tmarhguy/tomato/docs/log/README.md

# Tomato engineering journal

> **Historical record:** Entries in this directory preserve the design as it
> was discussed on their publication date. They are not canonical current
> documentation. Some describe superseded word widths, register designs, ISA
> counts, software versions, or preview-only behavior. Use
> [`../status.md`](../status.md) for present facts and
> [`../documentation-policy.md`](../documentation-policy.md) when claims differ.

The journal records the path from early datapath experiments through the
discrete ALU slice, FPGA Tomato, Tomato OS, and later integrations. Historical
content is intentionally not rewritten.

## September 2026

- 15 Sep — [Envelop — Parsing, Simplest](<2026-09-15 - Envelop Parsing - Simplest.md>)
- 15 Sep — [Envelop — Scope Optimization](<2026-09-15 - Envelop Scope Optimization.md>)
- 15 Sep — [Virtual Fallback vs AI](<2026-09-15 - Virtual Fallback vs AI.md>)
- 15 Sep — [Discard Previewer or Integrate](<2026-09-15 - Discard Previewer or Integrate.md>)
- 14 Sep — [Envelop — Website and World Connect](<2026-09-14 - Envelop Website and World Connect.md>)
- 14 Sep — [Envelop — Native Bridge](<2026-09-14 - Envelop Native Bridge.md>)
- 14 Sep — [Envelop — Origin](<2026-09-14 - Envelop Origin.md>)
- 14 Sep — [Synthesis Bypass](<2026-09-14 - Synthesis Bypass.md>)
- 14 Sep — [Multiple Participants](<2026-09-14 - Multiple Participants.md>)
- 14 Sep — [Envelop — Tomato gets a message app](<2026-09-14 - Envelop - Tomato gets a message app.md>)
- 13 Sep — [ISA Upgrade](<2026-09-13 - ISA Upgrade.md>)
- 11 Sep — [Of Course Tomato Needs Sudoku](<2026-09-11 - Of Course Tomato Needs Sudoku.md>)
- 11 Sep — [HDMI, Properly Captured](<2026-09-11 - HDMI, Properly Captured.md>)
- 11 Sep — [Wallpaper, Polish, and the Rest of the Computer](<2026-09-11 - Wallpaper, Polish, and the Rest of the Computer.md>)
- 11 Sep — [When assembly is still too high-level for Tomato](<2026-09-11 - When assembly is still too high-level for Tomato.md>)

## August 2026

- 29 Aug — [Tomato works beautifully!](<2026-08-29 - Tomato works beautifully!.md>)
- 28 Aug — [Pixels on the Glass](<2026-08-28 - Pixels on the Glass.md>)
- 28 Aug — [Exploring Beyond Vivado — Open-Source Synthesis Pivot](<2026-08-28 - Exploring Beyond Vivado - Open-Source Synthesis Pivot.md>)
- 28 Aug — [Successful Video — FPGA + PMOD](<2026-08-28 - Successful Video - FPGA + PMOD.md>)
- 28 Aug — [One Press, One Key](<2026-08-28 - One Press, One Key.md>)
- 26 Aug — [The PMOD Pivot](<2026-08-26 - The PMOD Pivot.md>)
- 23 Aug — [The Invisible Logic](<2026-08-23 - The Invisible Logic.md>)
- 21 Aug — [First Lights and Flux](<2026-08-21 - First Lights and Flux.md>)
- 20 Aug — [The Gallery Paradox](<2026-08-20 - The Gallery Paradox.md>)
- 18 Aug — [First Phase of Assembly](<2026-08-18 - First Phase of Assembly.md>)
- 16 Aug — [Tomato Web Optimization](<2026-08-16 - Tomato Web Optimization.md>)
- 15 Aug — [PCBs Arrive!](<2026-08-15 - PCBs Arrive!.md>)
- 15 Aug — [ISA as a Wire](<2026-08-15 - ISA as a Wire.md>)
- 13 Aug — [Solder Station Arrives](<2026-08-13 - Solder Station Arrives.md>)
- 13 Aug — [Front-Page News in Ashtown Valley](<2026-08-13 - Front-Page News in Ashtown Valley.md>)
- 07 Aug — [Ordered Tomato](<2026-08-07 - Ordered Tomato.md>)
- 02 Aug — [Designing Additional Boards](<2026-08-02 - Designing Additional Boards.md>)

## July 2026

- 31 Jul — [The lingering thoughts](<2026-07-31 - The lingering thoughts.md>)
- 31 Jul — [Falling back to 32b](<2026-07-31 - Falling back to 32b.md>)
- 30 Jul — [Redesign into 40b (Old design = 32b)](<2026-07-30 - Redesign into 40b (Old design = 32b).md>) — **superseded direction; Tomato is currently 32-bit**
- 13 Jul — [Truth Table Latch](<2026-07-13 - Truth Table Latch.md>)
- 13 Jul — [Pipelined FPGA — What if…](<2026-07-13 - Pipelined FPGA - What if....md>)
- 13 Jul — [Downgrade for an upgrade — 32b to 16b × 4](<2026-07-13 - Downgrade for an upgrade - 32b to 16b x 4.md>) — **superseded exploration**
- 13 Jul — [Demo Ideas](<2026-07-13 - Demo Ideas.md>)
- 13 Jul — [Architecture Upgrade](<2026-07-13 - Architecture Upgrade.md>)

## June 2026

- 27 Jun — [Elimination of Mode Multiplexers](<2026-06-27 - Elimination of Mode Multiplexers.md>)
- 26 Jun — [ALU Architecture Refinement & Logic Optimization](<2026-06-26 - ALU Architecture Refinement & Logic Optimization.md>)
- 26 Jun — [ALU — Redesign with 74251](<2026-06-26 - ALU - Redesign with 74251.md>)
- 19 Jun — [ALU segment display design](<2026-06-19 - ALU segment display design.md>)
- 16 Jun — [Microcode Control Modularization](<2026-06-16 - Microcode Control Modularization.md>)
- 15 Jun — [Multiplication and Division](<2026-06-15 - Multiplication and Division.md>)
- 11 Jun — [Load Store Pipeline Analysis](<2026-06-11 - Load Store Pipeline Analysis.md>)
- 10 Jun — [Implementing Mul-Div Engine](<2026-06-10 - Implementing Mul-Div Engine.md>)

## Original introduction

[Welcome to Tomato 32](<Welcome to Tomato 32.md>) is the original welcome
dispatch and former hand-maintained index. Its prose and stale links are kept
as historical content; this README is the maintained journal index.
