tmarhguy/tomato/hardware/kicad/boards/02_shift_encoder/README.md

# 02 — Shift encoder

<p align="center"><strong>Shift + mul-div control lot · in design.</strong></p>

 

KiCad lot for the shift encoder and mul-div control board. Schematic and layout details land here as the lot advances.

**Project map:** [Boards](../README.md) · [KiCad](../../README.md) · Digital: shift / mul control sheets under [hardware/digital/modules/](../../../digital/modules/)
