tmarhguy/tomato/docs/log/2026-08-15 - PCBs Arrive!.md

# PCBs Arrive!

The PCBs all just arrived! I ordered 5 of them, and I tested them with a continuity meter, particularly for the power connections, and I am happy to log that there are no islands! It is beautiful watching the board of such sophisticated nature, realizing that I remember placing every single trace!

<p align="center">
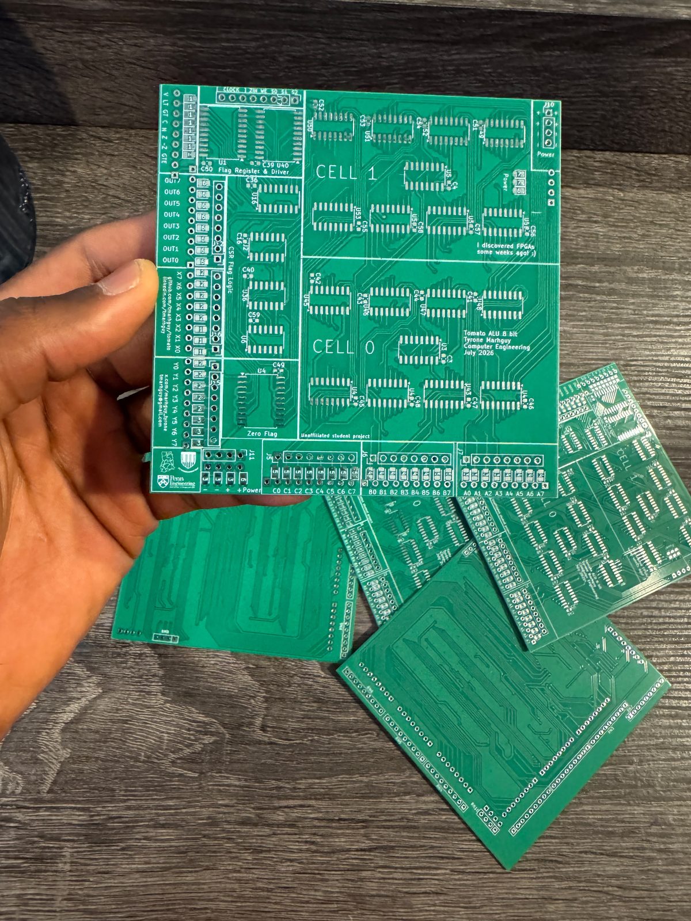
[picture p47: web/assets/pcb/pcb-arrive.jpeg]
Five 07_alu boards on the desk — Tomato ALU 8 bit, July 2026.
  
</p>
<p align="center"><em>Five boards. Lot 07, as received.</em></p>

<p align="center">
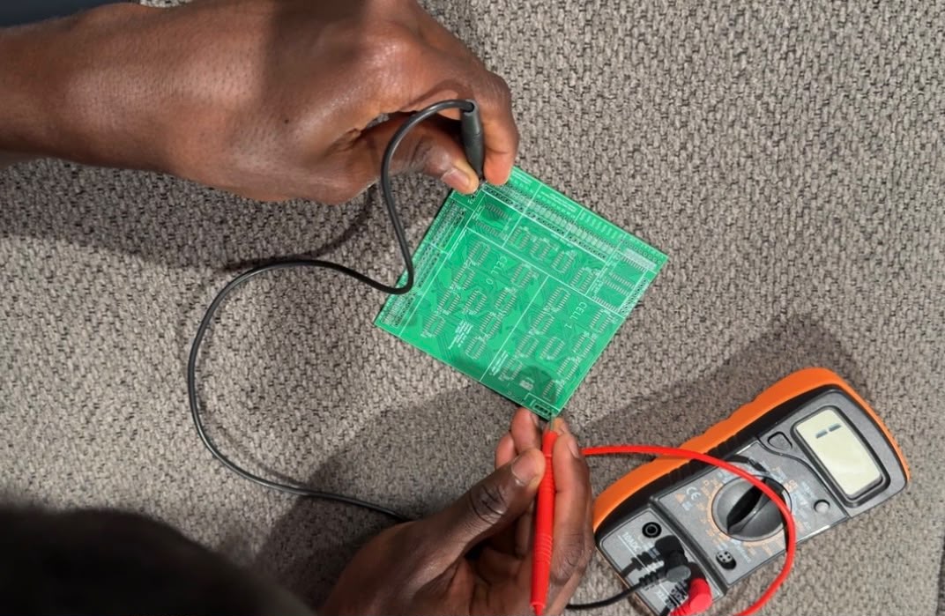
[picture p48: web/assets/pcb/continuity-test.jpeg]
Continuity meter on the 07_alu power rails — no islands.
  
</p>
<p align="center"><em>Continuity on power. No islands.</em></p>

<p align="center">
  <video src="../../web/assets/pcb/pcb-arrive.mp4" controls width="520"></video>
</p>
<p align="center"><em>The boards, in the round. ([video](../../web/assets/pcb/pcb-arrive.mp4))</em></p>

I had to admit to my roommate: isn't it hilarious that all this I have been working on, I did it all by myself? Buying a multimeter, an FPGA, using KiCad, down to this project. It has been a long and interesting journey!

The boards look stunning!
