tmarhguy/tomato/docs/alu/alu-1b/alu_control_map.pdf

# MOSAIC32 ALU Control Map - Reference Sheet

14-bit micro-instruction: LUT[7:0] + ctrl[4:0] + Cin | • Aeff = (Asel · A) ⊕ Ainv | Beff = (Bsel · B) ⊕ Binv
csel=0 → Arithmetic Mode (carry chain) | • csel=1 → Logic Mode (C bus)

# PART 1 — Arithmetic

csel=0 → ctrl 0x00--0x0F. SUM(0x96) for sub.

# Mnemonic | LUT Ctrl Aeff | Beff | Cin Result

1 ADD | 0x96 0x05 A | B | fr | A + B + Cin
2 ADC | 0x96 0x05 A | B | 1 | A + B + 1
3 INC A | 0x96 0x01 A | GND 1 | A + 1
4 INC B | 0x96 0x04 GND B | 1 | B + 1
5 DEC A | 0x96 0x09 A | VCC 0 | A − 1
6 DEC B | 0x96 0x06 VCC B | 0 | B − 1
7 NEG A | 0x96 0x03 ∼ A | GND 1 | −A
8 NEG B | 0x96 0x0C GND ∼ B | 1 | −B
9 NOT A | 0x96 0x03 ∼ A | GND 0 | ∼ A
10 NOT B | 0x96 0x0C GND ∼ B | 0 | ∼ B
11 MOV A | 0x96 0x01 A | GND 0 | A
12 MOV B | 0x96 0x04 GND B | 0 | B
13 ZERO | 0x96 0x00 GND GND 0 | 0
14 ONE | 0x96 0x00 GND GND 1 | +1
15 ALL ONES | 0x96 0x0A VCC VCC 1 | −1
16 MINUS TWO 0x96 0x0A VCC VCC 0 | −2
17 CMN | 0x96 0x05 A | B | 0 | A + B
18 RSC | 0x96 0x07 ∼ A | B | 0 | B − A − 1
19 RSB | 0x96 0x07 ∼ A | B | 1 | B − A
20 SBB | 0x96 0x0D A | ∼ B | 0 | A − B − 1
21 SUB | 0x96 0x0D A | ∼ B | 1 | A − B
22 CMP | 0x96 0x0D A | ∼ B | 1 | A − B (flg)
23 ANOM | 0x69 0x04 GND B | 0 | −B − 1
24 ANOM | 0x69 0x04 GND B | 1 | −B
25 ANOM | 0x69 0x05 A | B | 0 | −A − B − 1
26 ANOM | 0x69 0x05 A | B | 1 | −A − B
27 ANOM | 0x69 0x0C GND ∼ B | 0 | B
28 ANOM | 0x69 0x0C GND ∼ B | 1 | B + 1
29 ANOM | 0x96 0x0F ∼ A | ∼ B | 1 | ∼ (A + B)
30 ANOM | 0x96 0x0F ∼ A | ∼ B | 0 | −A − B − 2

## Routing States

Ctrl Aeff / Beff Maps To

0x00 GND / GND ZERO / ONE
0x01 A / GND INC A / MOV A 0x02 VCC / GND (unused)
0x03 ∼ A / GND | NEG A / NOT A
0x04 GND / B | INC B / MOV B
0x05 A / B | ADD/ADC/CMN
0x06 VCC / B | DEC B / ANOM
0x07 ∼ A / B | RSB / RSC
0x08 GND / VCC (unused)
0x09 A / VCC | DEC A
0x0A VCC / VCC | ONES / MINUS2
0x0B ∼ A / VCC | (unused)
0x0C GND / ∼ B | NEG B / NOT B
0x0D A / ∼ B | SUB/SBB/CMP
0x0E VCC / ∼ B | (unused)
0x0F ∼ A / ∼ B | ANOM

# PART 2 — Logic

csel=1 → ctrl = 0x15 for all logic ops.

# Mnemonic | LUT Expression

31 ZERO | 0x00 0
32 ONES | 0xFF 1
33 MOV A | 0xAA A
34 NOT A | 0x55 ∼ A
35 MOV B | 0xCC B
36 NOT B | 0x33 ∼ B
37 MOV C | 0xF0 C
38 NOT C | 0x0F ∼ C
39 AND A,B | 0x88 A ∧ B
40 OR A,B | 0xEE A ∨ B
41 NAND A,B 0x77 ∼ (A ∧ B)
42 NOR A,B | 0x11 ∼ (A ∨ B)
43 XOR A,B | 0x66 A ⊕ B
44 XNOR A,B 0x99 ∼ (A ⊕ B)
45 AND A,C | 0xA0 A ∧ C
46 OR A,C | 0xFA A ∨ C
47 NAND A,C 0x5F ∼ (A ∧ C)
48 NOR A,C | 0x05 ∼ (A ∨ C)
49 XOR A,C | 0x5A A ⊕ C
50 XNOR A,C 0xA5 ∼ (A ⊕ C)
51 AND B,C | 0xC0 B ∧ C
52 OR B,C | 0xFC B ∨ C
53 NAND B,C 0x3F ∼ (B ∧ C)
54 NOR B,C | 0x03 ∼ (B ∨ C)
55 XOR B,C | 0x3C B ⊕ C
56 XNOR B,C 0xC3 ∼ (B ⊕ C)
57 BIC A,B | 0x22 A∧ ∼ B
58 BIC B,A | 0x44 ∼ A ∧ B
59 ORN A,B | 0xBB A∨ ∼ B
60 IMP A→B | 0xDD ∼ A ∨ B
61 BIC A,C | 0x0A A∧ ∼ C
62 BIC C,A | 0x50 ∼ A ∧ C

# PART 2 — Continued

# Mnemonic | LUT Expression

63 ORN A,C | 0xAF A∨ ∼ C
64 IMP A→C | 0xF5 ∼ A ∨ C
65 BIC B,C | 0x0C B∧ ∼ C
66 BIC C,B | 0x30 ∼ B ∧ C
67 ORN B,C | 0xCF B∨ ∼ C
68 IMP B→C | 0xF3 ∼ B ∨ C
69 AND3 | 0x80 A ∧ B ∧ C
70 OR3 | 0xFE A ∨ B ∨ C
71 NAND3 | 0x7F ∼ (A ∧ B ∧ C)
72 NOR3 | 0x01 ∼ (A ∨ B ∨ C)
73 XOR3 / SUM 0x96 A ⊕ B ⊕ C
74 XNOR3 | 0x69 ∼ (A ⊕ B ⊕ C)
75 MAJ | 0xE8 AB ∨ BC ∨ AC
76 MIN | 0x17 ∼ (AB ∨ BC ∨ AC)
77 MUX C?B:A | 0xCA C?B : A
78 MUX B?C:A | 0xE2 B?C : A
79 MUX A?C:B | 0xE4 A?C : B
80 AO21 | 0xEA A ∨ (B ∧ C)
81 AO21 | 0xEC B ∨ (A ∧ C)
82 AO21 | 0xF8 C ∨ (A ∧ B)
83 OA21 | 0xA8 A ∧ (B ∨ C)
84 OA21 | 0xC8 B ∧ (A ∨ C)
85 OA21 | 0xE0 C ∧ (A ∨ B)
86 AOI21 | 0x15 ∼ (A ∨ (B ∧ C))
87 AOI21 | 0x13 ∼ (B ∨ (A ∧ C))
88 AOI21 | 0x07 ∼ (C ∨ (A ∧ B))
89 OAI21 | 0x57 ∼ (A ∧ (B ∨ C))
90 OAI21 | 0x37 ∼ (B ∧ (A ∨ C))
91 OAI21 | 0x1F ∼ (C ∧ (A ∨ B))

Total Primitives: 91 (30 Arithmetic + 61 Logic). All ops are single-pass. MAJ is a free CLA co-product. XOR3(0x96) used for both SUM and SUB. csel=1 routes C bus directly to each slice’s C-input for logic mode.
