tmarhguy/tomato/docs/log/Welcome to Tomato 32.md

> **Historical introduction and superseded index:** This dispatch is preserved
> as written. Its counts, status claims, and links may reflect earlier designs.
> Use the [current journal index](README.md) and
> [canonical status](../status.md) for present information.

This is a build log for Tomato 32. It will keep track of the questions that come up and the answers I settled for. It focussed on build log, the constraints explored and the journey from building simple logic gates to a parametric datapath — a machine where an ISA is a map onto muxes, not a second computer in copper. If you're reading this. You probably love building computers and enjoy the architecture like I do. Enjoy!

Every dispatch in [`docs/log/`](.) is listed below: the file itself, and a shield into the typeset page on [tomato.tmarhguy.com](https://tomato.tmarhguy.com/journal.html).

## The vault

| Date | Log | Link |
| --- | --- | --- |
| 13 Sep 2026 | [ISA Upgrade](<./2026-09-13%20-%20ISA%20Upgrade.md>) |  |
| 11 Sep 2026 | [HDMI, Properly Captured](<./2026-09-11%20-%20HDMI,%20Properly%20Captured.md>) |   |
| 11 Sep 2026 | [Of Course Tomato Needs Sudoku](<./2026-09-11%20-%20Of%20Course%20Tomato%20Needs%20Sudoku.md>) |  |
| 11 Sep 2026 | [Wallpaper, Polish, and the Rest of the Computer](<./2026-09-11%20-%20Wallpaper,%20Polish,%20and%20the%20Rest%20of%20the%20Computer.md>) |  |
| 11 Sep 2026 | [When assembly is still too high-level for Tomato](<./2026-09-11%20-%20When%20assembly%20is%20still%20too%20high-level%20for%20Tomato.md>) |  |
| 29 Aug 2026 | [Tomato works beautifully!](<./2026-08-29%20-%20Tomato%20works%20beautifully%21.md>) |  |
| 29 Aug 2026 | Register file → 32,768 GPR (dispatch) |  |
| 28 Aug 2026 | [One Press, One Key](<./2026-08-28%20-%20One%20Press,%20One%20Key.md>) |  |
| 28 Aug 2026 | [Exploring Beyond Vivado - Open-Source Synthesis Pivot](<./2026-08-28%20-%20Exploring%20Beyond%20Vivado%20-%20Open-Source%20Synthesis%20Pivot.md>) |  |
| 28 Aug 2026 | [Pixels on the Glass](<./2026-08-28%20-%20Pixels%20on%20the%20Glass.md>) |  |
| 26 Aug 2026 | [The PMOD Pivot](<./2026-08-26%20-%20The%20PMOD%20Pivot.md>) |  |
| 23 Aug 2026 | [The Invisible Logic](<./2026-08-23%20-%20The%20Invisible%20Logic.md>) |  |
| 21 Aug 2026 | [First Lights and Flux](<./2026-08-21%20-%20First%20Lights%20and%20Flux.md>) |  |
| 20 Aug 2026 | [The Gallery Paradox](<./2026-08-20%20-%20The%20Gallery%20Paradox.md>) |  |
| 18 Aug 2026 | [First Phase of Assembly](<./2026-08-18%20-%20First%20Phase%20of%20Assembly.md>) |  |
| 16 Aug 2026 | [Tomato Web Optimization](<./2026-08-16%20-%20Tomato%20Web%20Optimization.md>) |  |
| 15 Aug 2026 | [PCBs Arrive!](<./2026-08-15%20-%20PCBs%20Arrive%21.md>) |  |
| 15 Aug 2026 | [ISA as a Wire](<./2026-08-15%20-%20ISA%20as%20a%20Wire.md>) |   |
| 13 Aug 2026 | [Solder Station Arrives](<./2026-08-13%20-%20Solder%20Station%20Arrives.md>) |  |
| 13 Aug 2026 | [Front-Page News in Ashtown Valley](<./2026-08-13%20-%20Front-Page%20News%20in%20Ashtown%20Valley.md>) |  |
| 07 Aug 2026 | [Ordered Tomato](<./2026-08-07%20-%20Ordered%20Tomato.md>) |  |
| 02 Aug 2026 | [Designing Additional Boards](<./2026-08-02%20-%20Designing%20Additional%20Boards.md>) |  |
| 31 Jul 2026 | [The lingering thoughts](<./2026-07-31%20-%20The%20lingering%20thoughts.md>) |  |
| 31 Jul 2026 | [Falling back to 32b](<./2026-07-31%20-%20Falling%20back%20to%2032b.md>) |  |
| 30 Jul 2026 | [Redesign into 40b (Old design = 32b)](<./2026-07-30%20-%20Redesign%20into%2040b%20%28Old%20design%20=%2032b%29.md>) |  |
| 13 Jul 2026 | [Truth Table Latch](<./2026-07-13%20-%20Truth%20Table%20Latch.md>) |  |
| 13 Jul 2026 | [Pipelined FPGA — What if…](<./2026-07-13%20-%20Pipelined%20FPGA%20-%20What%20if....md>) |  |
| 13 Jul 2026 | [Downgrade for an upgrade — 32b to 16b × 4](<./2026-07-13%20-%20Downgrade%20for%20an%20upgrade%20-%2032b%20to%2016b%20x%204.md>) |  |
| 13 Jul 2026 | [Demo Ideas](<./2026-07-13%20-%20Demo%20Ideas.md>) |  |
| 13 Jul 2026 | [Architecture Upgrade](<./2026-07-13%20-%20Architecture%20Upgrade.md>) |  |
| 27 Jun 2026 | [Elimination of Mode Multiplexers](<./2026-06-27%20-%20Elimination%20of%20Mode%20Multiplexers.md>) |  |
| 26 Jun 2026 | [ALU — Redesign with 74251](<./2026-06-26%20-%20ALU%20-%20Redesign%20with%2074251.md>) |  |
| 26 Jun 2026 | [ALU Architecture Refinement &amp; Logic Optimization](<./2026-06-26%20-%20ALU%20Architecture%20Refinement%20%26%20Logic%20Optimization.md>) |  |
| 19 Jun 2026 | [ALU segment display design](<./2026-06-19%20-%20ALU%20segment%20display%20design.md>) |  |
| 16 Jun 2026 | [Microcode Control Modularization](<./2026-06-16%20-%20Microcode%20Control%20Modularization.md>) |  |
| 15 Jun 2026 | [Multiplication and Division](<./2026-06-15%20-%20Multiplication%20and%20Division.md>) |  |
| 11 Jun 2026 | [Load Store Pipeline Analysis](<./2026-06-11%20-%20Load%20Store%20Pipeline%20Analysis.md>) |  |
| 10 Jun 2026 | [Implementing Mul-Div Engine](<./2026-06-10%20-%20Implementing%20Mul-Div%20Engine.md>) |  |

## The map

The READMEs are the map of the tree. The log above is the trail.

| README | Link |
| --- | --- |
| [`README.md`](https://github.com/tmarhguy/tomato/blob/main/README.md) |  |
| [`web/README.md`](https://github.com/tmarhguy/tomato/blob/main/web/README.md) |  |
| [`docs/README.md`](https://github.com/tmarhguy/tomato/blob/main/docs/README.md) |  |
| [`docs/isa/README.md`](https://github.com/tmarhguy/tomato/blob/main/docs/isa/README.md) |  |
| [`hardware/README.md`](https://github.com/tmarhguy/tomato/blob/main/hardware/README.md) |  |
| [`hardware/digital/README.md`](https://github.com/tmarhguy/tomato/blob/main/hardware/digital/README.md) |  |
| [`hardware/verilog/README.md`](https://github.com/tmarhguy/tomato/blob/main/hardware/verilog/README.md) |  |
| [`hardware/kicad/README.md`](https://github.com/tmarhguy/tomato/blob/main/hardware/kicad/README.md) |  |
| [`hardware/kicad/modules/README.md`](https://github.com/tmarhguy/tomato/blob/main/hardware/kicad/modules/README.md) |  |
| [`hardware/kicad/boards/README.md`](https://github.com/tmarhguy/tomato/blob/main/hardware/kicad/boards/README.md) |  |
| [`hardware/kicad/boards/01_alu/README.md`](https://github.com/tmarhguy/tomato/blob/main/hardware/kicad/boards/01_alu/README.md) |  |
| [`hardware/kicad/boards/02_shift_encoder/README.md`](https://github.com/tmarhguy/tomato/blob/main/hardware/kicad/boards/02_shift_encoder/README.md) |  |
| [`hardware/kicad/boards/07_alu/README.md`](https://github.com/tmarhguy/tomato/blob/main/hardware/kicad/boards/07_alu/README.md) |  |
| [`hardware/fpga/core/README.md`](https://github.com/tmarhguy/tomato/blob/main/hardware/fpga/core/README.md) |  |
| [`hardware/fpga/README.md`](https://github.com/tmarhguy/tomato/blob/main/hardware/fpga/README.md) |  |
| [`verification/README.md`](https://github.com/tmarhguy/tomato/blob/main/verification/README.md) |  |
| [`verification/formal/README.md`](https://github.com/tmarhguy/tomato/blob/main/verification/formal/README.md) |  |
| [`verification/rtl/README.md`](https://github.com/tmarhguy/tomato/blob/main/verification/rtl/README.md) |  |
| [`verification/scripts/README.md`](https://github.com/tmarhguy/tomato/blob/main/verification/scripts/README.md) |  |
| [`verification/directed/README.md`](https://github.com/tmarhguy/tomato/blob/main/verification/directed/README.md) |  |
| [`verification/synthesis/README.md`](https://github.com/tmarhguy/tomato/blob/main/verification/synthesis/README.md) |  |
| [`verification/uvm/README.md`](https://github.com/tmarhguy/tomato/blob/main/verification/uvm/README.md) |  |
| [`verification/uvm/common/README.md`](https://github.com/tmarhguy/tomato/blob/main/verification/uvm/common/README.md) |   |
| [`verification/uvm/alu_1b/README.md`](https://github.com/tmarhguy/tomato/blob/main/verification/uvm/alu_1b/README.md) |   |
| [`verification/uvm/alu_8b/README.md`](https://github.com/tmarhguy/tomato/blob/main/verification/uvm/alu_8b/README.md) |   |
| [`verification/uvm/alu_32b/README.md`](https://github.com/tmarhguy/tomato/blob/main/verification/uvm/alu_32b/README.md) |  |
| [`microcode/README.md`](https://github.com/tmarhguy/tomato/blob/main/microcode/README.md) |  |
| [`software/README.md`](https://github.com/tmarhguy/tomato/blob/main/software/README.md) |  |
| [`firmware/README.md`](https://github.com/tmarhguy/tomato/blob/main/firmware/README.md) |  |
| [`test/README.md`](https://github.com/tmarhguy/tomato/blob/main/test/README.md) |  |
