tmarhguy/tomato/docs/images/envelop/chat-on-tomato.webp

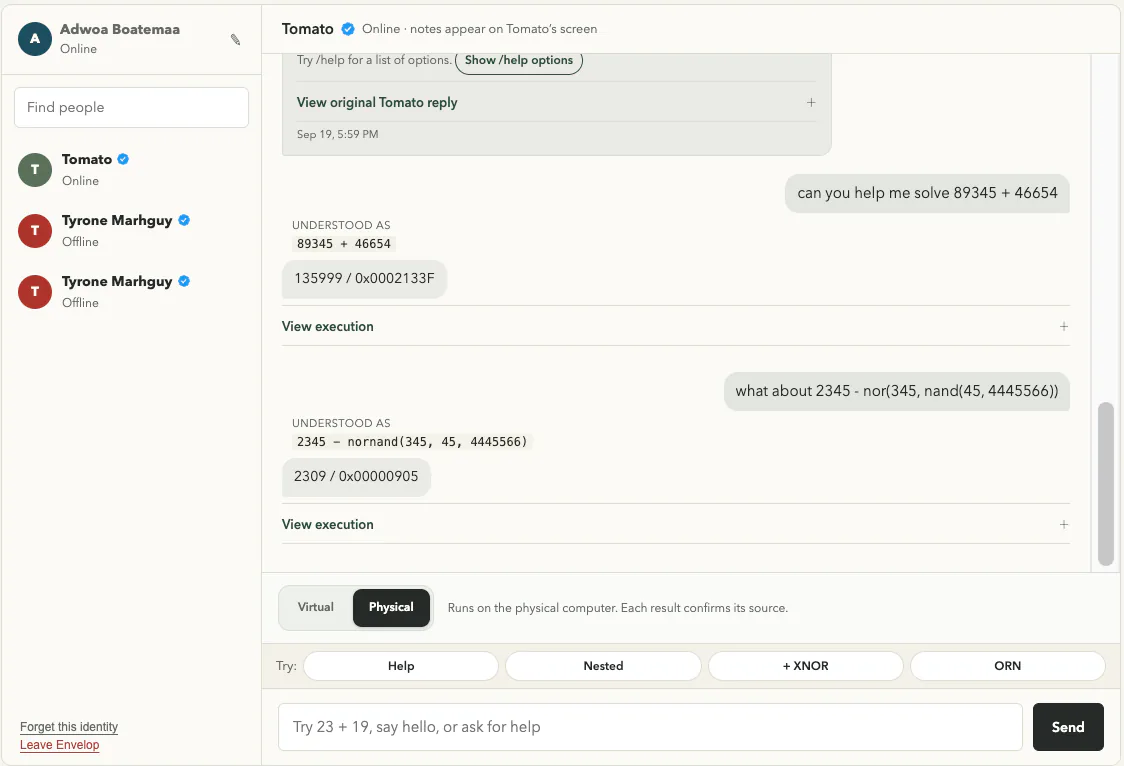
docs/images/envelop/chat-on-tomato.webp
