tmarhguy/tomato/hardware/kicad/main/8b-alu-slice/8b-alu-slice.png

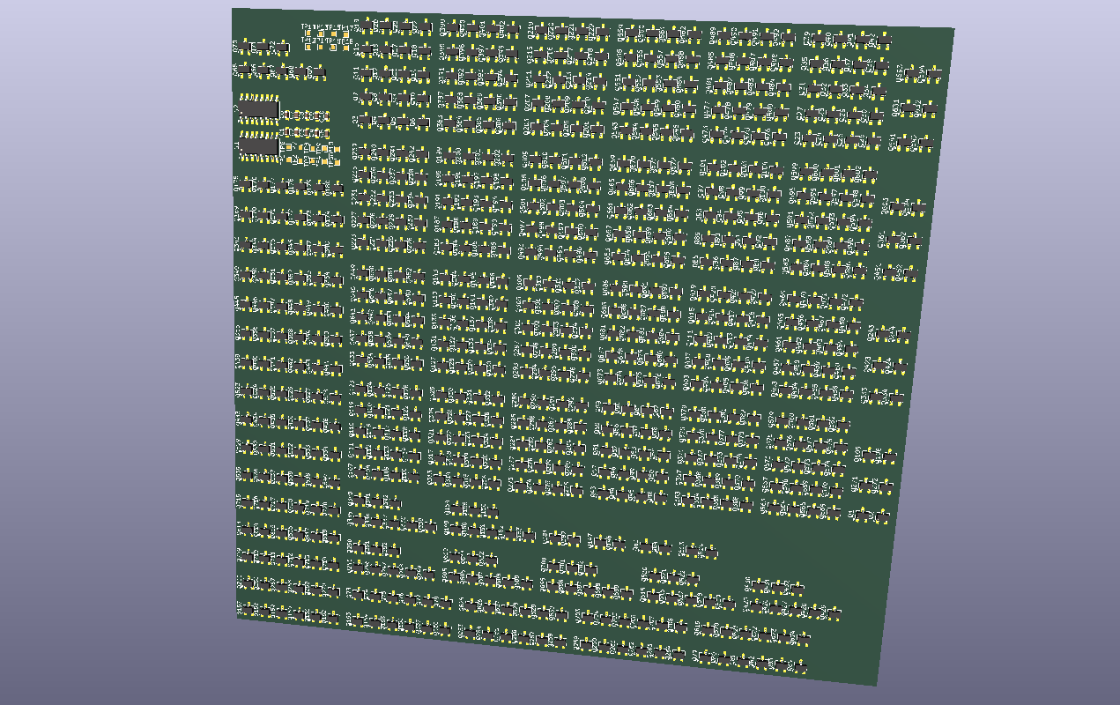
hardware/kicad/main/8b-alu-slice/8b-alu-slice.png
