tmarhguy/tomato/media/digital/2026-06-07-main.png

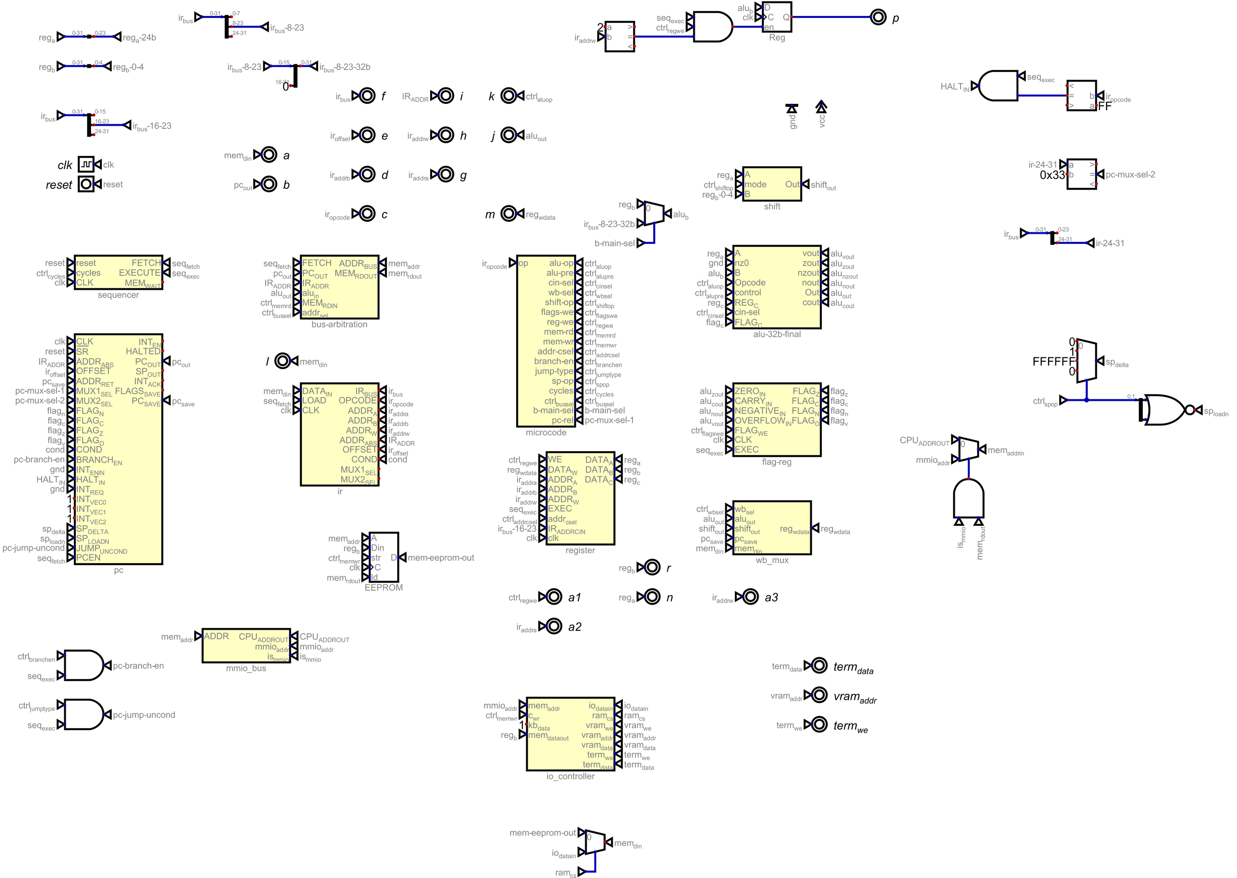
media/digital/2026-06-07-main.png
