tmarhguy/tomato/media/digital/2026-06-08-main.png

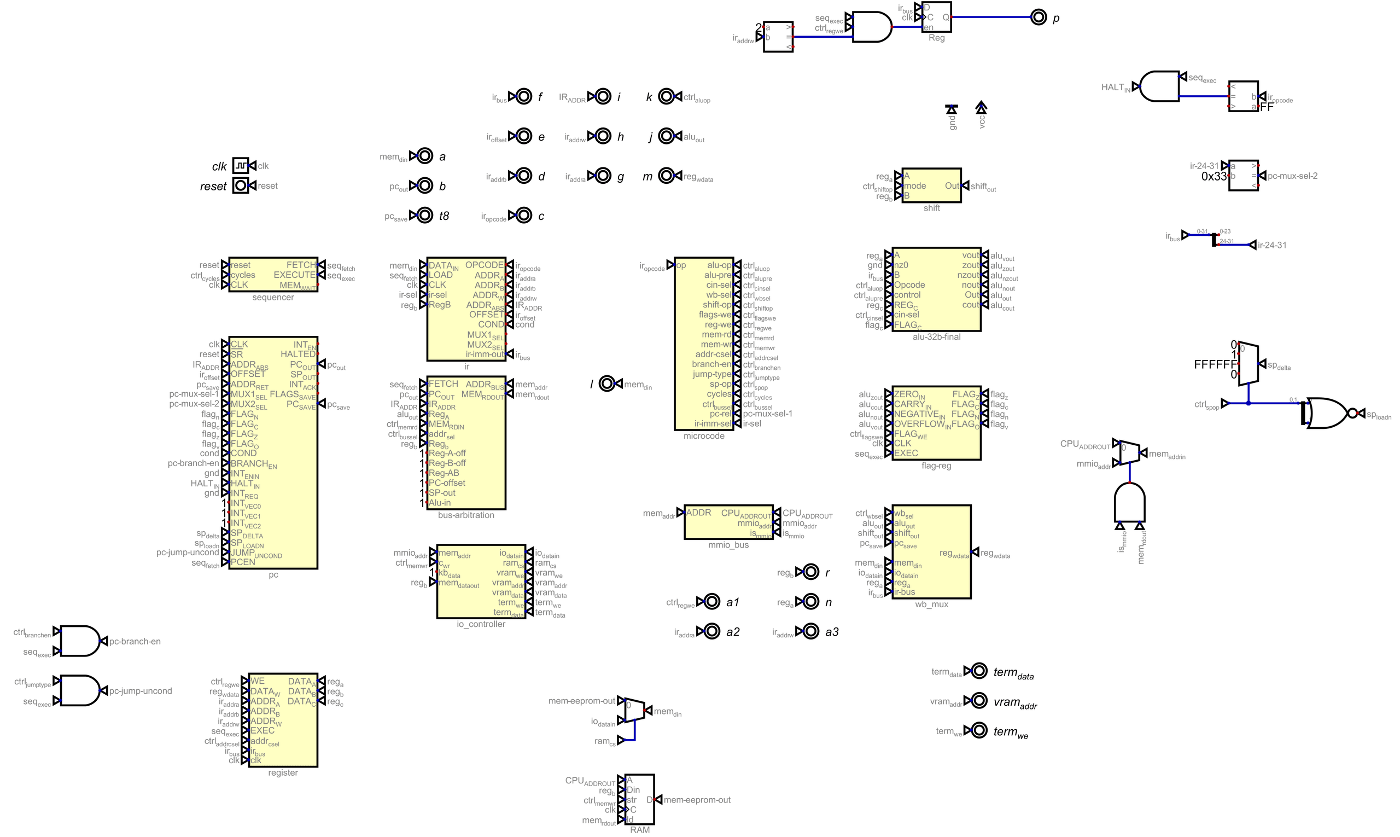
media/digital/2026-06-08-main.png
