tmarhguy/tomato/media/digital/2026-06-16-main.png

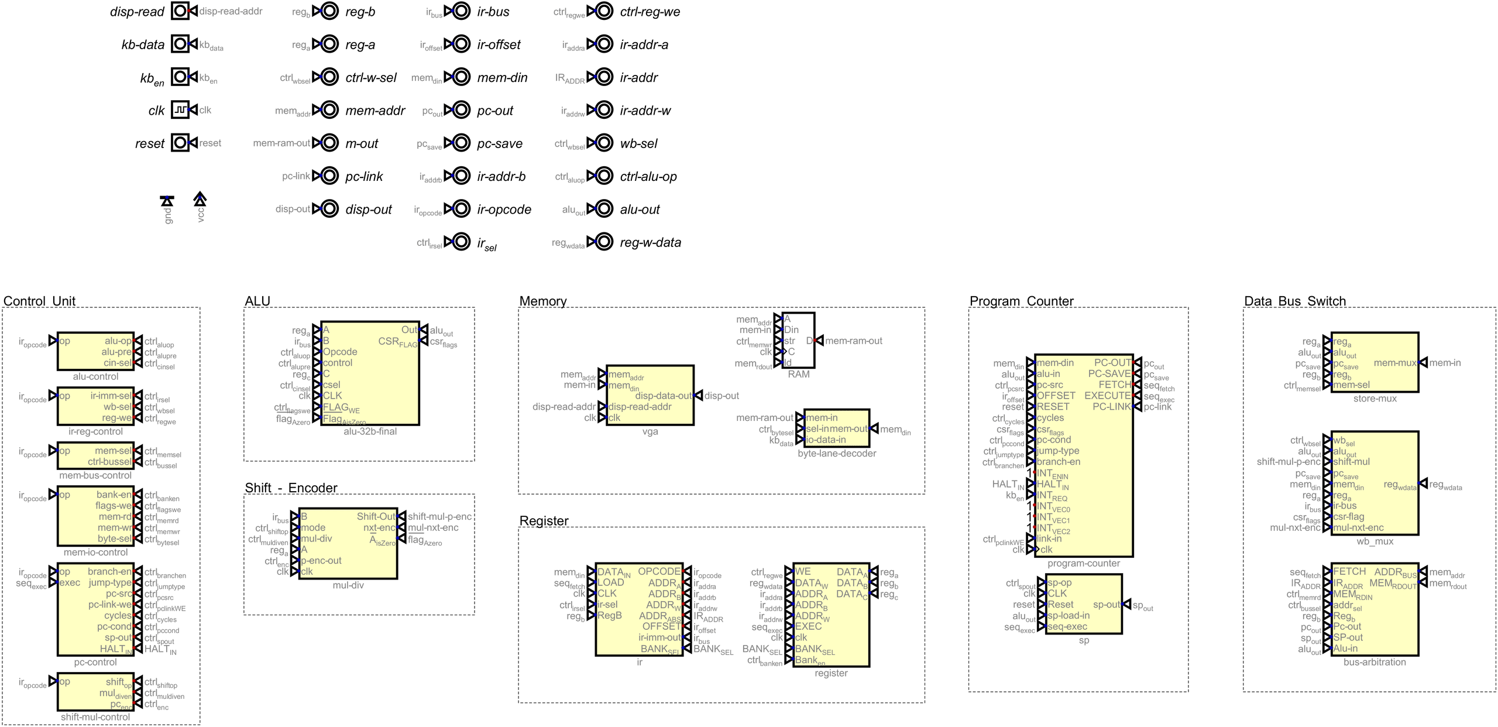
media/digital/2026-06-16-main.png
