tmarhguy/tomato/media/digital/alu/02-1b-cell-4to1-mux-logic.png

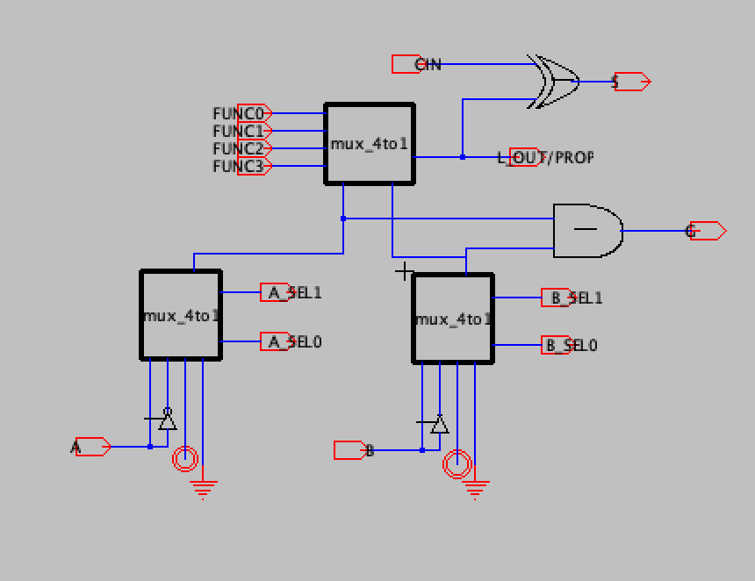
media/digital/alu/02-1b-cell-4to1-mux-logic.png
