tmarhguy/tomato/media/digital/alu/10-tg-xor-vpulse.png

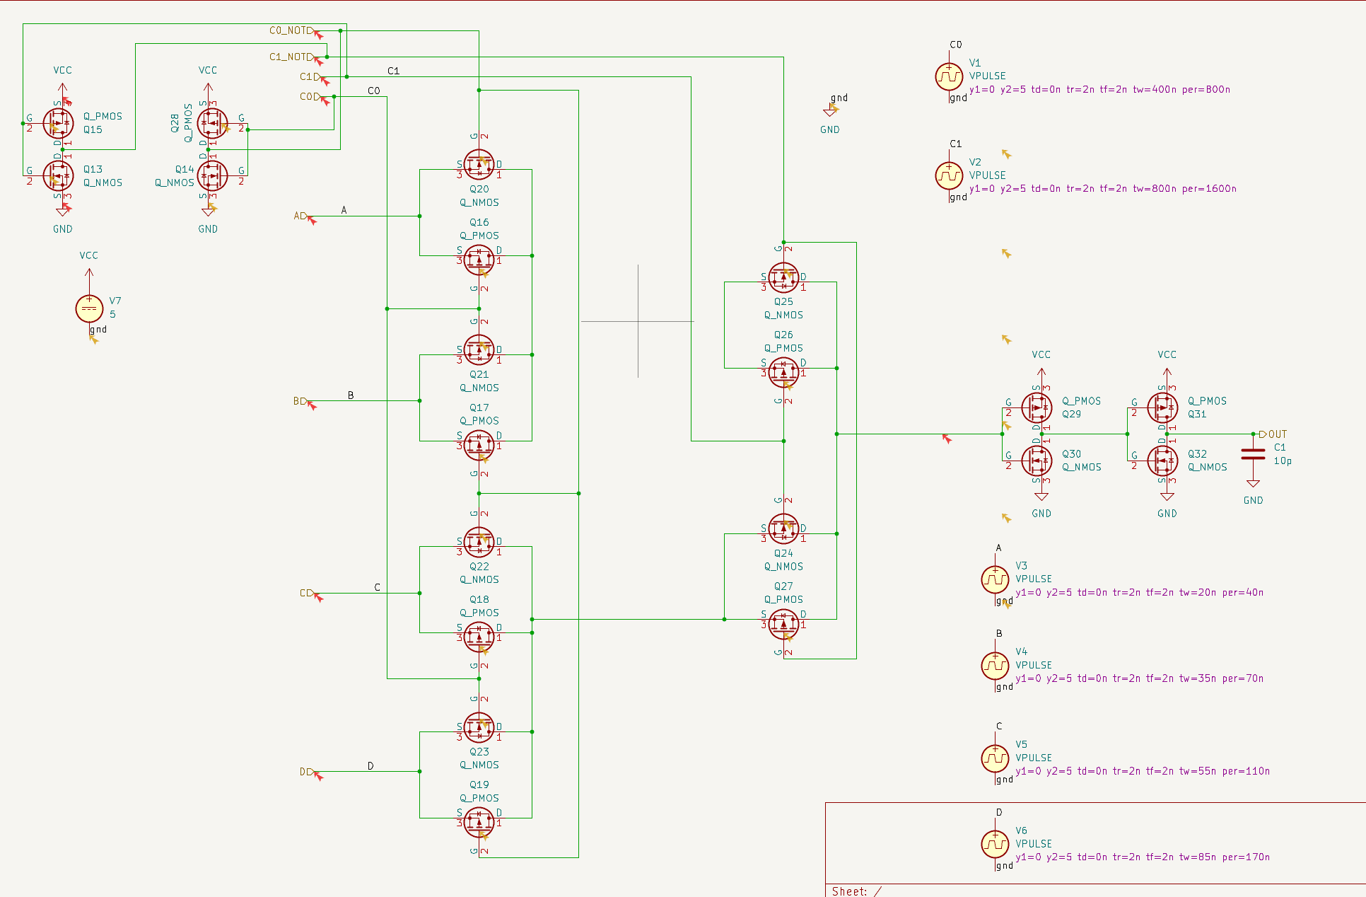
media/digital/alu/10-tg-xor-vpulse.png
