tmarhguy/tomato/media/digital/bus/01-arbiter-fail-then-pass.png

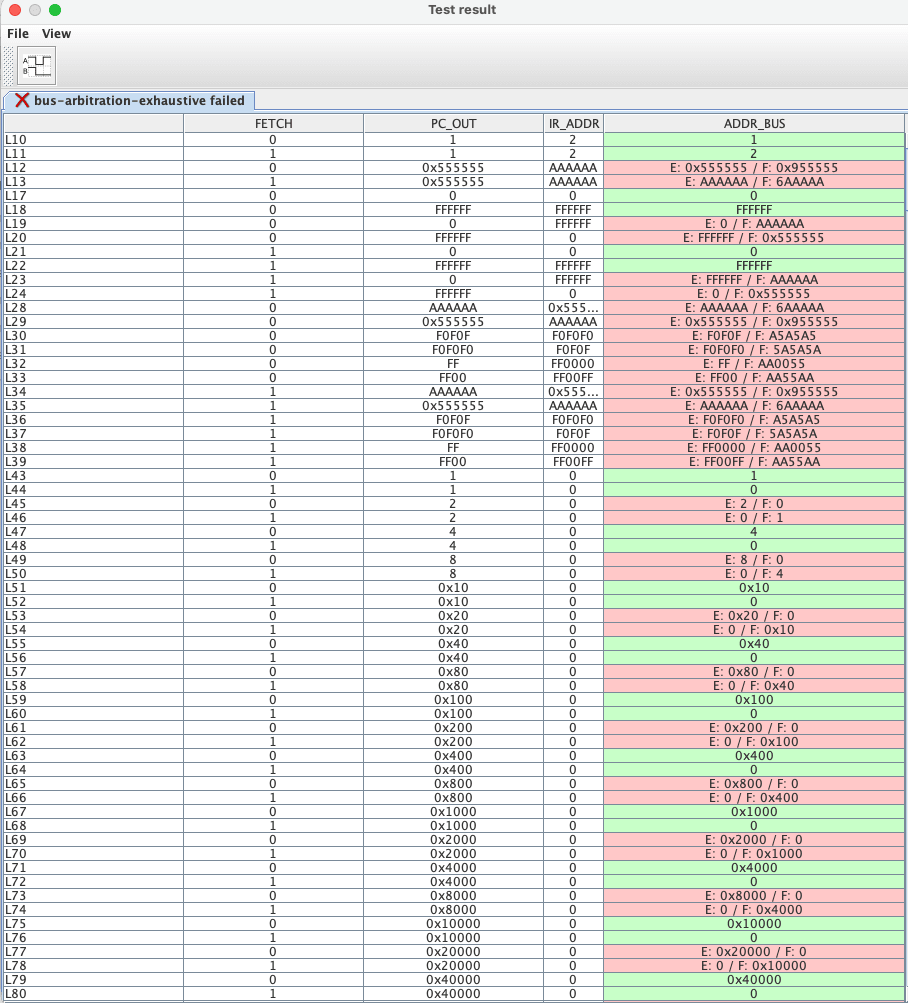
media/digital/bus/01-arbiter-fail-then-pass.png
