tmarhguy/tomato/media/digital/control/03-ctrl-unit-32b-later.png

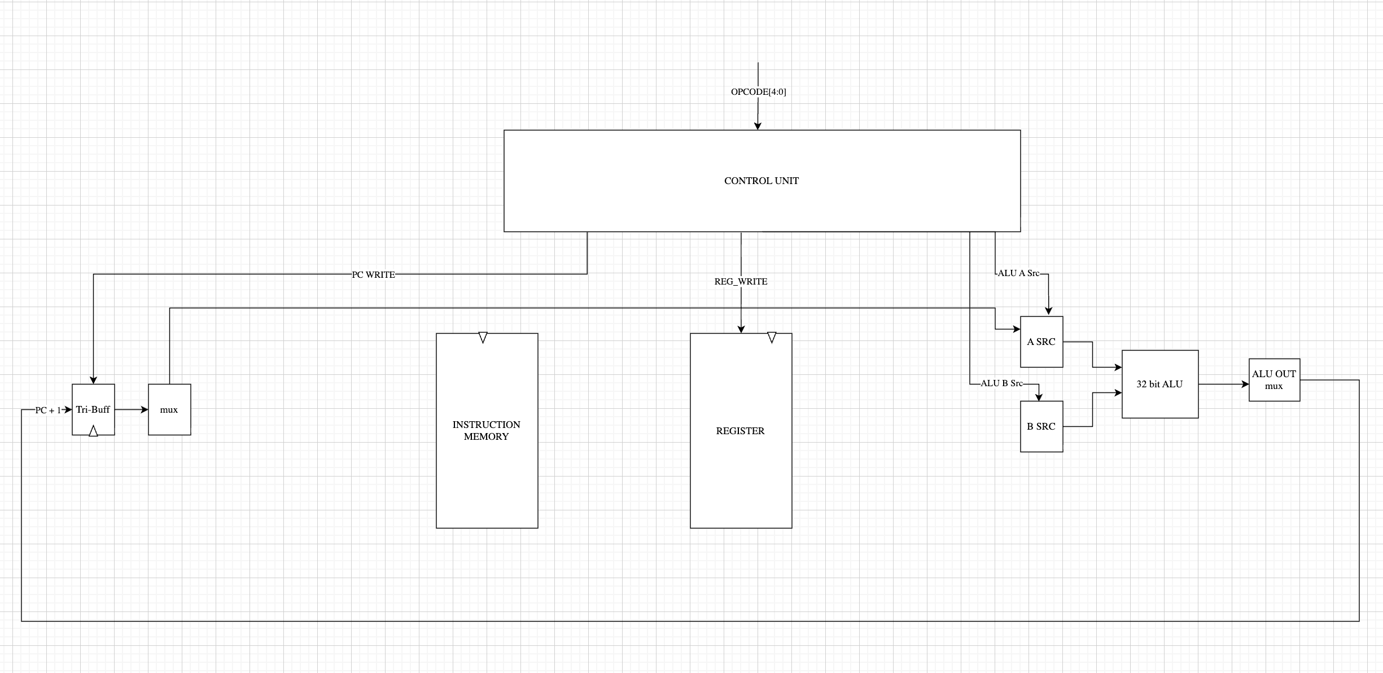
media/digital/control/03-ctrl-unit-32b-later.png
