tmarhguy/tomato/media/digital/control/06-microcode-rom-hex-64b.jpg

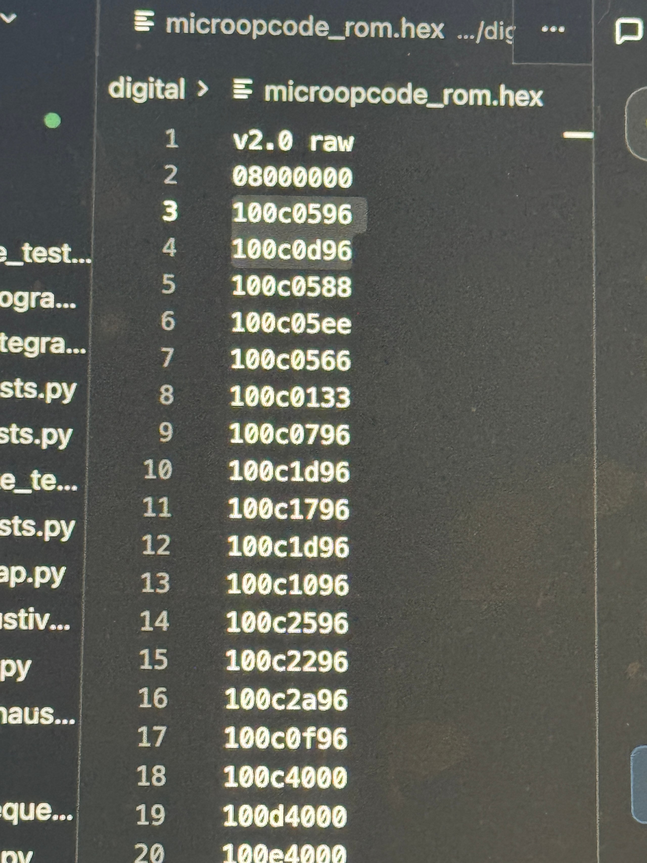
media/digital/control/06-microcode-rom-hex-64b.jpg
