tmarhguy/tomato/media/digital/control/07-system-schematic-overview.jpg

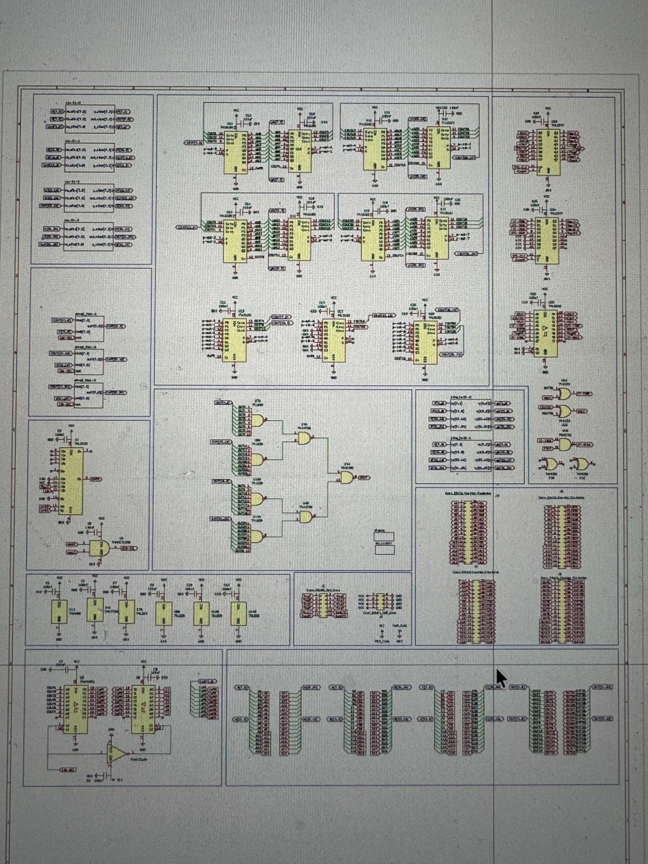
media/digital/control/07-system-schematic-overview.jpg
