tmarhguy/tomato/media/digital/pc-display/06-seg-atf16v8-cell.png

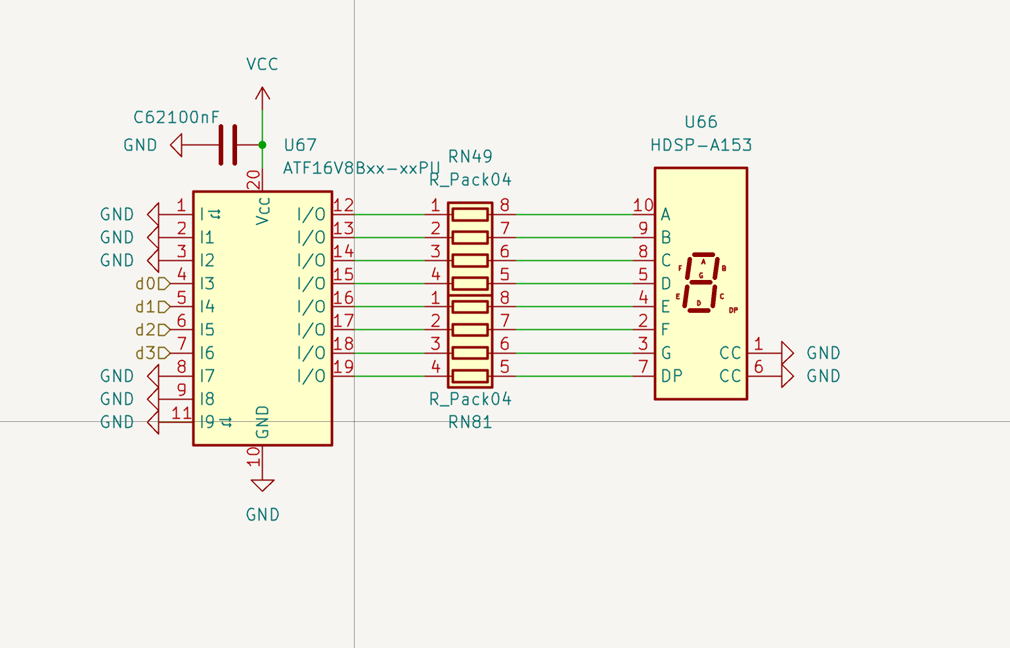
media/digital/pc-display/06-seg-atf16v8-cell.png
