tmarhguy/tomato/media/digital/pc-display/07-display-drawio.png

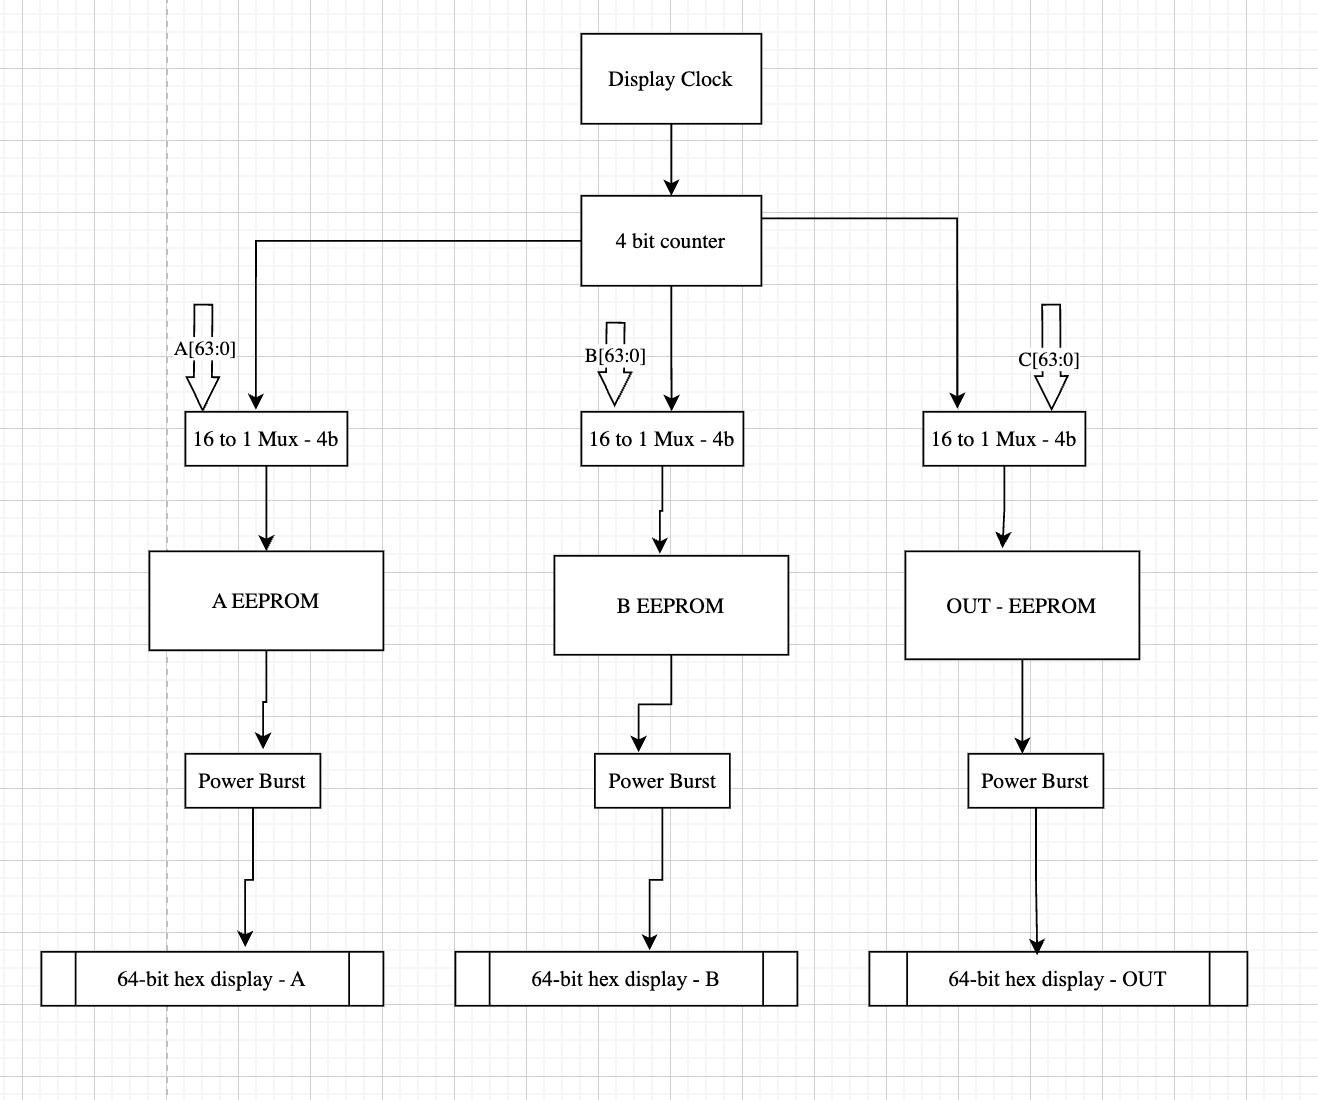
media/digital/pc-display/07-display-drawio.png
