tmarhguy/tomato/media/kicad/07_alu/schematics/07_alu-images-1.jpg

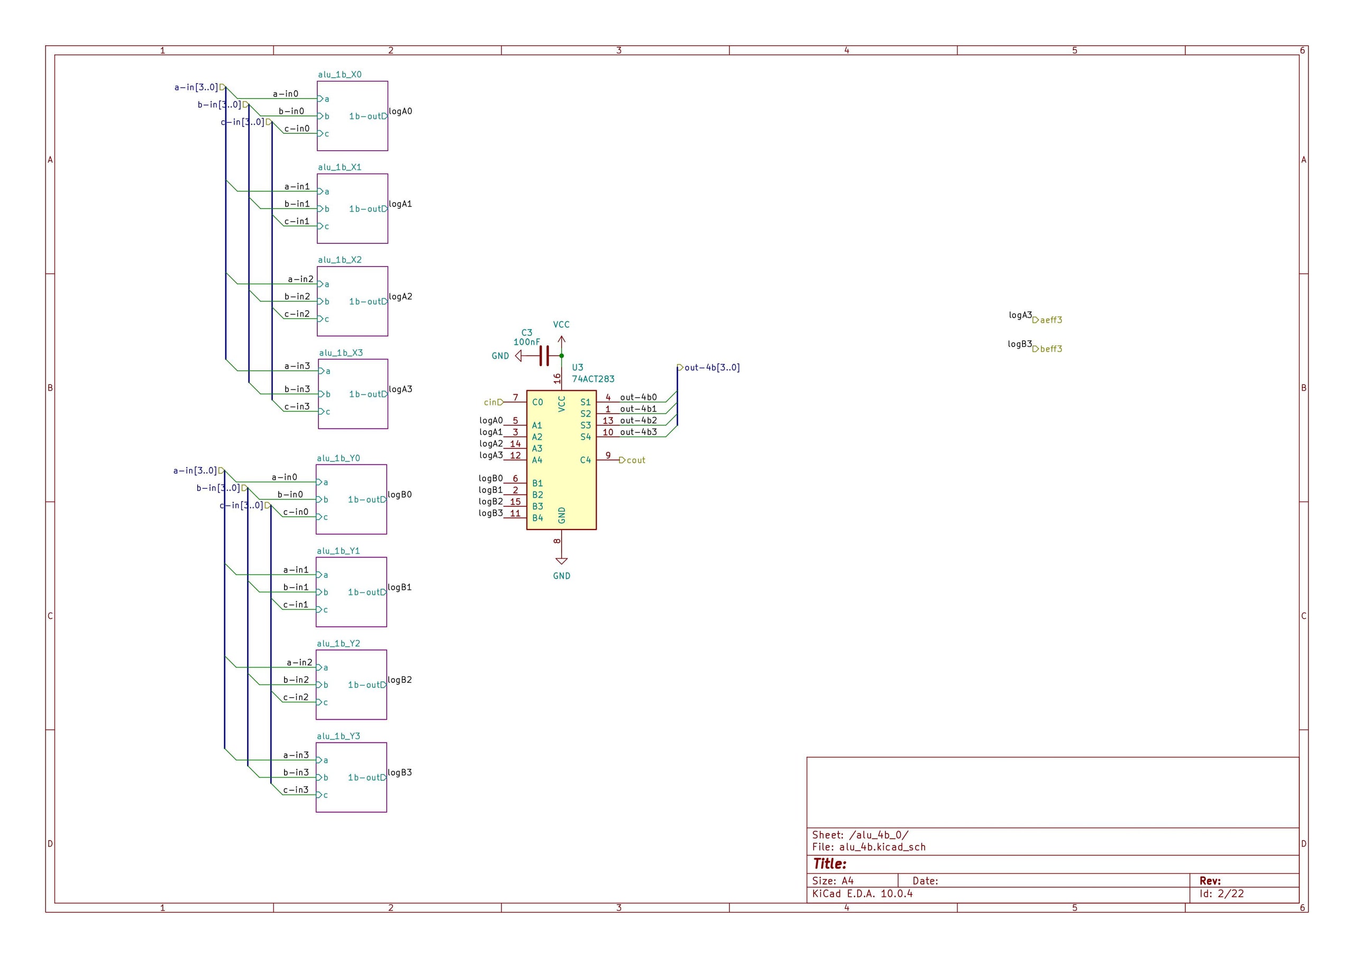
media/kicad/07_alu/schematics/07_alu-images-1.jpg
