tmarhguy/tomato/media/kicad/07_alu/schematics/07_alu-images-5.jpg

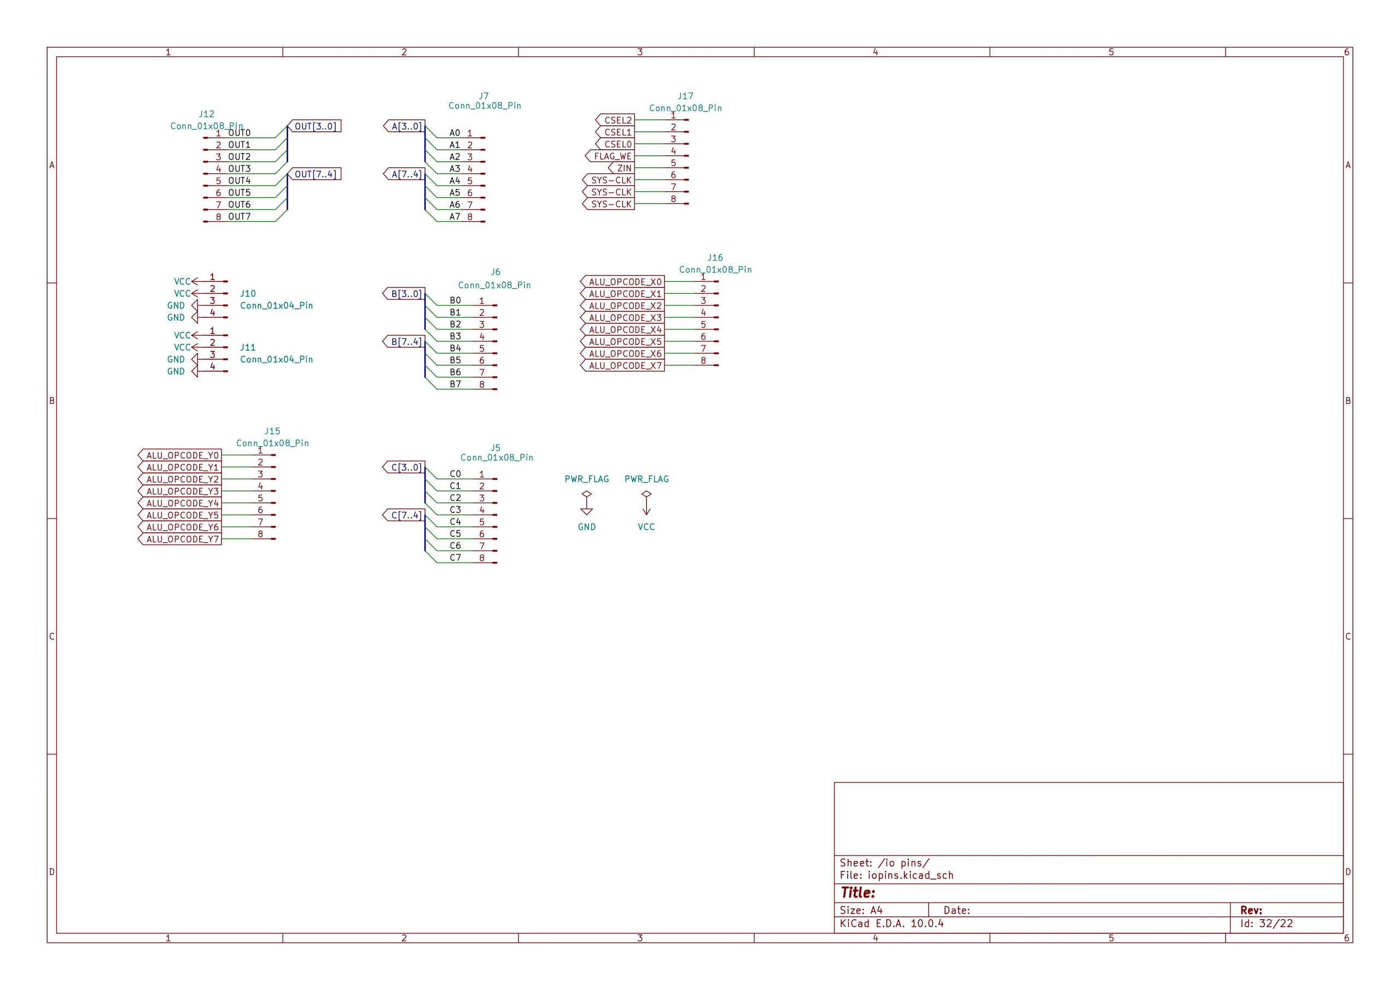
media/kicad/07_alu/schematics/07_alu-images-5.jpg
