tmarhguy/tomato/media/kicad/32b/05-74182-inv-driver-sch.png

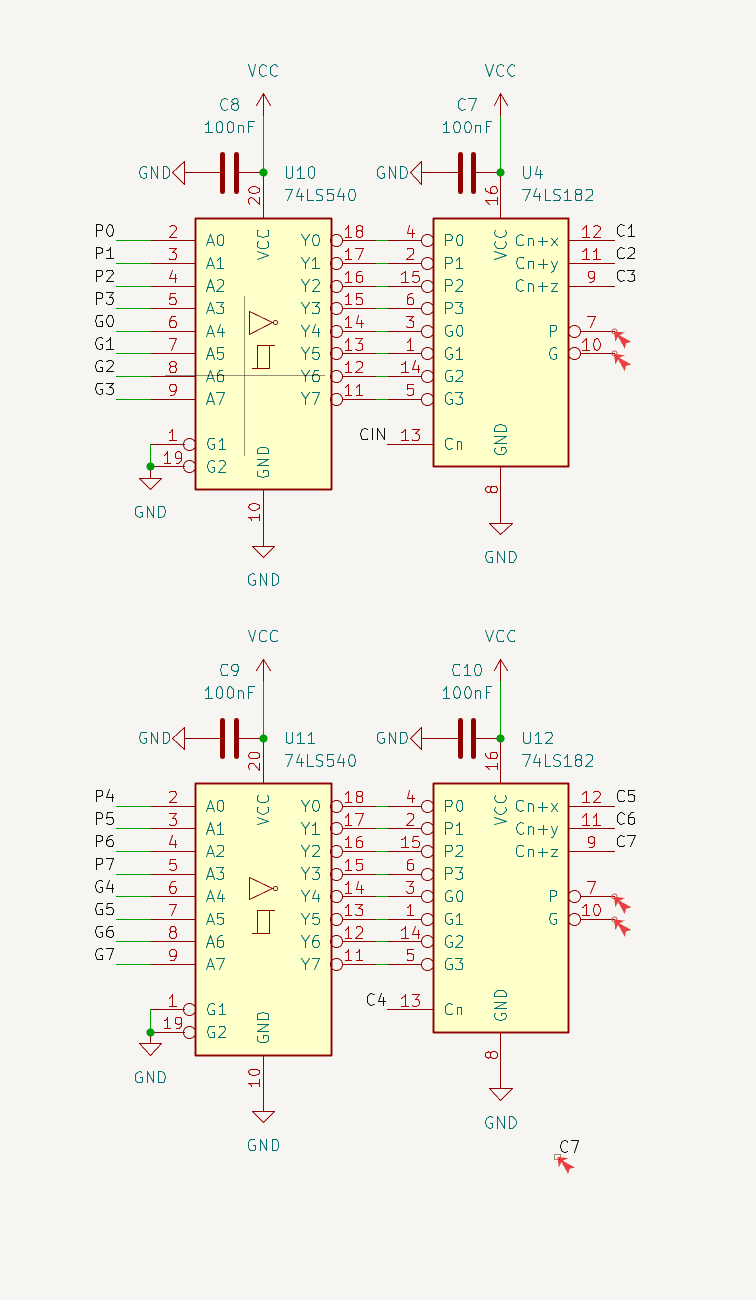
media/kicad/32b/05-74182-inv-driver-sch.png
