tmarhguy/tomato/media/logs/screenshots/2026-07-17-10.42.34-am.png

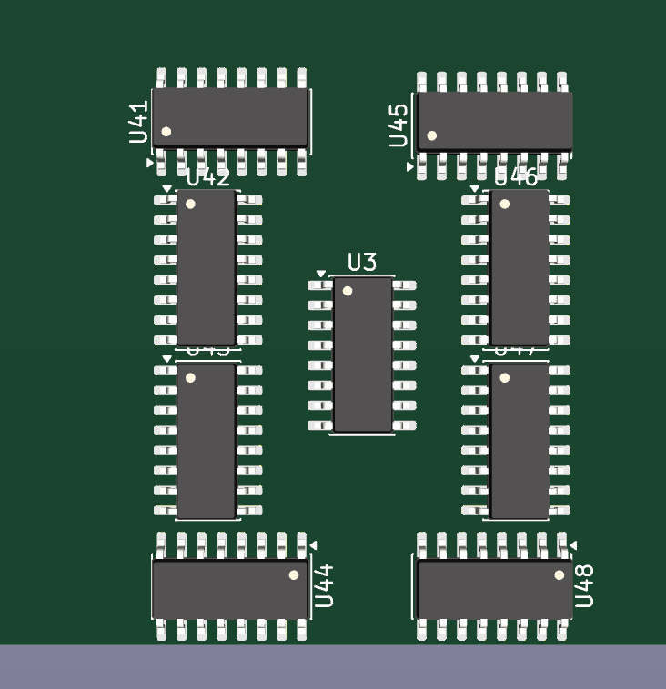
media/logs/screenshots/2026-07-17-10.42.34-am.png
