tmarhguy/tomato/media/logs/screenshots/2026-07-25-8.25.05-pm.png

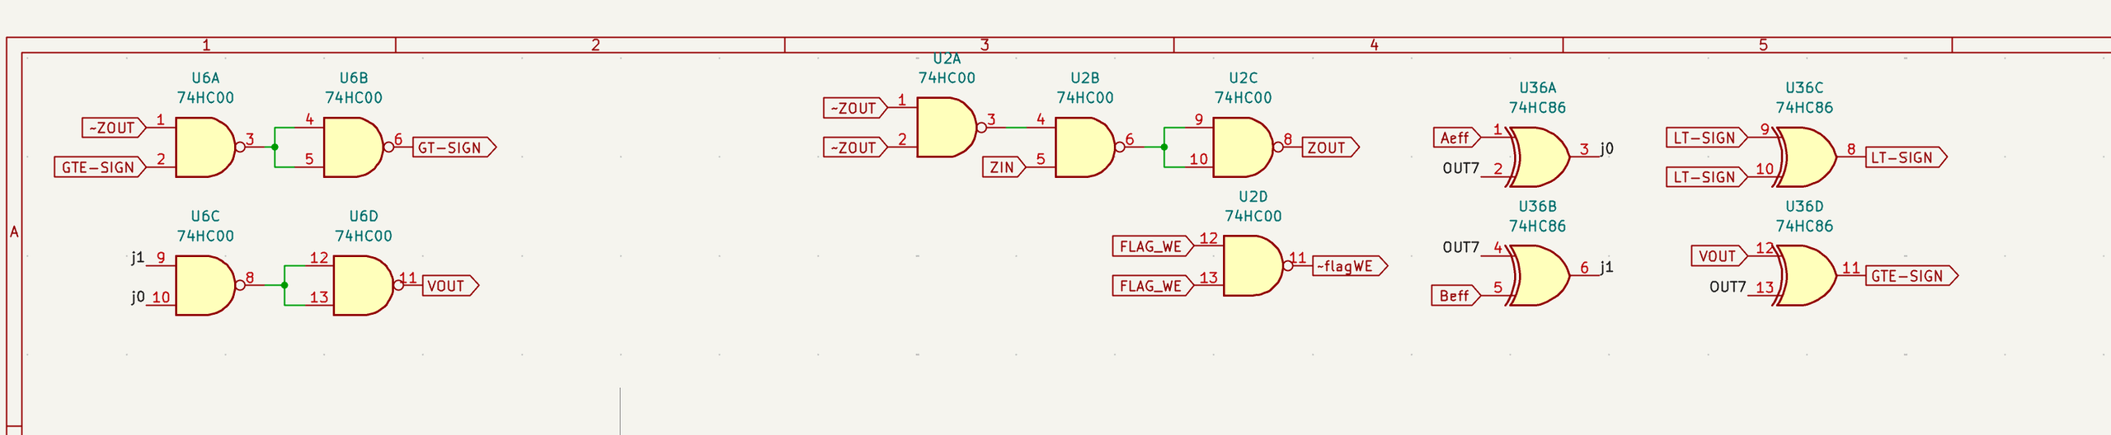
media/logs/screenshots/2026-07-25-8.25.05-pm.png
