tmarhguy/tomato/media/logs/screenshots/2026-07-26-2.43.37-pm.png

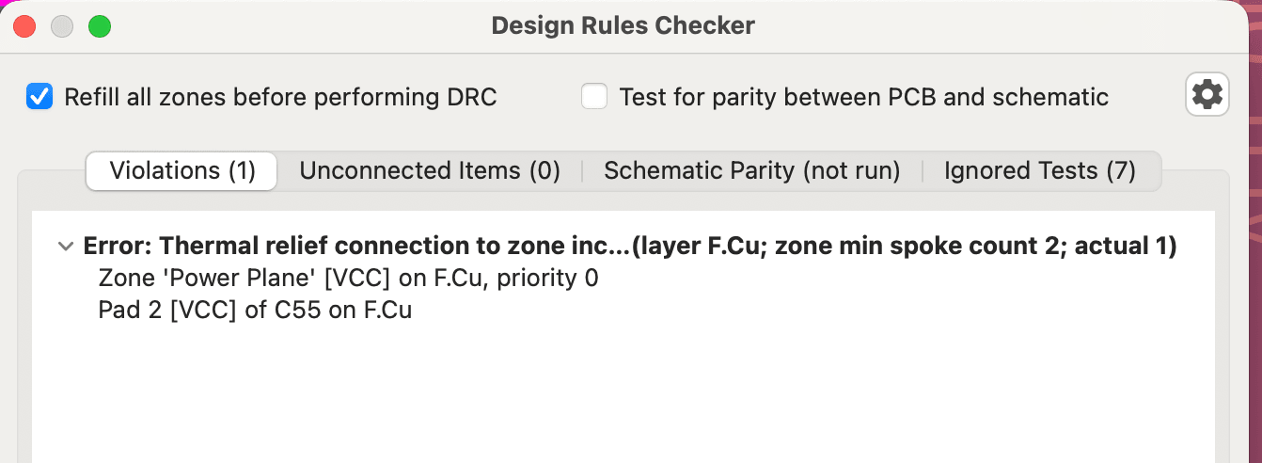
media/logs/screenshots/2026-07-26-2.43.37-pm.png
