tmarhguy/tomato/media/logs/screenshots/2026-07-26-5.35.04-pm.png

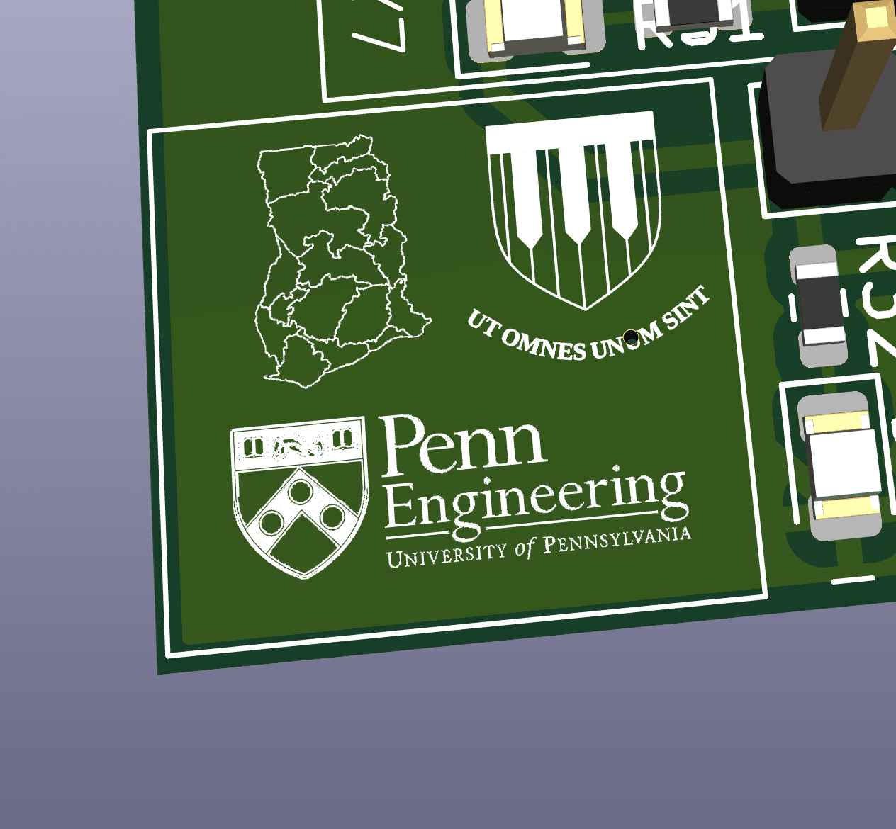
media/logs/screenshots/2026-07-26-5.35.04-pm.png
