tmarhguy/tomato/media/logs/screenshots/2026-07-26-6.12.58-pm.png

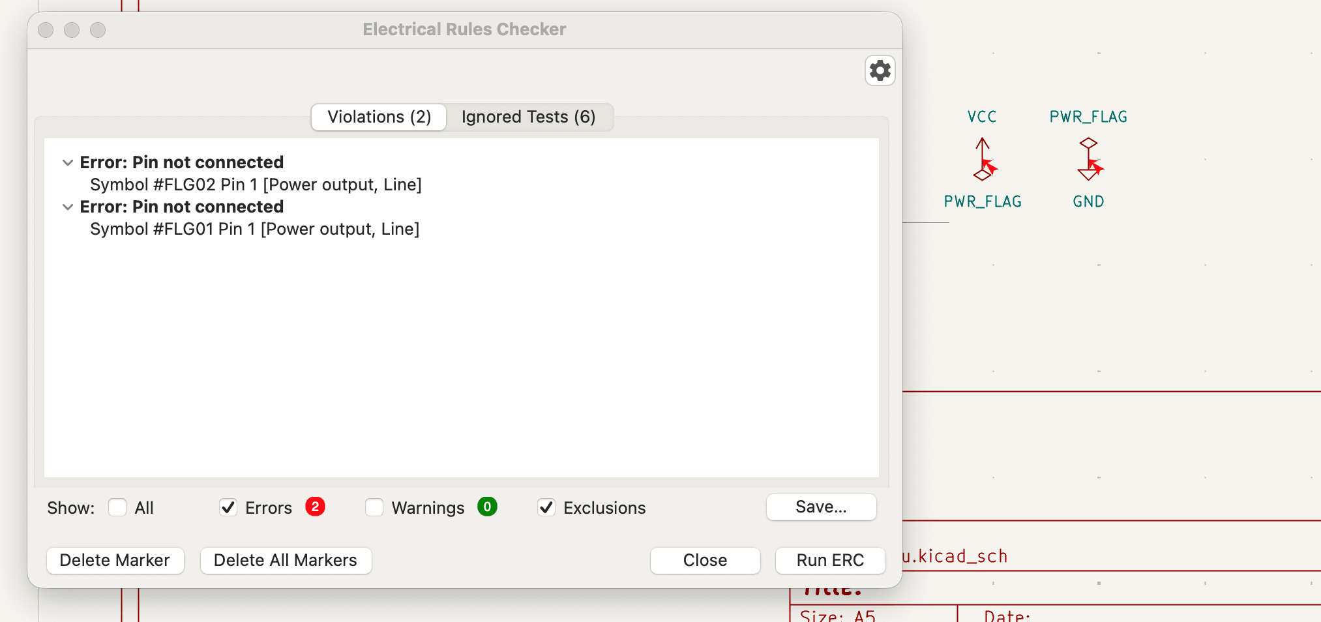
media/logs/screenshots/2026-07-26-6.12.58-pm.png
