tmarhguy/tomato/media/logs/screenshots/2026-08-08-2.02.14-am.png

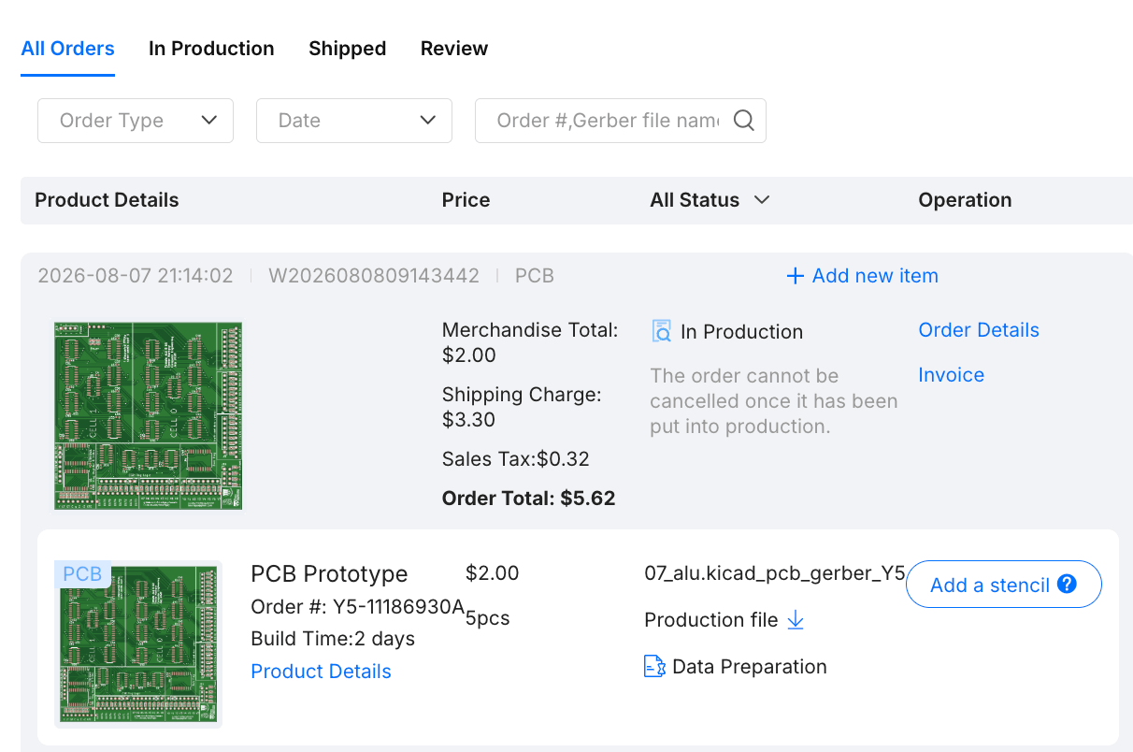
media/logs/screenshots/2026-08-08-2.02.14-am.png
