tmarhguy/tomato/media/logs/screenshots/2026-08-16-11.42.04-am.png

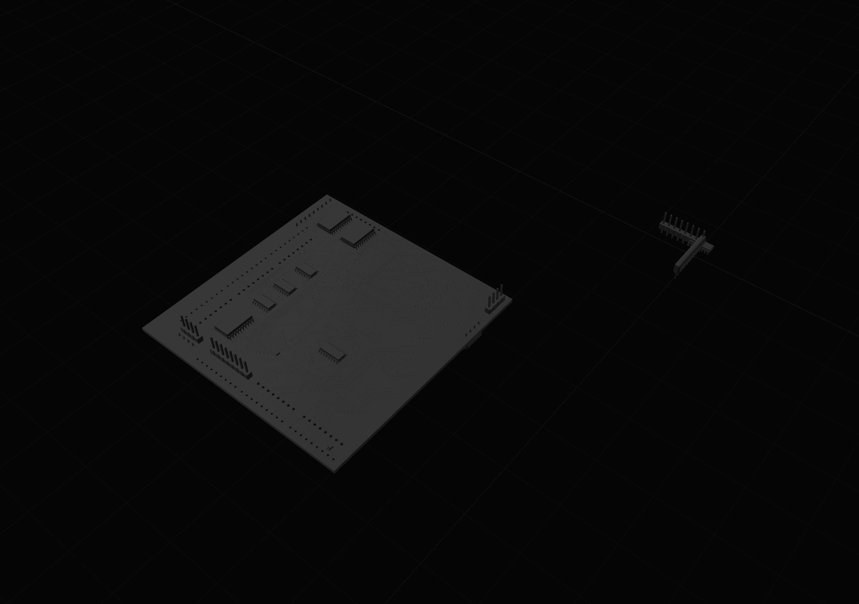
media/logs/screenshots/2026-08-16-11.42.04-am.png
