tmarhguy/tomato/media/notes/04-display-nibble-mux-insight.jpg

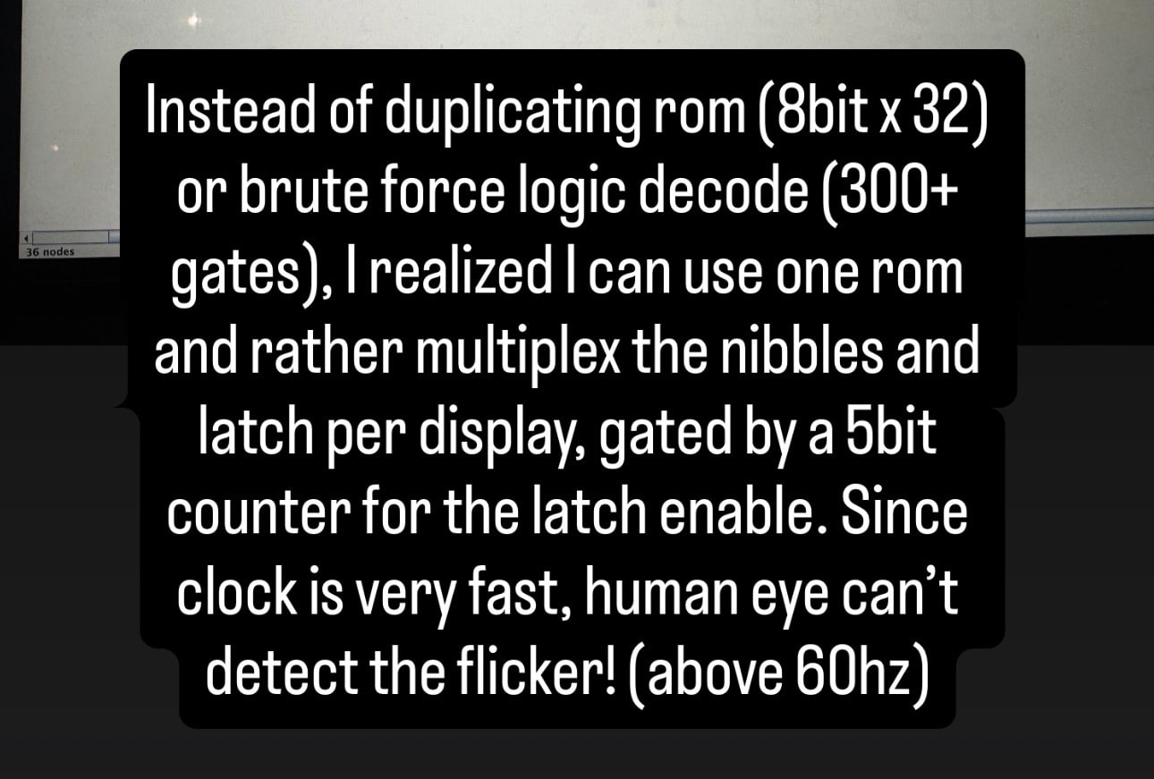
media/notes/04-display-nibble-mux-insight.jpg
