tmarhguy/tomato/media/open-source/librelane-3.0.8.png

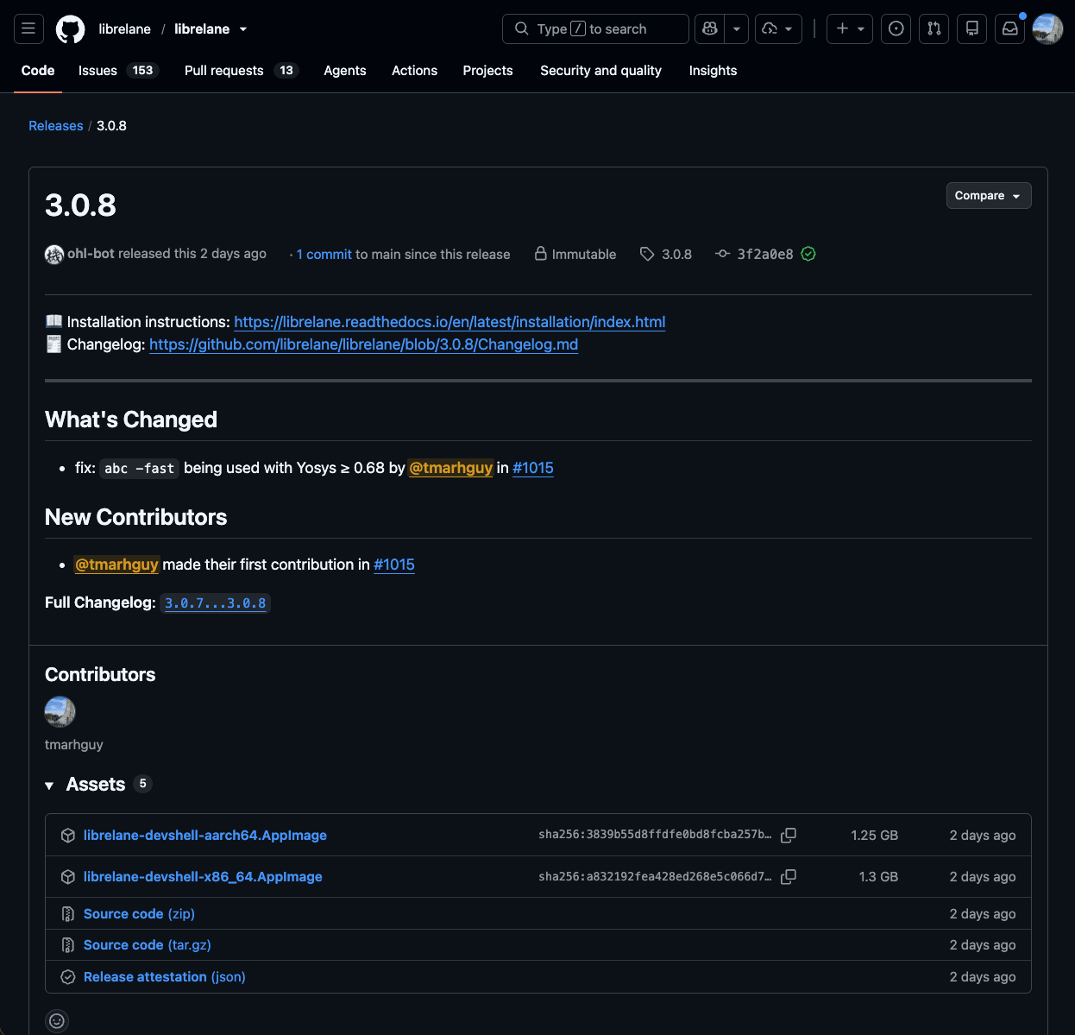
media/open-source/librelane-3.0.8.png
