tmarhguy/tomato/media/spice/01-555-timer-ltspice.png

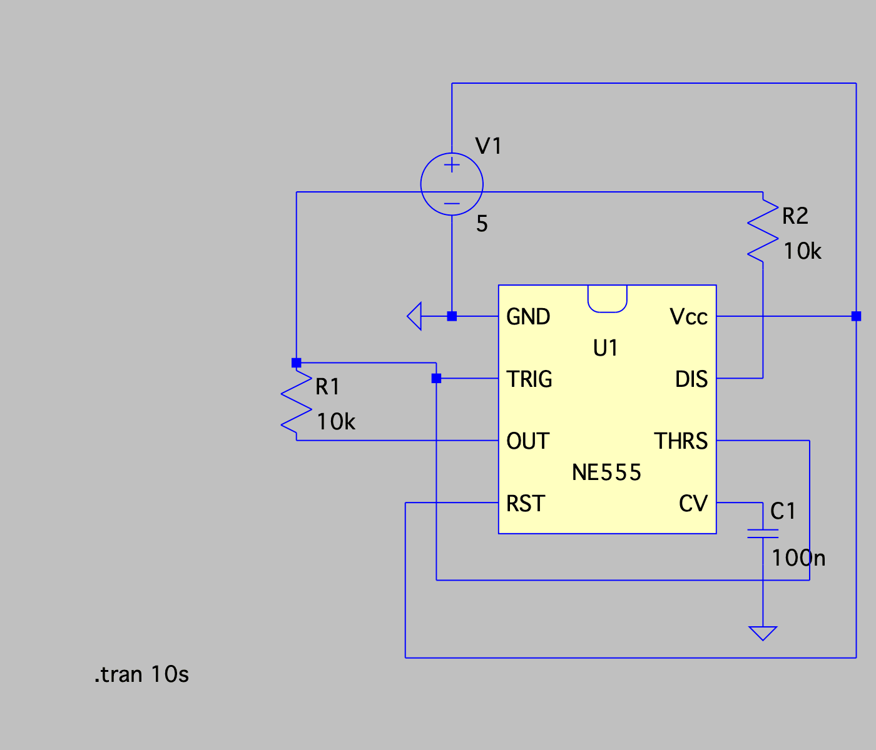
media/spice/01-555-timer-ltspice.png
