tmarhguy/tomato/software/os/assets/ghana-wallpaper.png

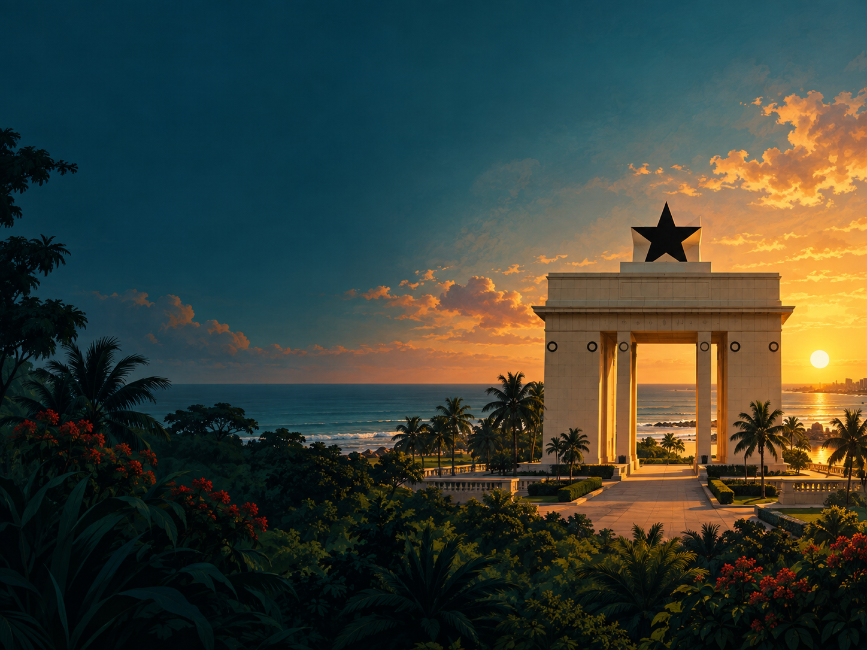
software/os/assets/ghana-wallpaper.png
