tmarhguy/tomato/web/assets/documentation/desktop/tomato-architecture-desktop.webp

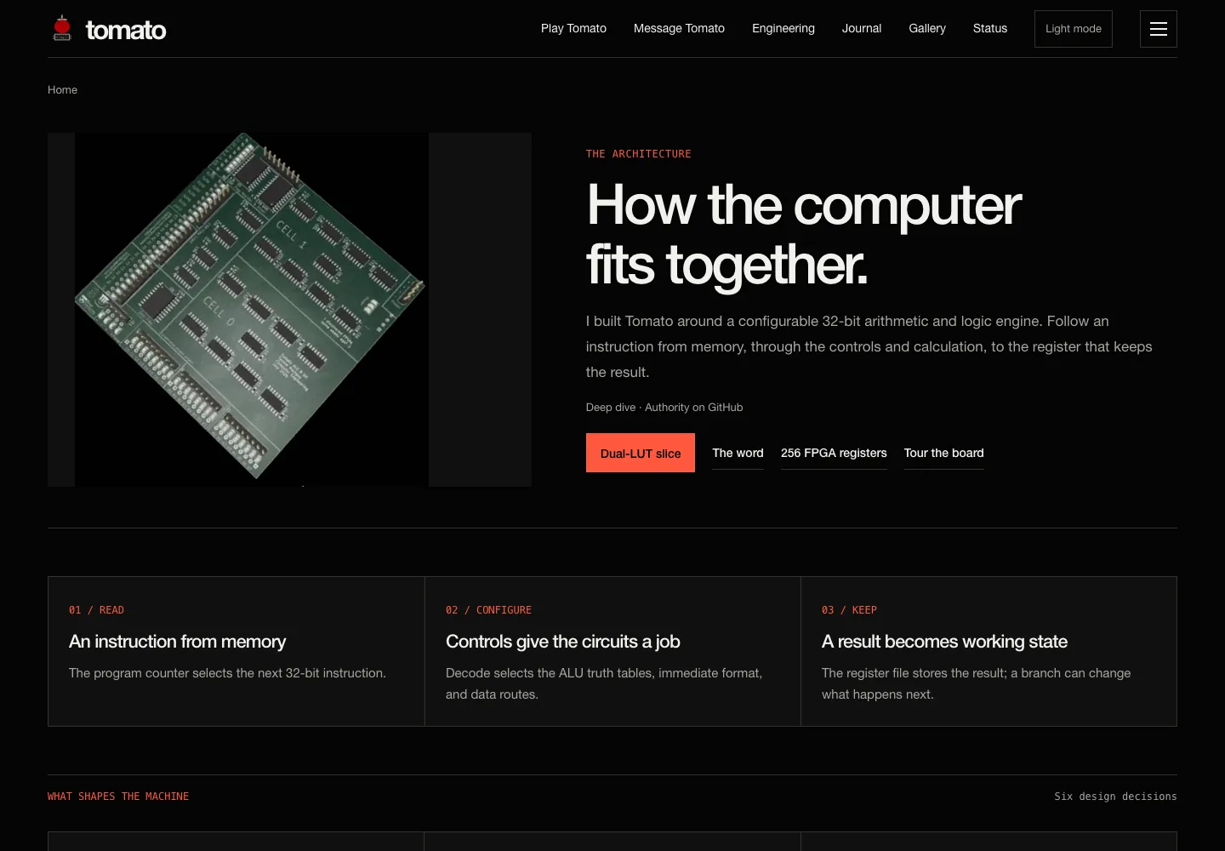
web/assets/documentation/desktop/tomato-architecture-desktop.webp
