tmarhguy/tomato/web/assets/documentation/infinix/tomato-home-infinix.webp

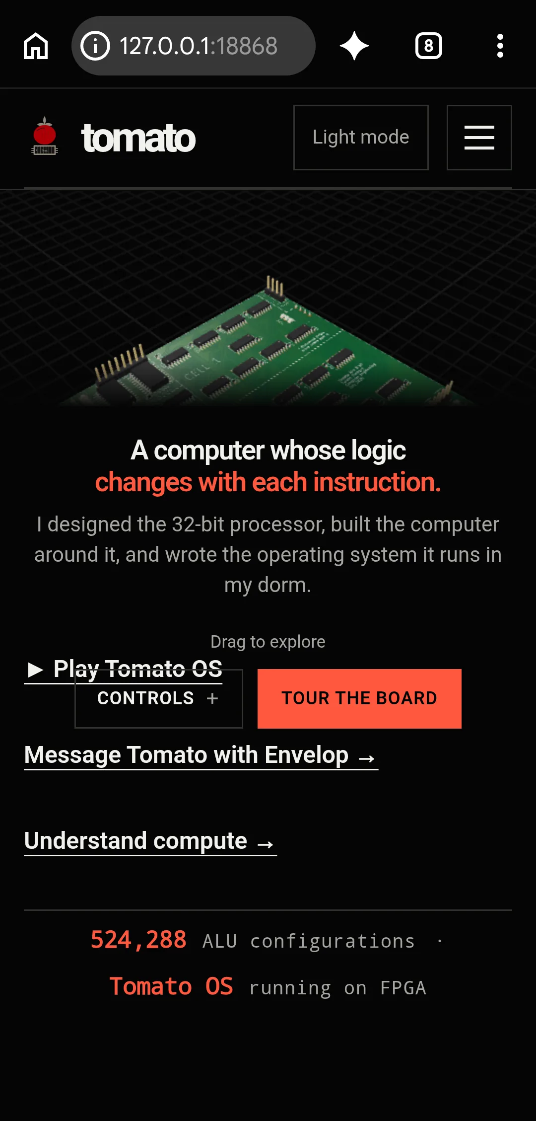
web/assets/documentation/infinix/tomato-home-infinix.webp
