tmarhguy/tomato/web/assets/documentation/infinix/tomato-os-page-infinix.webp

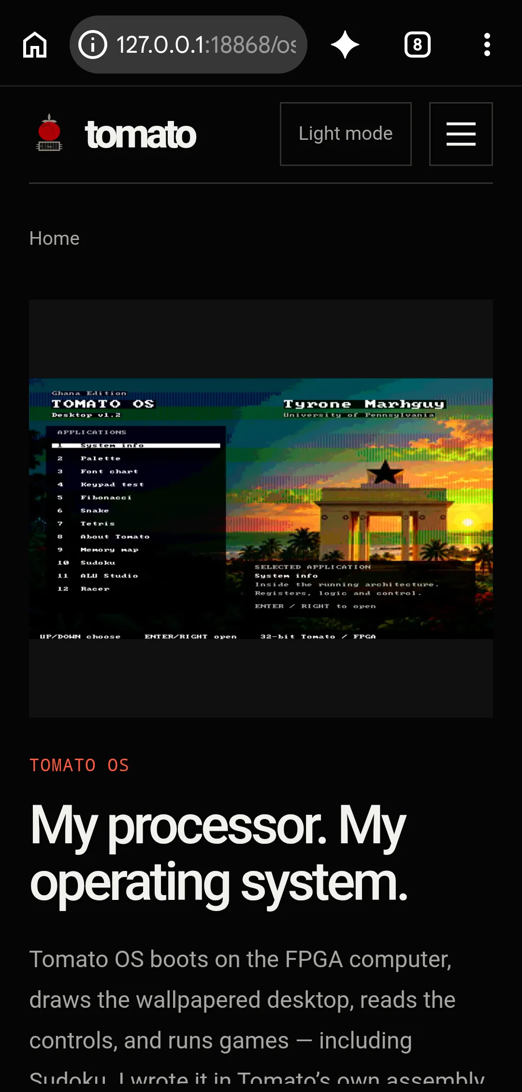
web/assets/documentation/infinix/tomato-os-page-infinix.webp
