tmarhguy/tomato/web/assets/envelop/envelop-on-tomato.webp

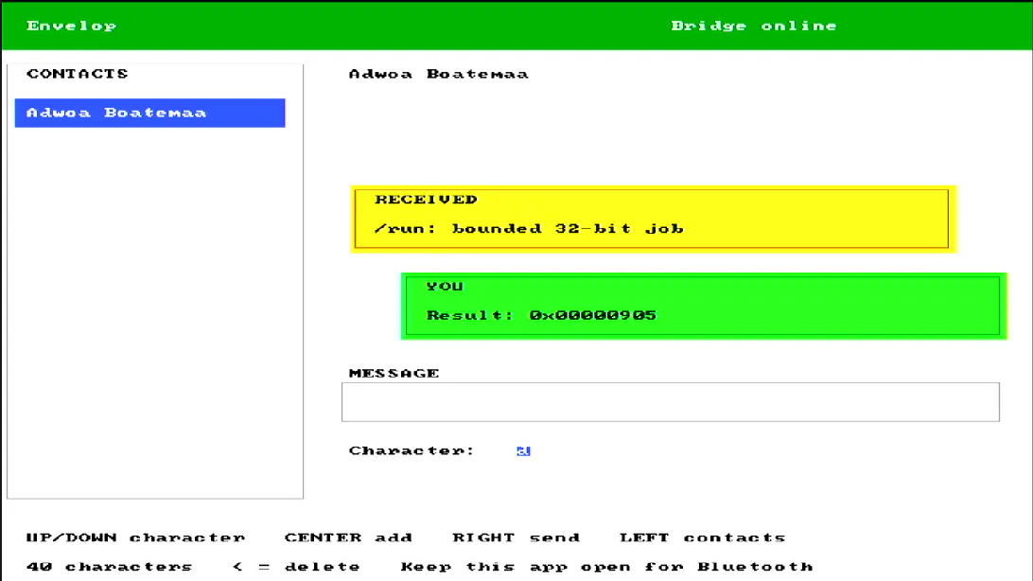
web/assets/envelop/envelop-on-tomato.webp
