tmarhguy/tomato/web/assets/envelop/tomato-compute.webp

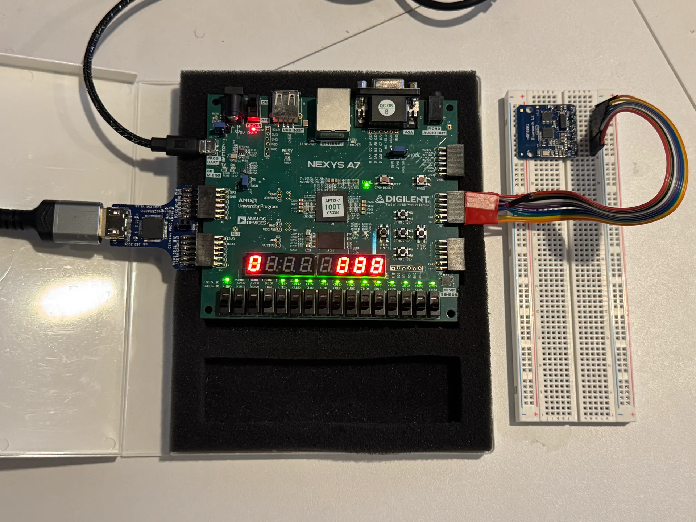
web/assets/envelop/tomato-compute.webp
