tmarhguy/tomato/web/assets/gallery/os/alu-studio-screen-640w.webp

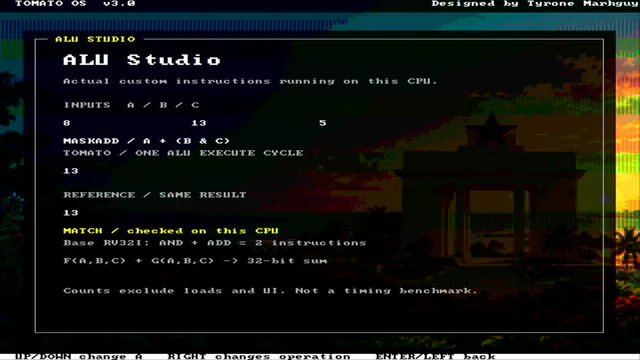
web/assets/gallery/os/alu-studio-screen-640w.webp
