tmarhguy/tomato/web/assets/gallery/os/keyboard-matrix-attempt-1280w.webp

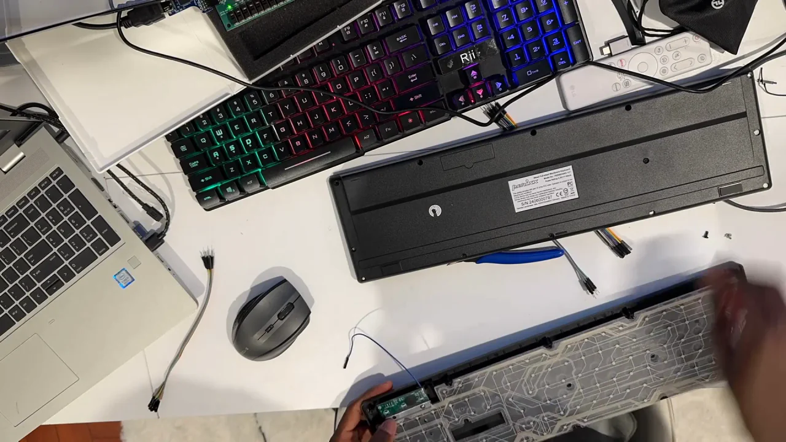
web/assets/gallery/os/keyboard-matrix-attempt-1280w.webp
