tmarhguy/tomato/web/assets/gallery/os/system-info-screen-640w.webp

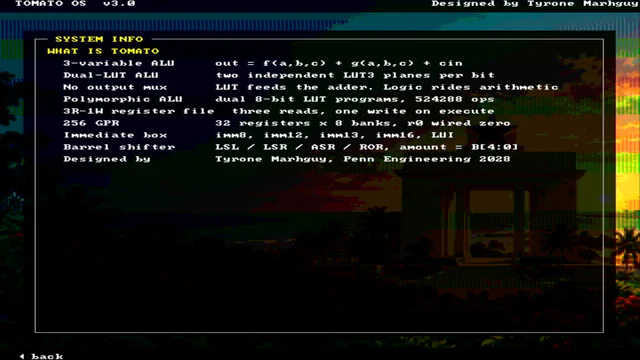
web/assets/gallery/os/system-info-screen-640w.webp
