tmarhguy/tomato/web/assets/gallery/pcb/board-iso-640w.webp

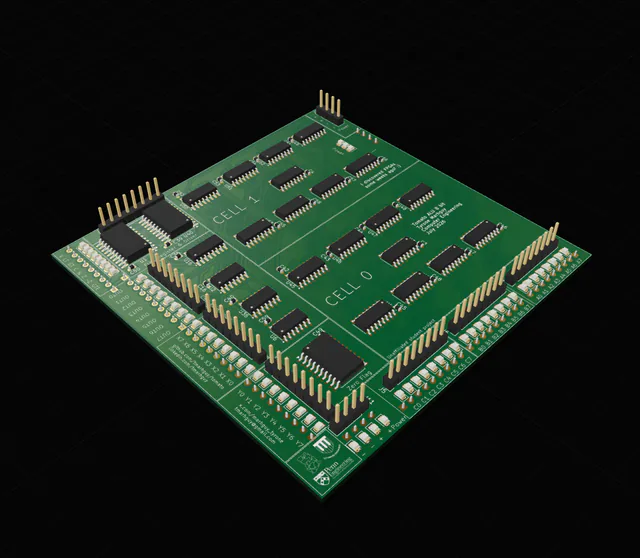
web/assets/gallery/pcb/board-iso-640w.webp
