tmarhguy/tomato/web/assets/gallery/plates/jlcpcb-checkout-640w.webp

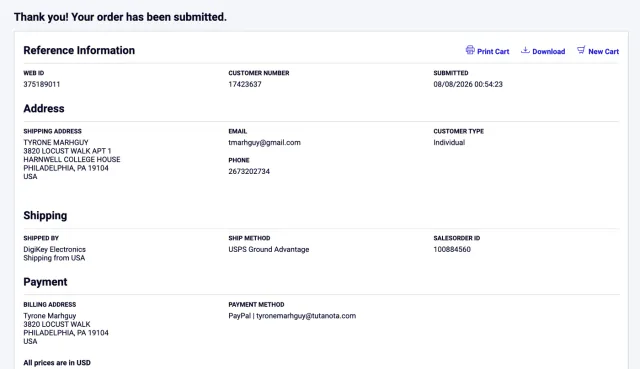
web/assets/gallery/plates/jlcpcb-checkout-640w.webp
