tmarhguy/tomato/web/assets/gallery/plates/microcode-modular-640w.webp

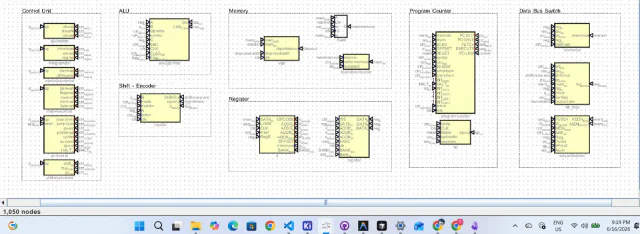
web/assets/gallery/plates/microcode-modular-640w.webp
