tmarhguy/tomato/web/assets/gallery/story/alu/8b-mux-sim-1280w.webp

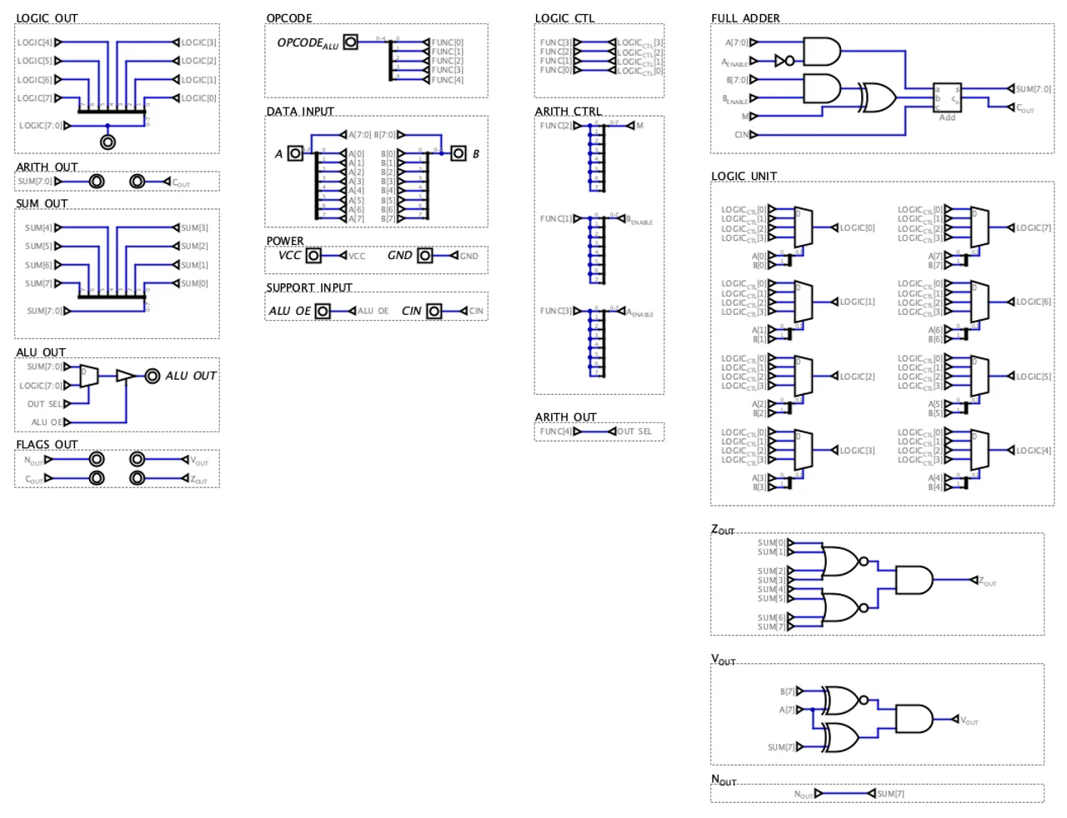
web/assets/gallery/story/alu/8b-mux-sim-1280w.webp
