tmarhguy/tomato/web/assets/gallery/story/alu/barrel-shift-640w.webp

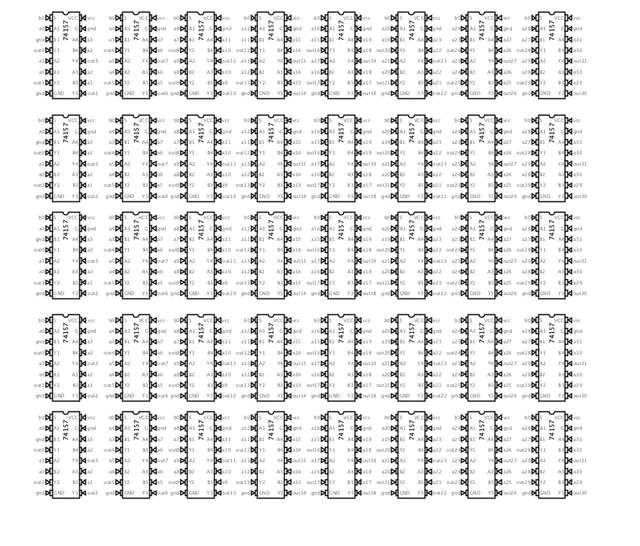
web/assets/gallery/story/alu/barrel-shift-640w.webp
