tmarhguy/tomato/web/assets/gallery/story/alu/barrel-shift-1280w.webp

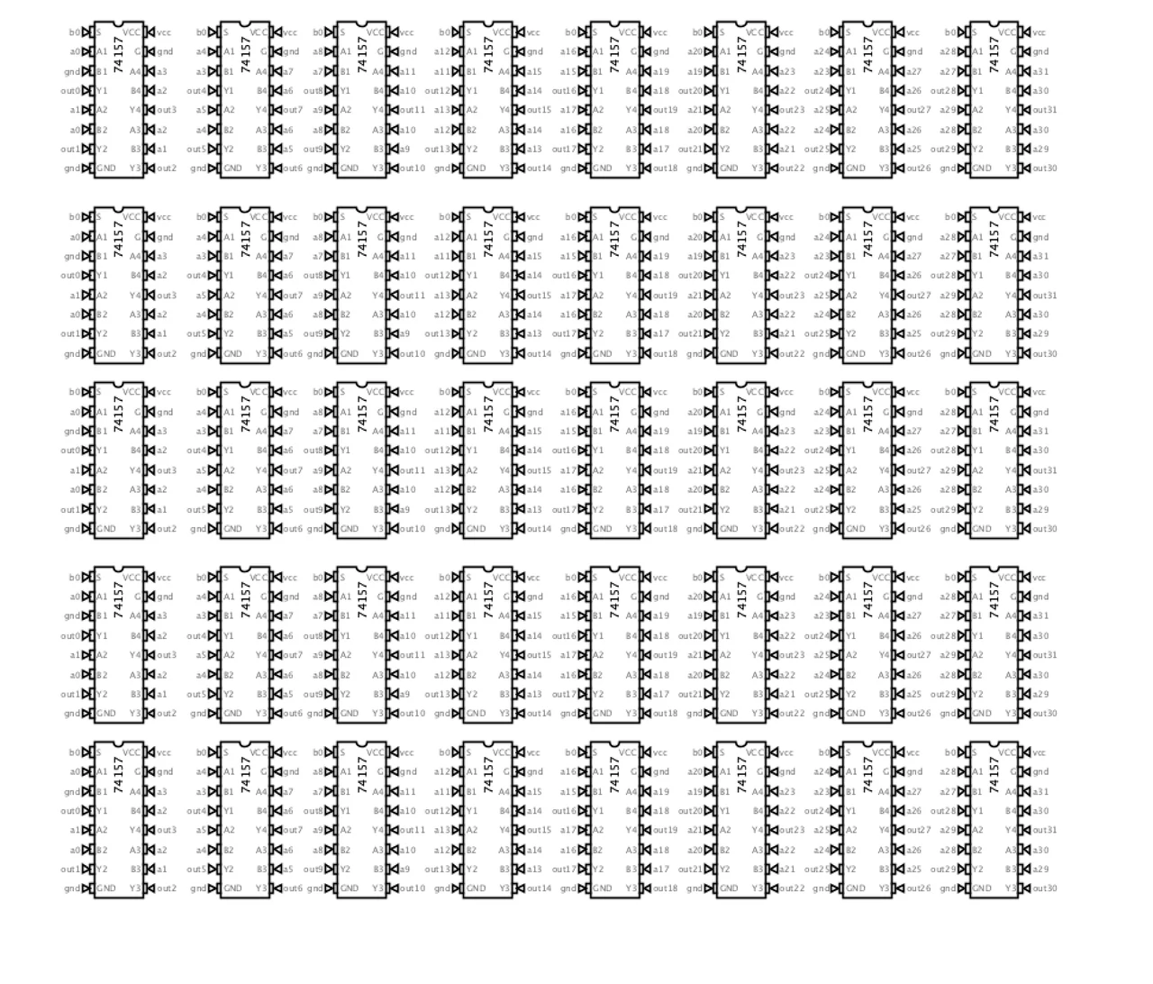
web/assets/gallery/story/alu/barrel-shift-1280w.webp
