tmarhguy/tomato/web/assets/gallery/story/arch/64b-machine-1280w.webp

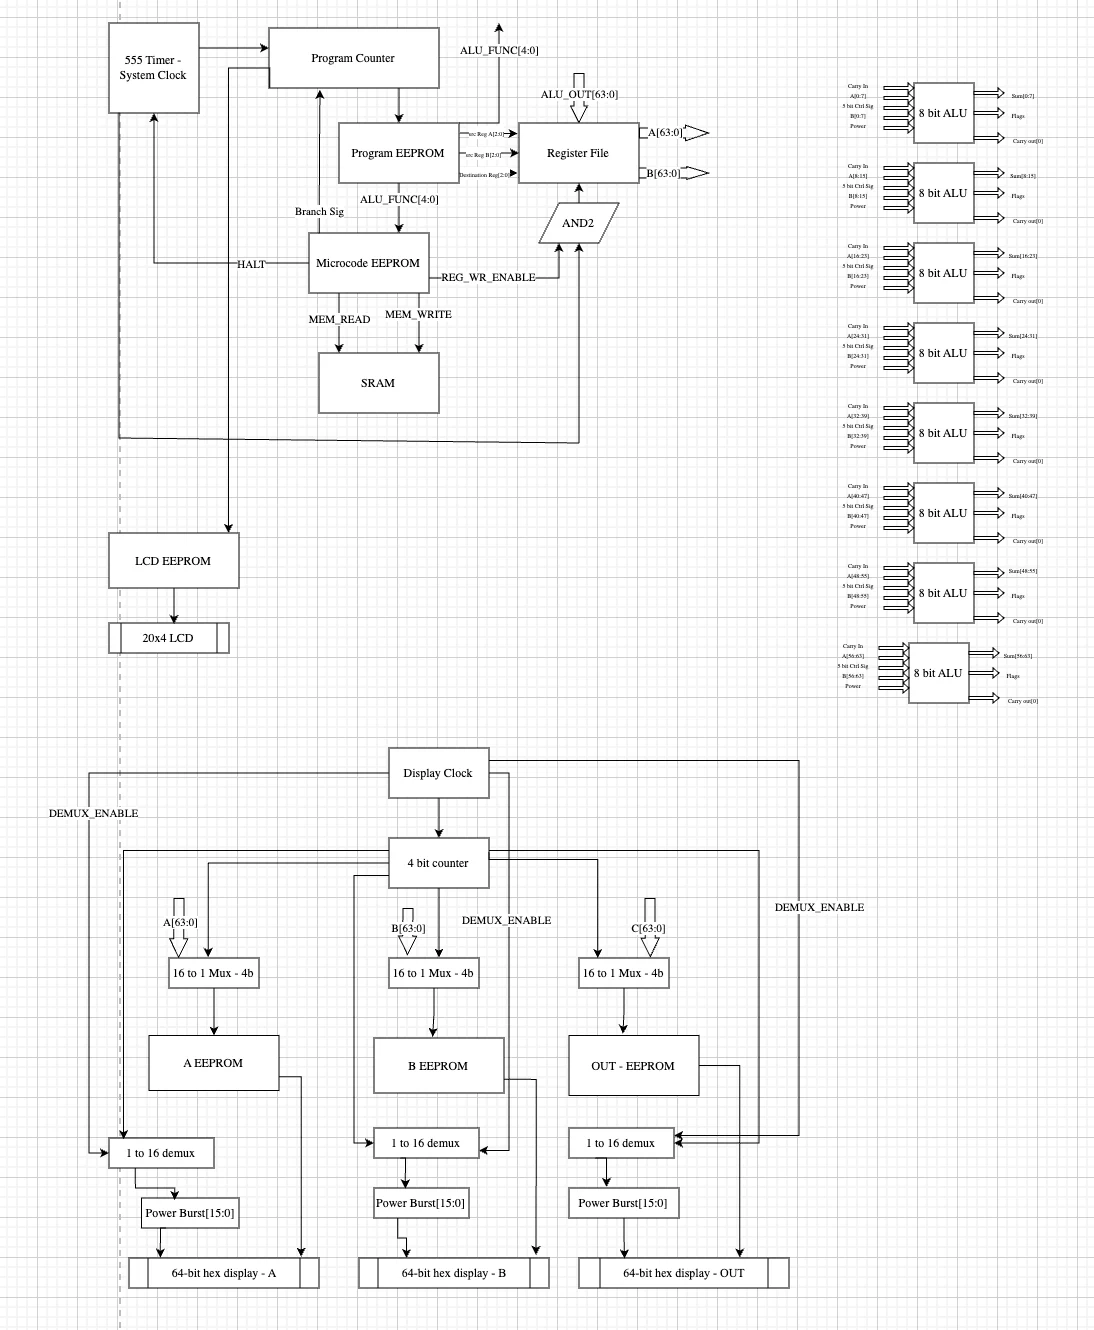
web/assets/gallery/story/arch/64b-machine-1280w.webp
