tmarhguy/tomato/web/assets/gallery/story/bus/mmio-passed-640w.webp

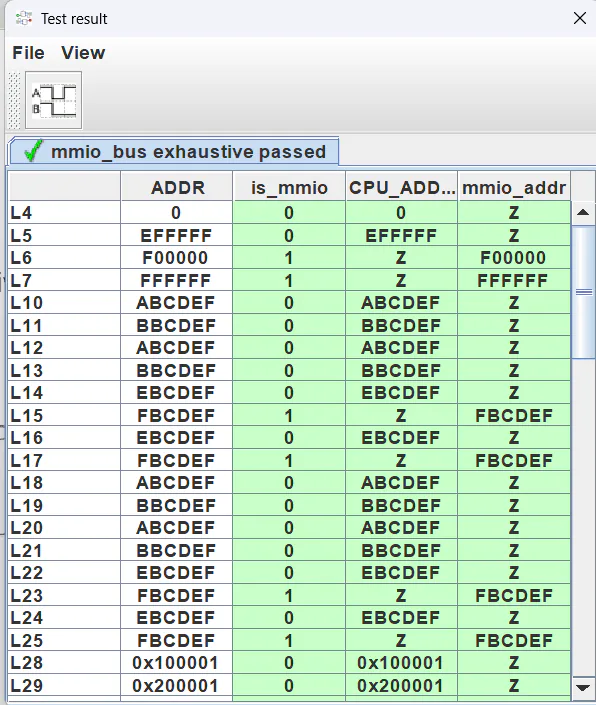
web/assets/gallery/story/bus/mmio-passed-640w.webp
