tmarhguy/tomato/web/assets/gallery/story/control/datapath-32b-128w.webp

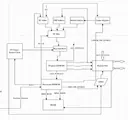
web/assets/gallery/story/control/datapath-32b-128w.webp
