tmarhguy/tomato/web/assets/gallery/story/control/eeprom-fanout-640w.webp

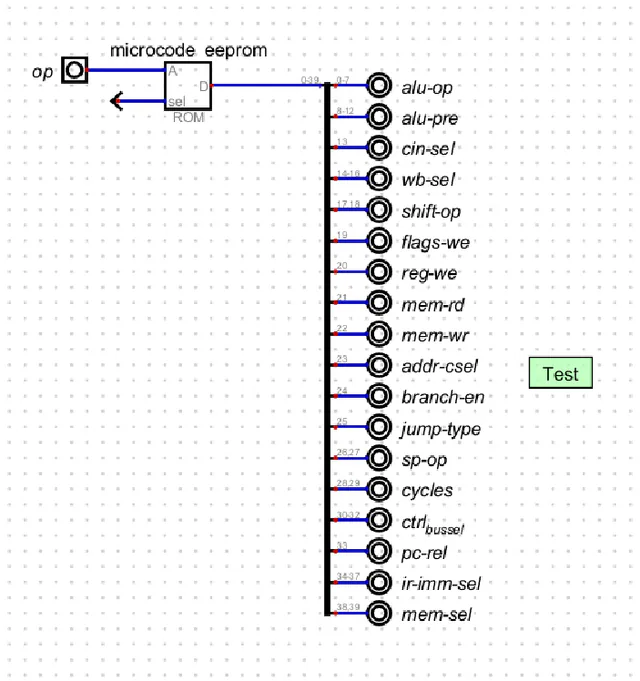
web/assets/gallery/story/control/eeprom-fanout-640w.webp
