tmarhguy/tomato/web/assets/gallery/story/digital/main-2026-06-06-640w.webp

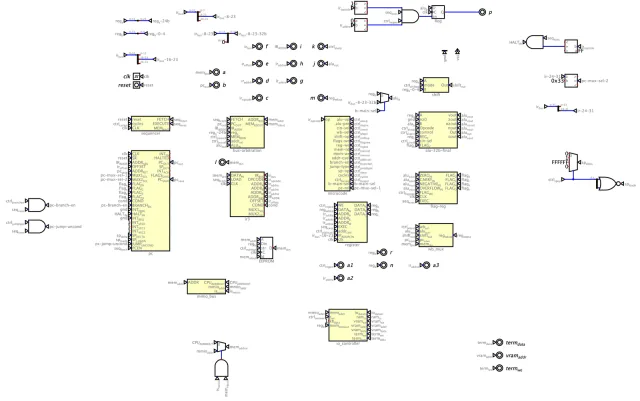
web/assets/gallery/story/digital/main-2026-06-06-640w.webp
