tmarhguy/tomato/web/assets/gallery/story/hardware/nexys-a7-128w.webp

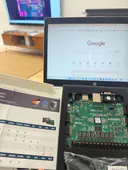
web/assets/gallery/story/hardware/nexys-a7-128w.webp
