tmarhguy/tomato/web/assets/gallery/story/kicad/24cm-3d-128w.webp

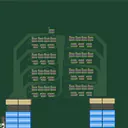
web/assets/gallery/story/kicad/24cm-3d-128w.webp
