tmarhguy/tomato/web/assets/gallery/story/kicad/ratsnest-32b-640w.webp

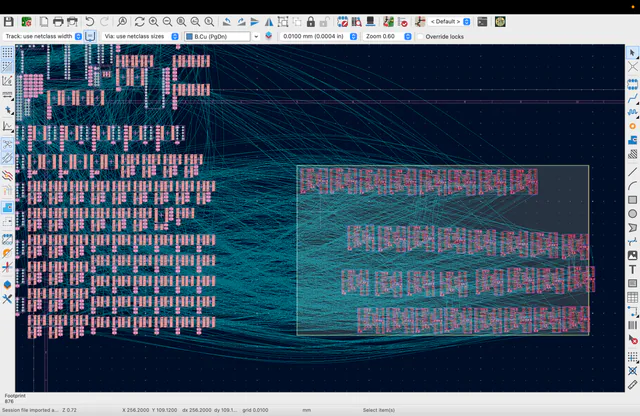
web/assets/gallery/story/kicad/ratsnest-32b-640w.webp
