tmarhguy/tomato/web/assets/gallery/story/notes/hex-patterns-640w.webp

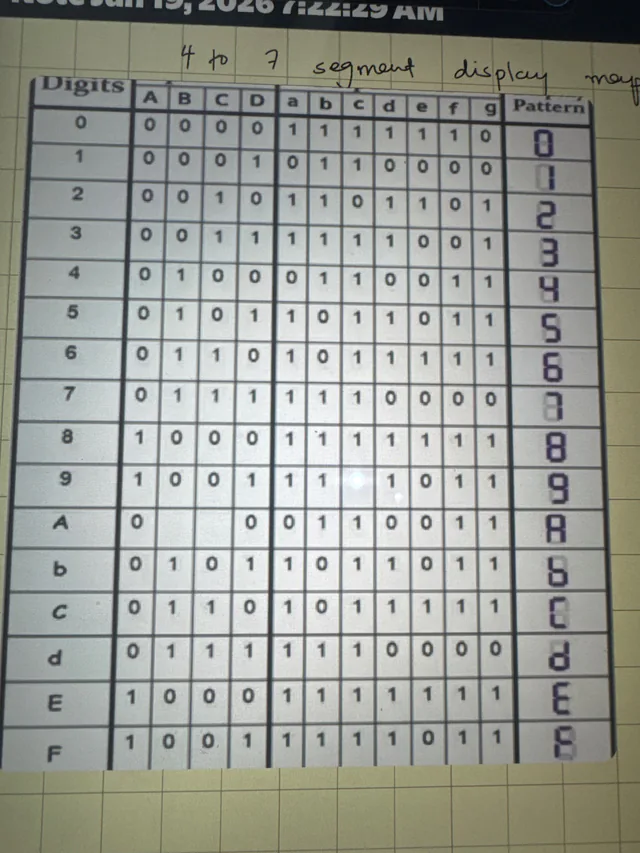
web/assets/gallery/story/notes/hex-patterns-640w.webp
