tmarhguy/tomato/web/assets/gallery/story/notes/hex-to-rom-128w.webp

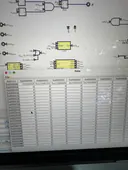
web/assets/gallery/story/notes/hex-to-rom-128w.webp
