tmarhguy/tomato/web/assets/gallery/story/open-source/openroad-activity-640w.webp

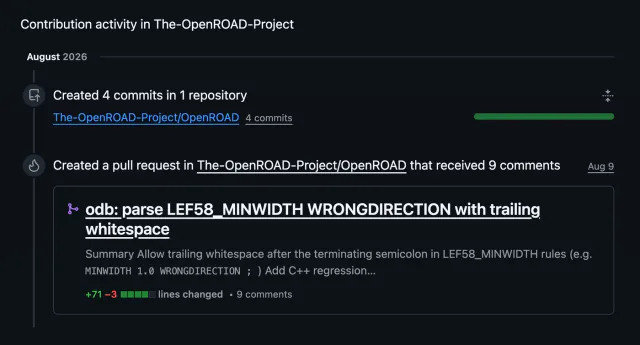
web/assets/gallery/story/open-source/openroad-activity-640w.webp
