tmarhguy/tomato/web/assets/gallery/story/run/custom-program-1280w.webp

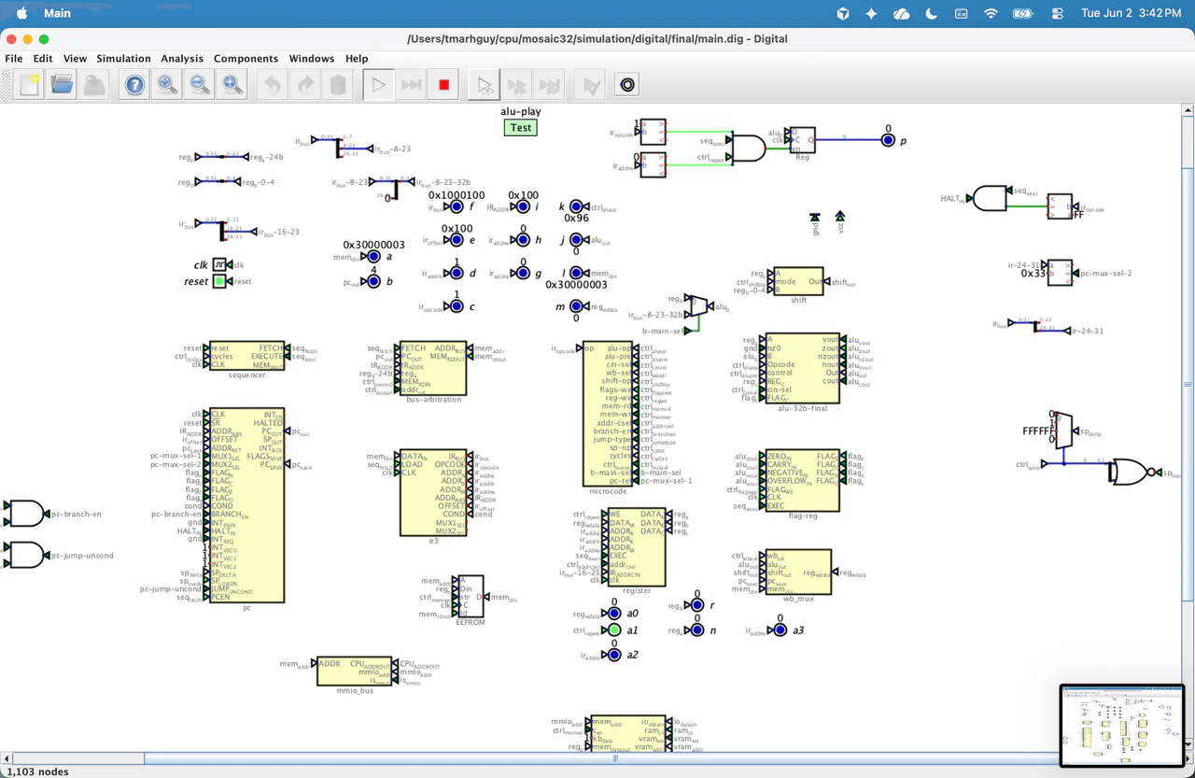
web/assets/gallery/story/run/custom-program-1280w.webp
