tmarhguy/tomato/web/assets/gallery/story/run/fibonacci-register-1280w.webp

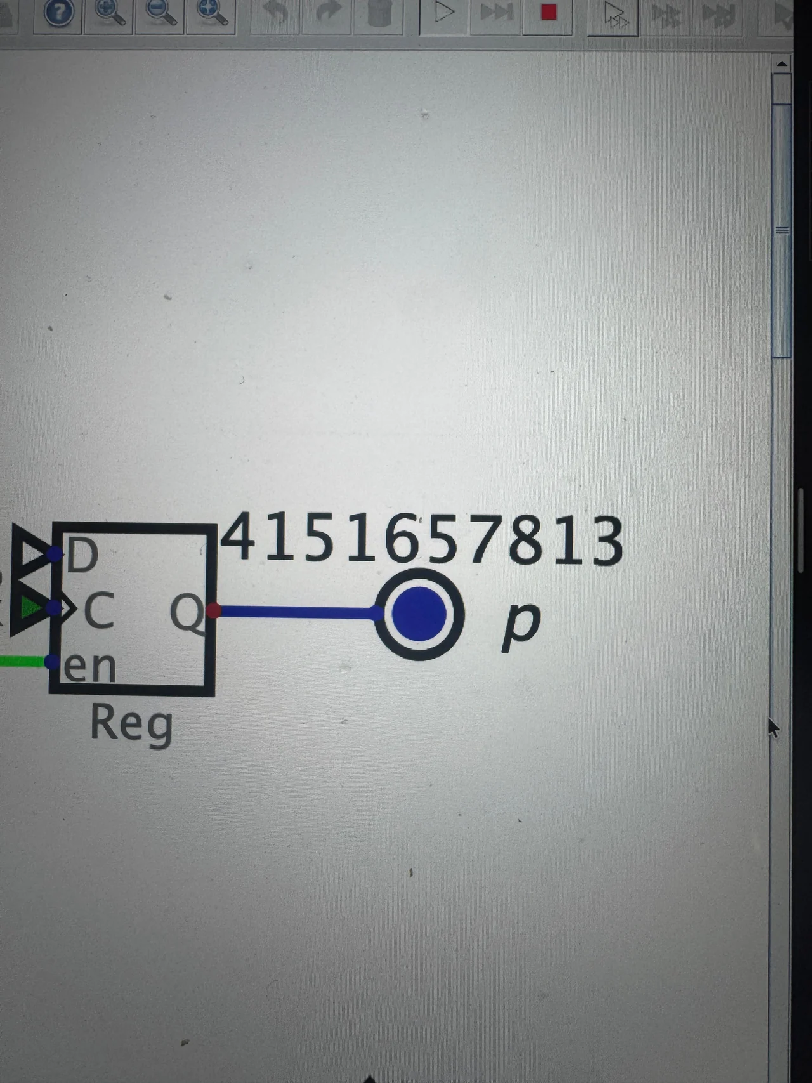
web/assets/gallery/story/run/fibonacci-register-1280w.webp
