tmarhguy/tomato/web/assets/gallery/story/run/html-emulator-1280w.webp

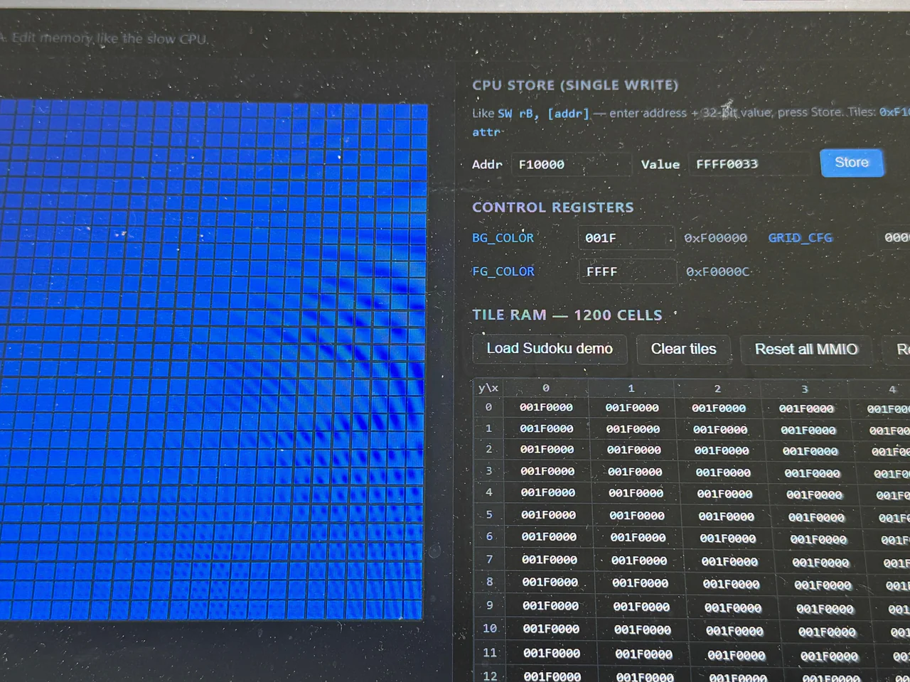
web/assets/gallery/story/run/html-emulator-1280w.webp
