tmarhguy/tomato/web/assets/gallery/story/spice/555-clock-128w.webp

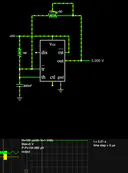
web/assets/gallery/story/spice/555-clock-128w.webp
