tmarhguy/tomato/web/assets/og/tomato-envelop.webp

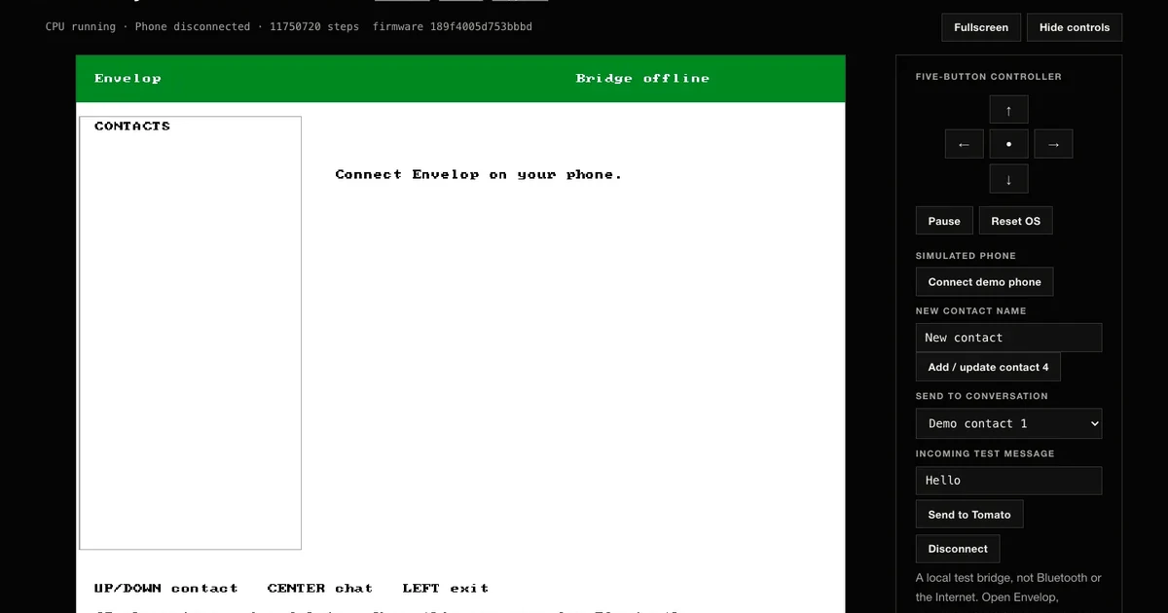
web/assets/og/tomato-envelop.webp
