tmarhguy/tomato/web/assets/pcb/board-iso-light.webp

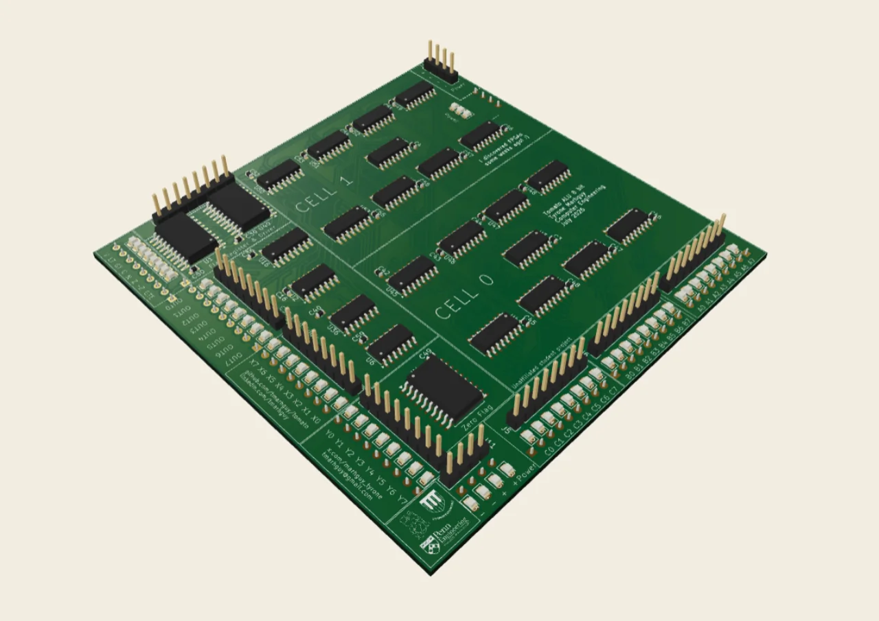
web/assets/pcb/board-iso-light.webp
