tmarhguy/tomato/web/assets/pcb/immersion_white_poster.webp

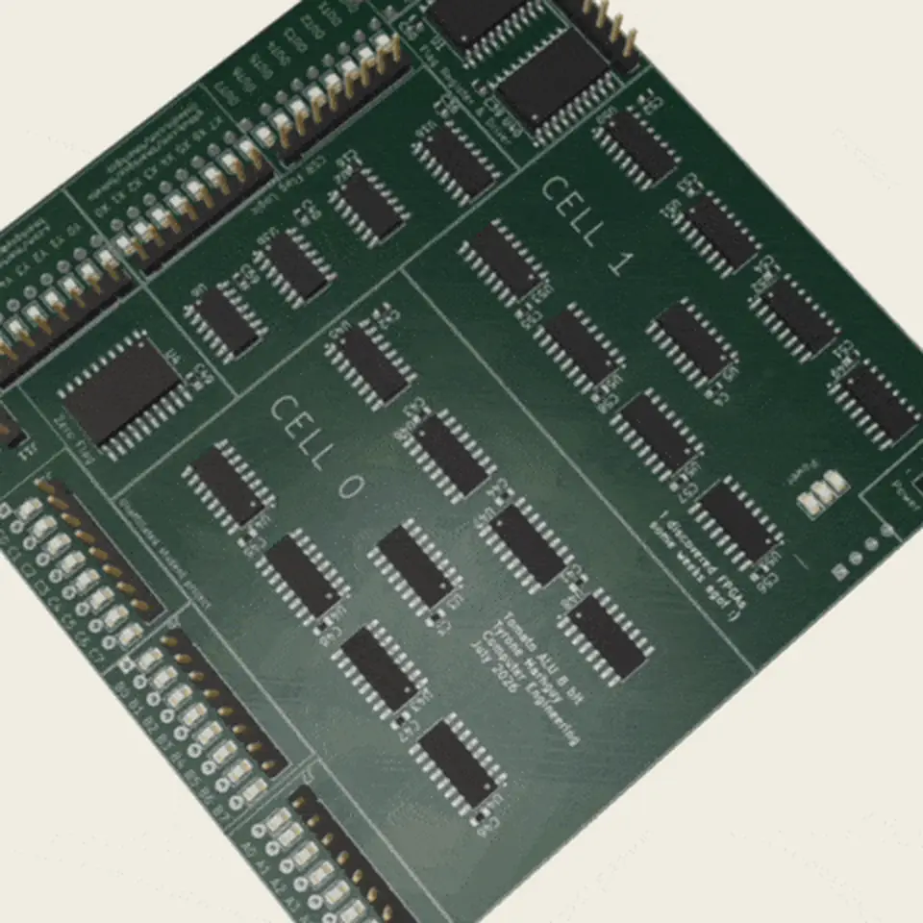
web/assets/pcb/immersion_white_poster.webp
