tmarhguy/tomato/web/assets/plates/digikey.jpg

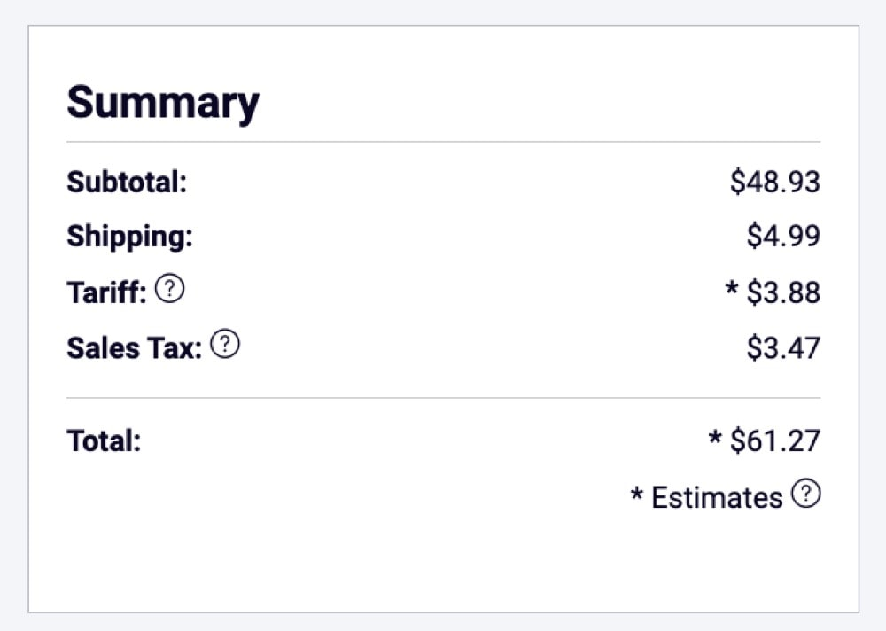
web/assets/plates/digikey.jpg
