tmarhguy/tomato/web/assets/story/control/eeprom-fanout.png

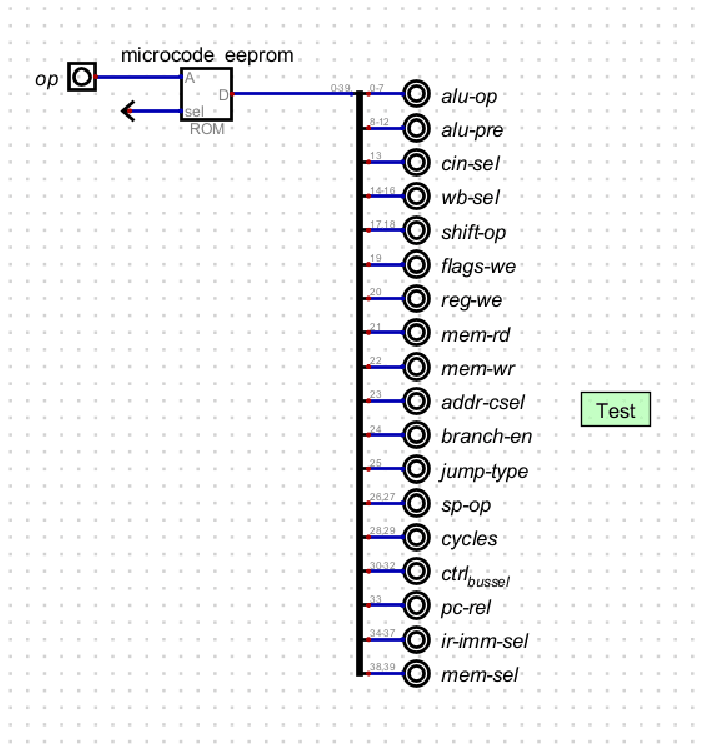
web/assets/story/control/eeprom-fanout.png
