tmarhguy/tomato/web/assets/story/field/atlantic-city.jpg

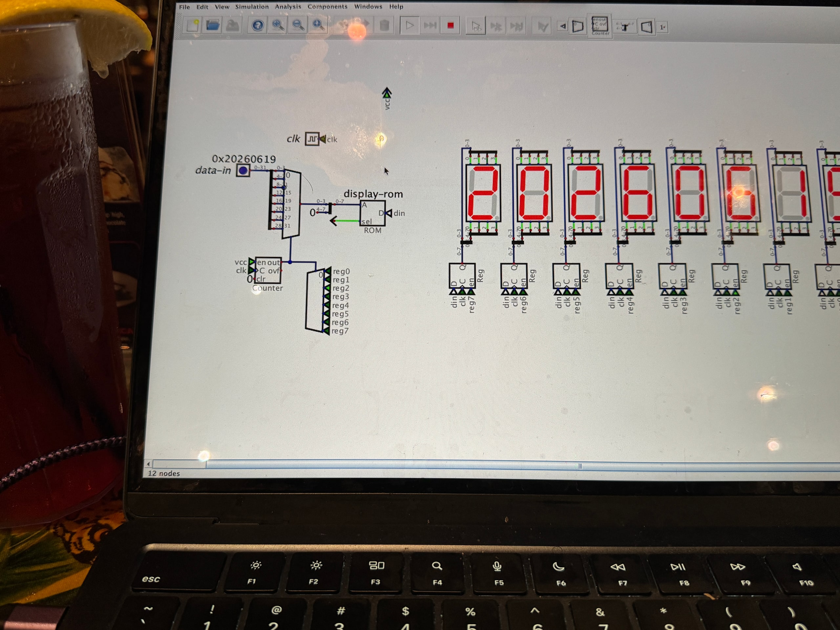
web/assets/story/field/atlantic-city.jpg
