tmarhguy/tomato/media/orders/bom-74act-line-items.png

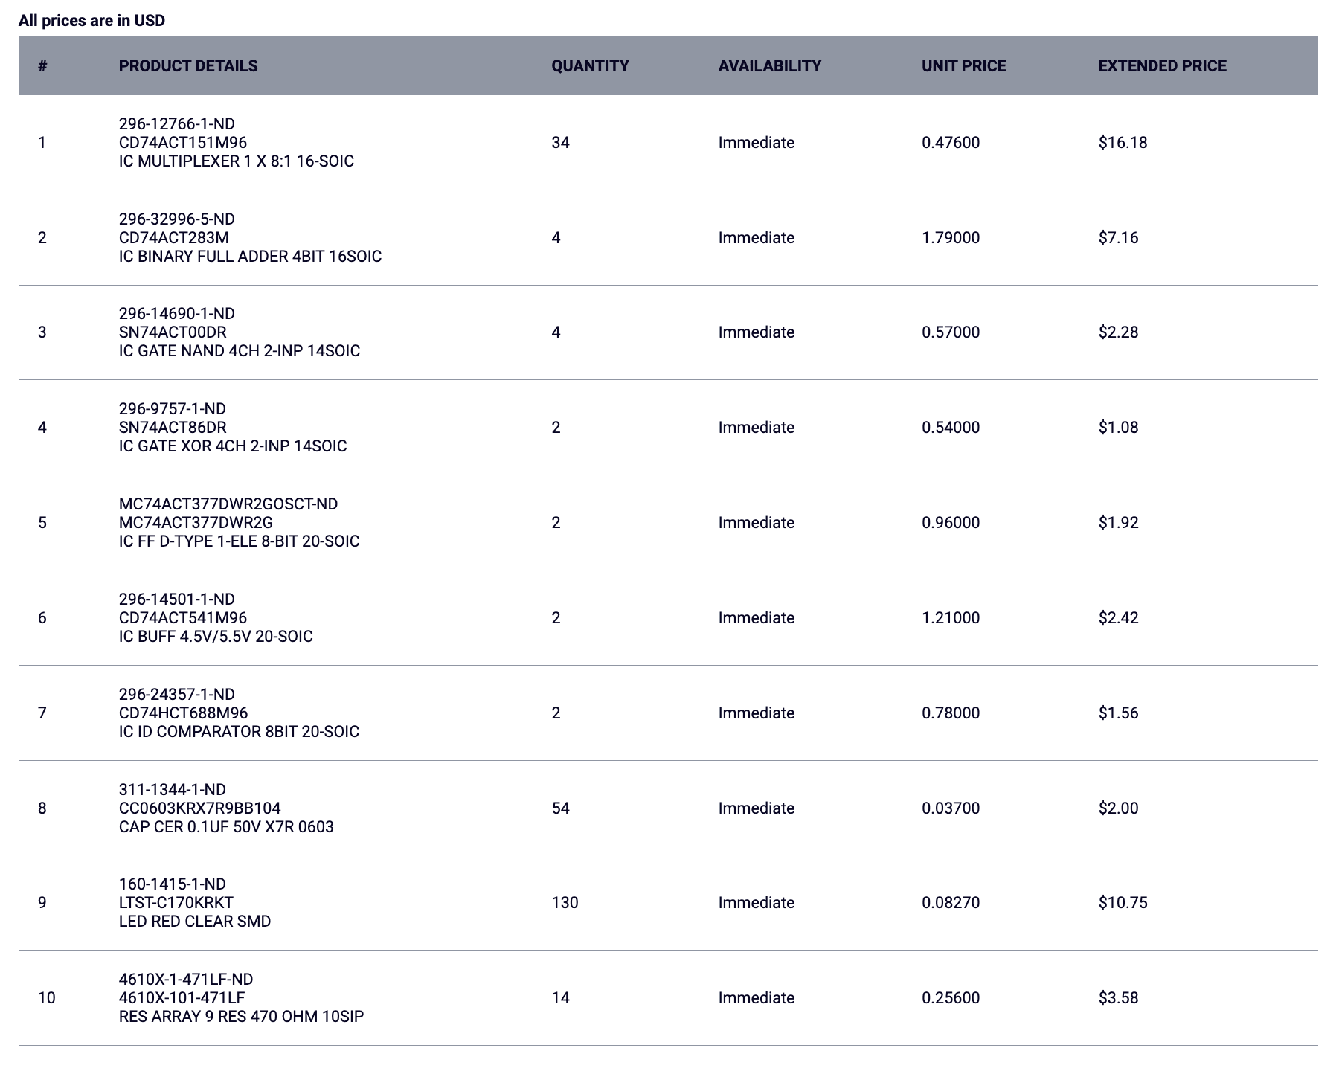
media/orders/bom-74act-line-items.png
