tmarhguy/tomato/web/assets/gallery/orders/hdmi-capture-receipt-640w.webp

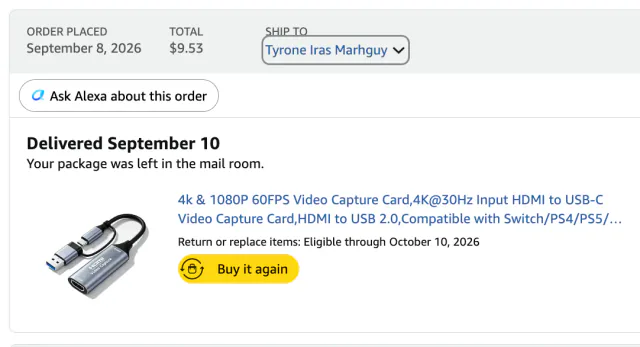
web/assets/gallery/orders/hdmi-capture-receipt-640w.webp
