tmarhguy/tomato/web/assets/assembly/3d-green-cells-july.png

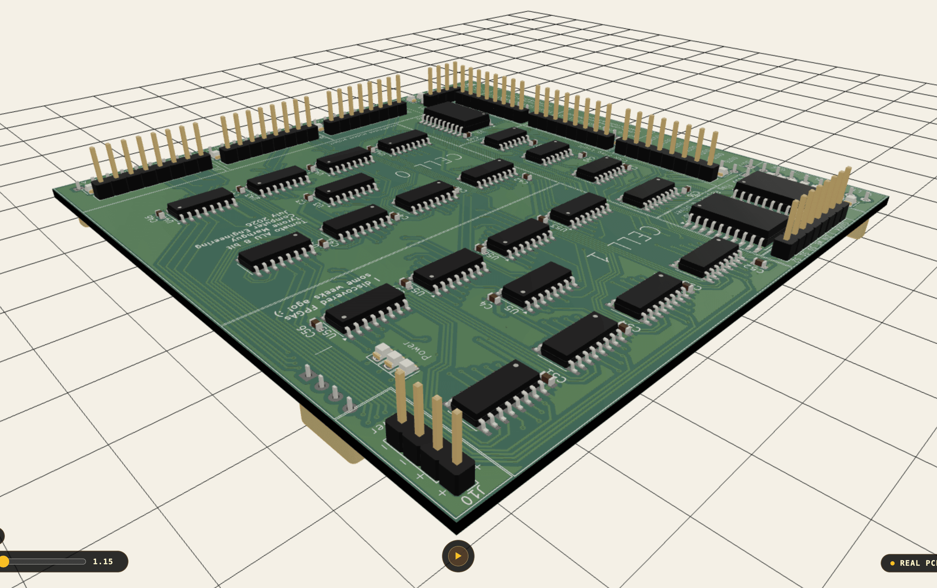
web/assets/assembly/3d-green-cells-july.png
