tmarhguy/tomato/web/assets/assembly/3d-olive-penn-branding.png

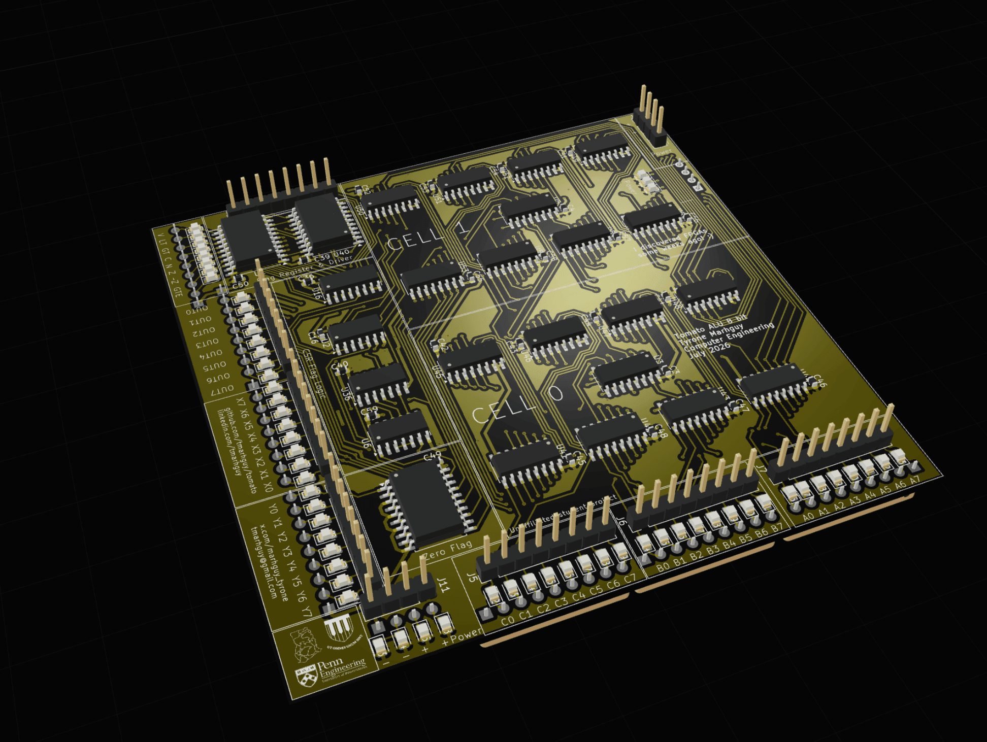
web/assets/assembly/3d-olive-penn-branding.png
