tmarhguy/tomato/web/assets/assembly/alu_back.png

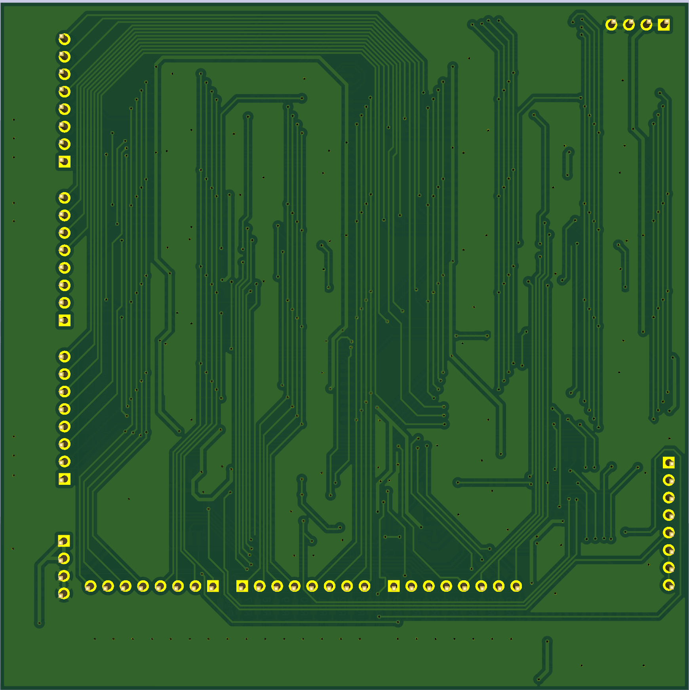
web/assets/assembly/alu_back.png
