tmarhguy/tomato/web/assets/assembly/fpga-num-seg-disp.webp

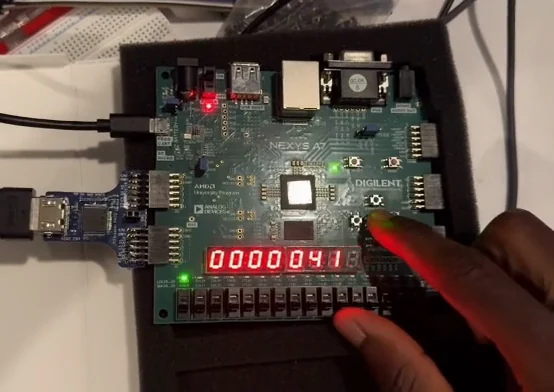
web/assets/assembly/fpga-num-seg-disp.webp
