tmarhguy/tomato/web/assets/assembly/placing-and-soldering.webp

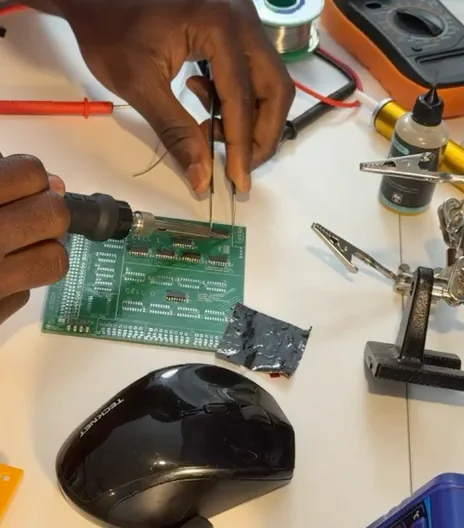
web/assets/assembly/placing-and-soldering.webp
