tmarhguy/tomato/web/assets/gallery/assembly/alu_back-128w.webp

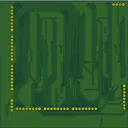
web/assets/gallery/assembly/alu_back-128w.webp
