tmarhguy/tomato/web/assets/gallery/assembly/digikey-box-1280w.webp

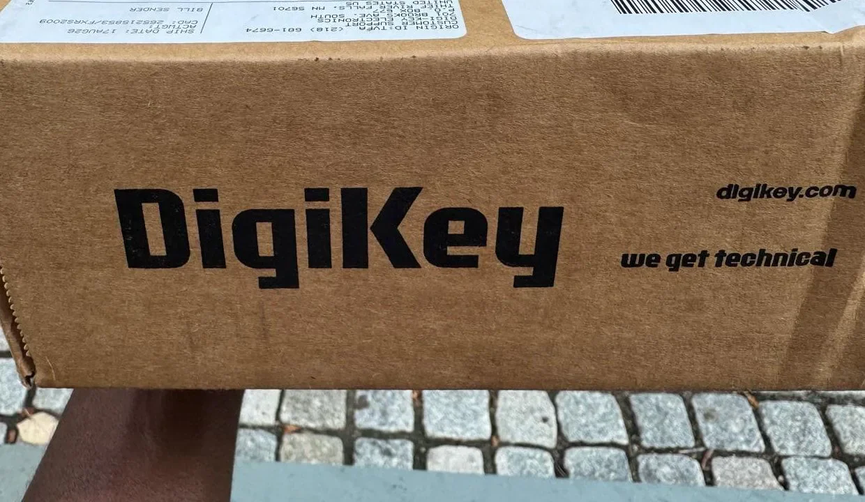
web/assets/gallery/assembly/digikey-box-1280w.webp
