tmarhguy/tomato/web/assets/gallery/assembly/layout-tomato-alu-8bit-128w.webp

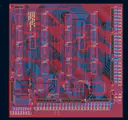
web/assets/gallery/assembly/layout-tomato-alu-8bit-128w.webp
