tmarhguy/tomato/web/assets/assembly/hdmi-test.webp

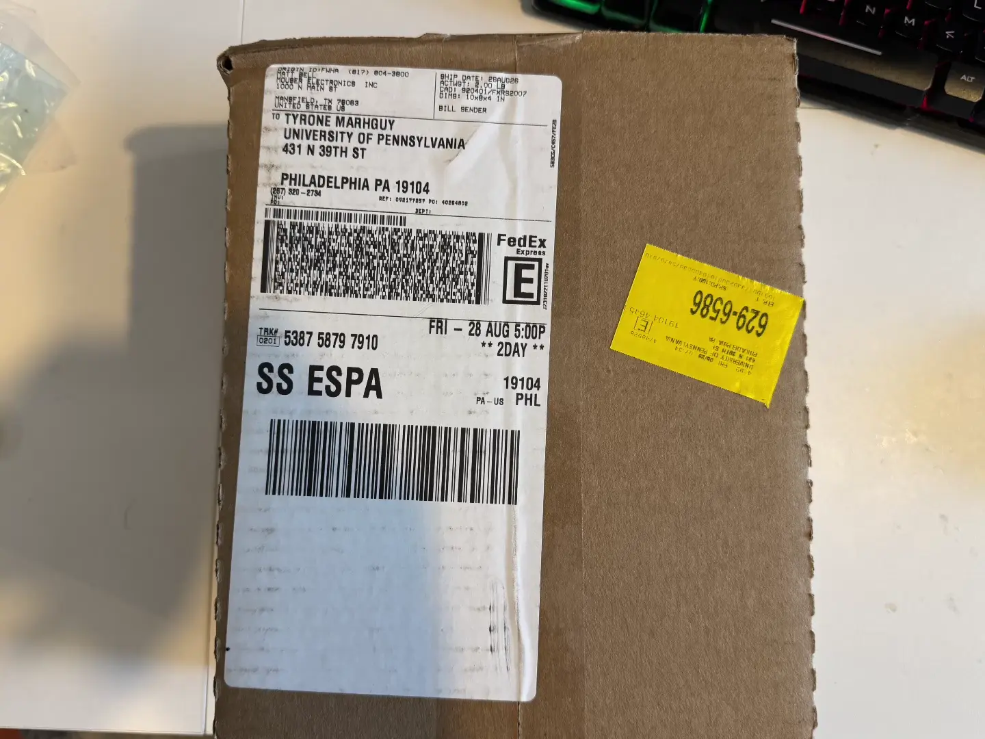
web/assets/assembly/hdmi-test.webp
