tmarhguy/tomato/web/assets/documentation/desktop/tomato-verification-desktop.webp

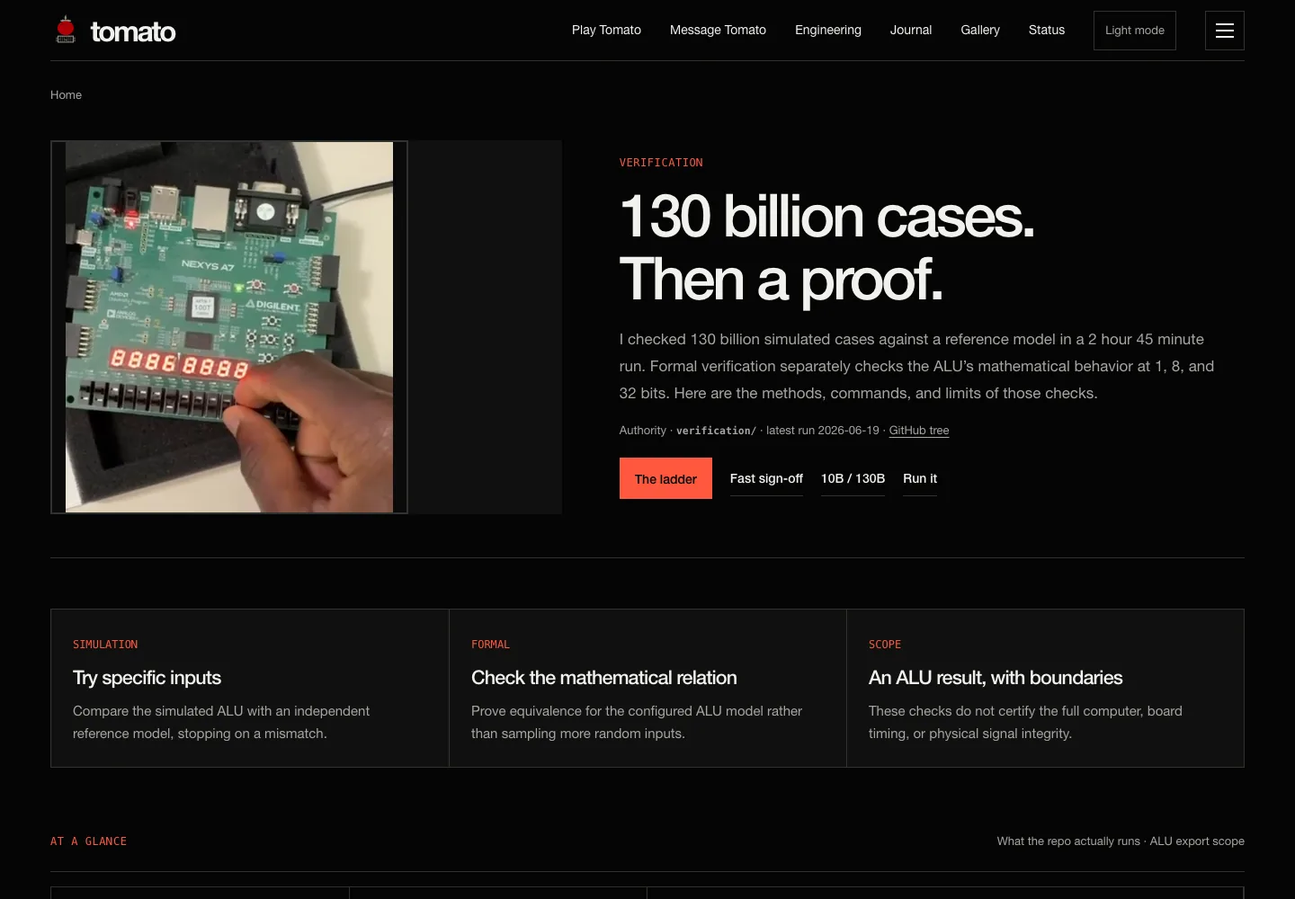
web/assets/documentation/desktop/tomato-verification-desktop.webp
