tmarhguy/tomato/hardware/kicad/main/1b-alu-slice/1b-alu-slice.cir

.title KiCad schematic
Q18 __Q18
Q19 __Q19
Q20 __Q20
Q17 __Q17
Q2 __Q2
Q1 __Q1
Q40 __Q40
Q41 __Q41
Q42 __Q42
Q39 __Q39
Q60 __Q60
Q61 __Q61
Q62 __Q62
Q59 __Q59
Q2 __Q2
Q1 __Q1
Q65 __Q65
Q66 __Q66
Q68 __Q68
Q67 __Q67
Q70 __Q70
Q69 __Q69
Q72 __Q72
Q71 __Q71
Q165 __Q165
Q157 __Q157
Q11 __Q11
Q12 __Q12
Q123 __Q123
Q115 __Q115
Q3 __Q3
Q2 __Q2
Q6 __Q6
Q515 __Q515
Q4 __Q4
Q5 __Q5
Q3 __Q3
Q2 __Q2
Q6 __Q6
Q515 __Q515
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
.end
