tmarhguy/tomato/hardware/kicad/main/8b-alu-slice/8b-alu-slice.cir

.title KiCad schematic
U7 __U7
C9 VCC GND C
C13 GND VCC 100n
U11 __U11
C10 GND VCC 100n
U8 __U8
C8 VCC GND C
U6 __U6
C6 GND VCC 100n
U10 __U10
U9 __U9
C7 GND VCC 100n
C15 GND VCC 100n
U13 __U13
C16 GND VCC 100n
U14 __U14
TP9 __TP9
TP1 __TP1
C5 VCC GND 100n
C2 VCC GND 100n
TP4 __TP4
TP2 __TP2
TP3 __TP3
U1 __U1
C1 VCC GND 100n
U4 __U4
C4 VCC GND 100n
U2 __U2
U5 __U5
U3 __U3
R3 Net-_U3-P2_ VCC 1000
C3 VCC GND 100n
R1 Net-_U3-G2_ VCC 1000
R2 Net-_U3-G3_ VCC 1000
R4 Net-_U3-P3_ VCC 1000
TP6 __TP6
TP5 __TP5
TP8 __TP8
J1 __J1
J2 __J2
TP7 __TP7
C11 GND VCC 100n
U12 __U12
R20 ALU_OUT_1_ Net-_D16-A_ 2200
R19 ALU_OUT_0_ Net-_D15-A_ 2200
D15 GND Net-_D15-A_ LED
D16 GND Net-_D16-A_ LED
R18 VOUT Net-_D14-A_ 2200
R17 N Net-_D13-A_ 2200
D14 GND Net-_D14-A_ LED
D13 GND Net-_D13-A_ LED
C12 VCC GND 100n
C14 GND VCC 100n
R22 ALU_OUT_3_ Net-_D18-A_ 2200
D17 GND Net-_D17-A_ LED
D18 GND Net-_D18-A_ LED
R21 ALU_OUT_2_ Net-_D17-A_ 2200
D19 GND Net-_D19-A_ LED
R25 ALU_OUT_6_ Net-_D21-A_ 2200
R24 ALU_OUT_5_ Net-_D20-A_ 2200
R26 ALU_OUT_7_ Net-_D22-A_ 2200
TP12 __TP12
TP13 __TP13
TP11 __TP11
TP10 __TP10
D20 GND Net-_D20-A_ LED
D22 GND Net-_D22-A_ LED
D21 GND Net-_D21-A_ LED
TP17 __TP17
TP15 __TP15
TP14 __TP14
TP16 __TP16
R23 ALU_OUT_4_ Net-_D19-A_ 2200
D4 GND Net-_D4-A_ LED
D2 GND Net-_D2-A_ LED
D3 GND Net-_D3-A_ LED
R8 /bsel1 Net-_D4-A_ 2200
R9 /func0 Net-_D5-A_ 2200
R10 /func1 Net-_D6-A_ 2200
D6 GND Net-_D6-A_ LED
D5 GND Net-_D5-A_ LED
R7 /bsel0 Net-_D3-A_ 2200
D1 GND Net-_D1-A_ LED
R5 /asel0 Net-_D1-A_ 2200
R6 /asel1 Net-_D2-A_ 2200
D11 GND Net-_D11-A_ LED
D12 GND Net-_D12-A_ LED
R15 ZOUT Net-_D11-A_ 2200
D10 GND Net-_D10-A_ LED
R14 NZ Net-_D10-A_ 2200
R16 COUT Net-_D12-A_ 2200
D9 GND Net-_D9-A_ LED
R13 /func4 Net-_D9-A_ 2200
D7 GND Net-_D7-A_ LED
R11 /func2 Net-_D7-A_ 2200
R12 /func3 Net-_D8-A_ 2200
D8 GND Net-_D8-A_ LED
Q34 __Q34
Q31 __Q31
Q32 __Q32
Q33 __Q33
Q199 __Q199
Q198 __Q198
Q202 __Q202
Q197 __Q197
Q200 __Q200
Q201 __Q201
Q211 __Q211
Q208 __Q208
Q214 __Q214
Q207 __Q207
Q212 __Q212
Q213 __Q213
Q225 __Q225
Q224 __Q224
Q228 __Q228
Q221 __Q221
Q226 __Q226
Q227 __Q227
Q231 __Q231
Q230 __Q230
Q234 __Q234
Q229 __Q229
Q232 __Q232
Q233 __Q233
Q237 __Q237
Q238 __Q238
Q235 __Q235
Q236 __Q236
Q239 __Q239
Q240 __Q240
Q241 __Q241
Q242 __Q242
Q36 __Q36
Q35 __Q35
Q40 __Q40
Q37 __Q37
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
.end
