tmarhguy/tomato/hardware/kicad/boards/07_alu/07_alu.kicad_pcb

## KiCad design hardware/kicad/boards/07_alu/07_alu.kicad_pcb (continued)

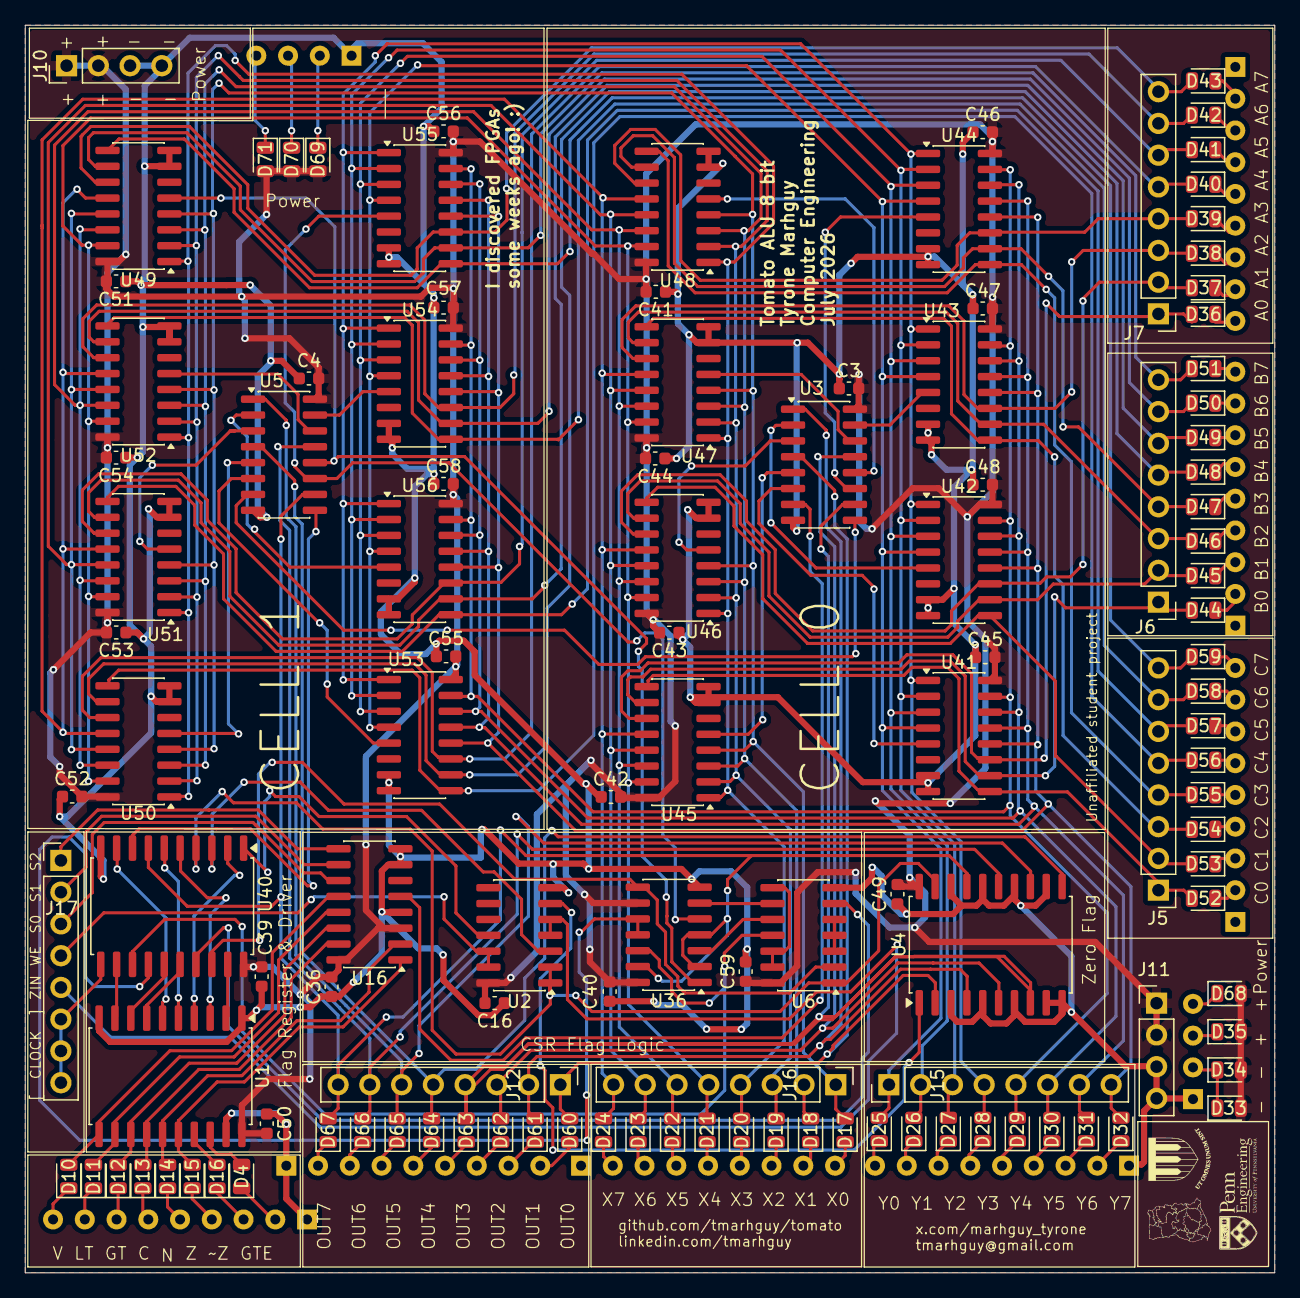
[picture p161: board 07_alu.kicad_pcb from above]

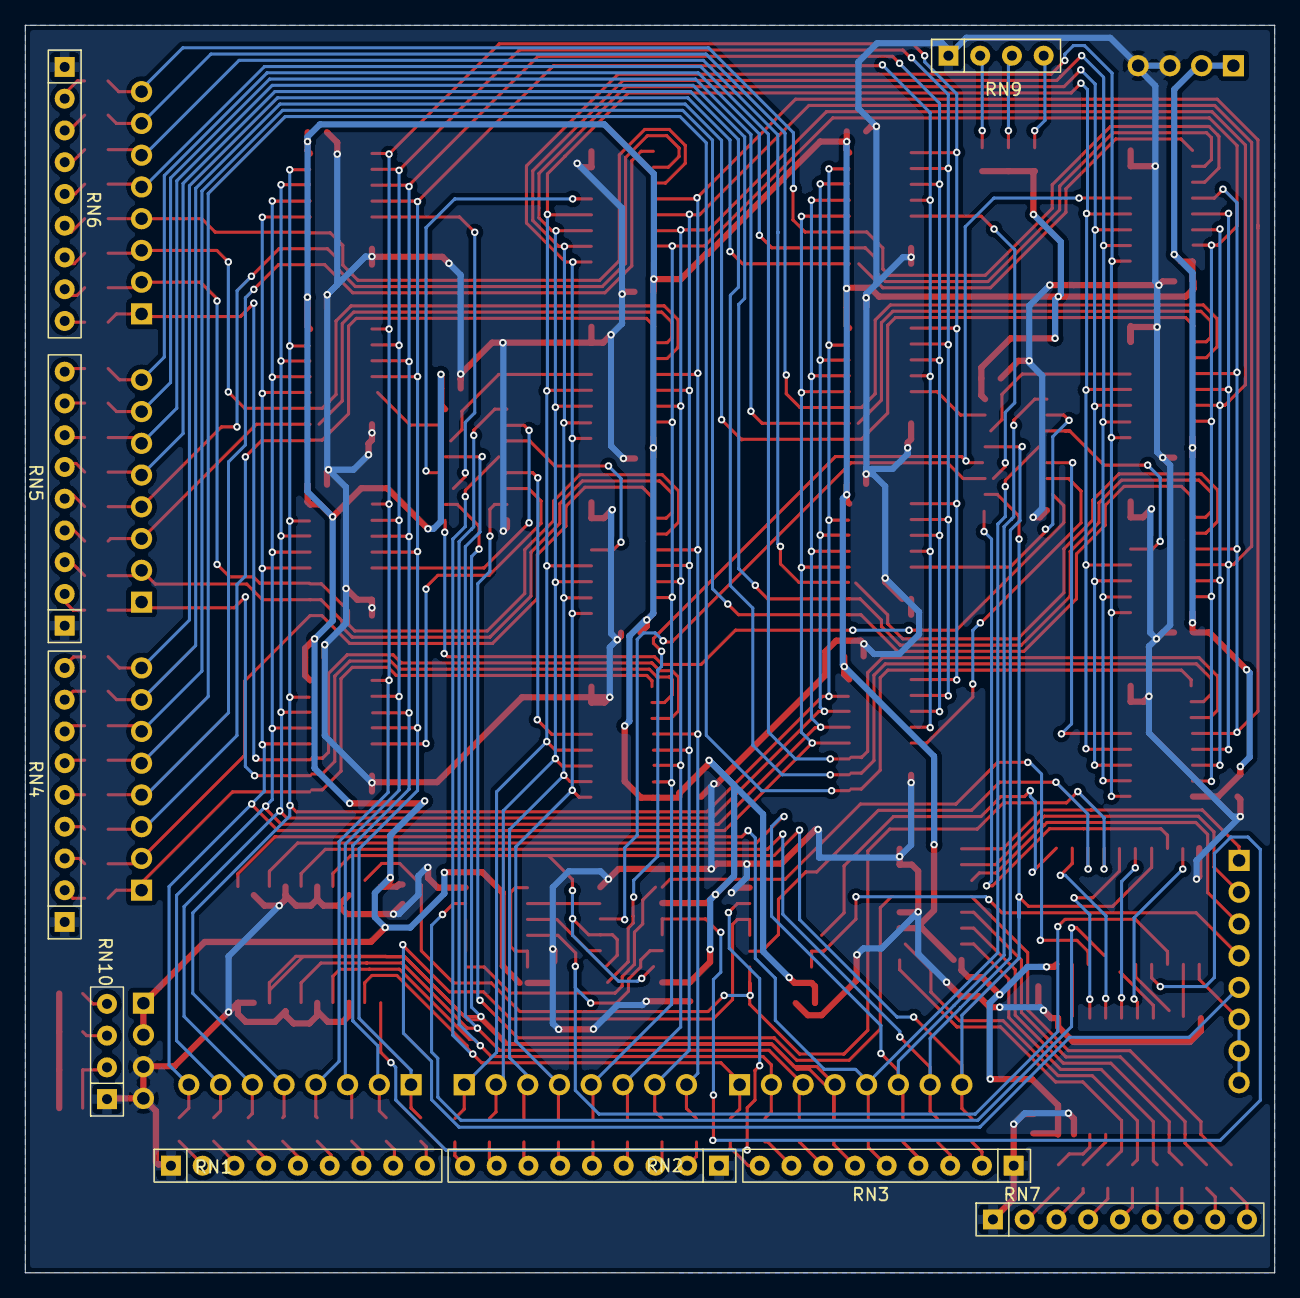
[picture p162: board 07_alu.kicad_pcb from below]

Board: 2 copper layers, 100.0 x 99.8 mm, 134 parts (9 on the bottom side), 165 nets.

Other parts of the board:
Ref**: Val**; ghana_map
Ref**#2: Val**; upenn_eng_logo
Ref**#3: Val**; achimota_logo
