tmarhguy/tomato/hardware/kicad/main/1b-alu-slice/1b-alu-slice.kicad_pcb

## KiCad design hardware/kicad/main/1b-alu-slice/1b-alu-slice.kicad_pcb (2026-06-05)

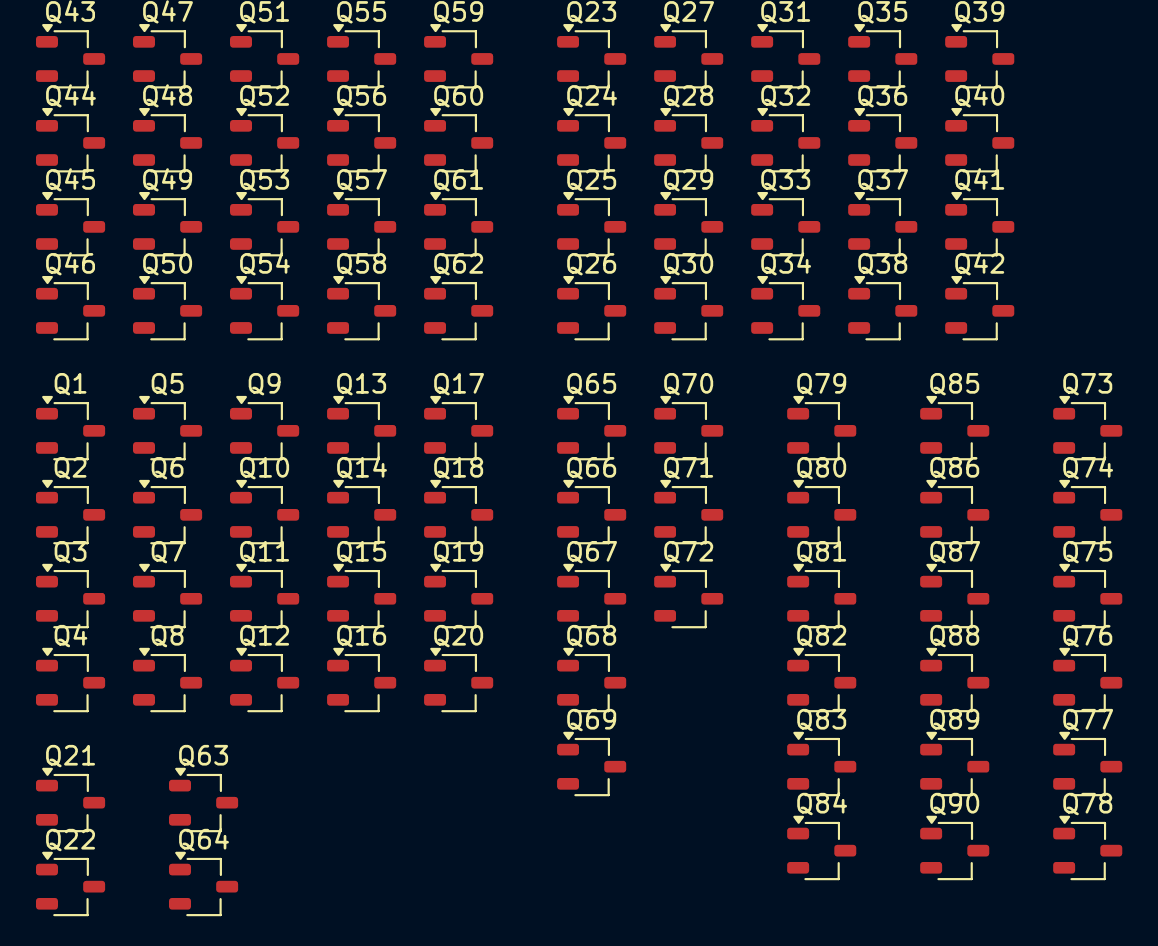
[picture p164: board 1b-alu-slice.kicad_pcb from above]

Board: 2 copper layers, 90 parts (0 on the bottom side), 49 nets, no tracks yet.

Parts:
Q1, Q3, Q6, Q8, Q10, Q12, Q14, Q16, Q17, Q19, Q21, Q23, Q25, Q28, Q30, Q32, Q34, Q36, Q38, Q39, Q41, Q43, Q45, Q48, Q50, Q52, Q54, Q56, Q58, Q59, Q61, Q63, Q65, Q67, Q71, Q73, Q74, Q79, Q80, Q86, Q87, Q89: Q_PMOS; TSOT-23
Q2, Q4, Q5, Q7, Q9, Q11, Q13, Q15, Q18, Q20, Q22, Q24, Q26, Q27, Q29, Q31, Q33, Q35, Q37, Q40, Q42, Q44, Q46, Q47, Q49, Q51, Q53, Q55, Q57, Q60, Q62, Q64, Q66, Q68, Q69, Q70, Q72, Q75, Q76, Q81, Q82, Q85, Q88, Q90: Q_NMOS; TSOT-23
Q77, Q83: PMOS; TSOT-23
Q78, Q84: NMOS; TSOT-23

Connections:
/A: Q5.3 (S), Q6.3 (S), Q21.2 (G), Q22.2 (G)
/A_SEL[0]: Q1.2 (G), Q2.2 (G), Q14.2 (G), Q15.2 (G)
/A_SEL[1]: Q3.2 (G), Q4.2 (G), Q6.2 (G), Q7.2 (G), Q10.2 (G), Q11.2 (G)
/B: Q47.3 (S), Q48.3 (S), Q63.2 (G), Q64.2 (G)
/B_SEL[0]: Q43.2 (G), Q44.2 (G), Q56.2 (G), Q57.2 (G)
/B_SEL[1]: Q45.2 (G), Q46.2 (G), Q48.2 (G), Q49.2 (G), Q52.2 (G), Q53.2 (G)
/CIN: Q67.2 (G), Q68.2 (G), Q70.1 (D), Q73.2 (G), Q76.2 (G)
/COUT: Q89.1 (D), Q90.1 (D)
/FUNC[0]: Q27.3 (S), Q28.3 (S)
/FUNC[1]: Q29.3 (S), Q30.3 (S)
/FUNC[2]: Q31.3 (S), Q32.3 (S)
/FUNC[3]: Q33.3 (S), Q34.3 (S)
/LOGIC_OUT: Q41.1 (D), Q42.1 (D), Q65.2 (G), Q66.2 (G), Q70.2 (G), Q74.2 (G), Q75.2 (G)
/S: Q71.1 (D), Q72.1 (D)
/and1/Y: Q77.1 (D), Q78.1 (D), Q85.2 (G), Q86.2 (G)
/and2/A: Q25.2 (G), Q26.2 (G), Q28.2 (G), Q29.2 (G), Q32.2 (G), Q33.2 (G), Q61.1 (D), Q62.1 (D), Q79.2 (G), Q82.2 (G)
/and2/B: Q19.1 (D), Q20.1 (D), Q23.2 (G), Q24.2 (G), Q36.2 (G), Q37.2 (G), Q80.2 (G), Q81.2 (G)
/and2/Y: Q83.1 (D), Q84.1 (D), Q87.2 (G), Q88.2 (G)
/inv1/Y: Q7.3 (S), Q8.3 (S), Q21.1 (D), Q22.1 (D)
/inv2/Y: Q49.3 (S), Q50.3 (S), Q63.1 (D), Q64.1 (D)
GND: Q2.3 (S), Q4.3 (S), Q11.3 (S), Q12.3 (S), Q18.3 (S), Q20.3 (S), Q22.3 (S), Q24.3 (S), Q26.3 (S), Q40.3 (S), Q42.3 (S), Q44.3 (S), Q46.3 (S), Q53.3 (S), Q54.3 (S), Q60.3 (S), Q62.3 (S), Q64.3 (S), Q66.3 (S), Q68.3 (S), Q72.3 (S), Q76.3 (S), Q78.3 (S), Q82.3 (S), Q84.3 (S), Q85.3 (S), Q88.3 (S), Q90.3 (S)
unnamed: Q1.1 (D), Q2.1 (D), Q13.2 (G), Q16.2 (G)
unnamed: Q9.1 (D), Q10.1 (D), Q11.1 (D), Q12.1 (D), Q15.3 (S), Q16.3 (S)
unnamed: Q3.1 (D), Q4.1 (D), Q5.2 (G), Q8.2 (G), Q9.2 (G), Q12.2 (G)
unnamed: Q13.1 (D), Q14.1 (D), Q15.1 (D), Q16.1 (D), Q17.2 (G), Q18.2 (G)
unnamed: Q5.1 (D), Q6.1 (D), Q7.1 (D), Q8.1 (D), Q13.3 (S), Q14.3 (S)
unnamed: Q17.1 (D), Q18.1 (D), Q19.2 (G), Q20.2 (G)
unnamed: Q23.1 (D), Q24.1 (D), Q35.2 (G), Q38.2 (G)
unnamed: Q25.1 (D), Q26.1 (D), Q27.2 (G), Q30.2 (G), Q31.2 (G), Q34.2 (G)
unnamed: Q27.1 (D), Q28.1 (D), Q29.1 (D), Q30.1 (D), Q35.3 (S), Q36.3 (S)
unnamed: Q31.1 (D), Q32.1 (D), Q33.1 (D), Q34.1 (D), Q37.3 (S), Q38.3 (S)
unnamed: Q35.1 (D), Q36.1 (D), Q37.1 (D), Q38.1 (D), Q39.2 (G), Q40.2 (G)
unnamed: Q39.1 (D), Q40.1 (D), Q41.2 (G), Q42.2 (G)
unnamed: Q43.1 (D), Q44.1 (D), Q55.2 (G), Q58.2 (G)
unnamed: Q45.1 (D), Q46.1 (D), Q47.2 (G), Q50.2 (G), Q51.2 (G), Q54.2 (G)
unnamed: Q47.1 (D), Q48.1 (D), Q49.1 (D), Q50.1 (D), Q55.3 (S), Q56.3 (S)
unnamed: Q51.1 (D), Q52.1 (D), Q53.1 (D), Q54.1 (D), Q57.3 (S), Q58.3 (S)
unnamed: Q55.1 (D), Q56.1 (D), Q57.1 (D), Q58.1 (D), Q59.2 (G), Q60.2 (G)
unnamed: Q59.1 (D), Q60.1 (D), Q61.2 (G), Q62.2 (G)
unnamed: Q65.1 (D), Q66.1 (D), Q69.2 (G)
unnamed: Q67.1 (D), Q68.1 (D), Q69.3 (S)
unnamed: Q69.1 (D), Q70.3 (S), Q71.2 (G), Q72.2 (G)
unnamed: Q73.1 (D), Q74.1 (D), Q75.1 (D), Q77.2 (G), Q78.2 (G)
unnamed: Q75.3 (S), Q76.1 (D)
unnamed: Q79.1 (D), Q80.1 (D), Q81.1 (D), Q83.2 (G), Q84.2 (G)
unnamed: Q81.3 (S), Q82.1 (D)
unnamed: Q85.1 (D), Q87.1 (D), Q88.1 (D), Q89.2 (G), Q90.2 (G)
unnamed: Q86.1 (D), Q87.3 (S)
VCC: Q1.3 (S), Q3.3 (S), Q9.3 (S), Q10.3 (S), Q17.3 (S), Q19.3 (S), Q21.3 (S), Q23.3 (S), Q25.3 (S), Q39.3 (S), Q41.3 (S), Q43.3 (S), Q45.3 (S), Q51.3 (S), Q52.3 (S), Q59.3 (S), Q61.3 (S), Q63.3 (S), Q65.3 (S), Q67.3 (S), Q71.3 (S), Q73.3 (S), Q74.3 (S), Q77.3 (S), Q79.3 (S), Q80.3 (S), Q83.3 (S), Q86.3 (S), Q89.3 (S)
