tmarhguy/tomato/hardware/kicad/modules/gates/and/gate_and_3in.kicad_sch

## KiCad design hardware/kicad/modules/gates/and/gate_and_3in.kicad_sch (2026-06-05)

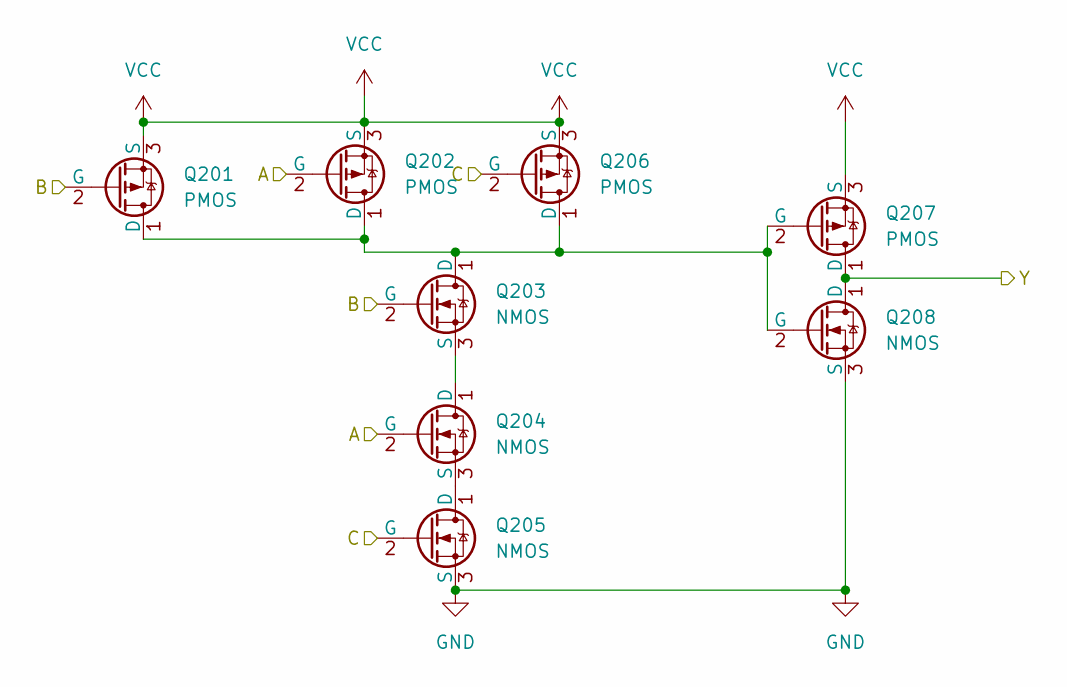
[picture p165: schematic gate_and_3in.kicad_sch]

Parts:
Q201, Q202, Q206, Q207: PMOS; TSOT-23
Q203, Q204, Q205, Q208: NMOS; TSOT-23

Connections:
A: Q202.2 (G), Q204.2 (G)
B: Q201.2 (G), Q203.2 (G)
C: Q205.2 (G), Q206.2 (G)
GND: Q205.3 (S), Q208.3 (S)
unnamed: Q201.1 (D), Q202.1 (D), Q203.1 (D), Q206.1 (D), Q207.2 (G), Q208.2 (G)
unnamed: Q203.3 (S), Q204.1 (D)
unnamed: Q204.3 (S), Q205.1 (D)
VCC: Q201.3 (S), Q202.3 (S), Q206.3 (S), Q207.3 (S)
Y: Q207.1 (D), Q208.1 (D)
