tmarhguy/tomato/hardware/kicad/modules/gates/and/gate_and_4in.kicad_sch

## KiCad design hardware/kicad/modules/gates/and/gate_and_4in.kicad_sch (2026-06-05)

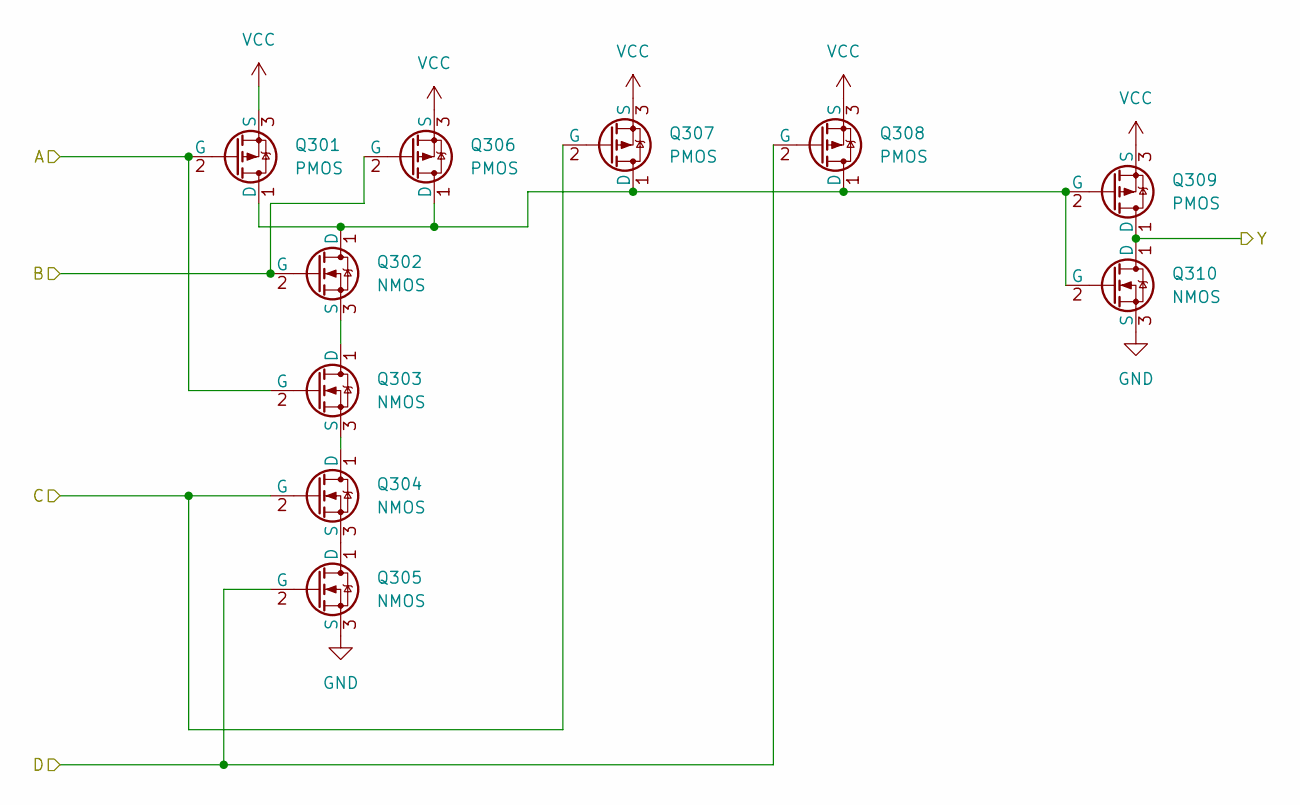
[picture p166: schematic gate_and_4in.kicad_sch]

Parts:
Q301, Q306, Q307, Q308, Q309: PMOS; TSOT-23
Q302, Q303, Q304, Q305, Q310: NMOS; TSOT-23

Connections:
A: Q301.2 (G), Q303.2 (G)
B: Q302.2 (G), Q306.2 (G)
C: Q304.2 (G), Q307.2 (G)
D: Q305.2 (G), Q308.2 (G)
GND: Q305.3 (S), Q310.3 (S)
unnamed: Q301.1 (D), Q302.1 (D), Q306.1 (D), Q307.1 (D), Q308.1 (D), Q309.2 (G), Q310.2 (G)
unnamed: Q302.3 (S), Q303.1 (D)
unnamed: Q303.3 (S), Q304.1 (D)
unnamed: Q304.3 (S), Q305.1 (D)
VCC: Q301.3 (S), Q306.3 (S), Q307.3 (S), Q308.3 (S), Q309.3 (S)
Y: Q309.1 (D), Q310.1 (D)
