tmarhguy/tomato/hardware/kicad/modules/gates/aoi22/gate_aoi22.kicad_sch

## KiCad design hardware/kicad/modules/gates/aoi22/gate_aoi22.kicad_sch (2026-06-08)

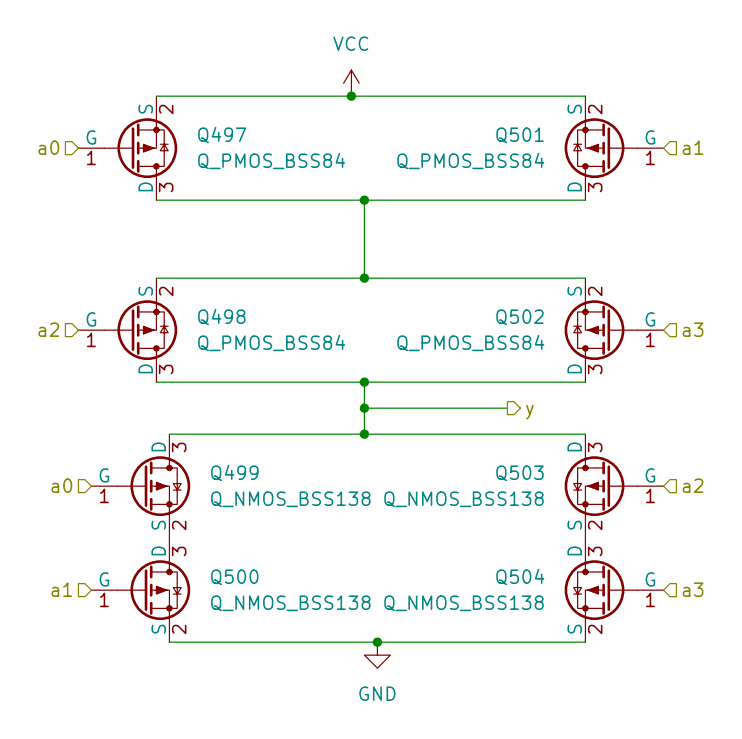
[picture p167: schematic gate_aoi22.kicad_sch]

Parts:
Q497, Q498, Q501, Q502: Q_PMOS_BSS84; SOT-23
Q499, Q500, Q503, Q504: Q_NMOS_BSS138; SOT-23

Connections:
GND: Q500.2 (S), Q504.2 (S)
unnamed: Q497.3 (D), Q498.2 (S), Q501.3 (D), Q502.2 (S)
unnamed: Q499.2 (S), Q500.3 (D)
unnamed: Q503.2 (S), Q504.3 (D)
VCC: Q497.2 (S), Q501.2 (S)
a0: Q497.1 (G), Q499.1 (G)
a1: Q500.1 (G), Q501.1 (G)
a2: Q498.1 (G), Q503.1 (G)
a3: Q502.1 (G), Q504.1 (G)
y: Q498.3 (D), Q499.3 (D), Q502.3 (D), Q503.3 (D)
