tmarhguy/tomato/hardware/kicad/modules/gates/buff/gate_buff.kicad_sch

## KiCad design hardware/kicad/modules/gates/buff/gate_buff.kicad_sch (2026-06-05)

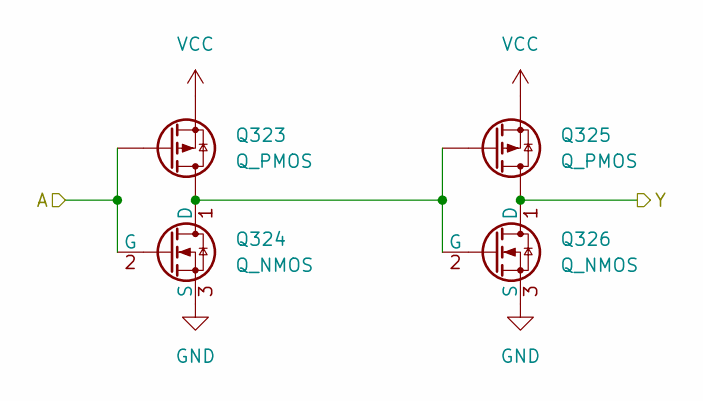
[picture p168: schematic gate_buff.kicad_sch]

Parts:
Q323, Q325: Q_PMOS; TSOT-23
Q324, Q326: Q_NMOS; TSOT-23

Connections:
A: Q323.G, Q324.2 (G)
GND: Q324.3 (S), Q326.3 (S)
unnamed: Q323.D, Q324.1 (D), Q325.G, Q326.2 (G)
VCC: Q323.S, Q325.S
Y: Q325.D, Q326.1 (D)
