tmarhguy/tomato/hardware/kicad/modules/gates/inv/gate_inv.kicad_sch

## KiCad design hardware/kicad/modules/gates/inv/gate_inv.kicad_sch (2026-06-23)

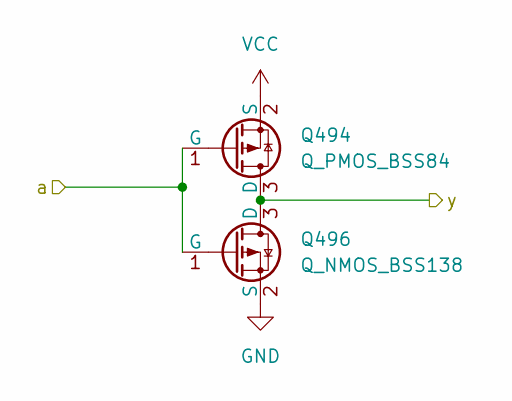
[picture p169: schematic gate_inv.kicad_sch]

Parts:
Q494: Q_PMOS_BSS84; SOT-23
Q496: Q_NMOS_BSS138; SOT-23

Connections:
GND: Q496.2 (S)
VCC: Q494.2 (S)
a: Q494.1 (G), Q496.1 (G)
y: Q494.3 (D), Q496.3 (D)
