tmarhguy/tomato/hardware/kicad/modules/gates/nand/gate_nand.kicad_sch

## KiCad design hardware/kicad/modules/gates/nand/gate_nand.kicad_sch (2026-06-05)

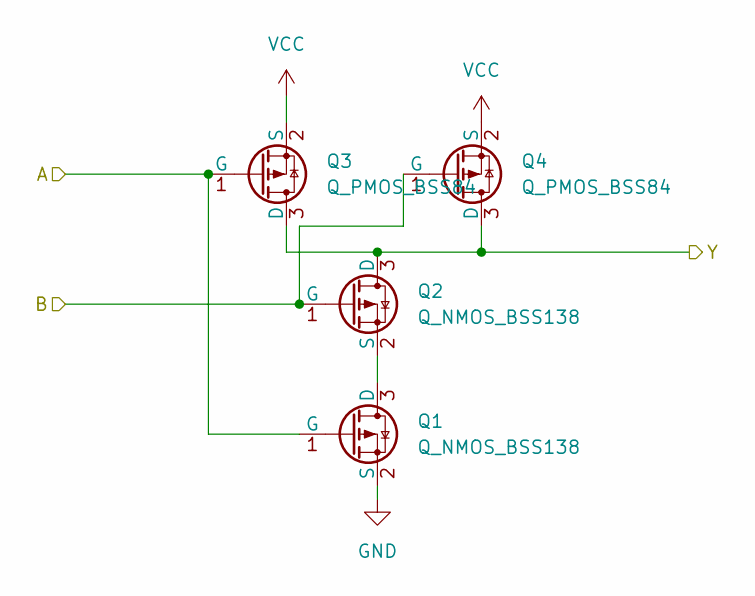
[picture p170: schematic gate_nand.kicad_sch]

Parts:
Q1, Q2: Q_NMOS_BSS138; SOT-23
Q3, Q4: Q_PMOS_BSS84; SOT-23

Connections:
A: Q1.1 (G), Q3.1 (G)
B: Q2.1 (G), Q4.1 (G)
GND: Q1.2 (S)
unnamed: Q1.3 (D), Q2.2 (S)
VCC: Q3.2 (S), Q4.2 (S)
Y: Q2.3 (D), Q3.3 (D), Q4.3 (D)
