tmarhguy/tomato/hardware/kicad/modules/gates/nand/gate_nand_3in.kicad_sch

## KiCad design hardware/kicad/modules/gates/nand/gate_nand_3in.kicad_sch (2026-06-05)

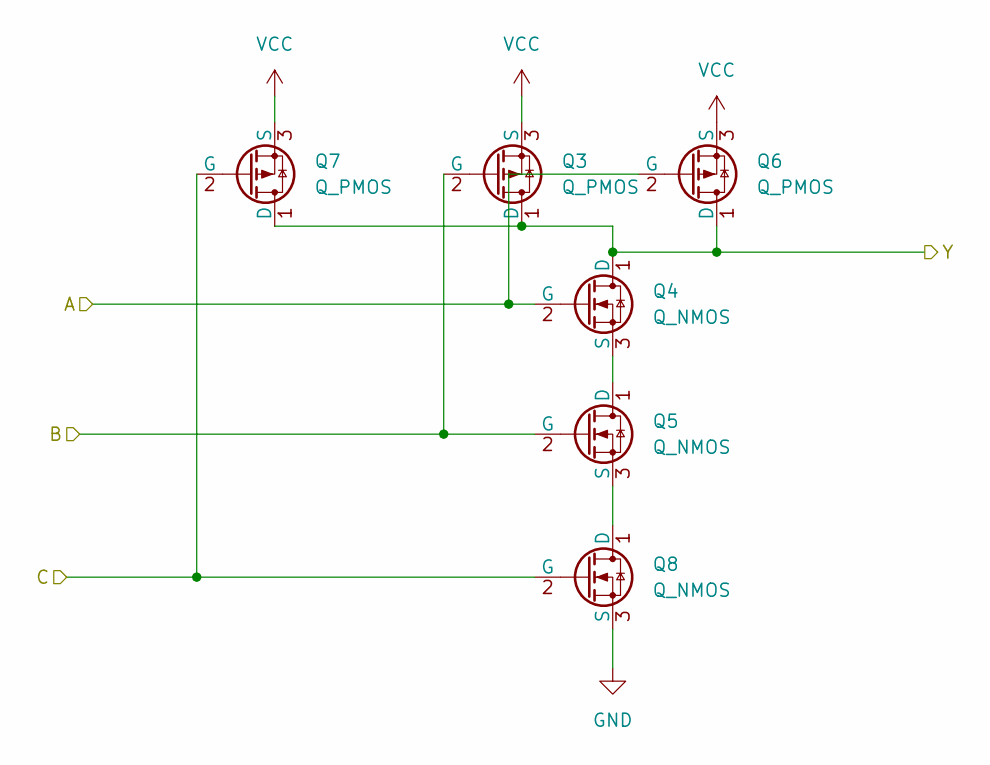
[picture p171: schematic gate_nand_3in.kicad_sch]

Parts:
Q3, Q6, Q7: Q_PMOS; TSOT-23
Q4, Q5, Q8: Q_NMOS; TSOT-23

Connections:
A: Q4.2 (G), Q6.2 (G)
B: Q3.2 (G), Q5.2 (G)
C: Q7.2 (G), Q8.2 (G)
GND: Q8.3 (S)
unnamed: Q4.3 (S), Q5.1 (D)
unnamed: Q5.3 (S), Q8.1 (D)
VCC: Q3.3 (S), Q6.3 (S), Q7.3 (S)
Y: Q3.1 (D), Q4.1 (D), Q6.1 (D), Q7.1 (D)
