tmarhguy/tomato/hardware/kicad/modules/gates/nand/gate_nand_4in.kicad_sch

## KiCad design hardware/kicad/modules/gates/nand/gate_nand_4in.kicad_sch (2026-06-05)

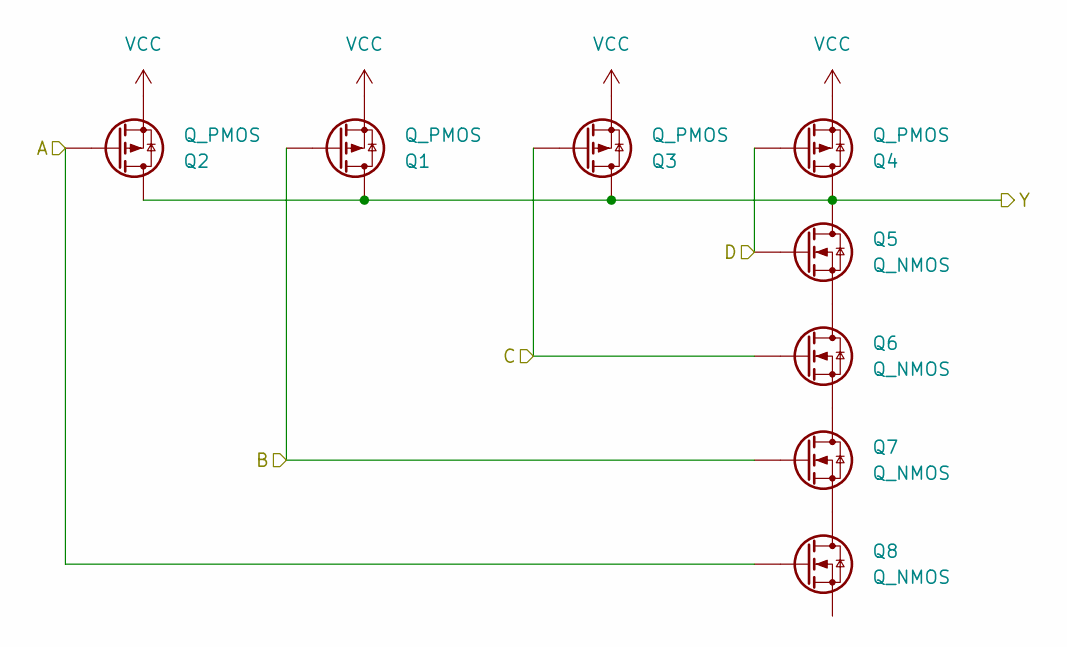
[picture p172: schematic gate_nand_4in.kicad_sch]

Parts:
Q1, Q2, Q3, Q4: Q_PMOS
Q5, Q6, Q7, Q8: Q_NMOS

Connections:
A: Q2.G, Q8.G
B: Q1.G, Q7.G
C: Q3.G, Q6.G
D: Q4.G, Q5.G
unnamed: Q5.S, Q6.D
unnamed: Q6.S, Q7.D
unnamed: Q7.S, Q8.D
VCC: Q1.S, Q2.S, Q3.S, Q4.S
Y: Q1.D, Q2.D, Q3.D, Q4.D, Q5.D
