tmarhguy/tomato/hardware/kicad/modules/gates/nor/gate_nor_2in.kicad_sch

## KiCad design hardware/kicad/modules/gates/nor/gate_nor_2in.kicad_sch (2026-06-05)

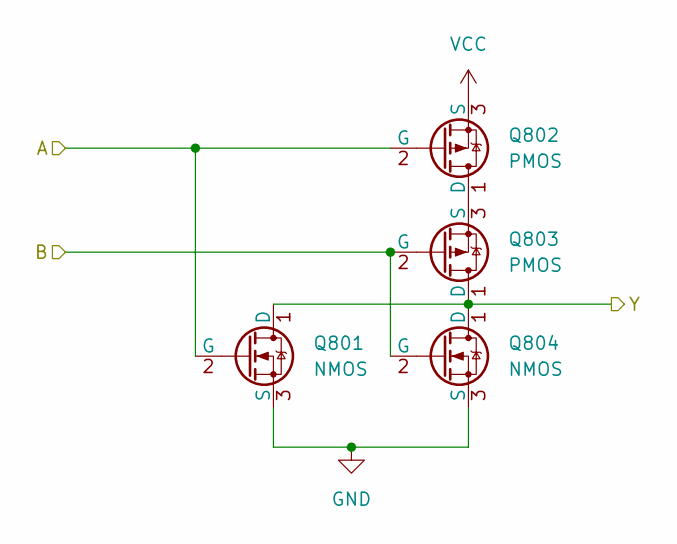
[picture p173: schematic gate_nor_2in.kicad_sch]

Parts:
Q801, Q804: NMOS; TSOT-23
Q802, Q803: PMOS; TSOT-23

Connections:
A: Q801.2 (G), Q802.2 (G)
B: Q803.2 (G), Q804.2 (G)
GND: Q801.3 (S), Q804.3 (S)
unnamed: Q802.1 (D), Q803.3 (S)
VCC: Q802.3 (S)
Y: Q801.1 (D), Q803.1 (D), Q804.1 (D)
