tmarhguy/tomato/hardware/kicad/modules/gates/nor/gate_nor_8in_1bit.kicad_sch

## KiCad design hardware/kicad/modules/gates/nor/gate_nor_8in_1bit.kicad_sch (2026-06-05)

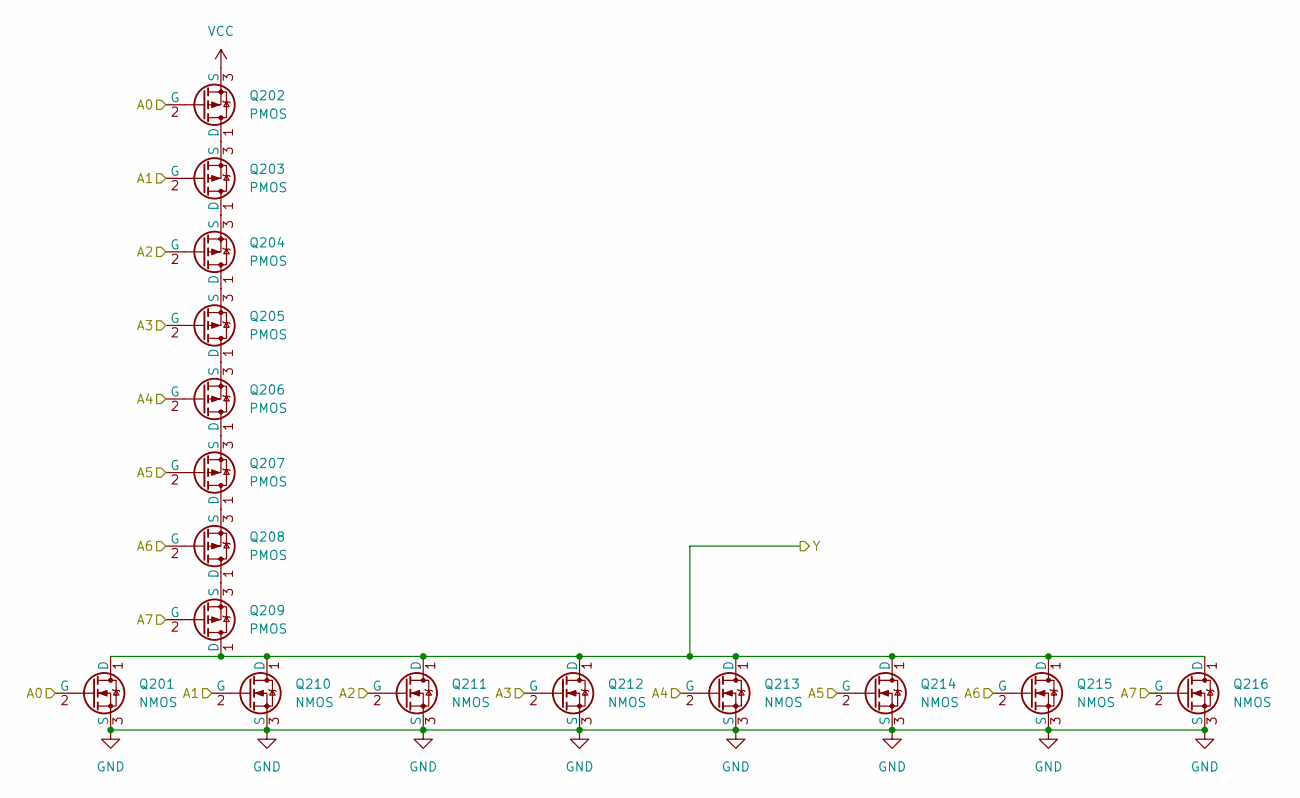
[picture p174: schematic gate_nor_8in_1bit.kicad_sch]

Parts:
Q201, Q210, Q211, Q212, Q213, Q214, Q215, Q216: NMOS; TSOT-23
Q202, Q203, Q204, Q205, Q206, Q207, Q208, Q209: PMOS; TSOT-23

Connections:
A0: Q201.2 (G), Q202.2 (G)
A1: Q203.2 (G), Q210.2 (G)
A2: Q204.2 (G), Q211.2 (G)
A3: Q205.2 (G), Q212.2 (G)
A4: Q206.2 (G), Q213.2 (G)
A5: Q207.2 (G), Q214.2 (G)
A6: Q208.2 (G), Q215.2 (G)
A7: Q209.2 (G), Q216.2 (G)
GND: Q201.3 (S), Q210.3 (S), Q211.3 (S), Q212.3 (S), Q213.3 (S), Q214.3 (S), Q215.3 (S), Q216.3 (S)
unnamed: Q202.1 (D), Q203.3 (S)
unnamed: Q203.1 (D), Q204.3 (S)
unnamed: Q204.1 (D), Q205.3 (S)
unnamed: Q205.1 (D), Q206.3 (S)
unnamed: Q206.1 (D), Q207.3 (S)
unnamed: Q207.1 (D), Q208.3 (S)
unnamed: Q208.1 (D), Q209.3 (S)
VCC: Q202.3 (S)
Y: Q201.1 (D), Q209.1 (D), Q210.1 (D), Q211.1 (D), Q212.1 (D), Q213.1 (D), Q214.1 (D), Q215.1 (D), Q216.1 (D)
