tmarhguy/tomato/hardware/kicad/modules/gates/or/gate_or.kicad_sch

## KiCad design hardware/kicad/modules/gates/or/gate_or.kicad_sch (2026-06-05)

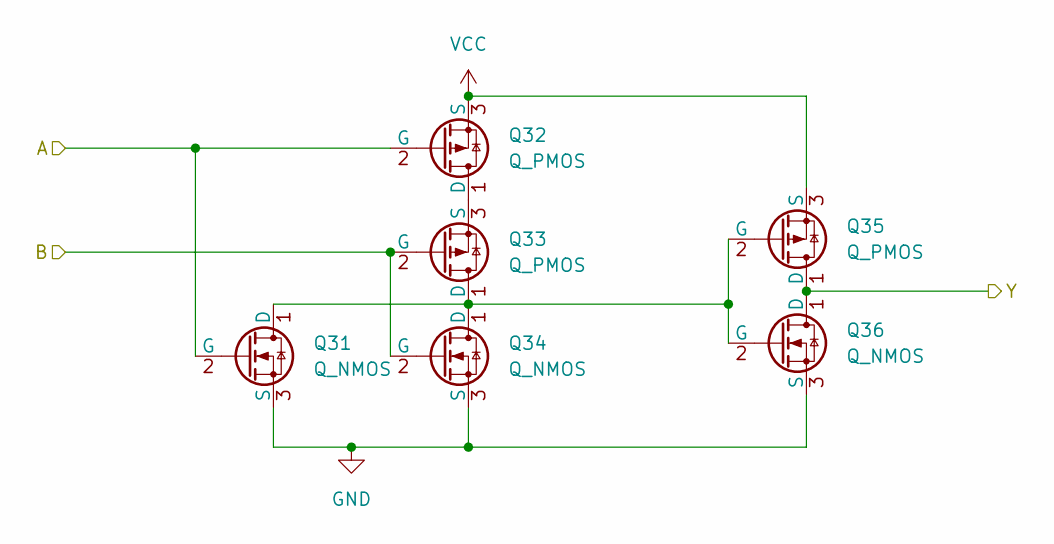
[picture p175: schematic gate_or.kicad_sch]

Parts:
Q31, Q34, Q36: Q_NMOS; TSOT-23
Q32, Q33, Q35: Q_PMOS; TSOT-23

Connections:
A: Q31.2 (G), Q32.2 (G)
B: Q33.2 (G), Q34.2 (G)
GND: Q31.3 (S), Q34.3 (S), Q36.3 (S)
unnamed: Q31.1 (D), Q33.1 (D), Q34.1 (D), Q35.2 (G), Q36.2 (G)
unnamed: Q32.1 (D), Q33.3 (S)
VCC: Q32.3 (S), Q35.3 (S)
Y: Q35.1 (D), Q36.1 (D)
