tmarhguy/tomato/hardware/kicad/modules/gates/or/gate_or_3in.kicad_sch

## KiCad design hardware/kicad/modules/gates/or/gate_or_3in.kicad_sch (2026-06-05)

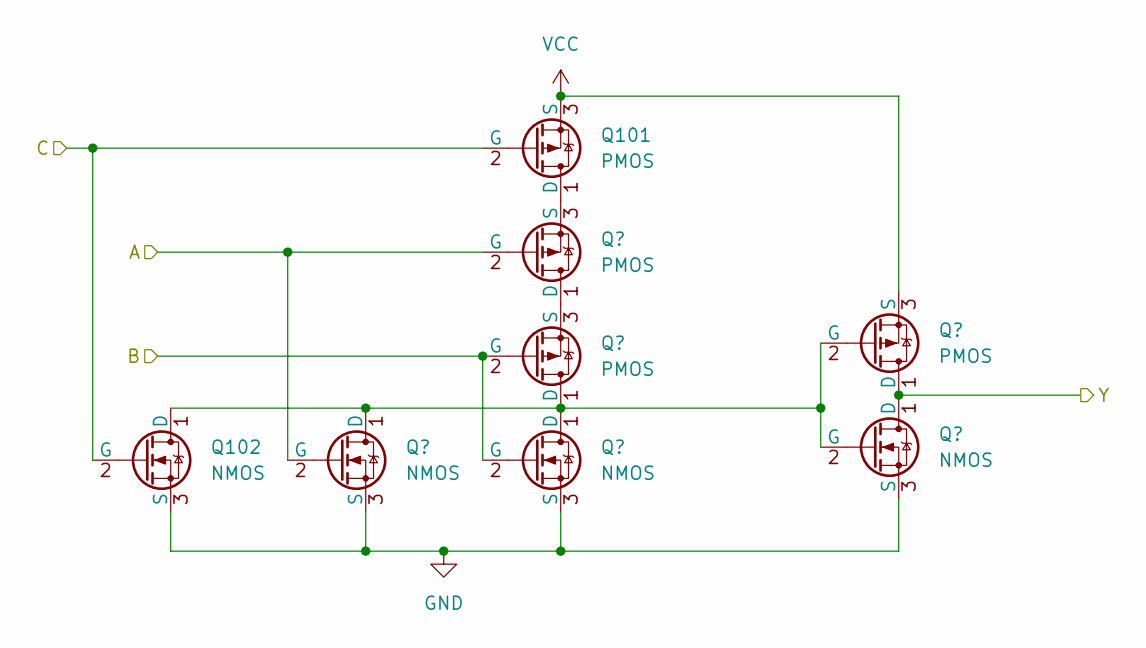
[picture p176: schematic gate_or_3in.kicad_sch]

Parts:
Q101: PMOS
Q102: NMOS; TSOT-23

Connections:
C: Q101.2 (G), Q102.2 (G)
VCC: Q101.3 (S)
