tmarhguy/tomato/hardware/kicad/modules/gates/xnor/gate_xnor_2in.kicad_sch

## KiCad design hardware/kicad/modules/gates/xnor/gate_xnor_2in.kicad_sch (2026-06-05)

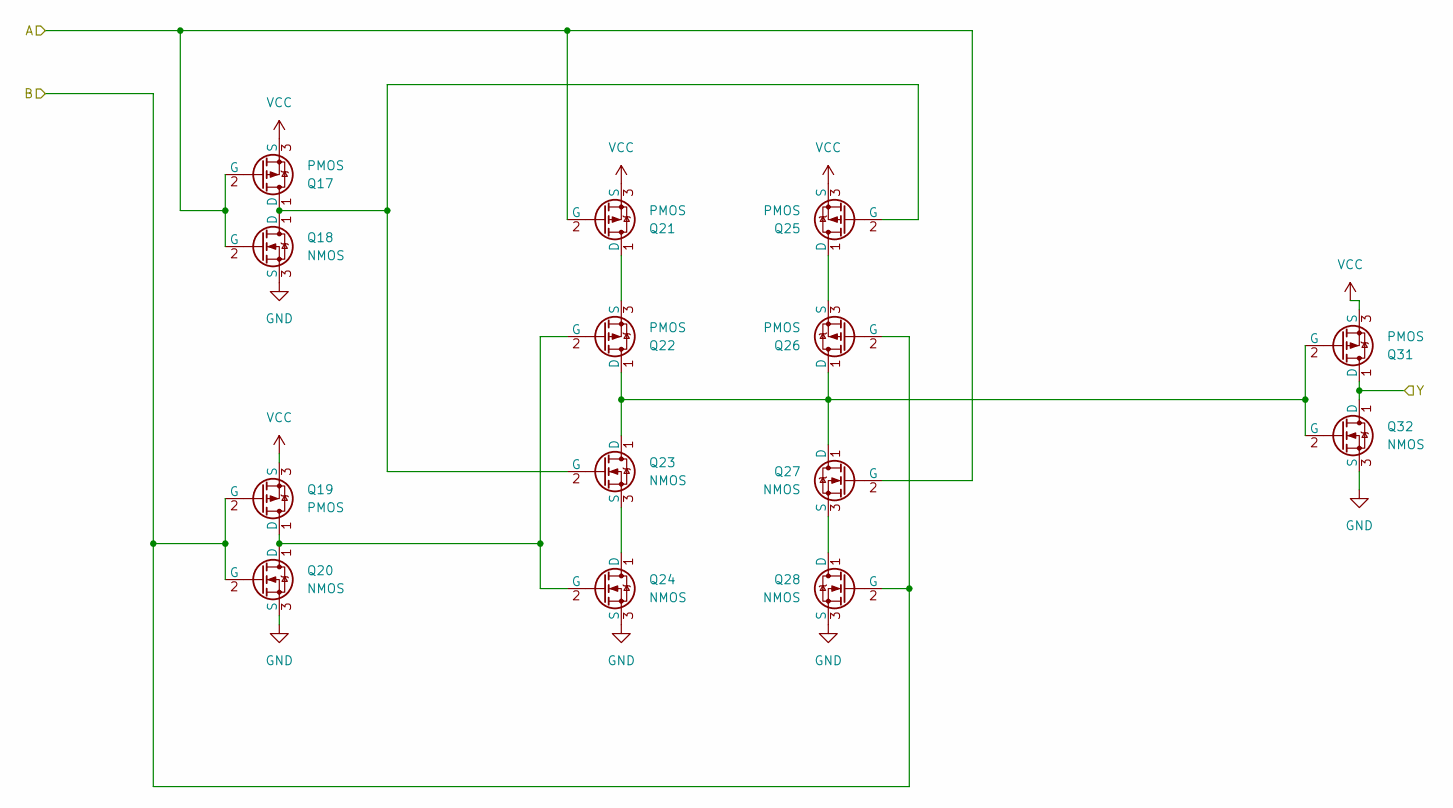
[picture p177: schematic gate_xnor_2in.kicad_sch]

Parts:
Q17, Q19, Q21, Q22, Q25, Q26, Q31: PMOS; TO-92_Inline_Wide
Q18, Q20, Q23, Q24, Q27, Q28, Q32: NMOS; TO-92_Inline_Wide

Connections:
A: Q17.2 (G), Q18.2 (G), Q21.2 (G), Q27.2 (G)
B: Q19.2 (G), Q20.2 (G), Q26.2 (G), Q28.2 (G)
GND: Q18.3 (S), Q20.3 (S), Q24.3 (S), Q28.3 (S), Q32.3 (S)
unnamed: Q17.1 (D), Q18.1 (D), Q23.2 (G), Q25.2 (G)
unnamed: Q19.1 (D), Q20.1 (D), Q22.2 (G), Q24.2 (G)
unnamed: Q21.1 (D), Q22.3 (S)
unnamed: Q22.1 (D), Q23.1 (D), Q26.1 (D), Q27.1 (D), Q31.2 (G), Q32.2 (G)
unnamed: Q23.3 (S), Q24.1 (D)
unnamed: Q25.1 (D), Q26.3 (S)
unnamed: Q27.3 (S), Q28.1 (D)
VCC: Q17.3 (S), Q19.3 (S), Q21.3 (S), Q25.3 (S), Q31.3 (S)
Y: Q31.1 (D), Q32.1 (D)
