tmarhguy/tomato/hardware/kicad/modules/gates/xor/gate_xor_2in.kicad_sch

## KiCad design hardware/kicad/modules/gates/xor/gate_xor_2in.kicad_sch (2026-06-05)

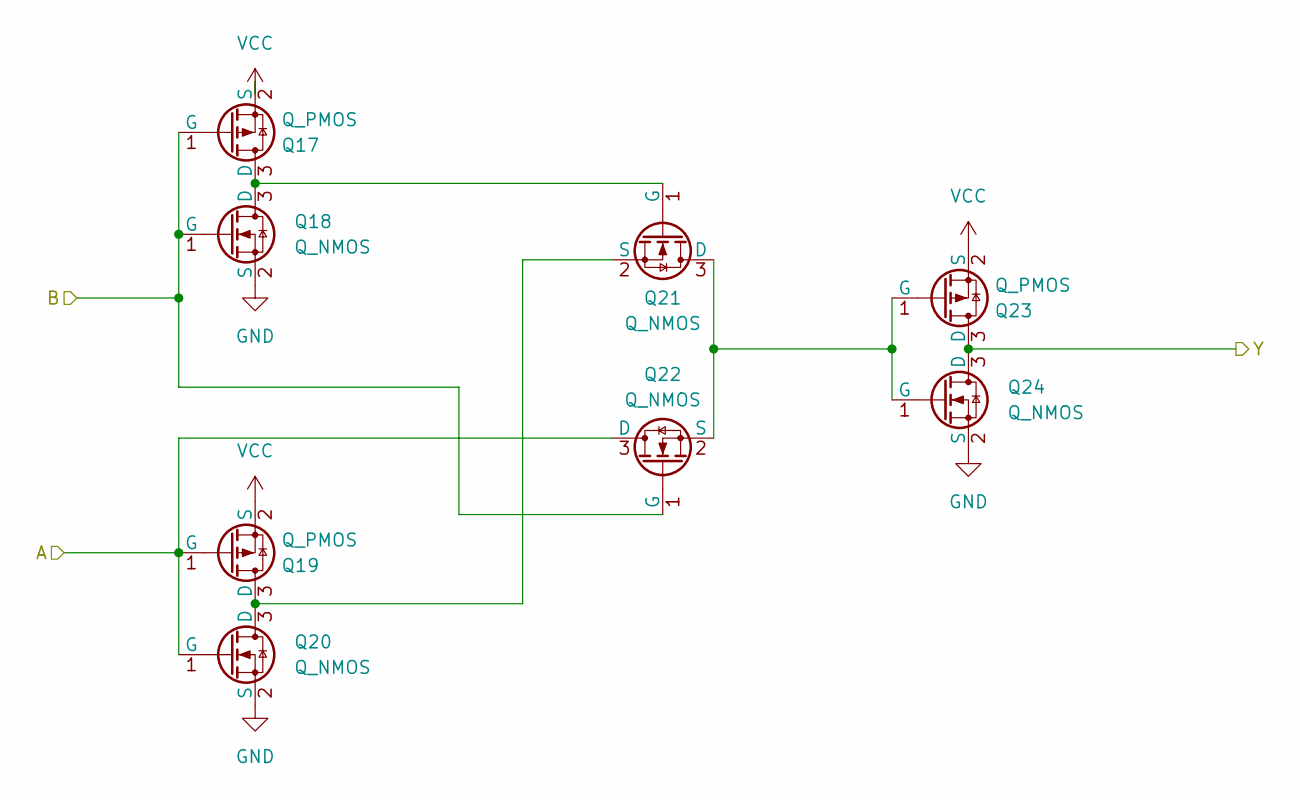
[picture p178: schematic gate_xor_2in.kicad_sch]

Parts:
Q17, Q19, Q23: Q_PMOS; SOT-23
Q18, Q20, Q21, Q22, Q24: Q_NMOS; SOT-23

Connections:
A: Q19.1 (G), Q20.1 (G), Q22.3 (D)
B: Q17.1 (G), Q18.1 (G), Q22.1 (G)
GND: Q18.2 (S), Q20.2 (S), Q24.2 (S)
unnamed: Q17.3 (D), Q18.3 (D), Q21.1 (G)
unnamed: Q19.3 (D), Q20.3 (D), Q21.2 (S)
unnamed: Q21.3 (D), Q22.2 (S), Q23.1 (G), Q24.1 (G)
VCC: Q17.2 (S), Q19.2 (S), Q23.2 (S)
Y: Q23.3 (D), Q24.3 (D)
