tmarhguy/tomato/hardware/kicad/modules/gates/xor/gate_xor_8bit.kicad_sch

## KiCad design hardware/kicad/modules/gates/xor/gate_xor_8bit.kicad_sch (2026-06-05)

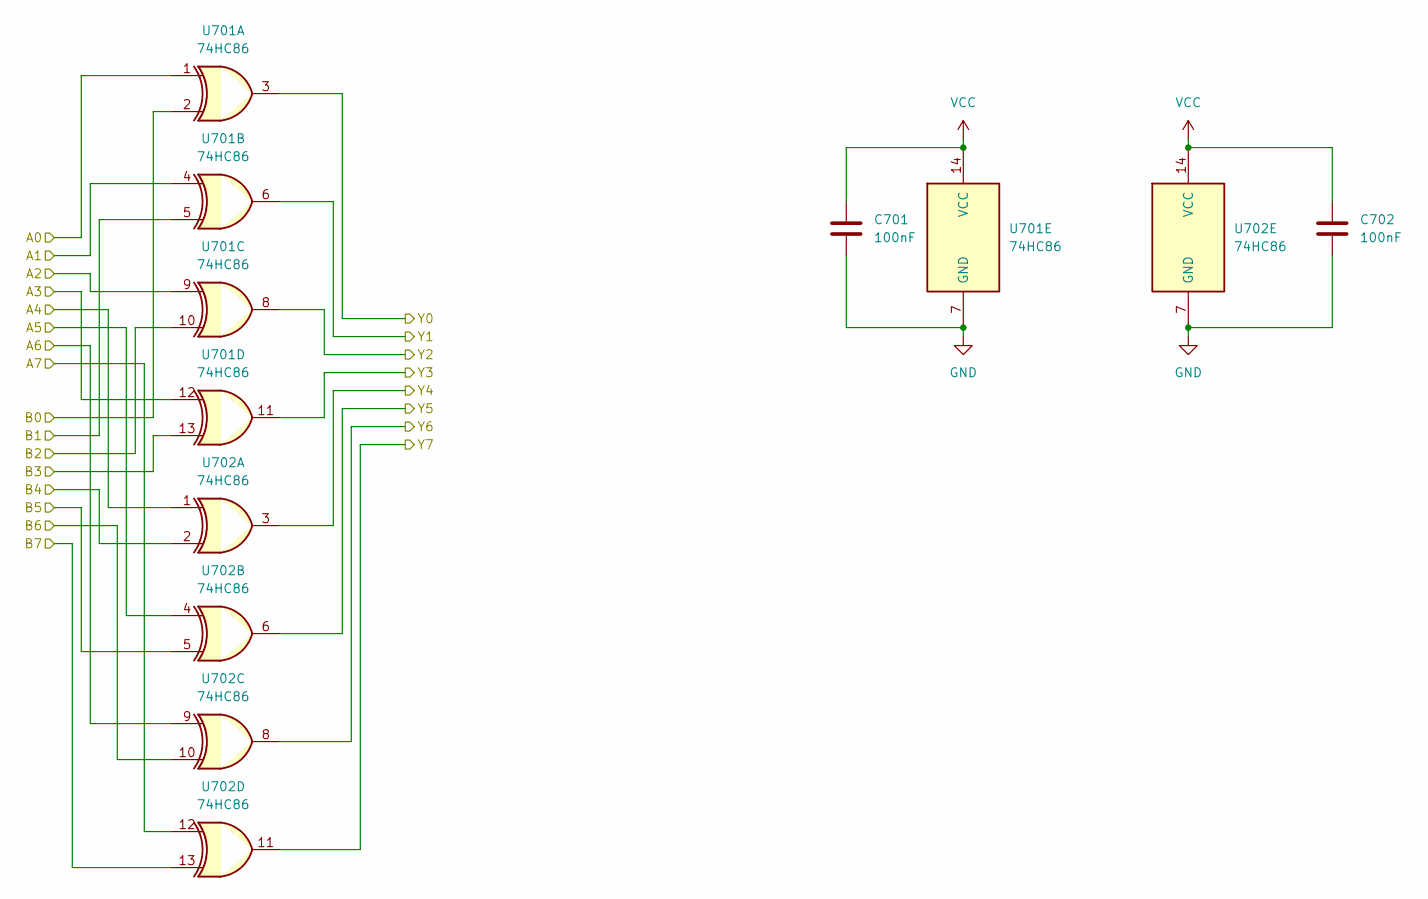
[picture p179: schematic gate_xor_8bit.kicad_sch]

Parts:
C701, C702: 100nF; C_Disc_D5.0mm_W2.5mm_P5.00mm
U701, U702: 74HC86; DIP-14_W7.62mm

Connections:
A0: U701.1
A1: U701.4
A2: U701.9
A3: U701.12
A4: U702.1
A5: U702.4
A6: U702.9
A7: U702.12
B0: U701.2
B1: U701.5
B2: U701.10
B3: U701.13
B4: U702.2
B5: U702.5
B6: U702.10
B7: U702.13
GND: C701.2, C702.2, U701.7 (GND), U702.7 (GND)
VCC: C701.1, C702.1, U701.14 (VCC), U702.14 (VCC)
Y0: U701.3
Y1: U701.6
Y2: U701.8
Y3: U701.11
Y4: U702.3
Y5: U702.6
Y6: U702.8
Y7: U702.11
