tmarhguy/tomato/hardware/kicad/modules/mux/drivers-74xx/drive8_2to1.kicad_sch

## KiCad design hardware/kicad/modules/mux/drivers-74xx/drive8_2to1.kicad_sch (2026-06-27)

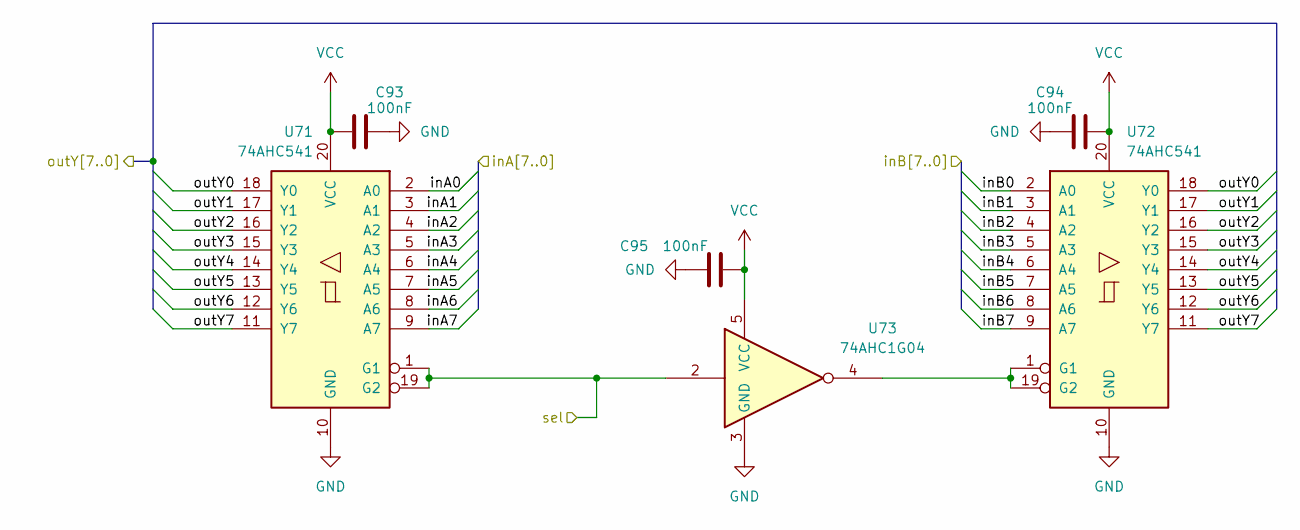
[picture p180: schematic drive8_2to1.kicad_sch]

Parts:
C93, C94, C95: 100nF; C_0603_1608Metric
U71, U72: 74AHC541; SOIC-20W_7.5x12.8mm_P1.27mm
U73: 74AHC1G04; SOT-23-5

Connections:
GND: C93.1, C94.1, C95.1, U71.10 (GND), U72.10 (GND), U73.3 (GND)
unnamed: U72.1 (G1), U72.19 (G2), U73.4
VCC: C93.2, C94.2, C95.2, U71.20 (VCC), U72.20 (VCC), U73.5 (VCC)
inA0: U71.2 (A0)
inA1: U71.3 (A1)
inA2: U71.4 (A2)
inA3: U71.5 (A3)
inA4: U71.6 (A4)
inA5: U71.7 (A5)
inA6: U71.8 (A6)
inA7: U71.9 (A7)
inB0: U72.2 (A0)
inB1: U72.3 (A1)
inB2: U72.4 (A2)
inB3: U72.5 (A3)
inB4: U72.6 (A4)
inB5: U72.7 (A5)
inB6: U72.8 (A6)
inB7: U72.9 (A7)
outY0: U71.18 (Y0), U72.18 (Y0)
outY1: U71.17 (Y1), U72.17 (Y1)
outY2: U71.16 (Y2), U72.16 (Y2)
outY3: U71.15 (Y3), U72.15 (Y3)
outY4: U71.14 (Y4), U72.14 (Y4)
outY5: U71.13 (Y5), U72.13 (Y5)
outY6: U71.12 (Y6), U72.12 (Y6)
outY7: U71.11 (Y7), U72.11 (Y7)
sel: U71.1 (G1), U71.19 (G2), U73.2
