tmarhguy/tomato/hardware/kicad/modules/mux/drivers-74xx/driver1_8to1.kicad_sch

## KiCad design hardware/kicad/modules/mux/drivers-74xx/driver1_8to1.kicad_sch (2026-06-26)

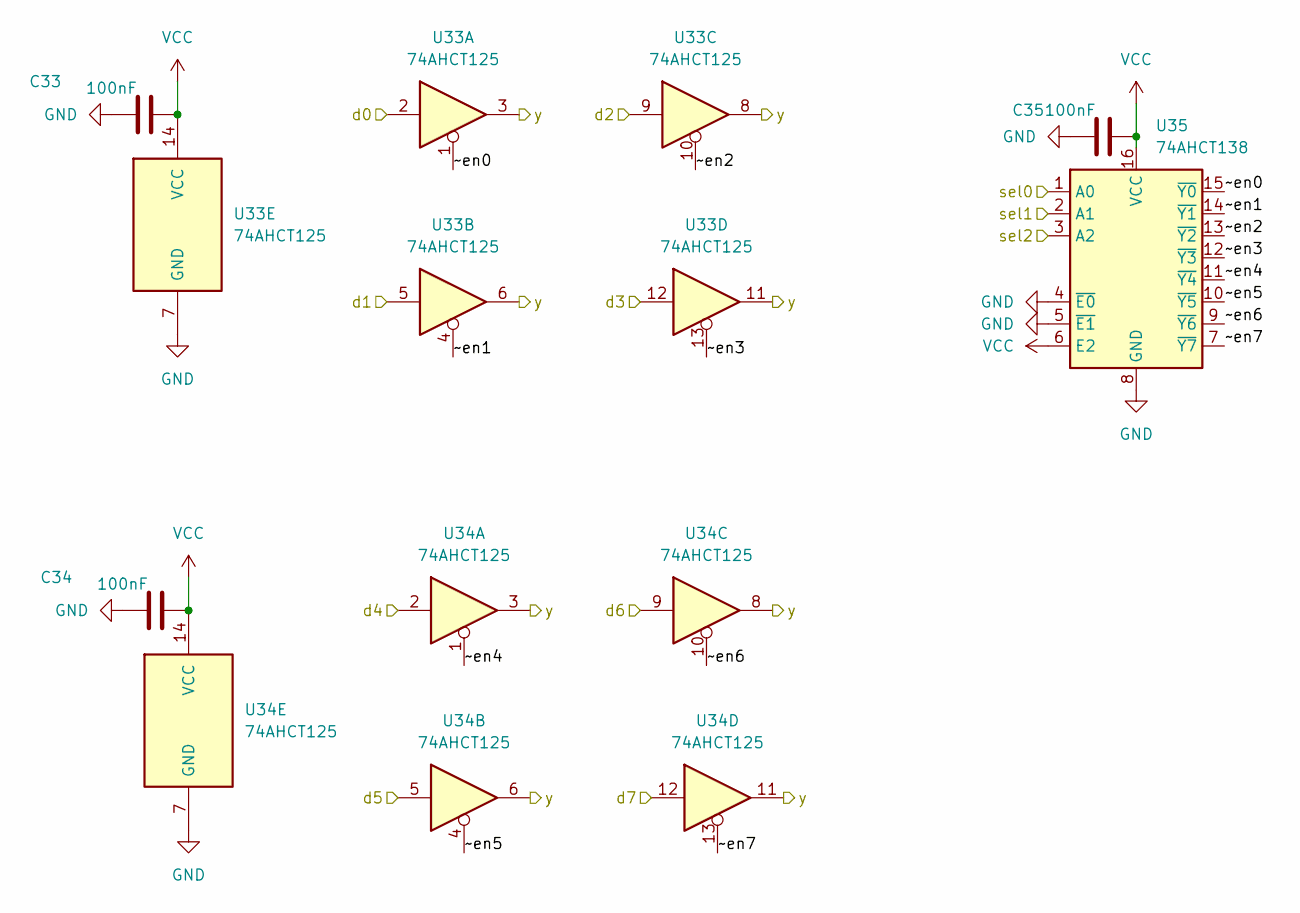
[picture p181: schematic driver1_8to1.kicad_sch]

Parts:
C33, C34, C35: 100nF; C_0805_2012Metric
U33, U34: 74AHCT125; SOIC-14_3.9x8.7mm_P1.27mm
U35: 74AHCT138; SOIC-16_3.9x9.9mm_P1.27mm

Connections:
GND: C33.1, C34.1, C35.1, U33.7 (GND), U34.7 (GND), U35.4 (~E0), U35.5 (~E1), U35.8 (GND)
VCC: C33.2, C34.2, C35.2, U33.14 (VCC), U34.14 (VCC), U35.6 (E2), U35.16 (VCC)
d0: U33.2
d1: U33.5
d2: U33.9
d3: U33.12
d4: U34.2
d5: U34.5
d6: U34.9
d7: U34.12
sel0: U35.1 (A0)
sel1: U35.2 (A1)
sel2: U35.3 (A2)
y: U33.3, U33.6, U33.8, U33.11, U34.3, U34.6, U34.8, U34.11
~en0: U33.1, U35.15 (~Y0)
~en1: U33.4, U35.14 (~Y1)
~en2: U33.10, U35.13 (~Y2)
~en3: U33.13, U35.12 (~Y3)
~en4: U34.1, U35.11 (~Y4)
~en5: U34.4, U35.10 (~Y5)
~en6: U34.10, U35.9 (~Y6)
~en7: U34.13, U35.7 (~Y7)
