tmarhguy/tomato/hardware/kicad/modules/mux/drivers_inv-74xx/drive_inv32.kicad_sch

## KiCad design hardware/kicad/modules/mux/drivers_inv-74xx/drive_inv32.kicad_sch (2026-06-27)

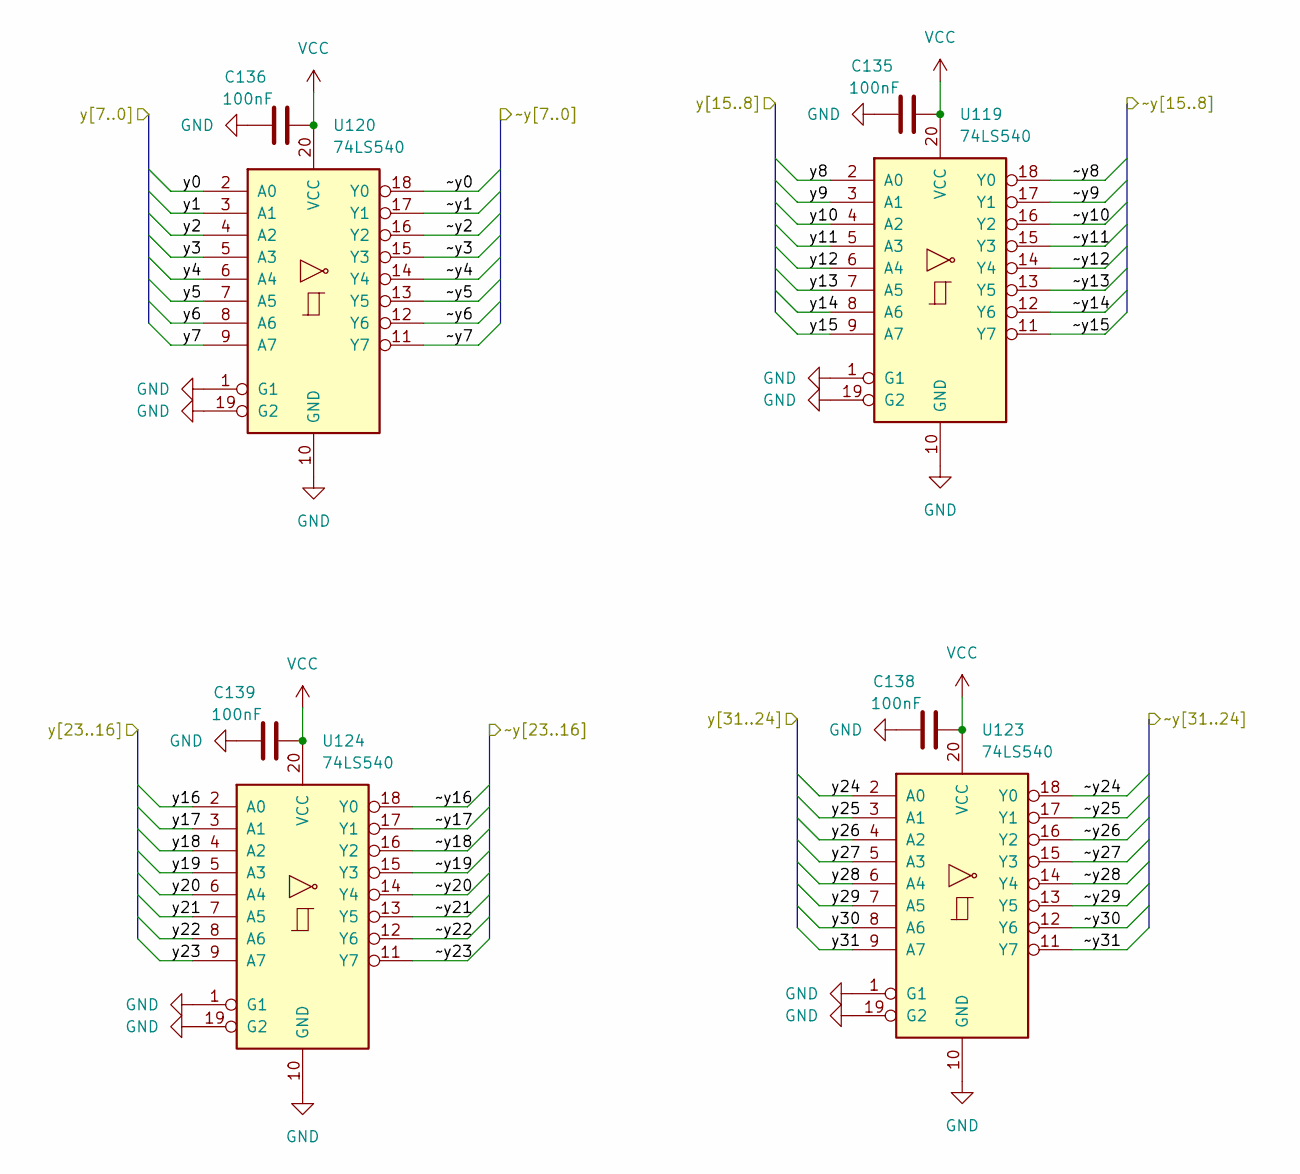
[picture p182: schematic drive_inv32.kicad_sch]

Parts:
C135, C136, C138, C139: 100nF; C_0805_2012Metric
U119, U120, U123, U124: 74LS540; SOIC-20W_7.5x12.8mm_P1.27mm

Connections:
GND: C135.1, C136.1, C138.1, C139.1, U119.1 (G1), U119.10 (GND), U119.19 (G2), U120.1 (G1), U120.10 (GND), U120.19 (G2), U123.1 (G1), U123.10 (GND), U123.19 (G2), U124.1 (G1), U124.10 (GND), U124.19 (G2)
VCC: C135.2, C136.2, C138.2, C139.2, U119.20 (VCC), U120.20 (VCC), U123.20 (VCC), U124.20 (VCC)
y0: U120.2 (A0)
y1: U120.3 (A1)
y2: U120.4 (A2)
y3: U120.5 (A3)
y4: U120.6 (A4)
y5: U120.7 (A5)
y6: U120.8 (A6)
y7: U120.9 (A7)
y8: U119.2 (A0)
y9: U119.3 (A1)
y10: U119.4 (A2)
y11: U119.5 (A3)
y12: U119.6 (A4)
y13: U119.7 (A5)
y14: U119.8 (A6)
y15: U119.9 (A7)
y16: U124.2 (A0)
y17: U124.3 (A1)
y18: U124.4 (A2)
y19: U124.5 (A3)
y20: U124.6 (A4)
y21: U124.7 (A5)
y22: U124.8 (A6)
y23: U124.9 (A7)
y24: U123.2 (A0)
y25: U123.3 (A1)
y26: U123.4 (A2)
y27: U123.5 (A3)
y28: U123.6 (A4)
y29: U123.7 (A5)
y30: U123.8 (A6)
y31: U123.9 (A7)
~y0: U120.18 (Y0)
~y1: U120.17 (Y1)
~y2: U120.16 (Y2)
~y3: U120.15 (Y3)
~y4: U120.14 (Y4)
~y5: U120.13 (Y5)
~y6: U120.12 (Y6)
~y7: U120.11 (Y7)
~y8: U119.18 (Y0)
~y9: U119.17 (Y1)
~y10: U119.16 (Y2)
~y11: U119.15 (Y3)
~y12: U119.14 (Y4)
~y13: U119.13 (Y5)
~y14: U119.12 (Y6)
~y15: U119.11 (Y7)
~y16: U124.18 (Y0)
~y17: U124.17 (Y1)
~y18: U124.16 (Y2)
~y19: U124.15 (Y3)
~y20: U124.14 (Y4)
~y21: U124.13 (Y5)
~y22: U124.12 (Y6)
~y23: U124.11 (Y7)
~y24: U123.18 (Y0)
~y25: U123.17 (Y1)
~y26: U123.16 (Y2)
~y27: U123.15 (Y3)
~y28: U123.14 (Y4)
~y29: U123.13 (Y5)
~y30: U123.12 (Y6)
~y31: U123.11 (Y7)
