tmarhguy/tomato/hardware/kicad/modules/mux/mux-74xx/mux4_8to1.kicad_sch

## KiCad design hardware/kicad/modules/mux/mux-74xx/mux4_8to1.kicad_sch (2026-06-26)

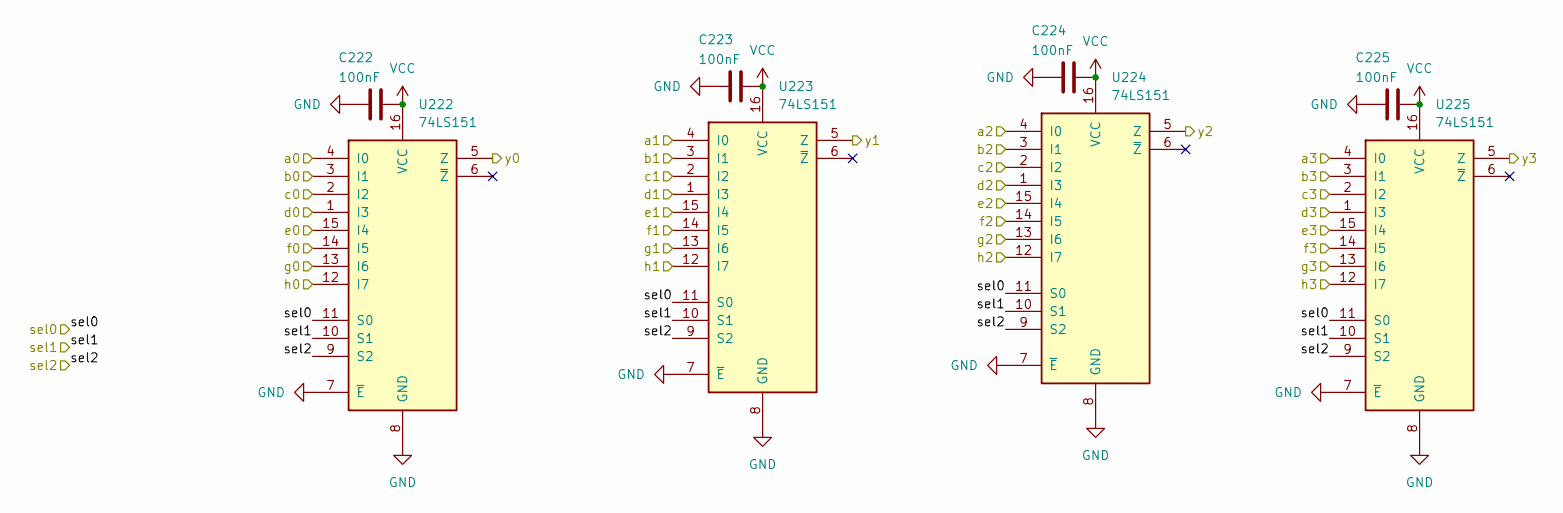
[picture p183: schematic mux4_8to1.kicad_sch]

Parts:
C222, C223, C224, C225: 100nF; C_0805_2012Metric
U222, U223, U224, U225: 74LS151; SOIC-16_3.9x9.9mm_P1.27mm

Connections:
GND: C222.1, C223.1, C224.1, C225.1, U222.7 (~E), U222.8 (GND), U223.7 (~E), U223.8 (GND), U224.7 (~E), U224.8 (GND), U225.7 (~E), U225.8 (GND)
VCC: C222.2, C223.2, C224.2, C225.2, U222.16 (VCC), U223.16 (VCC), U224.16 (VCC), U225.16 (VCC)
a0: U222.4 (I0)
a1: U223.4 (I0)
a2: U224.4 (I0)
a3: U225.4 (I0)
b0: U222.3 (I1)
b1: U223.3 (I1)
b2: U224.3 (I1)
b3: U225.3 (I1)
c0: U222.2 (I2)
c1: U223.2 (I2)
c2: U224.2 (I2)
c3: U225.2 (I2)
d0: U222.1 (I3)
d1: U223.1 (I3)
d2: U224.1 (I3)
d3: U225.1 (I3)
e0: U222.15 (I4)
e1: U223.15 (I4)
e2: U224.15 (I4)
e3: U225.15 (I4)
f0: U222.14 (I5)
f1: U223.14 (I5)
f2: U224.14 (I5)
f3: U225.14 (I5)
g0: U222.13 (I6)
g1: U223.13 (I6)
g2: U224.13 (I6)
g3: U225.13 (I6)
h0: U222.12 (I7)
h1: U223.12 (I7)
h2: U224.12 (I7)
h3: U225.12 (I7)
sel0: U222.11 (S0), U223.11 (S0), U224.11 (S0), U225.11 (S0)
sel1: U222.10 (S1), U223.10 (S1), U224.10 (S1), U225.10 (S1)
sel2: U222.9 (S2), U223.9 (S2), U224.9 (S2), U225.9 (S2)
y0: U222.5 (Z)
y1: U223.5 (Z)
y2: U224.5 (Z)
y3: U225.5 (Z)
