tmarhguy/tomato/hardware/kicad/modules/mux/mux-74xx/mux_2to1-8b.kicad_sch

## KiCad design hardware/kicad/modules/mux/mux-74xx/mux_2to1-8b.kicad_sch (2026-06-22)

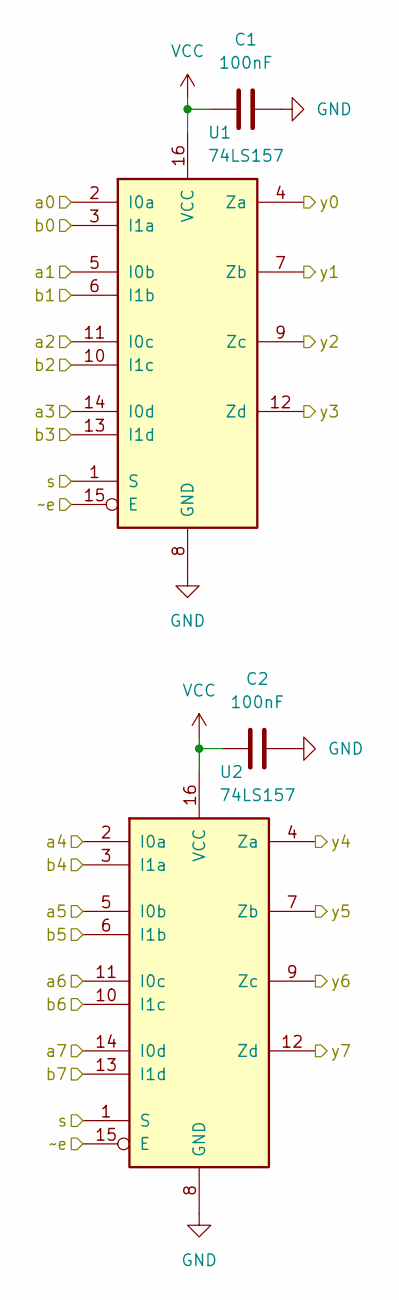
[picture p184: schematic mux_2to1-8b.kicad_sch]

Parts:
C1, C2: 100nF; C_0201_0603Metric
U1, U2: 74LS157; SOIC-16_3.9x9.9mm_P1.27mm

Connections:
GND: C1.2, C2.2, U1.8 (GND), U2.8 (GND)
VCC: C1.1, C2.1, U1.16 (VCC), U2.16 (VCC)
a0: U1.2 (I0a)
a1: U1.5 (I0b)
a2: U1.11 (I0c)
a3: U1.14 (I0d)
a4: U2.2 (I0a)
a5: U2.5 (I0b)
a6: U2.11 (I0c)
a7: U2.14 (I0d)
b0: U1.3 (I1a)
b1: U1.6 (I1b)
b2: U1.10 (I1c)
b3: U1.13 (I1d)
b4: U2.3 (I1a)
b5: U2.6 (I1b)
b6: U2.10 (I1c)
b7: U2.13 (I1d)
s: U1.1 (S), U2.1 (S)
y0: U1.4 (Za)
y1: U1.7 (Zb)
y2: U1.9 (Zc)
y3: U1.12 (Zd)
y4: U2.4 (Za)
y5: U2.7 (Zb)
y6: U2.9 (Zc)
y7: U2.12 (Zd)
~e: U1.15 (E), U2.15 (E)
