tmarhguy/tomato/hardware/kicad/modules/mux/mux-74xx/mux_8to1-8b.kicad_sch

## KiCad design hardware/kicad/modules/mux/mux-74xx/mux_8to1-8b.kicad_sch (2026-06-05)

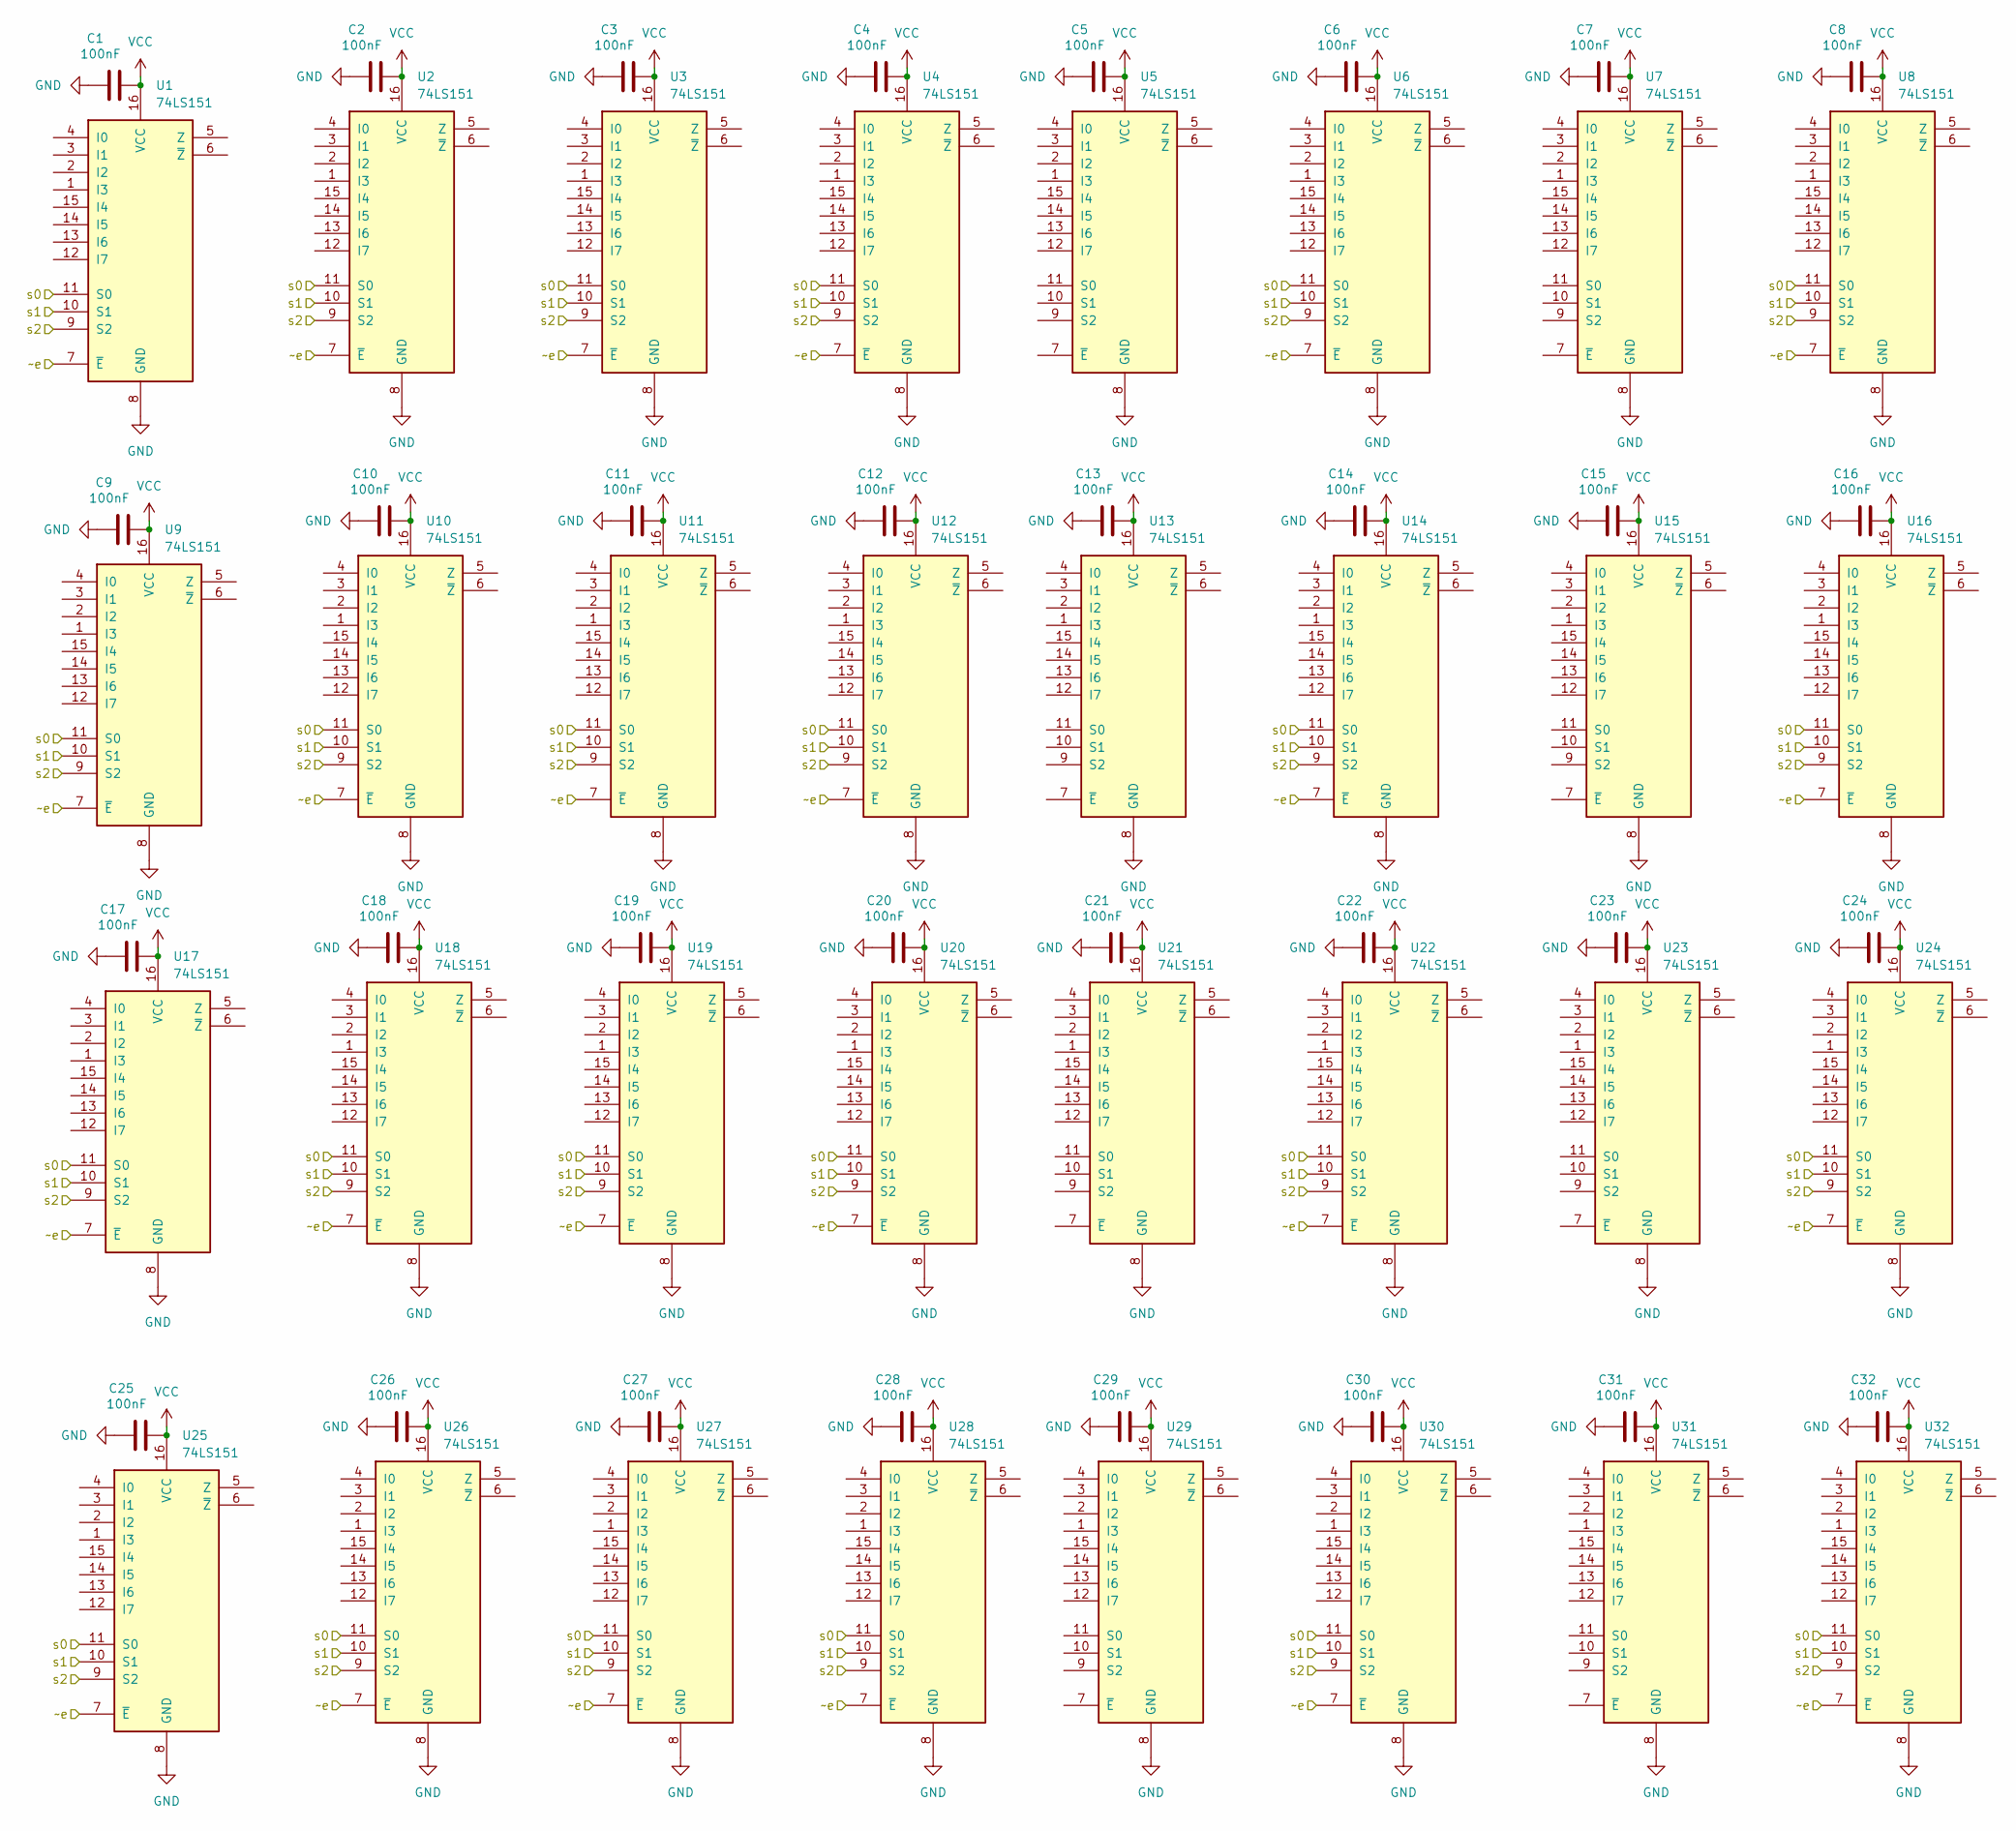
[picture p185: schematic mux_8to1-8b.kicad_sch]

Parts:
C1, C2, C3, C4, C5, C6, C7, C8, C9, C10, C11, C12, C13, C14, C15, C16, C17, C18, C19, C20, C21, C22, C23, C24, C25, C26, C27, C28, C29, C30, C31, C32: 100nF
U1, U2, U3, U4, U5, U6, U7, U8, U9, U10, U11, U12, U13, U14, U15, U16, U17, U18, U19, U20, U21, U22, U23, U24, U25, U26, U27, U28, U29, U30, U31, U32: 74LS151

Connections:
GND: C1.1, C2.1, C3.1, C4.1, C5.1, C6.1, C7.1, C8.1, C9.1, C10.1, C11.1, C12.1, C13.1, C14.1, C15.1, C16.1, C17.1, C18.1, C19.1, C20.1, C21.1, C22.1, C23.1, C24.1, C25.1, C26.1, C27.1, C28.1, C29.1, C30.1, C31.1, C32.1, U1.8 (GND), U2.8 (GND), U3.8 (GND), U4.8 (GND), U5.8 (GND), U6.8 (GND), U7.8 (GND), U8.8 (GND), U9.8 (GND), U10.8 (GND), U11.8 (GND), U12.8 (GND), U13.8 (GND), U14.8 (GND), U15.8 (GND), U16.8 (GND), U17.8 (GND), U18.8 (GND), U19.8 (GND), U20.8 (GND), U21.8 (GND), U22.8 (GND), U23.8 (GND), U24.8 (GND), U25.8 (GND), U26.8 (GND), U27.8 (GND), U28.8 (GND), U29.8 (GND), U30.8 (GND), U31.8 (GND), U32.8 (GND)
VCC: C1.2, C2.2, C3.2, C4.2, C5.2, C6.2, C7.2, C8.2, C9.2, C10.2, C11.2, C12.2, C13.2, C14.2, C15.2, C16.2, C17.2, C18.2, C19.2, C20.2, C21.2, C22.2, C23.2, C24.2, C25.2, C26.2, C27.2, C28.2, C29.2, C30.2, C31.2, C32.2, U1.16 (VCC), U2.16 (VCC), U3.16 (VCC), U4.16 (VCC), U5.16 (VCC), U6.16 (VCC), U7.16 (VCC), U8.16 (VCC), U9.16 (VCC), U10.16 (VCC), U11.16 (VCC), U12.16 (VCC), U13.16 (VCC), U14.16 (VCC), U15.16 (VCC), U16.16 (VCC), U17.16 (VCC), U18.16 (VCC), U19.16 (VCC), U20.16 (VCC), U21.16 (VCC), U22.16 (VCC), U23.16 (VCC), U24.16 (VCC), U25.16 (VCC), U26.16 (VCC), U27.16 (VCC), U28.16 (VCC), U29.16 (VCC), U30.16 (VCC), U31.16 (VCC), U32.16 (VCC)
s0: U1.11 (S0), U2.11 (S0), U3.11 (S0), U4.11 (S0), U6.11 (S0), U8.11 (S0), U9.11 (S0), U10.11 (S0), U11.11 (S0), U12.11 (S0), U14.11 (S0), U16.11 (S0), U17.11 (S0), U18.11 (S0), U19.11 (S0), U20.11 (S0), U22.11 (S0), U24.11 (S0), U25.11 (S0), U26.11 (S0), U27.11 (S0), U28.11 (S0), U30.11 (S0), U32.11 (S0)
s1: U1.10 (S1), U2.10 (S1), U3.10 (S1), U4.10 (S1), U6.10 (S1), U8.10 (S1), U9.10 (S1), U10.10 (S1), U11.10 (S1), U12.10 (S1), U14.10 (S1), U16.10 (S1), U17.10 (S1), U18.10 (S1), U19.10 (S1), U20.10 (S1), U22.10 (S1), U24.10 (S1), U25.10 (S1), U26.10 (S1), U27.10 (S1), U28.10 (S1), U30.10 (S1), U32.10 (S1)
s2: U1.9 (S2), U2.9 (S2), U3.9 (S2), U4.9 (S2), U6.9 (S2), U8.9 (S2), U9.9 (S2), U10.9 (S2), U11.9 (S2), U12.9 (S2), U14.9 (S2), U16.9 (S2), U17.9 (S2), U18.9 (S2), U19.9 (S2), U20.9 (S2), U22.9 (S2), U24.9 (S2), U25.9 (S2), U26.9 (S2), U27.9 (S2), U28.9 (S2), U30.9 (S2), U32.9 (S2)
~e: U1.7 (~E), U2.7 (~E), U3.7 (~E), U4.7 (~E), U6.7 (~E), U8.7 (~E), U9.7 (~E), U10.7 (~E), U11.7 (~E), U12.7 (~E), U14.7 (~E), U16.7 (~E), U17.7 (~E), U18.7 (~E), U19.7 (~E), U20.7 (~E), U22.7 (~E), U24.7 (~E), U25.7 (~E), U26.7 (~E), U27.7 (~E), U28.7 (~E), U30.7 (~E), U32.7 (~E)
