tmarhguy/tomato/hardware/fpga/core/rtl/main.v

/*
 * Tomato — top-level CPU (Nexys A7 board)
 *
 * Engineer : Tyrone Marhguy
 * Project  : Tomato 32-bit CPU
 * File     : main.v
 * Target   : Artix-7 / synthesizable Verilog-2001
 * ISA      : docs/isa/tomato.v1.csv
 *
 * Copyright (c) 2025-2026 Tyrone Marhguy
 * SPDX-License-Identifier: Apache-2.0 WITH SHL-2.1
 *
 * This is the machine, not the board. Everything that only exists because the
 * FPGA has pins — pixel timing, glyph ROM, 7-seg multiplexing, button
 * debounce — lives in rtl/board/ and hangs off the ports below. What is left
 * matches the Digital sheet in hardware/verilog/main.v.
 *
 * Peripherals: IN/OUT via lane sel=2 + io_out latch; MMIO [21:19]==111.
 * The tile RAM read port is exposed the way the Digital `vga` block exposes
 * it — the scanout supplies the address from outside, on its own clock.
 *
 * FPGA burn: without -DTOMATO_SIM, dmem is initialized from rtl/burn/dmem_init.vh
 * (Tomato OS by default). Microcode is always burned in control.v.
 * Board top: rtl/board/nexys_top.v.
 */

module main #(parameter CPU_HZ = 6250000) (
    input         clk,
    input         reset,
    input  [7:0]  kb_data,     // PS/2 / keypad byte (lane IN / MMIO)
    input         kb_ready,    // key pending (IRQ + status MMIO)
    output        kb_rd,       // CPU consumed the key this cycle
    output [7:0]  io_out,      // last OUT byte (UART TX / LED)
    output [31:0] disp_value,  // last nonzero WB / store (board 7-seg)
    output        halted,
    output [15:0] activity_leds, // board LED row: beat/halt/RX/TX + activity
    // Tile RAM scanout port — driven by rtl/board/videoout.v
    input         tile_rclk,
    input  [12:0] tile_raddr,
    output [31:0] tile_rdata,
    output [6:0] ble_addr,
    output ble_wr,
    output [7:0] ble_wdata,
    input [31:0] ble_rdata
);
    wire       kb_en = kb_ready;

    wire        cregwe, cbanken;
    wire        cmemrd, cmemwr;
    wire [3:0]  cbytesel;
    wire [2:0]  cbussel, cwbsel, cpcsrc, cpccond, ccsel;
    wire [3:0]  cirsel;
    wire [1:0]  ccycles, cspop, cshiftop;
    wire        cbranchen, cjumptype, cpclinkwe;
    wire        cmulen, cpenc, halt, calusel;
    wire [7:0]  clutA, clutB;

    wire        fetch, exec;
    wire [8:0]  opcode;
    wire [4:0]  addra, addrb, addrc, addrw;
    wire [2:0]  banksel;
    wire [21:0] addrabs, offset;
    wire [31:0] imm;
    wire [31:0] ra, rb, rc;
    wire [31:0] alu_a = calusel ? rb : ra;
    wire [31:0] aluout;
    wire [7:0]  flags;
    wire [31:0] shiftmul;
    wire [31:0] mulhi;
    wire        anz;
    wire [23:0] pcsave, pclink, spout, memaddr;
    wire [23:0] pcout;
    wire        memrdout;
    wire [31:0] memram, memdin;
    wire [31:0] wbdata;
    wire        aluflagwe;
    wire        flagswe = aluflagwe & exec;

    wire        vga_hit = (memaddr[21:19] == 3'b110);
    wire        kb_hit  = (memaddr[21:19] == 3'b111);
    // The nRF8001 ACI controller occupies the keyboard MMIO +0x100 subwindow.
    wire        ble_hit = kb_hit && memaddr[8];
    // Dual-LUT compiler counter: keyboard MMIO +0x80, not BLE.
    wire        compiler_hit = kb_hit && memaddr[7] && !memaddr[8];
    wire        compiler_wr = exec && cmemwr && compiler_hit;
    wire [31:0] compiler_rdata;
    wire        compiler_busy, compiler_done, compiler_hit_flag, compiler_held;
    wire [15:0] compiler_count, compiler_latched;
    compiler_fsm compiler0 (
        .clk(clk), .reset(reset), .wr(compiler_wr),
        .sel(memaddr[2:0]), .wdata(wbdata), .rdata(compiler_rdata),
        .busy_o(compiler_busy), .done_o(compiler_done),
        .hit_o(compiler_hit_flag), .held_o(compiler_held),
        .count_o(compiler_count), .latched_o(compiler_latched)
    );
    assign ble_addr = memaddr[6:0];
    assign ble_wr = exec && cmemwr && ble_hit;
    assign ble_wdata = wbdata[7:0];
    reg  [7:0]  io_out_r;
    assign io_out = io_out_r;

    // Key is consumed by a load of MMIO word 0 or by the IN opcode. The keypad
    // drops kb_ready on this strobe so one press yields exactly one keycode.
    assign kb_rd = exec & ((cmemrd & kb_hit & ~ble_hit &
                            (memaddr[1:0] == 0)) | (opcode == 9'h0C8));

    // Millisecond clock for OS delays; timer reads never consume a key.
    localparam MS_CYCLES = CPU_HZ / 1000;
    reg [31:0] ms_div, milliseconds;
    always @(posedge clk) begin
        if (reset) begin ms_div <= 0; milliseconds <= 0; end
        else if (ms_div == MS_CYCLES-1) begin
            ms_div <= 0; milliseconds <= milliseconds + 1'b1;
        end else ms_div <= ms_div + 1'b1;
    end

    // OUT opcode: latch peripheral byte (board UART/LED glue — same spirit as VGA MMIO)
    always @(posedge clk) begin
        if (reset)                         io_out_r <= 8'h00;
        else if (exec && (opcode == 9'h0C9)) io_out_r <= ra[7:0];
    end

    lane lane0 (
        .mem_in  (memram),
        .sel     (cbytesel),
        .io_data (kb_data),
        .mem_out (memdin)
    );

    pc pc0 (
        .clk       (clk),
        .rst       (reset),
        .cycles    (ccycles),
        .pc_src    (cpcsrc),
        .offset    (offset),
        .alu_in    (aluout),
        .mem_din   (memdin),
        .csr_flags (flags),
        .pc_cond   (cpccond),
        .jump      (cjumptype),
        .branch_en (cbranchen),
        .link_we   (cpclinkwe),
        .halt_in   (halt),
        .ecall_in  ((opcode == 9'h0E1) & exec),
        .int_en_in (1'b0),   // IRQ off until SEI; kb via IN / MMIO only
        .int_req   (kb_en),
        .int_vec0  (1'b0),
        .int_vec1  (1'b0),
        .int_vec2  (1'b0),
        .pc        (pcout),
        .pc_next   (pcsave),
        .pc_link   (pclink),
        .fetch     (fetch),
        .execute   (exec),
        .halted_o  (halted)
    );

    sp sp0 (
        .clk     (clk),
        .rst     (reset),
        .exec    (exec),
        .sp_op   (cspop),
        .load_in (aluout),
        .sp_out  (spout)
    );

    vga vga0 (
        .clk      (clk),
        .mem_addr (memaddr),
        .mem_din  (wbdata),
        .mem_wr   (cmemwr),
        .rclk     (tile_rclk),
        .raddr    (tile_raddr),
        .rdata    (tile_rdata)
    );

    // 7-seg = last nonzero writeback (or store). Latching every execute let
    // HALT wipe the answer; latching every LW of 0 (the OS idle poll) held
    // 00000000 on the board while the machine was clearly running.
    reg [31:0] disp;
    wire disp_reg = exec & cregwe & (addrw != 5'd0) & (wbdata != 32'd0);
    wire disp_mem = exec & cmemwr & (wbdata != 32'd0);
    always @(posedge clk) begin
        if (reset)                 disp <= 32'h0;
        else if (disp_reg | disp_mem) disp <= wbdata;
    end
    assign disp_value = disp;

    // Board LED activity: writeback chatter for apps; Dual-LUT sweep while
    // the hardware compiler searches; freeze on latched opcodes after a hit,
    // then release to writeback after a short hold so leaving the compiler
    // does not leave the row stuck forever.
    reg [11:0] wb_leds;
    reg [15:0] sweep_or;
    reg [21:0] latch_hold; // ~0.67 s at 6.25 MHz
    reg [22:0] beat;
    wire       wb_any = exec & ((cregwe & (addrw != 5'd0)) | cmemwr);
    always @(posedge clk) begin
        if (reset) begin
            wb_leds <= 12'h0;
            sweep_or <= 16'h0;
            latch_hold <= 22'h0;
            beat <= 23'h0;
        end else begin
            beat <= beat + 1'b1;
            if (wb_any)
                wb_leds <= wbdata[11:0];
            if (compiler_busy) begin
                sweep_or <= sweep_or | compiler_count;
                latch_hold <= 22'h0;
            end else if (compiler_done | compiler_held) begin
                if (latch_hold != 22'h3FFFFF)
                    latch_hold <= latch_hold + 1'b1;
            end else begin
                sweep_or <= 16'h0;
                latch_hold <= 22'h0;
            end
            // Fresh GO clears the sticky OR so a new search animates cleanly.
            if (compiler_wr && (memaddr[2:0] == 3'd5) && wbdata[0])
                sweep_or <= 16'h0;
        end
    end
    wire [11:0] freeze12 = compiler_latched[11:0] | sweep_or[11:0] | 12'h001;
    wire [11:0] activity_low =
        compiler_busy ? compiler_count[11:0] :
        ((compiler_done | compiler_held) && (latch_hold != 22'h3FFFFF)) ? freeze12 :
        wb_leds;
    // Bits 13:12 reserved for Envelop RX/TX pulses (board top overlays them).
    assign activity_leds = {beat[22], halted, 1'b0, 1'b0, activity_low};

    regs regs0 (
        .clk      (clk),
        .we       (cregwe),
        .exec     (exec),
        .bank_en  (cbanken),
        .bank_sel (banksel),
        .addr_a   (addra),
        .addr_b   (addrb),
        .addr_c   (addrc),
        .addr_w   (addrw),
        .data_w   (wbdata),
        .data_a   (ra),
        .data_b   (rb),
        .data_c   (rc)
    );

    wb wb0 (
        .wb_sel      (cwbsel),
        .alu_out     (aluout),
        .shift_mul   (shiftmul),
        .pc_save     (pcsave),
        .mem_din     (memdin),
        .reg_a       (ra),
        .imm         (imm),
        .csr_flags   (flags),
        .mul_hi      (mulhi),
        .wb_data     (wbdata)
    );

    // IR must see raw mem words — lane/byte_sel is for loads only. Fetching
    // through memdin after LB/SB leaves byte_sel≠0 and corrupts the next insn.
    ir ir0 (
        .clk      (clk),
        .load     (fetch),
        .data_in  (memram),
        .imm_sel  (cirsel),
        .reg_b    (rb),
        .opcode   (opcode),
        .addr_a   (addra),
        .addr_b   (addrb),
        .addr_c   (addrc),
        .addr_w   (addrw),
        .bank_sel (banksel),
        .addr_abs (addrabs),
        .offset   (offset),
        .imm_out  (imm)
    );

    bus bus0 (
        .fetch     (fetch),
        .mem_rd_in (cmemrd),
        .addr_sel  (cbussel),
        .ir_addr   (addrabs),
        .reg_b     (rb),
        .alu_in    (aluout),
        .pc        (pcout),
        .sp        (spout),
        .addr      (memaddr),
        .mem_rd    (memrdout)
    );

    // 16K×32 dmem (not VGA window). Byte/half stores merge via cbytesel (lane map).
    // FPGA: program image burned here (tools/gen_fpga_burn.py → burn/dmem_init.vh).
    // Sim TBs: compile with -DTOMATO_SIM and $readmemh into uut.dmem themselves.
    //
    // The Digital sheet's RAM reads asynchronously, and both phases of the
    // sequencer need the word in the same cycle they present the address: FETCH
    // latches it into IR, and a byte/half store merges it with wbdata on the very
    // edge that writes it back. Block RAM has no async port, so the read is taken
    // on the falling edge instead. The word lands mid-cycle — before the posedge
    // that consumes it — and a store still sees the pre-write contents, because
    // the sample happens half a cycle ahead of the write. Costs half the period
    // of setup, which is free at the divided CPU clock, and keeps the sequencer
    // at two phases. 16K×32 async read would otherwise mean ~500 Kb of LUTs.
    (* ram_style = "block" *) reg [31:0] dmem [0:16383];
`ifndef TOMATO_SIM
    integer burn_i;
    initial begin
        for (burn_i = 0; burn_i < 16384; burn_i = burn_i + 1)
            dmem[burn_i] = 32'h0;
        `include "burn/dmem_init.vh"
    end
`endif
    wire [13:0] dmema = memaddr[13:0];
    reg  [31:0] dread;
    always @(negedge clk) dread <= dmem[dmema];
    reg  [31:0] dmerge;
    always @(*) begin
        case (cbytesel)
            4'd4, 4'd8:  dmerge = {dread[31:8],  wbdata[7:0]};                 // byte0
            4'd5, 4'd9:  dmerge = {dread[31:16], wbdata[7:0], dread[7:0]};     // byte1
            4'd6, 4'd10: dmerge = {dread[31:24], wbdata[7:0], dread[15:0]};    // byte2
            4'd7, 4'd11: dmerge = {wbdata[7:0],  dread[23:0]};                 // byte3
            4'd12, 4'd14: dmerge = {dread[31:16], wbdata[15:0]};               // half0
            4'd13, 4'd15: dmerge = {wbdata[15:0], dread[15:0]};                // half1
            default:      dmerge = wbdata;                                      // word
        endcase
    end
    always @(posedge clk) begin
        if (cmemwr & exec & ~vga_hit & ~kb_hit) dmem[dmema] <= dmerge;
    end
    // MMIO [21:19]==111: word0 = kb data, word1 = {ready}
    assign memram = ble_hit ? ble_rdata : compiler_hit ? compiler_rdata : kb_hit
                  ? (memaddr[1:0] == 0 ? {24'b0, kb_data} :
                     memaddr[1:0] == 1 ? {31'b0, kb_ready} :
                     memaddr[1:0] == 2 ? milliseconds : CPU_HZ)
                  : dread;

    alu alu0 (
        .lutA    (clutA),
        .lutB    (clutB),
        .A       (alu_a),
        .B       (imm),
        .C       (rc),
        .csel    (ccsel),
        .flag_we (flagswe),
        .clk     (clk),
        .out     (aluout),
        .csr     (flags)
    );

    muldiv muldiv0 (
        .a        (alu_a),
        .b        (imm),
        .mode     (cshiftop),
        .mulen    (cmulen),
        .isdiv    (cpenc),
        .result   (shiftmul),
        .resulthi (mulhi),
        .anz      (anz)
    );

    memio memio0 (
        .op      (opcode),
        .fetch   (fetch),
        .banken  (cbanken),
        .memrd   (cmemrd),
        .memwr   (cmemwr),
        .bytesel (cbytesel)
    );
    pcctrl pcctrl0 (
        .exec     (exec),
        .op       (opcode),
        .branchen (cbranchen),
        .jumptype (cjumptype),
        .pcsrc    (cpcsrc),
        .pclinkwe (cpclinkwe),
        .cycles   (ccycles),
        .pccond   (cpccond),
        .spop     (cspop),
        .halt     (halt)
    );
    aluctrl aluctrl0 (
        .op      (opcode),
        .lutA    (clutA),
        .lutB    (clutB),
        .csel    (ccsel),
        .flagwe  (aluflagwe),
        .shiftop (cshiftop),
        .mulen   (cmulen),
        .penc    (cpenc)
    );
    irctrl irctrl0 (
        .op     (opcode),
        .immsel (cirsel),
        .wbsel  (cwbsel),
        .regwe  (cregwe)
    );
    membus membus0 (
        .op     (opcode),
        .bussel (cbussel),
        .alusel (calusel)
    );
endmodule
