tmarhguy/tomato/verification/directed/alu-32b-final_alu-comb-flags_tb.v

//  A testbench for alu-32b-final_alu-comb-flags_tb
`timescale 1us/1ns

module alu-32b-final_alu-comb-flags_tb;
    reg [31:0] A;
    reg [31:0] B;
    reg [7:0] Opcode;
    reg [3:0] control;
    reg [31:0] C;
    reg [1:0] csel;
    reg CLK;
    reg FLAG_WE;
    reg \~flag_a_is_zero ;
    wire [31:0] Out;
    wire [12:0] CSR_FLAG;

  \alu-32b-final  \alu-32b-final 0 (
    .A(A),
    .B(B),
    .Opcode(Opcode),
    .control(control),
    .C(C),
    .csel(csel),
    .CLK(CLK),
    .FLAG_WE(FLAG_WE),
    .\~flag_a_is_zero (\~flag_a_is_zero ),
    .Out(Out),
    .CSR_FLAG(CSR_FLAG)
  );

    reg [143:0] patterns[0:11];
    integer i;

    initial begin
      patterns[0] = 144'b00000000000000000000000000000000_00000000000000000000000000000000_00000000000000000000000000000000_10010110_0000_00_0_0_00000000000000000000000000000000;
      patterns[1] = 144'b11111111111111111111111111111111_11111111111111111111111111111111_00000000000000000000000000000000_10010110_1101_01_0_0_00000000000000000000000000000000;
      patterns[2] = 144'b00000000000000000000000000000000_00000000000000000000000000000001_00000000000000000000000000000000_10010110_1101_01_0_0_11111111111111111111111111111111;
      patterns[3] = 144'b01111111111111111111111111111111_00000000000000000000000000000001_00000000000000000000000000000000_10010110_0001_01_0_0_10000000000000000000000000000000;
      patterns[4] = 144'b10000000000000000000000000000000_10000000000000000000000000000000_00000000000000000000000000000000_10010110_0101_10_0_0_00000000000000000000000000000000;
      patterns[5] = 144'b00000000000000000000000000000001_11111111111111111111111111111111_00000000000000000000000000000000_10010110_0101_00_0_0_00000000000000000000000000000000;
      patterns[6] = 144'b11111111111111111111111111111111_00000000000000000000000000000001_00000000000000000000000000000000_10010110_0101_00_0_0_00000000000000000000000000000000;
      patterns[7] = 144'b00010010001101000101011001111000_00010010001101000101011001111000_00000000000000000000000000000000_10010110_1101_01_0_0_00000000000000000000000000000000;
      patterns[8] = 144'b00000000000000000000000000000000_00000000000000000000000000000001_00000000000000000000000000000000_10010110_1101_01_0_0_11111111111111111111111111111111;
      patterns[9] = 144'b00000000000000000000000000000010_00000000000000000000000000000001_00000000000000000000000000000000_10010110_1101_01_0_0_00000000000000000000000000000001;
      patterns[10] = 144'b10000000000000000000000000000000_00000000000000000000000000000001_00000000000000000000000000000000_10010110_1101_01_0_0_01111111111111111111111111111111;
      patterns[11] = 144'b01111111111111111111111111111111_11111111111111111111111111111111_00000000000000000000000000000000_10010110_1101_01_0_0_10000000000000000000000000000000;

      for (i = 0; i < 12; i = i + 1)
      begin
        A = patterns[i][143:112];
        B = patterns[i][111:80];
        C = patterns[i][79:48];
        Opcode = patterns[i][47:40];
        control = patterns[i][39:36];
        csel = patterns[i][35:34];
        CLK = patterns[i][33];
        FLAG_WE = patterns[i][32];
        #10;
        if (patterns[i][31:0] !== 32'hx)
        begin
          if (Out !== patterns[i][31:0])
          begin
            $display("%d:Out: (assertion error). Expected %h, found %h", i, patterns[i][31:0], Out);
            $finish;
          end
        end
      end

      $display("All tests passed.");
    end
    endmodule
