tmarhguy/tomato/hardware/fpga/core/tb/os_tb.v

/*
 * Tomato — Tomato OS end-to-end testbench
 *
 * Engineer : Tyrone Marhguy
 * Project  : Tomato 32-bit CPU
 * File     : tb/os_tb.v
 * Target   : simulation (cwd = hardware/fpga/core)
 *
 * Copyright (c) 2025-2026 Tyrone Marhguy
 * SPDX-License-Identifier: Apache-2.0 WITH SHL-2.1
 *
 * Boots the OS image, feeds it keystrokes through the keyboard MMIO exactly
 * the way rtl/board/keypad.v does, and prints the framebuffer as text. A
 * monitor cannot tell you why a screen is wrong; this can, before the bitstream
 * is ever built.
 *
 *   +PROG=<name>   image under tb/mem  (default tomato_os)
 *   +KEYS=<hex>    keystrokes to send, e.g. 1f1f0d for down,down,enter
 *   +SETTLE=<n>    cycles to run between keys (default 400000)
 *   +DUMP=1        print the framebuffer after each key
 */
`timescale 1ns/1ps
module os_tb;
    reg clk = 0;
    reg reset = 1;
    reg  [7:0]  kb_data = 8'h00;
    reg         kb_ready = 1'b0;
    wire [7:0]  io_out;
    wire [31:0] disp_value;
    wire        kb_rd, halted;
    reg  [12:0] tile_raddr = 13'd0;
    wire [31:0] tile_rdata;

    always #5 clk = ~clk;

    main #(.CPU_HZ(1000000)) uut (
        .clk(clk), .reset(reset),
        .kb_data(kb_data), .kb_ready(kb_ready), .kb_rd(kb_rd),
        .io_out(io_out), .disp_value(disp_value), .halted(halted),
        .tile_rclk(clk), .tile_raddr(tile_raddr), .tile_rdata(tile_rdata),
        .ble_rdata(32'd0)
    );

    // Same handshake as the keypad: the key clears when the CPU reads it.
    always @(posedge clk) if (kb_rd) kb_ready <= 1'b0;

    task tick; begin @(posedge clk); #1; end endtask

    task press;
        input [7:0] code;
        integer guard;
        begin
            kb_data  = code;
            kb_ready = 1'b1;
            guard = 0;
            while (kb_ready && guard < 200000) begin
                tick;
                guard = guard + 1;
            end
            if (kb_ready) begin
                $display("FAIL: key %02h never consumed (CPU not polling)", code);
                $finish(1);
            end
        end
    endtask

    // ---- framebuffer → text ------------------------------------------------
    integer x, y;
    reg [31:0] fb_word;
    
    reg [8*80-1:0] line;

    function [7:0] printable;
        input [31:0] word;
        begin
            if (word[15:8] == 8'h00)
                printable = (word[3:0] == 4'h0) ? 8'h20 : 8'h23;   // blank / '#'
            else if (word[7:0] >= 8'h20 && word[7:0] < 8'h7F)
                printable = word[7:0];
            else if (word[7:0] == 8'h00)
                printable = 8'h20;
            else
                printable = 8'h2E;                                  // '.'
        end
    endfunction

    task dump_screen;
        begin
            $display("+------------------------------------------------------------------------------+");
            for (y = 0; y < 60; y = y + 1) begin
                line = 0;
                for (x = 0; x < 80; x = x + 1) begin
                    fb_word = {uut.vga0.hi[y * 80 + x], uut.vga0.lo[y * 80 + x]};
                    line = {line[8*79-1:0], printable(fb_word)};
                end
                $display("|%0s|", line);
            end
            $display("+------------------------------------------------------------------------------+");
        end
    endtask

    // Count non-blank cells so the test can assert something actually drew.
    function integer painted;
        input dummy;
        integer i, n;
        begin
            n = 0;
            for (i = 0; i < 4800; i = i + 1)
                if ({uut.vga0.hi[i], uut.vga0.lo[i]} != 32'h0) n = n + 1;
            painted = n;
        end
    endfunction

    integer k, nkeys, settle, want_dump, drawn, frame_fd, frame_i;
    reg [1023:0] frame_path;
    reg [8*64-1:0] prog;
    reg [1023:0]   path;
    reg [8*32-1:0] keys_arg;
    reg [7:0]      keys [0:31];

    // Parse an ASCII hex string of keycodes into a byte list.
    task parse_keys;
        input [8*32-1:0] s;
        integer i, n, hi_nib;
        reg [7:0] c;
        begin
            // $value$plusargs right-justifies, so walk down from the top byte
            // and take the non-NUL hex digits in order, two per keycode.
            n = 0;
            nkeys = 0;
            hi_nib = 0;
            for (i = 31; i >= 0; i = i - 1) begin
                c = s[i*8 +: 8];
                if (c != 8'h00) begin
                    if (n[0] == 0) hi_nib = hex_val(c);
                    else begin
                        keys[nkeys] = (hi_nib << 4) | hex_val(c);
                        nkeys = nkeys + 1;
                    end
                    n = n + 1;
                end
            end
        end
    endtask

    function integer hex_val;
        input [7:0] c;
        begin
            if (c >= "0" && c <= "9")      hex_val = c - "0";
            else if (c >= "a" && c <= "f") hex_val = c - "a" + 10;
            else if (c >= "A" && c <= "F") hex_val = c - "A" + 10;
            else                           hex_val = 0;
        end
    endfunction

    initial begin
        prog     = "tomato_os";
        keys_arg = "";
        settle   = 400000;
        want_dump = 0;
        nkeys = 0;

        if ($value$plusargs("PROG=%s", prog)) begin end
        if ($value$plusargs("SETTLE=%d", settle)) begin end
        if ($value$plusargs("DUMP=%d", want_dump)) begin end
        if ($value$plusargs("KEYS=%s", keys_arg)) parse_keys(keys_arg);

        for (k = 0; k < 256; k = k + 1) uut.regs0.mem[k] = 32'h0;
        uut.regs0.bank = 3'd0;
        for (k = 0; k < 16384; k = k + 1) uut.dmem[k] = 32'h0;
        for (k = 0; k < 8192; k = k + 1) begin
            uut.vga0.lo[k] = 16'h0;
            uut.vga0.hi[k] = 16'h0;
        end

        $sformat(path, "tb/mem/%0s.mem", prog);
        $readmemh(path, uut.dmem);
        uut.dmem[14'h0E03] = 32'd1;     // tune_boot: skip the splash delay

        tick; tick;
        reset = 0;

        // Let the first screen paint (splash + desktop).
        for (k = 0; k < settle; k = k + 1) tick;

        drawn = painted(1'b0);
        if (drawn < 300) begin
            $display("FAIL: only %0d cells painted after boot — no GUI on screen", drawn);
            dump_screen;
            $finish(1);
        end
        // Native launcher and bitmap/large-type attributes.
        if (uut.vga0.lo[15*80+9][7:0] !== "S" ||
            uut.vga0.lo[30*80+9][7:0] !== "S" ||
            uut.vga0.lo[33*80+9][7:0] !== "T" ||
            uut.vga0.lo[42*80+9][7:0] !== "S" ||
            uut.vga0.lo[45*80+9][7:0] !== "A" ||
            uut.vga0.hi[5*80+4][4:0] !== 5'b00111)
            $fatal(1, "workspace apps or large glass heading missing");
        $display("boot: %0d cells painted", drawn);
        if (want_dump) dump_screen;
        if (!$test$plusargs("NO_NAV_CHECK")) begin
        press(8'h1E); repeat (settle) tick;
        if (uut.regs0.mem[20] !== 13 || uut.vga0.lo[54*80+9][7:0] !== "E")
            $fatal(1,"Envelop missing at end of launcher");
        press(8'h10); repeat (settle) tick;
        // Envelop Lite landmarks match the firmware UI test (envelop_tb):
        // title at (2,2), CONTACTS header at (2,7).
        if (uut.vga0.lo[2*80+2][7:0] !== "E" ||
            uut.vga0.lo[7*80+2][7:0] !== "C")
            $fatal(1,"Envelop Lite screen missing");
        press(8'h11); repeat (settle) tick;
        press(8'h1E); repeat (settle) tick;
        if (uut.regs0.mem[20] !== 12 || uut.vga0.lo[51*80+9][7:0] !== "C")
            $fatal(1,"Compiler missing before Envelop");
        press(8'h1E); repeat (settle) tick;
        if (uut.regs0.mem[20] !== 11 || uut.vga0.lo[48*80+9][7:0] !== "R")
            $fatal(1,"Racer missing before Compiler");
        press(8'h1E); repeat (settle) tick;
        if (uut.regs0.mem[20] !== 10 ||
            uut.vga0.lo[45*80+9][15:8] !== 8'hf0 ||
            uut.vga0.lo[45*80+39][7:0] !== "A")
            $fatal(1, "focus wrap/preview mismatch");
        press(8'h10); repeat (settle) tick;
        // ALU Studio opens from RIGHT; wallpaper bit stays set under the UI.
        if (uut.vga0.lo[9*80+8][7:0] !== "A" || uut.vga0.hi[20*80+40][0] !== 1'b1)
            $fatal(1, "RIGHT ALU Studio title=%h background=%h PC=%h", uut.vga0.lo[9*80+8], uut.vga0.hi[20*80+40], uut.pc0.pc);
        press(8'h11); repeat (settle) tick;
        if (uut.regs0.mem[20] !== 10 || uut.vga0.lo[45*80+39][7:0] !== "A")
            $fatal(1, "return failed to retain focus");
        press(8'h1F); repeat (settle) tick;
        press(8'h1F); repeat (settle) tick;
        press(8'h1F); repeat (settle) tick;
        press(8'h1F); repeat (settle) tick;
        if (uut.regs0.mem[20] !== 0 ||
            uut.vga0.lo[15*80+9][15:8] !== 8'hf0 ||
            uut.vga0.lo[45*80+9][15:8] !== 8'h0f ||
            uut.vga0.lo[45*80+39][7:0] !== "S")
            $fatal(1, "down wrap left stale selection/preview");
        $display("workspace: bitmap, typography, wrap, ALU Studio, return pass");

        end

        for (k = 0; k < nkeys; k = k + 1) begin
            press(keys[k]);
            for (x = 0; x < settle; x = x + 1) tick;
            $display("after key %02h: %0d cells painted", keys[k], painted(1'b0));
            if (want_dump) dump_screen;
        end

        if (halted) begin
            $display("FAIL: OS halted — the shell should never stop");
            $finish(1);
        end

        // Exact tile dump for the host renderer; no approximated mockup.
        if ($value$plusargs("FRAME=%s", frame_path)) begin
            frame_fd = $fopen(frame_path, "w");
            if (!frame_fd) $fatal(1, "cannot write FRAME");
            for (frame_i = 0; frame_i < 4800; frame_i = frame_i + 1)
                $fdisplay(frame_fd, "%08h", {uut.vga0.hi[frame_i], uut.vga0.lo[frame_i]});
            $fclose(frame_fd);
        end
        $display("PASS: tomato_os");
        $finish;
    end
endmodule
