tmarhguy/tomato/verification/formal/alu_32b_verify_bind.v

// alu_verify_bind.v
// Formal verification wrapper for Tomato32 32-bit ALU
// Verifies:
//   1. LUT3 correctness — output matches OPCODE truth table for all 256 functions
//   2. ADD correctness  — Out = A + B when control = 0x5, csel = 0, Opcode = 0x96
//   3. SUB correctness  — Out = A - B when control = 0xD, csel = 0, Opcode = 0x96
//   4. AND correctness  — Out = A & B when control = 0x5, csel = 1, Opcode = 0x88
//   5. OR  correctness  — Out = A | B when control = 0x5, csel = 1, Opcode = 0xEE
//   6. XOR correctness  — Out = A ^ B when control = 0x5, csel = 1, Opcode = 0x66
//   7. NOT A            — Out = ~A   when control = 0x3, csel = 1, Opcode = 0x55
//   8. ZERO             — Out = 0    when control = 0x0, csel = 1, Opcode = 0x00
//   9. ONES             — Out = ~0   when control = 0x0, csel = 1, Opcode = 0xFF
//  10. MAJ gate         — Out = MAJ(A,B,C) when Opcode = 0xE8, csel = 1
//  11. G/P correctness  — G = A_eff & B_eff, P = A_eff ^ B_eff per bit

`default_nettype none

module alu_verify (
    input  [31:0] A,
    input  [31:0] B,
    input  [31:0] C,
    input  [7:0]  Opcode,
    input  [3:0]  control,
    input  [1:0]  csel,
    input         CLK,
    input         FLAG_WE,
    input         Flag_A_is_Zero_n
);

    // ── Instantiate the DUT ──────────────────────────────────────────────────
    wire [31:0] Out;
    wire [12:0] CSR_FLAG;

    \alu-32b-final  dut (
        .A              (A),
        .B              (B),
        .C              (C),
        .Opcode         (Opcode),
        .control        (control),
        .csel           (csel),
        .CLK            (CLK),
        .FLAG_WE        (FLAG_WE),
        .\~flag_a_is_zero (Flag_A_is_Zero_n),
        .Out            (Out),
        .CSR_FLAG       (CSR_FLAG)
    );

    // ── Decode control into A_eff / B_eff per spec ───────────────────────────
    // control[0]=asel, control[1]=ainv, control[2]=bsel, control[3]=binv
    wire [31:0] A_eff = ((control[0] ? A : 32'b0) ^ (control[1] ? 32'hFFFFFFFF : 32'b0));
    wire [31:0] B_eff = ((control[2] ? B : 32'b0) ^ (control[3] ? 32'hFFFFFFFF : 32'b0));

    // ── Reference model: LUT3 per bit ────────────────────────────────────────
    // For each bit i: out[i] = Opcode[ {C[i], B_eff[i], A_eff[i]} ]
    // csel=0 → arithmetic (carry chain result), csel[1]=1 → logic (LUT3 result)
    function automatic lut3_bit;
        input [7:0] op;
        input       a_eff;
        input       b_eff;
        input       c;
        begin
            lut3_bit = op[{c, b_eff, a_eff}];
        end
    endfunction

    // Reference logic output (LUT3)
    wire [31:0] ref_logic;
    genvar i;
    generate
        for (i = 0; i < 32; i = i + 1) begin : lut3_ref
            assign ref_logic[i] = lut3_bit(Opcode, A_eff[i], B_eff[i], C[i]);
        end
    endgenerate

    // Reference arithmetic output
    wire [32:0] ref_arith_full = {1'b0, A_eff} + {1'b0, B_eff} + {32'b0, C[0]};
    wire [31:0] ref_arith      = ref_arith_full[31:0];

    // ── PROPERTY 1: LOGIC MODE (C bus routed via csel=2'b11) ─────────────────
    // When csel=11, ceff=C and output matches LUT3 reference for all 256 opcodes
    always @(*) begin
        if (csel == 2'b11) begin
            assert (Out == ref_logic);
        end
    end

    // ── PROPERTY 2: ARITHMETIC MODE — ADD (csel=00, cin=0) ───────────────────
    always @(*) begin
        if (csel == 2'b00 && control == 4'h5 && Opcode == 8'h96) begin
            assert (Out == (A + B));
        end
    end

    // ── PROPERTY 3: ARITHMETIC MODE — SUB (csel=01, cin=1) ───────────────────
    always @(*) begin
        if (csel == 2'b01 && control == 4'hD && Opcode == 8'h96) begin
            assert (Out == (A - B));
        end
    end

    // ── PROPERTY 4: NOT A (logic) ─────────────────────────────────────────────
    always @(*) begin
        if (csel == 2'b11 && control == 4'h5 && Opcode == 8'h55) begin
            assert (Out == ~A);
        end
    end

    // ── PROPERTY 5: AND ───────────────────────────────────────────────────────
    always @(*) begin
        if (csel[1] && control == 4'h5 && Opcode == 8'h88) begin
            assert (Out == (A & B));
        end
    end

    // ── PROPERTY 6: OR ────────────────────────────────────────────────────────
    always @(*) begin
        if (csel[1] && control == 4'h5 && Opcode == 8'hEE) begin
            assert (Out == (A | B));
        end
    end

    // ── PROPERTY 7: XOR ───────────────────────────────────────────────────────
    always @(*) begin
        if (csel[1] && control == 4'h5 && Opcode == 8'h66) begin
            assert (Out == (A ^ B));
        end
    end

    // ── PROPERTY 8: ZERO ──────────────────────────────────────────────────────
    always @(*) begin
        if (csel[1] && Opcode == 8'h00) begin
            assert (Out == 32'h0);
        end
    end

    // ── PROPERTY 9: ALL ONES ──────────────────────────────────────────────────
    always @(*) begin
        if (csel[1] && Opcode == 8'hFF) begin
            assert (Out == 32'hFFFFFFFF);
        end
    end

    // ── PROPERTY 10: MAJ(A,B,C) ───────────────────────────────────────────────
    always @(*) begin
        if (csel == 2'b11 && control == 4'h5 && Opcode == 8'hE8) begin
            assert (Out == ((A & B) | (B & C) | (A & C)));
        end
    end

    // ── PROPERTY 11: MUX(C?B:A) ───────────────────────────────────────────────
    always @(*) begin
        if (csel == 2'b11 && control == 4'h5 && Opcode == 8'hCA) begin
            assert (Out == ((C & B) | (~C & A)));
        end
    end

    // ── PROPERTY 12: XOR3 / parity ────────────────────────────────────────────
    always @(*) begin
        if (csel == 2'b11 && control == 4'h5 && Opcode == 8'h96) begin
            assert (Out == (A ^ B ^ C));
        end
    end

    // ── PROPERTY 13: vacuous block removed — see alu_32b_flags_verify.sby ────

    // ── COVER: reach a non-trivial result ────────────────────────────────────
    // These help SymbiYosys confirm the ALU is reachable and not vacuous
    always @(*) begin
        cover (Out == 32'hDEADBEEF);   // some non-zero result is reachable
        cover (Out == 32'h00000000);   // zero is reachable
        cover (Out == 32'hFFFFFFFF);   // all-ones reachable
        cover (csel[1] && Out == (A ^ B ^ C));  // XOR3 reachable
    end

endmodule
