tmarhguy/tomato/verification/directed/alu-32b-final_Exhaustive 91 Ops Test_tb.v

//  A testbench for alu-32b-final_Exhaustive 91 Ops Test_tb
`timescale 1us/1ns

module alu-32b-final_Exhaustive 91 Ops Test_tb;
    reg [31:0] A;
    reg [31:0] B;
    reg [7:0] Opcode;
    reg [3:0] control;
    reg [31:0] C;
    reg [1:0] csel;
    reg CLK;
    reg FLAG_WE;
    reg \~flag_a_is_zero ;
    wire [31:0] Out;
    wire [12:0] CSR_FLAG;

  \alu-32b-final  \alu-32b-final 0 (
    .A(A),
    .B(B),
    .Opcode(Opcode),
    .control(control),
    .C(C),
    .csel(csel),
    .CLK(CLK),
    .FLAG_WE(FLAG_WE),
    .\~flag_a_is_zero (\~flag_a_is_zero ),
    .Out(Out),
    .CSR_FLAG(CSR_FLAG)
  );

    reg [143:0] patterns[0:454];
    integer i;

    initial begin
      patterns[0] = 144'b10100111100000111010011110100110_01001101101100001100001011111010_01000100110111110101001001000010_10010110_0101_10_0_0_11110101001101000110101010100000;
      patterns[1] = 144'b00100101101010110110000110101001_00011110110011111111010001101001_10010110110101101010110000101011_10010110_0101_10_0_0_01000100011110110101011000010010;
      patterns[2] = 144'b00100011000010000010010100111101_01101011001011110011011101111000_00010011101110100100011111111011_10010110_0101_10_0_0_10001110001101110101110010110101;
      patterns[3] = 144'b00100100010001110101001010000110_10010000111110111000011100011101_01111010100111001010011101101101_10010110_0101_10_0_0_10110101010000101101100110100011;
      patterns[4] = 144'b10110111110110110100001000110100_01011010010101001001001011001100_01010110101110011011011001001100_10010110_0101_10_0_0_00010010001011111101010100000000;
      patterns[5] = 144'b00111001101110010101110011101010_00110101001011011111010100110001_11111000101011100011101101001001_10010110_0101_01_0_0_01101110111001110101001000011100;
      patterns[6] = 144'b10111000110111110010111001101110_10111011100001101110101101100111_11001111000011100110100000111010_10010110_0101_01_0_0_01110100011001100001100111010110;
      patterns[7] = 144'b11000110001100110110010011110000_10110111111000101100000110110000_11011001101100110011001001001000_10010110_0101_01_0_0_01111110000101100010011010100001;
      patterns[8] = 144'b10100011000110111001101101111101_11110110110011010000010110100111_00110101000110101000010111001101_10010110_0101_01_0_0_10011001111010001010000100100101;
      patterns[9] = 144'b11000111111001100000010010111010_00111101011100001011011101010001_10100111110010111000111110101001_10010110_0101_01_0_0_00000101010101101011110000001100;
      patterns[10] = 144'b10100100110110101100000101111100_11100100100111110010001100001111_11111111111111111111111111111111_10010110_0001_01_0_0_10100100110110101100000101111101;
      patterns[11] = 144'b01010101000001110001000111101010_00000011001010111010110100111010_00101011111010001110100101001011_10010110_0001_01_0_0_01010101000001110001000111101011;
      patterns[12] = 144'b11001010101111011001011010110111_11110000010011000111110100100110_01010110010101100001010100110011_10010110_0001_01_0_0_11001010101111011001011010111000;
      patterns[13] = 144'b10000010010011000001101111010100_11100111000100011101001001000110_10100111010011001011001110011110_10010110_0001_01_0_0_10000010010011000001101111010101;
      patterns[14] = 144'b00000011011101111010111000111001_01101100000011110111001101000100_11000000011010111010010010101100_10010110_0001_01_0_0_00000011011101111010111000111010;
      patterns[15] = 144'b11001001100001111110100000111001_01000111011000001101110010100101_11111111001001101100000100111001_10010110_0100_01_0_0_01000111011000001101110010100110;
      patterns[16] = 144'b11010101110110000101011110011110_10111111110100010011000010000001_00001010111001011011011110010011_10010110_0100_01_0_0_10111111110100010011000010000010;
      patterns[17] = 144'b00110111110001100111100010000110_01100101101001011111111010011111_11110101001000011000111100101001_10010110_0100_01_0_0_01100101101001011111111010100000;
      patterns[18] = 144'b10001000001001111110000110100111_00110001100000001111101011100100_01001100100000001000011111001100_10010110_0100_01_0_0_00110001100000001111101011100101;
      patterns[19] = 144'b00000011111000101010101111000110_00100010000101011100010111011011_01111001001011101111100100000000_10010110_0100_01_0_0_00100010000101011100010111011100;
      patterns[20] = 144'b10011001110111000010011111010101_10001010001001000010001110111001_01010110110001010011111001111111_10010110_1001_00_0_0_10011001110111000010011111010100;
      patterns[21] = 144'b00110110110101010011010110110011_00001100111110110110101001110100_11100101110001011110100100101011_10010110_1001_00_0_0_00110110110101010011010110110010;
      patterns[22] = 144'b10011000100101011000010000010111_10100011000101000101100110011011_00010101011111111110100001001110_10010110_1001_00_0_0_10011000100101011000010000010110;
      patterns[23] = 144'b11010000000001111010111011000000_01100101001001011000111110101011_00101101111000111011110010100001_10010110_1001_00_0_0_11010000000001111010111010111111;
      patterns[24] = 144'b00011001010000001101110111100100_01010110001111110100111110011100_10011000011111010101001111101011_10010110_1001_00_0_0_00011001010000001101110111100011;
      patterns[25] = 144'b01010010111111101011010011111010_10110001111111010110011010111101_11111111111111111111111111111111_10010110_0110_00_0_0_10110001111111010110011010111100;
      patterns[26] = 144'b01000100010001010000010101010010_00011100001011001111000100110100_10100001111110010010001011101111_10010110_0110_00_0_0_00011100001011001111000100110011;
      patterns[27] = 144'b11000110011000110001000011111100_11000101110100011001000101000100_01110011000000011110110010000011_10010110_0110_00_0_0_11000101110100011001000101000011;
      patterns[28] = 144'b11010100011001010011001011000000_01010110110100111110011011110000_01101011100000001101000010011111_10010110_0110_00_0_0_01010110110100111110011011101111;
      patterns[29] = 144'b11001100011111101110110011111101_01011011110001000011001111100001_01010111111101000111010100001110_10010110_0110_00_0_0_01011011110001000011001111100000;
      patterns[30] = 144'b01111010101100010111101101011010_00000101111100010111111000011000_01110001111101110110001110101101_10010110_0011_01_0_0_10000101010011101000010010100110;
      patterns[31] = 144'b00000101011011101100001000100111_00010001011101100110100100101011_00001100001100011000001100001100_10010110_0011_01_0_0_11111010100100010011110111011001;
      patterns[32] = 144'b00011000101110101000100100100111_11110001010110010100001000110010_10010111010111011010101010001111_10010110_0011_01_0_0_11100111010001010111011011011001;
      patterns[33] = 144'b00000101100000011111000100110111_00011011101010111110000010100111_10011000101001011101001111110111_10010110_0011_01_0_0_11111010011111100000111011001001;
      patterns[34] = 144'b01100100011011111011100110110100_11001101010110101100111100101100_10010010000010010100000110011111_10010110_0011_01_0_0_10011011100100000100011001001100;
      patterns[35] = 144'b01000101011011101110010010001100_00001000011111011110101111010111_10111100001111100001011101011010_10010110_1100_01_0_0_11110111100000100001010000101001;
      patterns[36] = 144'b11100000101000010110000111101100_11101101010111011111100011100011_10101100110100100000100011001111_10010110_1100_01_0_0_00010010101000100000011100011101;
      patterns[37] = 144'b01011111010010001010000100010110_11100111110000111101100001011011_00001111110001111001000101000111_10010110_1100_01_0_0_00011000001111000010011110100101;
      patterns[38] = 144'b10101101000001010001110111010011_10101000111110010011110010000111_10101110001110111111001100101001_10010110_1100_01_0_0_01010111000001101100001101111001;
      patterns[39] = 144'b11110110110100100000000000111011_00111011000101000100011110000010_00011010111010110100000110100100_10010110_1100_01_0_0_11000100111010111011100001111110;
      patterns[40] = 144'b01110001111011000011000111100010_11110010101110110010101110001111_11111111111111111111111111111111_10010110_0011_00_0_0_10001110000100111100111000011101;
      patterns[41] = 144'b10100110001111001110110110100110_11110111000100011111010010110101_10010001101101101001001110000110_10010110_0011_00_0_0_01011001110000110001001001011001;
      patterns[42] = 144'b11101000000011001010101100101011_00010101000110111100001111001001_01011110110000101010110011001111_10010110_0011_00_0_0_00010111111100110101010011010100;
      patterns[43] = 144'b01010111100111110001010111011111_11000010100000010000001100100101_10101110001000101111000010001001_10010110_0011_00_0_0_10101000011000001110101000100000;
      patterns[44] = 144'b10001101000101100100010000000000_00001111011000100100010010011011_01010111111101011110111100010000_10010110_0011_00_0_0_01110010111010011011101111111111;
      patterns[45] = 144'b10100110011100111111001111011000_11110111111100001011011100011110_10000101001011000101001101101101_10010110_1100_00_0_0_00001000000011110100100011100001;
      patterns[46] = 144'b11011100110111010001000101000110_00101010011001110010000011100101_11101101010011111110100001101100_10010110_1100_00_0_0_11010101100110001101111100011010;
      patterns[47] = 144'b10100110010011111010101000110101_10000010110101011001001100100001_11110010100011101110110010111011_10010110_1100_00_0_0_01111101001010100110110011011110;
      patterns[48] = 144'b10101001101100110110101101011011_11001011100101001011010010011010_01010000000100110110001111011001_10010110_1100_00_0_0_00110100011010110100101101100101;
      patterns[49] = 144'b11011111100000000111001000100010_00001101101101011111000010001101_10010011001101110110110111100110_10010110_1100_00_0_0_11110010010010100000111101110010;
      patterns[50] = 144'b11011011000100100010110101110001_00100111001100100100011110000011_01110100100101101110001100100010_10010110_0001_00_0_0_11011011000100100010110101110001;
      patterns[51] = 144'b01100110011101111001100011100010_00001011011011100001110011110011_00101101100110011100111110110101_10010110_0001_00_0_0_01100110011101111001100011100010;
      patterns[52] = 144'b10110111010010101100111111110110_10001011101000100010111101111010_00110110010101100010001000011011_10010110_0001_00_0_0_10110111010010101100111111110110;
      patterns[53] = 144'b10001110010100001110111111010001_10110101001111100011111010101111_00100000011001010000011100101001_10010110_0001_00_0_0_10001110010100001110111111010001;
      patterns[54] = 144'b00111111001110100011011010101011_01011000000001000001101110110100_11000000001110010000100001001100_10010110_0001_00_0_0_00111111001110100011011010101011;
      patterns[55] = 144'b11100111000100010110011001011100_11100010100001001000111101110011_11111111111111111111111111111111_10010110_0100_00_0_0_11100010100001001000111101110011;
      patterns[56] = 144'b01001111010001001101101011110110_01110011110110111000111001001110_00100010011100011100100000110001_10010110_0100_00_0_0_01110011110110111000111001001110;
      patterns[57] = 144'b10100100111100110100100000100001_10011111110010001100110110011000_00110101001101010001110100110110_10010110_0100_00_0_0_10011111110010001100110110011000;
      patterns[58] = 144'b01010011110000000010111101110100_10011100000010111111001011101001_00101011100001000100111111110101_10010110_0100_00_0_0_10011100000010111111001011101001;
      patterns[59] = 144'b01111100001101101110001011101111_10001000000011101101100110010011_10010010110011010001101011110111_10010110_0100_00_0_0_10001000000011101101100110010011;
      patterns[60] = 144'b10000011101000101110100010001001_11001000010011111011110011111101_00110011110011001001000111101110_10010110_0000_00_0_0_00000000000000000000000000000000;
      patterns[61] = 144'b01010010101111111001101101010011_11000101100101110111010110000110_10011010001101011001001011110000_10010110_0000_00_0_0_00000000000000000000000000000000;
      patterns[62] = 144'b10101101011100100101011111100001_00111111001100010111111011000001_10001110011010010111111100011010_10010110_0000_00_0_0_00000000000000000000000000000000;
      patterns[63] = 144'b11000111010101101010001101100001_11001000011000110011000100010110_01110111011110111010111110101000_10010110_0000_00_0_0_00000000000000000000000000000000;
      patterns[64] = 144'b01011100100011111110011101001011_01101010011000100101110100000010_00010011000010011101110100000100_10010110_0000_00_0_0_00000000000000000000000000000000;
      patterns[65] = 144'b00110100110001010110101110010010_00011001010101111001010110101000_11011001000000000011110100010011_10010110_0000_01_0_0_00000000000000000000000000000001;
      patterns[66] = 144'b00111011110110110101011011110101_10100101010101000111011111100000_10110010100100101100000000110110_10010110_0000_01_0_0_00000000000000000000000000000001;
      patterns[67] = 144'b11100010000001010100110001011010_10101001011010011001011010011110_10101011101010110100100101100111_10010110_0000_01_0_0_00000000000000000000000000000001;
      patterns[68] = 144'b10010000001001010010111000110000_10001010100111110100110100000011_00001111111110100011001000011110_10010110_0000_01_0_0_00000000000000000000000000000001;
      patterns[69] = 144'b10110111110110110101111100001010_00000010101101010110001000101000_10010011000011110001101011000101_10010110_0000_01_0_0_00000000000000000000000000000001;
      patterns[70] = 144'b01111001000010101110001010011101_00000010111010000011010100101101_11111111111111111111111111111111_10010110_1010_01_0_0_11111111111111111111111111111111;
      patterns[71] = 144'b10111000111110111010010000111000_11101110000011011101011100000110_01101110011100011000110010010000_10010110_1010_01_0_0_11111111111111111111111111111111;
      patterns[72] = 144'b10011000000000011111111110111011_01111111001001000111011001010101_00110000111110010001011011110010_10010110_1010_01_0_0_11111111111111111111111111111111;
      patterns[73] = 144'b11010001001111100011100110000110_00010011010000101101000111001110_01000000000010010100001010001011_10010110_1010_01_0_0_11111111111111111111111111111111;
      patterns[74] = 144'b00001110101100000101011000110111_10000111100110110110100001100010_01100001001011011100011010000100_10010110_1010_01_0_0_11111111111111111111111111111111;
      patterns[75] = 144'b00111100000011110110001000101101_10000010011110000111110100110010_01000110000100001001010000000101_10010110_1010_00_0_0_11111111111111111111111111111110;
      patterns[76] = 144'b01001101001000001101100001101010_00001011001000010100000010100100_11010000110101101010110001110111_10010110_1010_00_0_0_11111111111111111111111111111110;
      patterns[77] = 144'b11000101000101111000110111010001_01000100101010010100101000101110_01000110100011110101101010110100_10010110_1010_00_0_0_11111111111111111111111111111110;
      patterns[78] = 144'b10010110111110011011111101010001_01000101001110000001101100100100_11011001111110111100100000110101_10010110_1010_00_0_0_11111111111111111111111111111110;
      patterns[79] = 144'b01110010000001110100100100111000_01101010110111011111001100010100_00100000111110110001100011001010_10010110_1010_00_0_0_11111111111111111111111111111110;
      patterns[80] = 144'b10010101101100110101010010101000_11011001110110111111100001000100_10000000111000000110111001000010_10010110_0101_00_0_0_01101111100011110100110011101100;
      patterns[81] = 144'b01100010101110010110110111001100_10101100000101010000010111101111_10010100111110100110100100000010_10010110_0101_00_0_0_00001110110011100111001110111011;
      patterns[82] = 144'b01010011110101110010010011101001_10011101111000001000010011110100_00001111100100001010111011001001_10010110_0101_00_0_0_11110001101101111010100111011101;
      patterns[83] = 144'b01111010110101111001101110000010_00001010001111100110100010001001_00011010100111010111101111000111_10010110_0101_00_0_0_10000101000101100000010000001011;
      patterns[84] = 144'b11001000100111111101001111011011_10101010110000001111011001110111_10100011100100000010011001010000_10010110_0101_00_0_0_01110011011000001100101001010010;
      patterns[85] = 144'b11101101110110011000001101011001_10011011001110000000011001101010_11111111111111111111111111111111_10010110_0111_00_0_0_10101101010111101000001100010000;
      patterns[86] = 144'b01110011010011101000100001000110_01001111101101111011111111011011_00010111001101100001011000110001_10010110_0111_00_0_0_11011100011010010011011110010100;
      patterns[87] = 144'b10111100100111101001100100001011_00001110001101010110011000110110_10011100101001110110010010111010_10010110_0111_00_0_0_01010001100101101100110100101010;
      patterns[88] = 144'b10101010001010111001111011010010_00010011100001100011000010000110_11101101010010101001011101101001_10010110_0111_00_0_0_01101001010110101001000110110011;
      patterns[89] = 144'b01110001010101100111110000110010_00111001011011111111001000010001_11101001100101100110001000000101_10010110_0111_00_0_0_11001000000110010111010111011110;
      patterns[90] = 144'b00110111010000000011001011111100_00101111000100010010100011110100_00010001101100101010100110000100_10010110_0111_01_0_0_11110111110100001111010111111000;
      patterns[91] = 144'b11000111011000001000110111100000_11001000010011010100010000011000_01000001001110010001010100010100_10010110_0111_01_0_0_00000000111011001011011000111000;
      patterns[92] = 144'b00101000011110110011101110001011_01010010001100001100000100110000_10000111010011001100111011010011_10010110_0111_01_0_0_00101001101101011000010110100101;
      patterns[93] = 144'b00010100000000000111110001001010_10010010110101111111100011111111_01111100101010111110000101000010_10010110_0111_01_0_0_01111110110101110111110010110101;
      patterns[94] = 144'b10010101000100111110000011000111_01000011101111000011100001001111_10000010111010100110101111100100_10010110_0111_01_0_0_10101110101010000101011110001000;
      patterns[95] = 144'b10010101100001111000010100111111_10100010101001000001100111111101_10101110101010011001111001111000_10010110_1101_00_0_0_11110010111000110110101101000001;
      patterns[96] = 144'b01110010111010010011110101110110_01111010110000111000101000110011_00101111011001010001110010001010_10010110_1101_00_0_0_11111000001001011011001101000010;
      patterns[97] = 144'b10010011010011011101100101110100_10111000010111000000101010001011_11100100111110001111000101101110_10010110_1101_00_0_0_11011010111100011100111011101000;
      patterns[98] = 144'b11000111011110110000100010000110_00011011001001010000000010010101_10000011010111000001010010010000_10010110_1101_00_0_0_10101100010101100000011111110000;
      patterns[99] = 144'b10001100101001010100101011010101_01001100101100010100100111101100_01011100101010000100000110010110_10010110_1101_00_0_0_00111111111101000000000011101000;
      patterns[100] = 144'b10011010111110010101010110111010_00010011000111000111101111011010_11111111111111111111111111111111_10010110_1101_01_0_0_10000111110111001101100111100000;
      patterns[101] = 144'b10001000101011001101111111010011_11111100110100111000011010111111_01010010001111011011100001111001_10010110_1101_01_0_0_10001011110110010101100100010100;
      patterns[102] = 144'b11011010110111011100100101100100_11111100100001110101011011110000_00110001011010010101101011111011_10010110_1101_01_0_0_11011110010101100111001001110100;
      patterns[103] = 144'b01100100100101000111100100111000_11100100101110010001010010100011_10111100110110000110011101100000_10010110_1101_01_0_0_01111111110110110110010010010101;
      patterns[104] = 144'b01010111100010111100001001001011_00010011000000010000100000100010_00001000110000011011011000011110_10010110_1101_01_0_0_01000100100010101011101000101001;
      patterns[105] = 144'b00010010010010011001100011101010_11010001111101111111010100001001_00100011001011000001011101110000_10010110_1101_01_0_0_01000000010100011010001111100001;
      patterns[106] = 144'b00100110000101111111011011011010_00100100011001100011100001011110_01001001011000000000000110010101_10010110_1101_01_0_0_00000001101100011011111001111100;
      patterns[107] = 144'b00000101110110001110010100010101_10001111010001010110000101101100_01000000101010111110011100000101_10010110_1101_01_0_0_01110110100100111000001110101001;
      patterns[108] = 144'b11011111110001110101111110010110_01001111000001011110111000110101_10100111100000111100101111110000_10010110_1101_01_0_0_10010000110000010111000101100001;
      patterns[109] = 144'b01111000101011010110011110001001_11010111001110111100011000001010_10100011111100111110111001111111_10010110_1101_01_0_0_10100001011100011010000101111111;
      patterns[110] = 144'b11010001101000001101100110111100_10110011011011111001110101101101_10000111100000101101110110110110_01101001_0100_00_0_0_01001100100100000110001010010010;
      patterns[111] = 144'b11011110110000011011111010010100_00111010001110100101101010110100_00011101101111001100111100101011_01101001_0100_00_0_0_11000101110001011010010101001011;
      patterns[112] = 144'b00111010100101111001101110001100_10001001101100001110010111001010_00011000011110011001110101001000_01101001_0100_00_0_0_01110110010011110001101000110101;
      patterns[113] = 144'b01101111110111110001000100100111_00011010010001111111101100010101_10101001110100000000010010010001_01101001_0100_00_0_0_11100101101110000000010011101010;
      patterns[114] = 144'b00000000110010000011110101000000_10011000011011110000001110110001_00110100101001110011101110010111_01101001_0100_00_0_0_01100111100100001111110001001110;
      patterns[115] = 144'b00110110001011011110111110111111_11010111011101010000011101101101_11111111111111111111111111111111_01101001_0100_01_0_0_00101000100010101111100010010011;
      patterns[116] = 144'b10000001000100100010101010110011_00011100010100111110000100110000_00111011000101100010011000011010_01101001_0100_01_0_0_11100011101011000001111011010000;
      patterns[117] = 144'b10110011011000111000001010101110_01101011011100000111110010100010_10100100111001011001001011111000_01101001_0100_01_0_0_10010100100011111000001101011110;
      patterns[118] = 144'b00110100001111011101100111010010_01011110110111100011101010100100_00000000011111100101001110110110_01101001_0100_01_0_0_10100001001000011100010101011100;
      patterns[119] = 144'b01011000101100110111110000010101_11010111000000011011110010000010_00100001010111010011110011001100_01101001_0100_01_0_0_00101000111111100100001101111110;
      patterns[120] = 144'b11101010010110100110110110111101_11101111111111001010001001010010_11011100101100011101101010111111_01101001_0101_00_0_0_00001110111010010111000000110000;
      patterns[121] = 144'b10111010011000001000011111110100_01101010000100101110110010001001_00111010001111101000011110010111_01101001_0101_00_0_0_01110011100011101001110110000010;
      patterns[122] = 144'b10001001111110110101111111110111_10101001001000111111010110111000_00110100110100011100010100100010_01101001_0101_00_0_0_11100001011010011111111011010000;
      patterns[123] = 144'b10000001101010011000001111011000_10101010010111001000001011101101_10001110000011000101010111100010_01101001_0101_00_0_0_11010100000110110000001101011010;
      patterns[124] = 144'b00010101010111011110011110000101_10011101011110011010111101110010_11111110000000001011000010110110_01101001_0101_00_0_0_10011000011011001111100100001000;
      patterns[125] = 144'b10100010110000101111011111100010_01111001110011110011110101110110_01100111101110011101010010110001_01101001_0101_01_0_0_01100101011101100101111110101100;
      patterns[126] = 144'b11001011010001011000100011000111_01101101110010110000101010101111_01011100001111100001101001011000_01101001_0101_01_0_0_11101011111100111000111010011000;
      patterns[127] = 144'b01101111111001011010000100011001_10101001000001001101100011100001_00000111000100110100110101011110_01101001_0101_01_0_0_01001011001001111000011000001000;
      patterns[128] = 144'b10001011110000001111100000011010_11010011011100100011110111110011_11110010011001100110101000001010_01101001_0101_01_0_0_10101001110011010100101000111011;
      patterns[129] = 144'b11100111001001000100100010001111_01100110011100110100001010000001_01001110010111010100010101111011_01101001_0101_01_0_0_10000010111010010111011011110010;
      patterns[130] = 144'b10100101011101100100111000011110_01010000100011011000011101011000_11111111111111111111111111111111_01101001_1100_00_0_0_01010000100011011000011101011000;
      patterns[131] = 144'b00001111001110001010100110110100_00010001001110110110011101110010_10111100011101111101011100111111_01101001_1100_00_0_0_00010001001110110110011101110010;
      patterns[132] = 144'b10001111011111010000101111010000_01010101011101101110011010001100_10111100111011111101001101111011_01101001_1100_00_0_0_01010101011101101110011010001100;
      patterns[133] = 144'b00001111011101011100110111110001_00000010000011010100000010000100_10011000101110010101011001101111_01101001_1100_00_0_0_00000010000011010100000010000100;
      patterns[134] = 144'b00111010010001010000000110011100_11100111110011111110110001000110_11001110000010010100100000110100_01101001_1100_00_0_0_11100111110011111110110001000110;
      patterns[135] = 144'b00000000010111111101011011010011_00111110110111100111100001111010_11010111111000111001101100000111_01101001_1100_01_0_0_00111110110111100111100001111011;
      patterns[136] = 144'b10100000010101001000111101100001_00011111110010011000010111110000_11010000111101011100110100000011_01101001_1100_01_0_0_00011111110010011000010111110001;
      patterns[137] = 144'b01011100001111101101001111111101_01100010011001100110000111111101_01101110100011101100011000011100_01101001_1100_01_0_0_01100010011001100110000111111110;
      patterns[138] = 144'b00100111010110110101011110110101_10011011100010110000111010101011_10110001011001000111110111111000_01101001_1100_01_0_0_10011011100010110000111010101100;
      patterns[139] = 144'b00111001100010000001011001101000_10110001111010111100001111011101_10011100101000011010110011001011_01101001_1100_01_0_0_10110001111010111100001111011110;
      patterns[140] = 144'b11101100011111111001111100001110_01010101000010011010010000010010_00010101101111010101001011110010_10010110_1111_01_0_0_10111110011101101011110011011111;
      patterns[141] = 144'b00011001110000111101100001000100_10111010011001101110010111100100_10100010001110001011011110011010_10010110_1111_01_0_0_00101011110101010100000111010111;
      patterns[142] = 144'b10010000000010001001101010100000_00000100001100011100000111011011_10001000000001010001101011010101_10010110_1111_01_0_0_01101011110001011010001110000100;
      patterns[143] = 144'b10111101010111001011001011101101_10111000100011100111110110010010_01110110111000010001001111001010_10010110_1111_01_0_0_10001010000101001100111110000000;
      patterns[144] = 144'b11011101110101000001001001001111_00011100111000111001011000101111_11000111001001001000110011011011_10010110_1111_01_0_0_00000101010010000101011110000001;
      patterns[145] = 144'b01110101111000110100011111101111_11100000001100100110010110000001_11111111111111111111111111111111_10010110_1111_00_0_0_10101001111010100101001010001110;
      patterns[146] = 144'b11001100001001110110011011100110_00111011101011110011011100010011_00010110110010101000010110101010_10010110_1111_00_0_0_11111000001010010110001000000101;
      patterns[147] = 144'b01010111000010101111111001011010_10010001011110110110111011110001_10111100000111100010111000110010_10010110_1111_00_0_0_00010111011110011001001010110011;
      patterns[148] = 144'b00001010110101111011101101101101_01100011111011011111111101110101_11110100101101001011010101001100_10010110_1111_00_0_0_10010001001110100100010100011100;
      patterns[149] = 144'b01001001111011110101000000001101_01000100000001111001001000110100_00100111000000010100001011101100_10010110_1111_00_0_0_01110010000010010001110110111101;
      patterns[150] = 144'b10111110111101100001001100011110_10101101111001001101111000011111_11111111111111111111111111111111_00000000_0101_11_0_0_00000000000000000000000000000000;
      patterns[151] = 144'b01011010100001000100011100001110_01101100110001111001110011100111_11111111111111111111111111111111_00000000_0101_11_0_0_00000000000000000000000000000000;
      patterns[152] = 144'b00110101011101101010101110001111_10111111111101011110111011111001_11111111111111111111111111111111_00000000_0101_11_0_0_00000000000000000000000000000000;
      patterns[153] = 144'b00110111100111011011011111111001_00011001001001110111100001110111_11111111111111111111111111111111_00000000_0101_11_0_0_00000000000000000000000000000000;
      patterns[154] = 144'b00010010011100111001000010111001_00110001100001001000101100100101_11111111111111111111111111111111_00000000_0101_11_0_0_00000000000000000000000000000000;
      patterns[155] = 144'b00111000011011100111000000001110_00111000110111000001101000011011_11111111111111111111111111111111_11111111_0101_11_0_0_11111111111111111111111111111111;
      patterns[156] = 144'b01011111011001110110010010000001_10001010000011110001011001111010_11111111111111111111111111111111_11111111_0101_11_0_0_11111111111111111111111111111111;
      patterns[157] = 144'b11010011101101110100001000100000_10011001110110001101101000010100_11111111111111111111111111111111_11111111_0101_11_0_0_11111111111111111111111111111111;
      patterns[158] = 144'b00000001000111110101011010000101_11010101100001111010011101101000_11111111111111111111111111111111_11111111_0101_11_0_0_11111111111111111111111111111111;
      patterns[159] = 144'b00001100011011010111101111110111_10110001010111100101100011100001_11111111111111111111111111111111_11111111_0101_11_0_0_11111111111111111111111111111111;
      patterns[160] = 144'b00001011000000101000100101010000_01111111110011100010001001101101_11111111111111111111111111111111_10101010_0101_11_0_0_00001011000000101000100101010000;
      patterns[161] = 144'b10001101010010110011101011001011_00011101001111011111000100101110_11111111111111111111111111111111_10101010_0101_11_0_0_10001101010010110011101011001011;
      patterns[162] = 144'b11011001011110010010010110110100_11000110000010000111010001010111_11111111111111111111111111111111_10101010_0101_11_0_0_11011001011110010010010110110100;
      patterns[163] = 144'b11101001011111100010000100010001_01000101001000010110100111011100_11111111111111111111111111111111_10101010_0101_11_0_0_11101001011111100010000100010001;
      patterns[164] = 144'b11110001010010001100111101101111_11110111101101101001111110011011_11111111111111111111111111111111_10101010_0101_11_0_0_11110001010010001100111101101111;
      patterns[165] = 144'b01110011101101010111110111101011_00111011100011101111010100111010_11111111111111111111111111111111_01010101_0101_11_0_0_10001100010010101000001000010100;
      patterns[166] = 144'b10111110100110001011010011111000_01001110001000110000101011101110_11111111111111111111111111111111_01010101_0101_11_0_0_01000001011001110100101100000111;
      patterns[167] = 144'b11000001011001111100001001000001_00110110010111111011101010011011_11111111111111111111111111111111_01010101_0101_11_0_0_00111110100110000011110110111110;
      patterns[168] = 144'b01000101110111111100100011100001_11101101100111101111111001110100_11111111111111111111111111111111_01010101_0101_11_0_0_10111010001000000011011100011110;
      patterns[169] = 144'b01111011100001001011101111101100_00101110111101010011101000100001_11111111111111111111111111111111_01010101_0101_11_0_0_10000100011110110100010000010011;
      patterns[170] = 144'b10010001001011111000011111100001_10101110111101110111100110101000_11111111111111111111111111111111_11001100_0101_11_0_0_10101110111101110111100110101000;
      patterns[171] = 144'b10000001010011011000010110010101_11111101011111000100001000110000_11111111111111111111111111111111_11001100_0101_11_0_0_11111101011111000100001000110000;
      patterns[172] = 144'b01111000111001001010110101000010_01110001110110101011000010000011_11111111111111111111111111111111_11001100_0101_11_0_0_01110001110110101011000010000011;
      patterns[173] = 144'b00000110101111111010110111000010_00101000001001011100011101110100_11111111111111111111111111111111_11001100_0101_11_0_0_00101000001001011100011101110100;
      patterns[174] = 144'b10011010101001010011111101011010_00010111011011001001100100101011_11111111111111111111111111111111_11001100_0101_11_0_0_00010111011011001001100100101011;
      patterns[175] = 144'b11011111000110111100110101100010_10011100011000100111000111100111_11111111111111111111111111111111_00110011_0101_11_0_0_01100011100111011000111000011000;
      patterns[176] = 144'b01001001101111001110100001111001_01000001011000110000110011101010_11111111111111111111111111111111_00110011_0101_11_0_0_10111110100111001111001100010101;
      patterns[177] = 144'b10000010111110010100011000001001_01000000111111000110000110010000_11111111111111111111111111111111_00110011_0101_11_0_0_10111111000000111001111001101111;
      patterns[178] = 144'b10001100000000110011111101100111_00111110000001111100001100110011_11111111111111111111111111111111_00110011_0101_11_0_0_11000001111110000011110011001100;
      patterns[179] = 144'b00101001001100110000000000000110_00000100011010000001001011100101_11111111111111111111111111111111_00110011_0101_11_0_0_11111011100101111110110100011010;
      patterns[180] = 144'b01011111010010001010001001111000_00110110110011110111001001101100_11111111111111111111111111111111_11110000_0101_11_0_0_11111111111111111111111111111111;
      patterns[181] = 144'b00010111000011111011011010001010_01010000100100001011100001001001_11111111111111111111111111111111_11110000_0101_11_0_0_11111111111111111111111111111111;
      patterns[182] = 144'b11100101110011100110011000110100_01001011101101100100011101010111_11111111111111111111111111111111_11110000_0101_11_0_0_11111111111111111111111111111111;
      patterns[183] = 144'b11010101011101100101101001101010_00111001001111100101000100101101_11111111111111111111111111111111_11110000_0101_11_0_0_11111111111111111111111111111111;
      patterns[184] = 144'b10110110111101011011010101101110_00110100001011000010110010010010_11111111111111111111111111111111_11110000_0101_11_0_0_11111111111111111111111111111111;
      patterns[185] = 144'b10101010110110010000111000111100_00110011110111001010111011001011_11111111111111111111111111111111_00001111_0101_11_0_0_00000000000000000000000000000000;
      patterns[186] = 144'b00110101101000011110110001101110_01001100110011010010000111010100_11111111111111111111111111111111_00001111_0101_11_0_0_00000000000000000000000000000000;
      patterns[187] = 144'b01110101111111011010111110010100_00010111001111101000111011010110_11111111111111111111111111111111_00001111_0101_11_0_0_00000000000000000000000000000000;
      patterns[188] = 144'b10101100010001011110101010001101_11100011110000100101001011010110_11111111111111111111111111111111_00001111_0101_11_0_0_00000000000000000000000000000000;
      patterns[189] = 144'b11111111001101010000000101111111_11101101000100100010111100011001_11111111111111111111111111111111_00001111_0101_11_0_0_00000000000000000000000000000000;
      patterns[190] = 144'b01001100001111010110110100000000_11010111010011000011101110110011_11111111111111111111111111111111_10001000_0101_11_0_0_01000100000011000010100100000000;
      patterns[191] = 144'b11101001011110111001101010110111_01001110110010100101111000111101_11111111111111111111111111111111_10001000_0101_11_0_0_01001000010010100001101000110101;
      patterns[192] = 144'b00000111101011011000000111000111_10111101110010011001001101100000_11111111111111111111111111111111_10001000_0101_11_0_0_00000101100010011000000101000000;
      patterns[193] = 144'b01100001100011011101010101011001_11010010010110100101111001000101_11111111111111111111111111111111_10001000_0101_11_0_0_01000000000010000101010001000001;
      patterns[194] = 144'b11000100011001110001001001101101_10000110100011101010000011010110_11111111111111111111111111111111_10001000_0101_11_0_0_10000100000001100000000001000100;
      patterns[195] = 144'b10001010110100101101011110011100_10001110111110001111010000001001_11111111111111111111111111111111_11101110_0101_11_0_0_10001110111110101111011110011101;
      patterns[196] = 144'b01011110010110001000001111000111_00011001011100011100010110101010_11111111111111111111111111111111_11101110_0101_11_0_0_01011111011110011100011111101111;
      patterns[197] = 144'b01001001110101001011111010001001_00110110001110101110010011010000_11111111111111111111111111111111_11101110_0101_11_0_0_01111111111111101111111011011001;
      patterns[198] = 144'b11010101011101011011001111110101_00001000101001110100100001001100_11111111111111111111111111111111_11101110_0101_11_0_0_11011101111101111111101111111101;
      patterns[199] = 144'b10110110110001011011111101000011_00000011111111011100010010110001_11111111111111111111111111111111_11101110_0101_11_0_0_10110111111111011111111111110011;
      patterns[200] = 144'b11000110000111001101011010000001_00000001100001110110100110010110_11111111111111111111111111111111_01110111_0101_11_0_0_11111111111110111011111101111111;
      patterns[201] = 144'b11111101100011000000110000110011_10011111110110001011110010111100_11111111111111111111111111111111_01110111_0101_11_0_0_01100010011101111111001111001111;
      patterns[202] = 144'b00000110111010111011111000110100_11101110010000010011101000010101_11111111111111111111111111111111_01110111_0101_11_0_0_11111001101111101100010111101011;
      patterns[203] = 144'b01010010000011001101010000010111_00001001110100010001100011001110_11111111111111111111111111111111_01110111_0101_11_0_0_11111111111111111110111111111001;
      patterns[204] = 144'b01000111010110101011000100000111_00111100110111000011010101110101_11111111111111111111111111111111_01110111_0101_11_0_0_11111011101001111100111011111010;
      patterns[205] = 144'b01000110101010011101000111110001_00001010110010011101111010011111_11111111111111111111111111111111_00010001_0101_11_0_0_10110001000101100010000000000000;
      patterns[206] = 144'b11000011000001001100011011010010_10111011100000011110010100101010_11111111111111111111111111111111_00010001_0101_11_0_0_00000100011110100001100000000101;
      patterns[207] = 144'b11000010100110101101100100110111_00000011111101111100101101110010_11111111111111111111111111111111_00010001_0101_11_0_0_00111100000000000010010010001000;
      patterns[208] = 144'b00010101000111011011010001001011_00100111101101010011110110010001_11111111111111111111111111111111_00010001_0101_11_0_0_11001000010000100100001000100100;
      patterns[209] = 144'b01000100101011010000100001111111_00011101001010010000010110011101_11111111111111111111111111111111_00010001_0101_11_0_0_10100010010100101111001000000000;
      patterns[210] = 144'b00010111100011110110110010110011_00000010000111110111001011000010_11111111111111111111111111111111_01100110_0101_11_0_0_00010101100100000001111001110001;
      patterns[211] = 144'b11110100101101110101000010111010_00001010111101011110010100100100_11111111111111111111111111111111_01100110_0101_11_0_0_11111110010000101011010110011110;
      patterns[212] = 144'b00010110101011100000010001100001_00011111011000110110001100110001_11111111111111111111111111111111_01100110_0101_11_0_0_00001001110011010110011101010000;
      patterns[213] = 144'b00111110111011111100100001100101_01001111110111111010010110010011_11111111111111111111111111111111_01100110_0101_11_0_0_01110001001100000110110111110110;
      patterns[214] = 144'b00011011111100100010101100010101_11011001110100010100101101001101_11111111111111111111111111111111_01100110_0101_11_0_0_11000010001000110110000001011000;
      patterns[215] = 144'b01100001111111011100011011100011_01001000111001000101001011111011_11111111111111111111111111111111_10011001_0101_11_0_0_11010110111001100110101111100111;
      patterns[216] = 144'b11010010110010111001011011101010_01011001011100010001011100011011_11111111111111111111111111111111_10011001_0101_11_0_0_01110100010001010111111000001110;
      patterns[217] = 144'b00010000110111010101101000011100_11100000111011010101110100000100_11111111111111111111111111111111_10011001_0101_11_0_0_00001111110011111111100011100111;
      patterns[218] = 144'b01101000000111001001010110000111_00010100110011000111011100011011_11111111111111111111111111111111_10011001_0101_11_0_0_10000011001011110001110101100011;
      patterns[219] = 144'b00100000110111111010111001000101_01011001000100101110101101011110_11111111111111111111111111111111_10011001_0101_11_0_0_10000110001100101011101011100100;
      patterns[220] = 144'b10111011001110100111011110111100_00110011110111000110101010001111_11111111111111111111111111111111_10100000_0101_11_0_0_10111011001110100111011110111100;
      patterns[221] = 144'b11011100000100011100100010100110_00100010001010000101011111010101_11111111111111111111111111111111_10100000_0101_11_0_0_11011100000100011100100010100110;
      patterns[222] = 144'b10000001110001100100011100100111_00001101011010110001000101111011_11111111111111111111111111111111_10100000_0101_11_0_0_10000001110001100100011100100111;
      patterns[223] = 144'b00001000000100100001011101000001_00110111111000000000110110101111_11111111111111111111111111111111_10100000_0101_11_0_0_00001000000100100001011101000001;
      patterns[224] = 144'b01100111101010110110110110111011_11101111001110110010011000001011_11111111111111111111111111111111_10100000_0101_11_0_0_01100111101010110110110110111011;
      patterns[225] = 144'b10100100111001010000101101000111_00011111001011100000101010001110_11111111111111111111111111111111_11111010_0101_11_0_0_11111111111111111111111111111111;
      patterns[226] = 144'b11000010100100011100100110111010_11101000001110001000001110001000_11111111111111111111111111111111_11111010_0101_11_0_0_11111111111111111111111111111111;
      patterns[227] = 144'b00110001000100100001001100001101_11000010101000011101010111111100_11111111111111111111111111111111_11111010_0101_11_0_0_11111111111111111111111111111111;
      patterns[228] = 144'b00001100111111110100010001010100_01000011010001010001011010110010_11111111111111111111111111111111_11111010_0101_11_0_0_11111111111111111111111111111111;
      patterns[229] = 144'b11100110001111101001000110001100_10001000010000000010101100010000_11111111111111111111111111111111_11111010_0101_11_0_0_11111111111111111111111111111111;
      patterns[230] = 144'b11110101100111000000111110000101_10011000000000100111110111111101_11111111111111111111111111111111_01011111_0101_11_0_0_00001010011000111111000001111010;
      patterns[231] = 144'b01011000001011001010111010010101_00001111101100110111100010100100_11111111111111111111111111111111_01011111_0101_11_0_0_10100111110100110101000101101010;
      patterns[232] = 144'b00001101010101001011000010110100_01111011001000110111101101111111_11111111111111111111111111111111_01011111_0101_11_0_0_11110010101010110100111101001011;
      patterns[233] = 144'b10100010000000010111010010101110_01000010011001101111111111010110_11111111111111111111111111111111_01011111_0101_11_0_0_01011101111111101000101101010001;
      patterns[234] = 144'b01000000010111101101000011100001_11101101101100110100011011010111_11111111111111111111111111111111_01011111_0101_11_0_0_10111111101000010010111100011110;
      patterns[235] = 144'b11111111100011110011010110110000_00000100001001110100001010110010_11111111111111111111111111111111_00000101_0101_11_0_0_00000000000000000000000000000000;
      patterns[236] = 144'b10001010110110110010111110010101_11011001100100001101001011011101_11111111111111111111111111111111_00000101_0101_11_0_0_00000000000000000000000000000000;
      patterns[237] = 144'b00010111001001100101101011111001_10111101011001110111010110100011_11111111111111111111111111111111_00000101_0101_11_0_0_00000000000000000000000000000000;
      patterns[238] = 144'b00100111011111011010010110100111_11110000100100000101000101101000_11111111111111111111111111111111_00000101_0101_11_0_0_00000000000000000000000000000000;
      patterns[239] = 144'b01111011011100101100011001010000_01000110100110011010111010100100_11111111111111111111111111111111_00000101_0101_11_0_0_00000000000000000000000000000000;
      patterns[240] = 144'b11111010011010100011000001000010_00011000000110110101111001010111_11111111111111111111111111111111_01011010_0101_11_0_0_00000101100101011100111110111101;
      patterns[241] = 144'b01111001000110101010101001010010_01010010100001001110101001100101_11111111111111111111111111111111_01011010_0101_11_0_0_10000110111001010101010110101101;
      patterns[242] = 144'b10011101110110011001001111100001_11100000101100010001111110101001_11111111111111111111111111111111_01011010_0101_11_0_0_01100010001001100110110000011110;
      patterns[243] = 144'b01101000110101010110011011001111_01001011000000011000100110101100_11111111111111111111111111111111_01011010_0101_11_0_0_10010111001010101001100100110000;
      patterns[244] = 144'b10010110111111001101101100110010_00011000000000011101110110100111_11111111111111111111111111111111_01011010_0101_11_0_0_01101001000000110010010011001101;
      patterns[245] = 144'b11010011011001010100110110010111_01110111000110111001101000011011_11111111111111111111111111111111_10100101_0101_11_0_0_11010011011001010100110110010111;
      patterns[246] = 144'b01101101101110100111001001011001_00100011011100111000110000000111_11111111111111111111111111111111_10100101_0101_11_0_0_01101101101110100111001001011001;
      patterns[247] = 144'b10001111000011011000000000010101_11111101100000100100001101011011_11111111111111111111111111111111_10100101_0101_11_0_0_10001111000011011000000000010101;
      patterns[248] = 144'b11010001110010001010001001100010_10100110101001100101011111010110_11111111111111111111111111111111_10100101_0101_11_0_0_11010001110010001010001001100010;
      patterns[249] = 144'b00110100111100001011010110000110_01000011010001100101001110111110_11111111111111111111111111111111_10100101_0101_11_0_0_00110100111100001011010110000110;
      patterns[250] = 144'b00110101000001110010110001110111_10100111110110101010011101100000_11111111111111111111111111111111_11000000_0101_11_0_0_10100111110110101010011101100000;
      patterns[251] = 144'b10010111011101100101001111010001_10000001111101011000110011001100_11111111111111111111111111111111_11000000_0101_11_0_0_10000001111101011000110011001100;
      patterns[252] = 144'b11011011011111100111111010011101_01001011010001010101111010000100_11111111111111111111111111111111_11000000_0101_11_0_0_01001011010001010101111010000100;
      patterns[253] = 144'b11010000111011001111001101100101_10110011110010111010000011100000_11111111111111111111111111111111_11000000_0101_11_0_0_10110011110010111010000011100000;
      patterns[254] = 144'b10000110000011100100110010000011_00011000111001010001011110101011_11111111111111111111111111111111_11000000_0101_11_0_0_00011000111001010001011110101011;
      patterns[255] = 144'b00100111110000100001100011100110_11010001111010110011000010011001_11111111111111111111111111111111_11111100_0101_11_0_0_11111111111111111111111111111111;
      patterns[256] = 144'b10001101000111001000010100001100_10101001001101000111000110011100_11111111111111111111111111111111_11111100_0101_11_0_0_11111111111111111111111111111111;
      patterns[257] = 144'b00110001010000100011010111100111_10101011111111111111101010010101_11111111111111111111111111111111_11111100_0101_11_0_0_11111111111111111111111111111111;
      patterns[258] = 144'b01000010010100010110001100001101_00111100001001011011100010111100_11111111111111111111111111111111_11111100_0101_11_0_0_11111111111111111111111111111111;
      patterns[259] = 144'b10110000001111101101010111011111_10100001100111111110110011001111_11111111111111111111111111111111_11111100_0101_11_0_0_11111111111111111111111111111111;
      patterns[260] = 144'b11111000010111100110110111100001_10000011110010010100111011110100_11111111111111111111111111111111_00111111_0101_11_0_0_01111100001101101011000100001011;
      patterns[261] = 144'b01110011100010001000100011101001_00110010100111110001000001001001_11111111111111111111111111111111_00111111_0101_11_0_0_11001101011000001110111110110110;
      patterns[262] = 144'b00000111101110011011100110110010_01001001101000100010111001011010_11111111111111111111111111111111_00111111_0101_11_0_0_10110110010111011101000110100101;
      patterns[263] = 144'b00011001000110110111101000000100_11011110001001001111010110100001_11111111111111111111111111111111_00111111_0101_11_0_0_00100001110110110000101001011110;
      patterns[264] = 144'b01011101111000110101000010001000_00111010010011001101001110101001_11111111111111111111111111111111_00111111_0101_11_0_0_11000101101100110010110001010110;
      patterns[265] = 144'b00000000011000011000010111110110_00101100110011011001000101100000_11111111111111111111111111111111_00000011_0101_11_0_0_00000000000000000000000000000000;
      patterns[266] = 144'b01111011111000011011010110011101_01001000001111101011011101011111_11111111111111111111111111111111_00000011_0101_11_0_0_00000000000000000000000000000000;
      patterns[267] = 144'b11101110100110011111000101110111_01111111011101000010110101101011_11111111111111111111111111111111_00000011_0101_11_0_0_00000000000000000000000000000000;
      patterns[268] = 144'b00001001010011000101011000100100_00011101110100001001010110000001_11111111111111111111111111111111_00000011_0101_11_0_0_00000000000000000000000000000000;
      patterns[269] = 144'b00101001011100000011111010100011_11011110001101010101100100001101_11111111111111111111111111111111_00000011_0101_11_0_0_00000000000000000000000000000000;
      patterns[270] = 144'b00110000101100110000100010001101_11101010011010100101011100101011_11111111111111111111111111111111_00111100_0101_11_0_0_00010101100101011010100011010100;
      patterns[271] = 144'b11110111011010001000101110010000_10001011111100111100000101101100_11111111111111111111111111111111_00111100_0101_11_0_0_01110100000011000011111010010011;
      patterns[272] = 144'b11011111110111110000101110000010_00001000001101010011111111011010_11111111111111111111111111111111_00111100_0101_11_0_0_11110111110010101100000000100101;
      patterns[273] = 144'b10100000110011010111000111000000_11011101000111011111100111110110_11111111111111111111111111111111_00111100_0101_11_0_0_00100010111000100000011000001001;
      patterns[274] = 144'b00100000101001001001111000110101_11110011100110100100100000111111_11111111111111111111111111111111_00111100_0101_11_0_0_00001100011001011011011111000000;
      patterns[275] = 144'b10111001000110111001000100100110_10111010111010110110011110001011_11111111111111111111111111111111_11000011_0101_11_0_0_10111010111010110110011110001011;
      patterns[276] = 144'b00001110111110001000100001100000_00001011111110010101001011111101_11111111111111111111111111111111_11000011_0101_11_0_0_00001011111110010101001011111101;
      patterns[277] = 144'b10100110101101100010011100100101_10111011110110111011001001111110_11111111111111111111111111111111_11000011_0101_11_0_0_10111011110110111011001001111110;
      patterns[278] = 144'b10010101011000001111010100110001_11000000111100100101011001011100_11111111111111111111111111111111_11000011_0101_11_0_0_11000000111100100101011001011100;
      patterns[279] = 144'b00100000110001100100111111001110_10110011100100011010100011011101_11111111111111111111111111111111_11000011_0101_11_0_0_10110011100100011010100011011101;
      patterns[280] = 144'b00010110101100110111111100011000_11010000100100010110010001111100_11111111111111111111111111111111_00100010_0101_11_0_0_00000110001000100001101100000000;
      patterns[281] = 144'b10101000011010101111110011011000_01110010000101110100100011000100_11111111111111111111111111111111_00100010_0101_11_0_0_10001000011010001011010000011000;
      patterns[282] = 144'b01110110111010011111101110001100_01000000101001100000100000000111_11111111111111111111111111111111_00100010_0101_11_0_0_00110110010010011111001110001000;
      patterns[283] = 144'b11110110100111110111000100111001_00011010011111001011111111101111_11111111111111111111111111111111_00100010_0101_11_0_0_11100100100000110100000000010000;
      patterns[284] = 144'b11010100110010111010100010100110_10100101110100010110000111101100_11111111111111111111111111111111_00100010_0101_11_0_0_01010000000010101000100000000010;
      patterns[285] = 144'b10011000000000110000110111011000_10001110100001000011001110000000_11111111111111111111111111111111_01000100_0101_11_0_0_00000110100001000011001000000000;
      patterns[286] = 144'b11100110001011101111011110010010_01001100000101100110001011010010_11111111111111111111111111111111_01000100_0101_11_0_0_00001000000100000000000001000000;
      patterns[287] = 144'b00111001100100101011101100100111_11000010110110000000111101001011_11111111111111111111111111111111_01000100_0101_11_0_0_11000010010010000000010001001000;
      patterns[288] = 144'b10100001000101010011111101111101_00101000000011010100011010001010_11111111111111111111111111111111_01000100_0101_11_0_0_00001000000010000100000010000010;
      patterns[289] = 144'b00101110111101110000100100001001_10110011000000000000111100100010_11111111111111111111111111111111_01000100_0101_11_0_0_10010001000000000000011000100010;
      patterns[290] = 144'b00101011010111001110000110011110_11110010110010001100000100110111_11111111111111111111111111111111_10111011_0101_11_0_0_00101111011111111111111111011110;
      patterns[291] = 144'b10110001000111011000010010001010_10101011000110010001000010100001_11111111111111111111111111111111_10111011_0101_11_0_0_11110101111111111110111111011110;
      patterns[292] = 144'b01001101100001010101110000001101_10000111011001100110110110110110_11111111111111111111111111111111_10111011_0101_11_0_0_01111101100111011101111001001101;
      patterns[293] = 144'b11101000010011000110011101011001_10001001111011001001101000001101_11111111111111111111111111111111_10111011_0101_11_0_0_11111110010111110110011111111011;
      patterns[294] = 144'b01100001101011101011111010011000_01100110110101110101000010010101_11111111111111111111111111111111_10111011_0101_11_0_0_11111001101011101011111111111010;
      patterns[295] = 144'b11101010011000010100010000110111_11101100000110110000111010101100_11111111111111111111111111111111_11011101_0101_11_0_0_11111101100111111011111111101100;
      patterns[296] = 144'b00011110011100110001000000001100_00001111110101000110011010110101_11111111111111111111111111111111_11011101_0101_11_0_0_11101111110111001110111111110111;
      patterns[297] = 144'b00011000111001110110101011100000_11111110100010011101011001110101_11111111111111111111111111111111_11011101_0101_11_0_0_11111111100110011101011101111111;
      patterns[298] = 144'b00100010000101100100000001101010_11001101110100101101011100001111_11111111111111111111111111111111_11011101_0101_11_0_0_11011101111110111111111110011111;
      patterns[299] = 144'b01011101000111010111100001100110_10100000010100011011000000000000_11111111111111111111111111111111_11011101_0101_11_0_0_10100010111100111011011110011001;
      patterns[300] = 144'b11101011010001110011100111010111_01111011000110001111100000001010_11111111111111111111111111111111_00001010_0101_11_0_0_00000000000000000000000000000000;
      patterns[301] = 144'b00111101001011110101110001111001_00011000000111011011010100110100_11111111111111111111111111111111_00001010_0101_11_0_0_00000000000000000000000000000000;
      patterns[302] = 144'b10001010101010110000101110100010_10101110011111001110010100110001_11111111111111111111111111111111_00001010_0101_11_0_0_00000000000000000000000000000000;
      patterns[303] = 144'b00111000110101001110001011001011_10000100101111011111101110010101_11111111111111111111111111111111_00001010_0101_11_0_0_00000000000000000000000000000000;
      patterns[304] = 144'b11110010010110000110110100100000_11001101011100101110011110010100_11111111111111111111111111111111_00001010_0101_11_0_0_00000000000000000000000000000000;
      patterns[305] = 144'b10111111000000101111010001001101_10111110010110001111011001011001_11111111111111111111111111111111_01010000_0101_11_0_0_01000000111111010000101110110010;
      patterns[306] = 144'b10001110010000010100110000110111_11100001001000101111001001000110_11111111111111111111111111111111_01010000_0101_11_0_0_01110001101111101011001111001000;
      patterns[307] = 144'b00110011000111001101010011100100_01101000111100010101110111110001_11111111111111111111111111111111_01010000_0101_11_0_0_11001100111000110010101100011011;
      patterns[308] = 144'b01011100111111110000101011101101_11110011110010111010010011110010_11111111111111111111111111111111_01010000_0101_11_0_0_10100011000000001111010100010010;
      patterns[309] = 144'b01000000100111000011100110100111_01001111010111110100001000110100_11111111111111111111111111111111_01010000_0101_11_0_0_10111111011000111100011001011000;
      patterns[310] = 144'b11111000100010000110010011010000_10100101111100111100110000010100_11111111111111111111111111111111_10101111_0101_11_0_0_11111000100010000110010011010000;
      patterns[311] = 144'b10001011010001000010010010000010_11111011111010110010110001101101_11111111111111111111111111111111_10101111_0101_11_0_0_10001011010001000010010010000010;
      patterns[312] = 144'b00010110110010100000001011000100_10100011001111110011110001011001_11111111111111111111111111111111_10101111_0101_11_0_0_00010110110010100000001011000100;
      patterns[313] = 144'b01001111011101001100010101001100_11000110000110000001000111000010_11111111111111111111111111111111_10101111_0101_11_0_0_01001111011101001100010101001100;
      patterns[314] = 144'b11111111101000000101110000100001_11001100010000111000110011111111_11111111111111111111111111111111_10101111_0101_11_0_0_11111111101000000101110000100001;
      patterns[315] = 144'b11111000111100110011111011001000_11101110101100000111001000001011_11111111111111111111111111111111_11110101_0101_11_0_0_11111111111111111111111111111111;
      patterns[316] = 144'b01011110010100011010110110010111_11111011001101001000110011011000_11111111111111111111111111111111_11110101_0101_11_0_0_11111111111111111111111111111111;
      patterns[317] = 144'b10000010111111010101111100101011_01001101000100000100011000011000_11111111111111111111111111111111_11110101_0101_11_0_0_11111111111111111111111111111111;
      patterns[318] = 144'b00010110001101011011011111101111_01111110000101110010001111111011_11111111111111111111111111111111_11110101_0101_11_0_0_11111111111111111111111111111111;
      patterns[319] = 144'b00000001101100100000010001100001_11001100100011111000010011110100_11111111111111111111111111111111_11110101_0101_11_0_0_11111111111111111111111111111111;
      patterns[320] = 144'b11001101110111010010001001110001_01010111101100011111110000000011_11111111111111111111111111111111_00001100_0101_11_0_0_00000000000000000000000000000000;
      patterns[321] = 144'b10000101000000110010001001110111_11000111101000110001110101010010_11111111111111111111111111111111_00001100_0101_11_0_0_00000000000000000000000000000000;
      patterns[322] = 144'b01011100101011111111111011110000_01001001010111001010101111110110_11111111111111111111111111111111_00001100_0101_11_0_0_00000000000000000000000000000000;
      patterns[323] = 144'b10101000001000100011100100100101_00011001110010011000101001010011_11111111111111111111111111111111_00001100_0101_11_0_0_00000000000000000000000000000000;
      patterns[324] = 144'b00001110100101010100110111101000_11100000101001110010100110101010_11111111111111111111111111111111_00001100_0101_11_0_0_00000000000000000000000000000000;
      patterns[325] = 144'b01101001010101110100011011000111_11011011110110111000000110001100_11111111111111111111111111111111_00110000_0101_11_0_0_00100100001001000111111001110011;
      patterns[326] = 144'b01001111001001100100101010011011_10010110111100110001110010101011_11111111111111111111111111111111_00110000_0101_11_0_0_01101001000011001110001101010100;
      patterns[327] = 144'b11010000000110110110101110011010_01110110011011011101001011010010_11111111111111111111111111111111_00110000_0101_11_0_0_10001001100100100010110100101101;
      patterns[328] = 144'b01101011100000100010101101111101_10101000010001100110000001110100_11111111111111111111111111111111_00110000_0101_11_0_0_01010111101110011001111110001011;
      patterns[329] = 144'b10100001110110001110010111001111_10111000011110001010010010101000_11111111111111111111111111111111_00110000_0101_11_0_0_01000111100001110101101101010111;
      patterns[330] = 144'b00001010010110101100010001100011_10010010001000001000111100001001_11111111111111111111111111111111_11001111_0101_11_0_0_10010010001000001000111100001001;
      patterns[331] = 144'b10011010000110101110000001110100_01110001101110010011111100110001_11111111111111111111111111111111_11001111_0101_11_0_0_01110001101110010011111100110001;
      patterns[332] = 144'b10101001110110100010000101000010_11101111011011011111100100010011_11111111111111111111111111111111_11001111_0101_11_0_0_11101111011011011111100100010011;
      patterns[333] = 144'b01100110010100111000111010011110_10010100110101100101010011101110_11111111111111111111111111111111_11001111_0101_11_0_0_10010100110101100101010011101110;
      patterns[334] = 144'b10100010111111110101001001111111_01001110110011110001111100110010_11111111111111111111111111111111_11001111_0101_11_0_0_01001110110011110001111100110010;
      patterns[335] = 144'b11010001000101000010000011000110_01010000101011100000100000001111_11111111111111111111111111111111_11110011_0101_11_0_0_11111111111111111111111111111111;
      patterns[336] = 144'b00001000000001010100010011110011_00010111110000110111110001011001_11111111111111111111111111111111_11110011_0101_11_0_0_11111111111111111111111111111111;
      patterns[337] = 144'b10001101011000010011110100010110_01001100101111110110111011101100_11111111111111111111111111111111_11110011_0101_11_0_0_11111111111111111111111111111111;
      patterns[338] = 144'b10011011010010000111010101000010_01101010000001011100100110011010_11111111111111111111111111111111_11110011_0101_11_0_0_11111111111111111111111111111111;
      patterns[339] = 144'b11010101001111010101001011111001_00100100011011100001110011011101_11111111111111111111111111111111_11110011_0101_11_0_0_11111111111111111111111111111111;
      patterns[340] = 144'b11111110010101100011011110001101_01101000010110000001010000111010_11111111111111111111111111111111_10000000_0101_11_0_0_01101000010100000001010000001000;
      patterns[341] = 144'b10100010000000110000001110101110_01101001101110101011000110000110_11111111111111111111111111111111_10000000_0101_11_0_0_00100000000000100000000110000110;
      patterns[342] = 144'b01011010011010110101101001100111_10110111111001001110011111100100_11111111111111111111111111111111_10000000_0101_11_0_0_00010010011000000100001001100100;
      patterns[343] = 144'b10000111111101011011111001001000_00100000001011000100000100000010_11111111111111111111111111111111_10000000_0101_11_0_0_00000000001001000000000000000000;
      patterns[344] = 144'b11001101011101010000111110010001_10100110001010000010111100001001_11111111111111111111111111111111_10000000_0101_11_0_0_10000100001000000000111100000001;
      patterns[345] = 144'b00100000111100011100111010110101_11100101010010101001011111011010_11111111111111111111111111111111_11111110_0101_11_0_0_11111111111111111111111111111111;
      patterns[346] = 144'b01010000010111101011011001110100_00001010000111111011011111010001_11111111111111111111111111111111_11111110_0101_11_0_0_11111111111111111111111111111111;
      patterns[347] = 144'b00100100001010111011101101000010_01101001110110010101101110011110_11111111111111111111111111111111_11111110_0101_11_0_0_11111111111111111111111111111111;
      patterns[348] = 144'b00000001010001100111101011111001_10110111100000100001001100110100_11111111111111111111111111111111_11111110_0101_11_0_0_11111111111111111111111111111111;
      patterns[349] = 144'b00000101101010001111111001011101_01111001000011000000000001011111_11111111111111111111111111111111_11111110_0101_11_0_0_11111111111111111111111111111111;
      patterns[350] = 144'b00100010100001101101101110011100_01010000000000010101000111011011_11111111111111111111111111111111_01111111_0101_11_0_0_11111111111111111010111001100111;
      patterns[351] = 144'b01000001010100101101000001000000_00011110001000000011100010000100_11111111111111111111111111111111_01111111_0101_11_0_0_11111111111111111110111111111111;
      patterns[352] = 144'b10011011011101010010010000100000_01101001101001101000110100111000_11111111111111111111111111111111_01111111_0101_11_0_0_11110110110110111111101111011111;
      patterns[353] = 144'b11111010101101000111011110111101_00010010000100001011100011001100_11111111111111111111111111111111_01111111_0101_11_0_0_11101101111011111100111101110011;
      patterns[354] = 144'b00011000011100111111111011100100_00111100100010101001010110111011_11111111111111111111111111111111_01111111_0101_11_0_0_11100111111111010110101101011111;
      patterns[355] = 144'b11000110000000110001100000111010_11010010100110010000000111001100_11111111111111111111111111111111_00000001_0101_11_0_0_00000000000000000000000000000000;
      patterns[356] = 144'b00110011101010010000111111001100_10110110111111011011111010111000_11111111111111111111111111111111_00000001_0101_11_0_0_00000000000000000000000000000000;
      patterns[357] = 144'b01011101101100010001110000010000_00011000010010010100011110100111_11111111111111111111111111111111_00000001_0101_11_0_0_00000000000000000000000000000000;
      patterns[358] = 144'b00011001101100110101001001101010_11111101111000111010001110111110_11111111111111111111111111111111_00000001_0101_11_0_0_00000000000000000000000000000000;
      patterns[359] = 144'b00010011001111100100010010010101_10010100010110001110011110101011_11111111111111111111111111111111_00000001_0101_11_0_0_00000000000000000000000000000000;
      patterns[360] = 144'b11110010011100101000101101001010_11110111011011101101101011100100_11111111111111111111111111111111_10010110_0101_11_0_0_11111010111000111010111001010001;
      patterns[361] = 144'b11011100100111010000111001110010_10011111001000011000100011110110_11111111111111111111111111111111_10010110_0101_11_0_0_10111100010000110111100101111011;
      patterns[362] = 144'b00011101000111100000000000010000_01011010111011010101100110010010_11111111111111111111111111111111_10010110_0101_11_0_0_10111000000011001010011001111101;
      patterns[363] = 144'b11101011001100001010101011110110_11011101101101010111010101010100_11111111111111111111111111111111_10010110_0101_11_0_0_11001001011110100010000001011101;
      patterns[364] = 144'b10001000110001111111001001000000_11010010010000010100001011001101_11111111111111111111111111111111_10010110_0101_11_0_0_10100101011110010100111101110010;
      patterns[365] = 144'b01101010000000111000010000000101_10000000010000100100011011110100_11111111111111111111111111111111_01101001_0101_11_0_0_11101010010000011100001011110001;
      patterns[366] = 144'b10101010000110011010000001110101_10011010100001010001101111110101_11111111111111111111111111111111_01101001_0101_11_0_0_00110000100111001011101110000000;
      patterns[367] = 144'b11100101001101010111110111001101_00100010110000101110101011100011_11111111111111111111111111111111_01101001_0101_11_0_0_11000111111101111001011100101110;
      patterns[368] = 144'b01011100100100000101101001101111_10011101111100011110001100000101_11111111111111111111111111111111_01101001_0101_11_0_0_11000001011000011011100101101010;
      patterns[369] = 144'b10000010000100010000100111110110_00010111011101011000100100101000_11111111111111111111111111111111_01101001_0101_11_0_0_10010101011001001000000011011110;
      patterns[370] = 144'b11011011111011101001001111010110_10010101111110001011010011011101_11111111111111111111111111111111_11101000_0101_11_0_0_11011111111111101011011111011111;
      patterns[371] = 144'b11000011001100000100011001010010_10110111100100101001010110110011_11111111111111111111111111111111_11101000_0101_11_0_0_11110111101100101101011111110011;
      patterns[372] = 144'b01100111110101010101101001100111_10111110011010001000010110011000_11111111111111111111111111111111_11101000_0101_11_0_0_11111111111111011101111111111111;
      patterns[373] = 144'b01001101110001010011111110011010_00011000001010001000100011110100_11111111111111111111111111111111_11101000_0101_11_0_0_01011101111011011011111111111110;
      patterns[374] = 144'b11010111010101100100101110111001_01001110101110010000110010111101_11111111111111111111111111111111_11101000_0101_11_0_0_11011111111111110100111110111101;
      patterns[375] = 144'b01011010100110010100101000001000_11101111110011010001011010011000_11111111111111111111111111111111_00010111_0101_11_0_0_00000000001000101010000101100111;
      patterns[376] = 144'b00001000000110000111100100011100_00000000001000001011101110011100_11111111111111111111111111111111_00010111_0101_11_0_0_11110111110001110000010001100011;
      patterns[377] = 144'b00001010110111001110000101101111_11010100001000110111000101011101_11111111111111111111111111111111_00010111_0101_11_0_0_00100001000000000000111010000000;
      patterns[378] = 144'b01110111010100100000001110100100_10110010000111010111001101111011_11111111111111111111111111111111_00010111_0101_11_0_0_00001000101000001000110000000000;
      patterns[379] = 144'b11011001101001000011111110011001_00110000010101000101110111011001_11111111111111111111111111111111_00010111_0101_11_0_0_00000110000010111000000000100110;
      patterns[380] = 144'b01001101100111010100000111011000_00111011010110010101000110010010_11111111111111111111111111111111_11001010_0101_11_0_0_00111011010110010101000110010010;
      patterns[381] = 144'b10011000001010011101100011010010_10101110101011000110001010111001_11111111111111111111111111111111_11001010_0101_11_0_0_10101110101011000110001010111001;
      patterns[382] = 144'b10111101110001111000001101110100_11000110000100110001111111010000_11111111111111111111111111111111_11001010_0101_11_0_0_11000110000100110001111111010000;
      patterns[383] = 144'b10101110010001010010111110100101_11001000100111000000010101010010_11111111111111111111111111111111_11001010_0101_11_0_0_11001000100111000000010101010010;
      patterns[384] = 144'b00101101100101111110010110010001_10101000001111011000100011111011_11111111111111111111111111111111_11001010_0101_11_0_0_10101000001111011000100011111011;
      patterns[385] = 144'b10001011000100101011001101011000_00011111100000101000100111100101_11111111111111111111111111111111_11100010_0101_11_0_0_10011111100100101011101111111101;
      patterns[386] = 144'b01001100110001100010000110110001_10100101111110111101000100101101_11111111111111111111111111111111_11100010_0101_11_0_0_11101101111111111111000110111101;
      patterns[387] = 144'b00100000011110111100000001101000_01111100001010000000001111001101_11111111111111111111111111111111_11100010_0101_11_0_0_01111100011110111100001111101101;
      patterns[388] = 144'b10101100000110010010101101101110_00100100111101000110110111010001_11111111111111111111111111111111_11100010_0101_11_0_0_10101100111111010110111111111111;
      patterns[389] = 144'b00001111111101100101011101011010_10011011111110000101101000111010_11111111111111111111111111111111_11100010_0101_11_0_0_10011111111111100101111101111010;
      patterns[390] = 144'b01110101110110000100000101001110_01110011001000010101000101001001_11111111111111111111111111111111_11100100_0101_11_0_0_01110111111110010101000101001111;
      patterns[391] = 144'b01111100110111001000011011101001_01111011100101110011111110011000_11111111111111111111111111111111_11100100_0101_11_0_0_01111111110111111011111111111001;
      patterns[392] = 144'b10011111001100010011011011111010_00111001101000000100101001011100_11111111111111111111111111111111_11100100_0101_11_0_0_10111111101100010111111011111110;
      patterns[393] = 144'b01100001000000101010100010110001_11110000000100111001111011111011_11111111111111111111111111111111_11100100_0101_11_0_0_11110001000100111011111011111011;
      patterns[394] = 144'b01011000101101001111110011101010_00110000110001101011010101100100_11111111111111111111111111111111_11100100_0101_11_0_0_01111000111101101111110111101110;
      patterns[395] = 144'b10101010010111000000010011111000_11010001001010101000110011111110_11111111111111111111111111111111_11101010_0101_11_0_0_11111011011111101000110011111110;
      patterns[396] = 144'b01111011000011101011100100111000_01010011101100010100110011110110_11111111111111111111111111111111_11101010_0101_11_0_0_01111011101111111111110111111110;
      patterns[397] = 144'b01111111110111001011010011101011_11010100010100011111111001010010_11111111111111111111111111111111_11101010_0101_11_0_0_11111111110111011111111011111011;
      patterns[398] = 144'b11001011111000100100110000100110_10011110001011010001110010101101_11111111111111111111111111111111_11101010_0101_11_0_0_11011111111011110101110010101111;
      patterns[399] = 144'b01101100010101000111000111001110_10000010010000001010101000000111_11111111111111111111111111111111_11101010_0101_11_0_0_11101110010101001111101111001111;
      patterns[400] = 144'b10010011010000000010111111001001_11011111111110110111000100011111_11111111111111111111111111111111_11101100_0101_11_0_0_11011111111110110111111111011111;
      patterns[401] = 144'b11101011001010010011110101110011_10101100111101000101110101100111_11111111111111111111111111111111_11101100_0101_11_0_0_11101111111111010111110101110111;
      patterns[402] = 144'b10100000101111001001101001001001_01110100010110010110101110110000_11111111111111111111111111111111_11101100_0101_11_0_0_11110100111111011111101111111001;
      patterns[403] = 144'b01001110001100001110111000010100_11000000111110110000000101000110_11111111111111111111111111111111_11101100_0101_11_0_0_11001110111110111110111101010110;
      patterns[404] = 144'b00110101110100111111000111011100_10101000011011101111101001111100_11111111111111111111111111111111_11101100_0101_11_0_0_10111101111111111111101111111100;
      patterns[405] = 144'b11100110111100111011000010001011_01101101110110100010100000111100_11111111111111111111111111111111_11111000_0101_11_0_0_11111111111111111111111111111111;
      patterns[406] = 144'b10010111100010101101011110001001_11011001000010000101010001110111_11111111111111111111111111111111_11111000_0101_11_0_0_11111111111111111111111111111111;
      patterns[407] = 144'b10111011011110011001011011011111_10011111100011011001001011011011_11111111111111111111111111111111_11111000_0101_11_0_0_11111111111111111111111111111111;
      patterns[408] = 144'b00001101101001111011000101101010_10101100101100011001010011011100_11111111111111111111111111111111_11111000_0101_11_0_0_11111111111111111111111111111111;
      patterns[409] = 144'b00110001011010101100101000100110_10111000010000110011000001110111_11111111111111111111111111111111_11111000_0101_11_0_0_11111111111111111111111111111111;
      patterns[410] = 144'b11100000100010000100101011000010_11101001101010110111011010100101_11111111111111111111111111111111_10101000_0101_11_0_0_11100000100010000100101011000010;
      patterns[411] = 144'b01100010100010100001110011011100_00101011000001010010000011000101_11111111111111111111111111111111_10101000_0101_11_0_0_01100010100010100001110011011100;
      patterns[412] = 144'b10001001010001000000001111000110_10001000010010110100000111010001_11111111111111111111111111111111_10101000_0101_11_0_0_10001001010001000000001111000110;
      patterns[413] = 144'b01010111110001000100111001011001_11110011010010101000010000010011_11111111111111111111111111111111_10101000_0101_11_0_0_01010111110001000100111001011001;
      patterns[414] = 144'b10111101011011001000101000101110_10000011011111111101001110101111_11111111111111111111111111111111_10101000_0101_11_0_0_10111101011011001000101000101110;
      patterns[415] = 144'b11110101101001101111110000111110_11011101001000001011001101110110_11111111111111111111111111111111_11001000_0101_11_0_0_11011101001000001011001101110110;
      patterns[416] = 144'b00010010000000001010111000000110_10010100101011110100010111010101_11111111111111111111111111111111_11001000_0101_11_0_0_10010100101011110100010111010101;
      patterns[417] = 144'b11000010110010101110111110100010_10010110111101010001010101010110_11111111111111111111111111111111_11001000_0101_11_0_0_10010110111101010001010101010110;
      patterns[418] = 144'b00001011001001011011001011100101_10111110010100010111011100000001_11111111111111111111111111111111_11001000_0101_11_0_0_10111110010100010111011100000001;
      patterns[419] = 144'b01100101111001010001111100100001_00110010100010001011111010001011_11111111111111111111111111111111_11001000_0101_11_0_0_00110010100010001011111010001011;
      patterns[420] = 144'b01111010011110001001000010001100_01101001110100011110010000111010_11111111111111111111111111111111_11100000_0101_11_0_0_01111011111110011111010010111110;
      patterns[421] = 144'b10110101110110100000001001011000_00011111110000100001011101101110_11111111111111111111111111111111_11100000_0101_11_0_0_10111111110110100001011101111110;
      patterns[422] = 144'b11111101010111001000011110110100_00110000111110100011111111001010_11111111111111111111111111111111_11100000_0101_11_0_0_11111101111111101011111111111110;
      patterns[423] = 144'b00000011111110011101001111010001_01101000010000100001000011000111_11111111111111111111111111111111_11100000_0101_11_0_0_01101011111110111101001111010111;
      patterns[424] = 144'b00000010010001101100011010011100_11000000010011100000110001100101_11111111111111111111111111111111_11100000_0101_11_0_0_11000010010011101100111011111101;
      patterns[425] = 144'b10000110111110101001111101101011_00101101100110011010010001000100_11111111111111111111111111111111_00010101_0101_11_0_0_01010000000001000100000010010000;
      patterns[426] = 144'b00000101111111000010001001011010_10010110101101110100001110111101_11111111111111111111111111111111_00010101_0101_11_0_0_01101000000000001001110000000000;
      patterns[427] = 144'b00110110011101001000000010011010_11000111111000111000010011110101_11111111111111111111111111111111_00010101_0101_11_0_0_00001000000010000111101100000000;
      patterns[428] = 144'b01101001011000101011100010000011_10100000011001011101100011111110_11111111111111111111111111111111_00010101_0101_11_0_0_00010110100110000000011100000000;
      patterns[429] = 144'b00110001100010001111110100101101_00011010111101110000111110111001_11111111111111111111111111111111_00010101_0101_11_0_0_11000100000000000000000001000010;
      patterns[430] = 144'b00010001011100111001001001011001_01100110110010111111010110111001_11111111111111111111111111111111_00010011_0101_11_0_0_10001000000001000000100000000110;
      patterns[431] = 144'b11110100101010011101011010111101_10001101101000000010010100100111_11111111111111111111111111111111_00010011_0101_11_0_0_00000010010101100000100001000000;
      patterns[432] = 144'b10110011110111010001101000001110_11111001011001111010001111000110_11111111111111111111111111111111_00010011_0101_11_0_0_00000100000000000100010000110001;
      patterns[433] = 144'b01000111001110000101100100101011_01000001010000001011000011010100_11111111111111111111111111111111_00010011_0101_11_0_0_10111000100001110000011000000000;
      patterns[434] = 144'b11011001010100011000010010100011_10001001100111111001010010010111_11111111111111111111111111111111_00010011_0101_11_0_0_00100110001000000110101101001000;
      patterns[435] = 144'b00101010001110100111111010000001_00100011101011101110001111101100_11111111111111111111111111111111_00000111_0101_11_0_0_00000000000000000000000000000000;
      patterns[436] = 144'b10110000011010101111000001100010_00100101101011001001011100011010_11111111111111111111111111111111_00000111_0101_11_0_0_00000000000000000000000000000000;
      patterns[437] = 144'b11010011011111000101101010011100_11100100001101110101111000001101_11111111111111111111111111111111_00000111_0101_11_0_0_00000000000000000000000000000000;
      patterns[438] = 144'b11111011111010011011110100101010_11001010010100001101000110011111_11111111111111111111111111111111_00000111_0101_11_0_0_00000000000000000000000000000000;
      patterns[439] = 144'b11110111111011101011101000001110_10110110000011010001110110000100_11111111111111111111111111111111_00000111_0101_11_0_0_00000000000000000000000000000000;
      patterns[440] = 144'b10010100100100000001110100001001_00111011001110111000010110110111_11111111111111111111111111111111_01010111_0101_11_0_0_01101011011011111110001011110110;
      patterns[441] = 144'b00100000011001001101001000111001_00010101111101110110000101000110_11111111111111111111111111111111_01010111_0101_11_0_0_11011111100110110010110111000110;
      patterns[442] = 144'b01010000011110011100011011100010_10010111101010010111010010000000_11111111111111111111111111111111_01010111_0101_11_0_0_10101111100001100011100100011101;
      patterns[443] = 144'b00101011010110001001011001111010_11111011000011001101101010010110_11111111111111111111111111111111_01010111_0101_11_0_0_11010100101001110110100110000101;
      patterns[444] = 144'b01011011001101100101110001011101_10010111001101110101110111010000_11111111111111111111111111111111_01010111_0101_11_0_0_10100100110010011010001110100010;
      patterns[445] = 144'b00111110101110000100111111010001_00110100101100011001101001101111_11111111111111111111111111111111_00110111_0101_11_0_0_11001011010011100110010110010000;
      patterns[446] = 144'b01000001101110000111101010011000_00011100011011101001010010110100_11111111111111111111111111111111_00110111_0101_11_0_0_11100011100100010110101101001011;
      patterns[447] = 144'b00000011100011111011011001111110_01010100011000000110110010110011_11111111111111111111111111111111_00110111_0101_11_0_0_10101011100111111001001101001100;
      patterns[448] = 144'b11101100001010101011101111010001_01011100001111010111100001010100_11111111111111111111111111111111_00110111_0101_11_0_0_10100011110000101000011110101011;
      patterns[449] = 144'b01111101000000010110111111111110_00011100010011100110110111001111_11111111111111111111111111111111_00110111_0101_11_0_0_11100011101100011001001000110000;
      patterns[450] = 144'b10111011101001100100001000101000_01111011010110001110011000011001_11111111111111111111111111111111_00011111_0101_11_0_0_00000100000000010001100111000110;
      patterns[451] = 144'b10100011011010111101110011011010_11010110011000001000001000110001_11111111111111111111111111111111_00011111_0101_11_0_0_00001000100101000010000100000100;
      patterns[452] = 144'b10011101110000111011110001001100_01111110111101011101101001110000_11111111111111111111111111111111_00011111_0101_11_0_0_00000000000010000000000110000011;
      patterns[453] = 144'b11000001001110001000110100100001_00110010100010101001010100010111_11111111111111111111111111111111_00011111_0101_11_0_0_00001100010001010110001011001000;
      patterns[454] = 144'b10000110001111010000101110000001_10101100110100001011111001101101_11111111111111111111111111111111_00011111_0101_11_0_0_01010001000000100100000000010010;

      for (i = 0; i < 455; i = i + 1)
      begin
        A = patterns[i][143:112];
        B = patterns[i][111:80];
        C = patterns[i][79:48];
        Opcode = patterns[i][47:40];
        control = patterns[i][39:36];
        csel = patterns[i][35:34];
        CLK = patterns[i][33];
        FLAG_WE = patterns[i][32];
        #10;
        if (patterns[i][31:0] !== 32'hx)
        begin
          if (Out !== patterns[i][31:0])
          begin
            $display("%d:Out: (assertion error). Expected %h, found %h", i, patterns[i][31:0], Out);
            $finish;
          end
        end
      end

      $display("All tests passed.");
    end
    endmodule
